brengi/CESE-PCB/2018/Moya/TP_FinalV2/doc/readme.txt

El circuito que se eligió es de un "Electrodo Activo para Electromiografía" para ser usado en mi Trabajo Final de la Especialidad de Sistemas Embebidos.
Está basado en el paper "Simple Circuit Design of Double Differential EMG Active Electrode" de Federico Nicolás Guerrero, Enrique Mario Spinelli y Marcelo Alejandro Haberman.
El circuito propuesto en el paper se muestra en la figura 3b y en el texto se hace la selección de componentes. La figura 5 muestra el PCB que implementaron.
La consigna para este trabajo fue mejorar ese PCB mediante las siguientes acciones:

- Incluir zonas de cobre
- Evitar puentes
- Brindar dos puntos de sujección a cada electrodo

El único requerimiento particular del circuito es que la distancia entre electrodos debe ser de 20mm.

Fue necesario iterar el diseño del esquemático y del PCB  reordenando componentes e intercambiando las unidades del circuito integrado para obtener un ruteo óptimo y las mayores áreas de cobre posible.
Si bien la distancia de los electrodos a los operacionales no es la misma,  no resulta crítico dadas las caracterísiticas de baja frecuencia de las señales (hasta 500 Hz).

Telmo Moya
CESE 2018
