brengi/CESE-PCB/doc/2016_curso1/Curso_PCBs_Intro.pdf

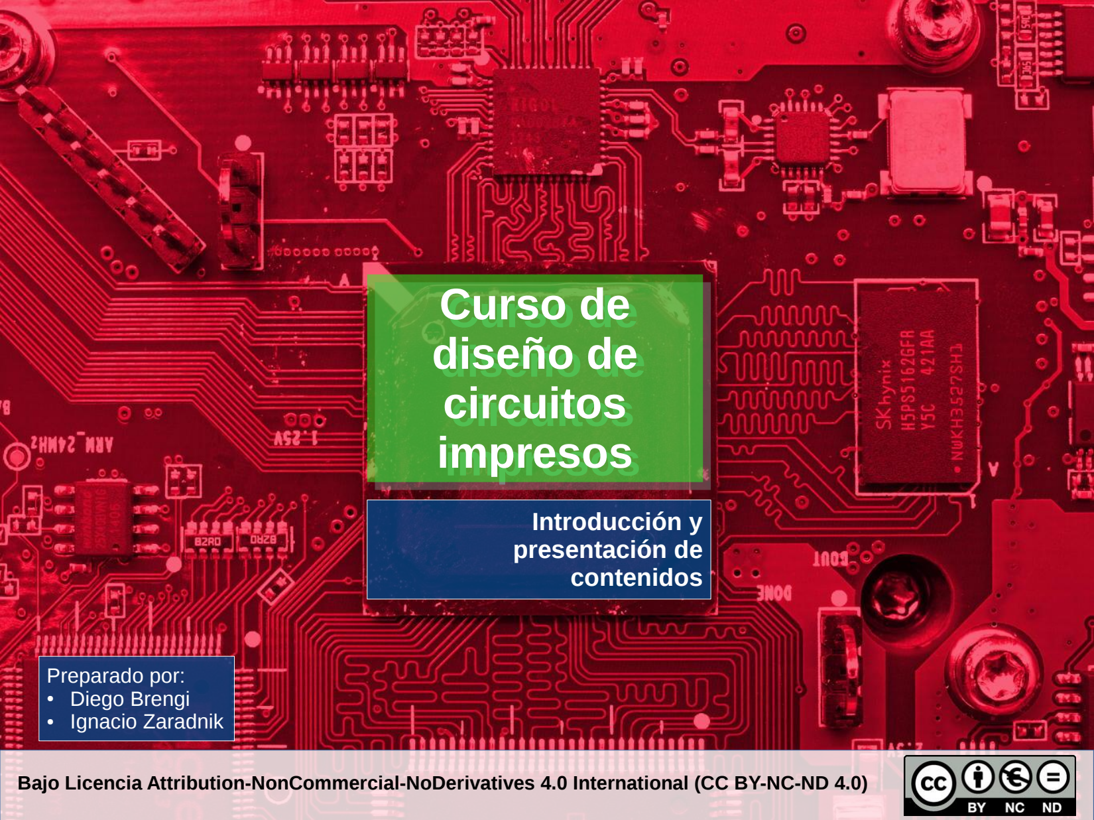
[picture p158: page 1]

# Curso de diseño de circuitos impresos

Introducción y
presentación de
contenidos

Bajo Licencia Attribution-NonCommercial-NoDerivatives 4.0 International (CC BY-NC-ND 4.0)

Preparado por:
- Diego Brengi
- Ignacio Zaradnik

## La problemática de los diseños de PCBs complejos

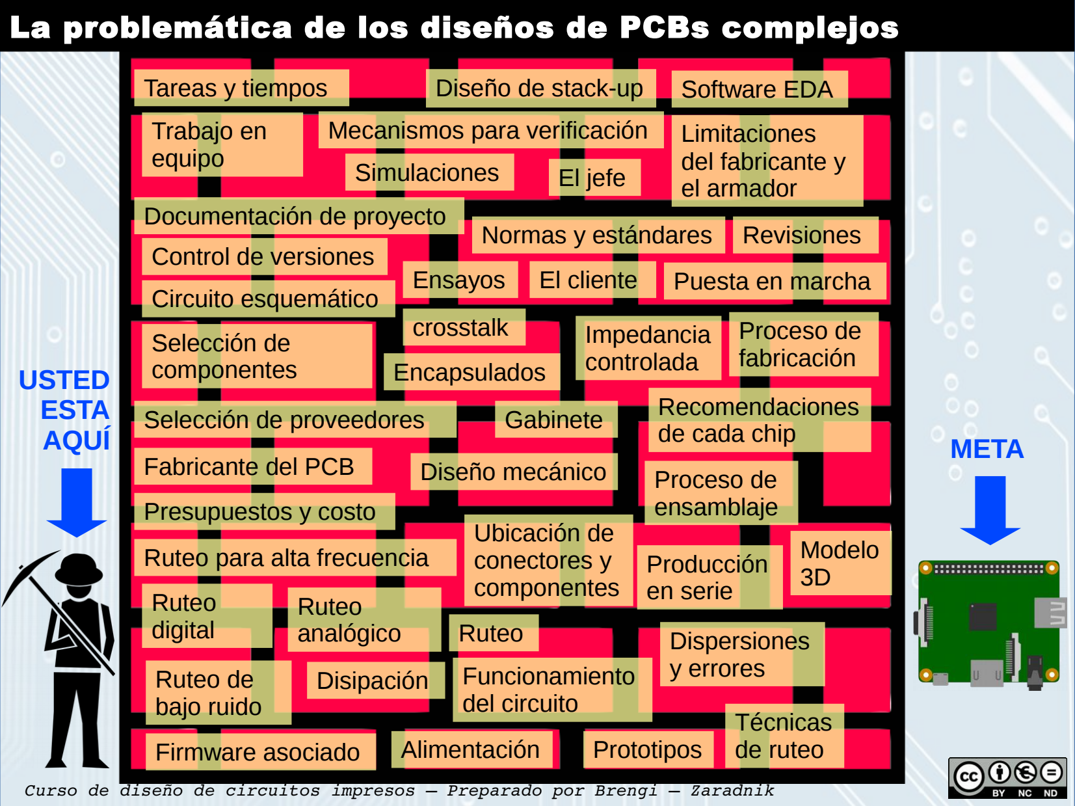
[picture p159: page 2]

Curso de diseño de circuitos impresos – Preparado por Brengi – Zaradnik

Proceso de
fabricación

Circuito esquemático

Documentación de proyecto

Selección de
componentes
Fabricante del PCB | Proceso de ensamblaje

Mecanismos para verificación

Puesta en marcha

Diseño de stack-up

Normas y estándares Revisiones

Trabajo en
equipo

Ruteo

Ubicación de
conectores y
componentes

Presupuestos y costo
Ruteo para alta frecuencia

Ruteo
analógico

Ruteo
digital

Software EDA

Diseño mecánico

Selección de proveedores

Simulaciones

Firmware asociado

Tareas y tiempos

Funcionamiento
del circuito

Gabinete

Ensayos

Alimentación

Ruteo de
bajo ruido

Limitaciones
del fabricante y
el armador

Recomendaciones
de cada chip

Modelo
3D

Encapsulados

Prototipos

Producción
en serie

Dispersiones
y errores

Técnicas
de ruteo

crosstalk Impedancia controlada

Disipación

Control de versiones
El cliente

El jefe

USTED
ESTA
AQUÍ | META

## La problemática de los diseños de PCBs complejos

## Los factores que intervienen son muy

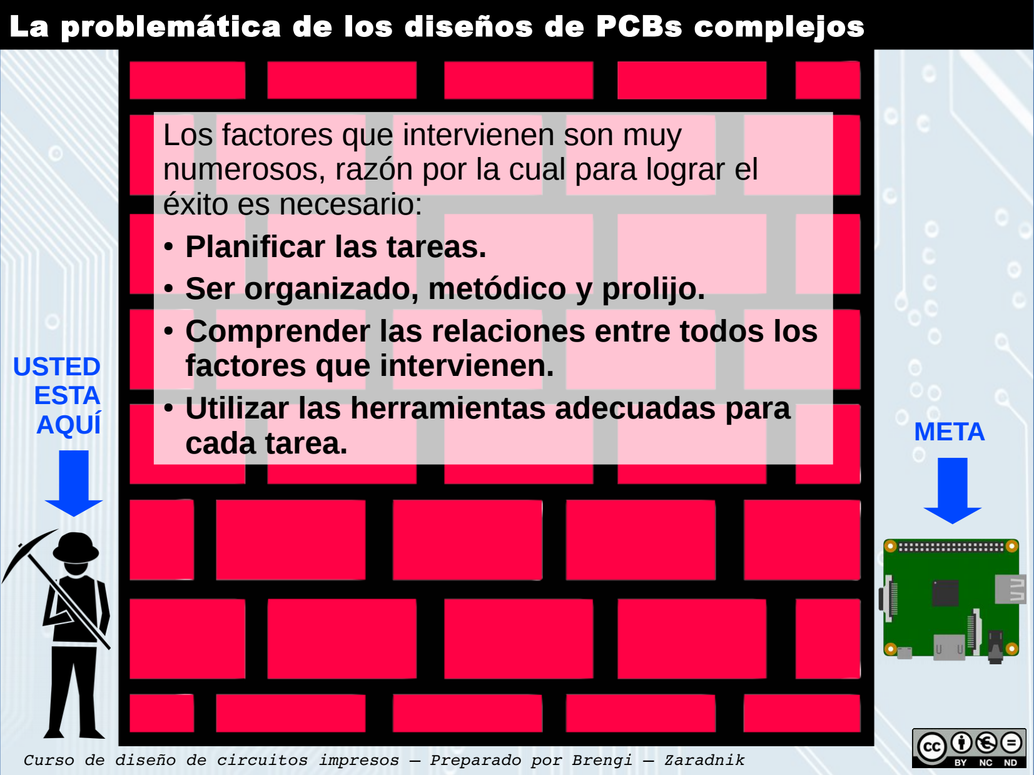
[picture p160: page 3]

USTED
ESTA
AQUÍ

## numerosos, razón por la cual para lograr el éxito es necesario:

- Planificar las tareas.
- Ser organizado, metódico y prolijo.

## - Comprender las relaciones entre todos los

factores que intervienen.

## - Utilizar las herramientas adecuadas para

cada tarea. | META

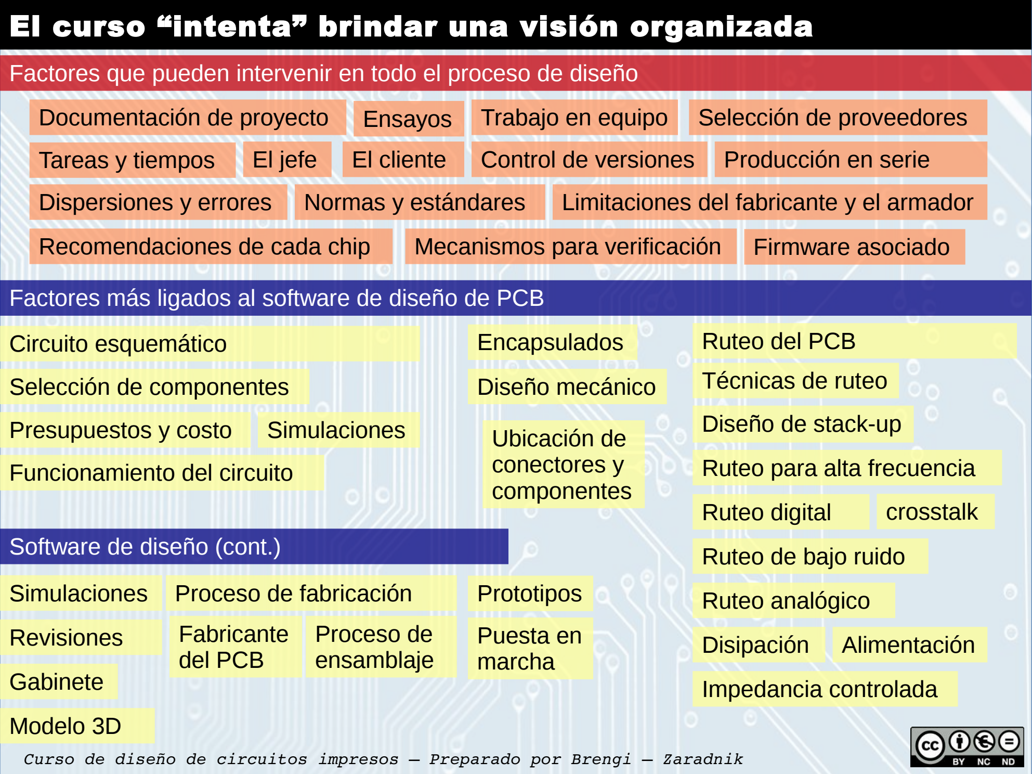
[picture p161: figure]
Proceso de fabricación; Circuito esquemático; Documentación de proyecto; Selección de componentes; Fabricante del PCB; Proceso de ensamblaje; Mecanismos para verificación; Puesta en marcha; Diseño de stack-up; Normas y estándares; Revisiones; Trabajo en equipo; Ruteo del PCB; Ubicación de conectores y componentes; Presupuestos y costo; Ruteo para alta frecuencia; Ruteo analógico; Ruteo digital; Diseño mecánico; Selección de proveedores; Simulaciones; Firmware asociado; Tareas y tiempos; Funcionamiento del circuito; Gabinete; Ensayos; Alimentación; Ruteo de bajo ruido; Recomendaciones de cada chip; Modelo 3D; Encapsulados; Prototipos; Producción en serie; Dispersiones y errores; Técnicas de ruteo; crosstalk; Impedancia controlada; Disipación; El jefe; El cliente; Control de versiones; Software de diseño (cont.)

## El curso “intenta” brindar una visión organizada

Factores más ligados al software de diseño de PCB

Limitaciones del fabricante y el armador

Factores que pueden intervenir en todo el proceso de diseño

## Alcance del curso

Aprender y dominar algunos de los conceptos y factores mencionados lleva años de experiencia, muchas horas de lectura en cada temática y otras tantas de práctica realizando diseños.

El curso debe ajustarse a una carga horaria total de 24 hs.

Por este motivo se dará prioridad a la práctica con el software de diseño de PCBs, a la metodología general y a los temas de base que incentiven a la investigación por cuenta propia.

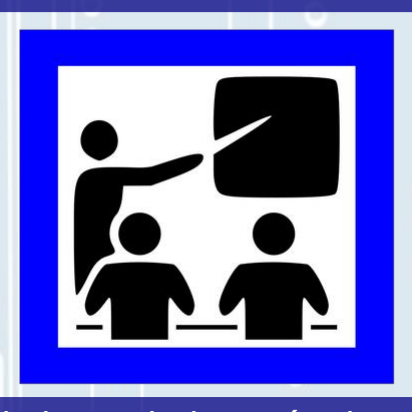
[picture p162: figure]

Al finalizar el curso se tendrá conocimiento de los métodos, pautas y procedimientos a considerar cuando se realiza un diseño de mediana y alta complejidad. Además se reforzarán los conceptos llevándolos a la práctica utilizando KiCad y realizando los ejercicio propuestos.

El contenido listado a continuación es orientativo, pudiéndose quitar o agregar temas dependiendo de la evolución del curso.

## Organización conceptual del curso

El curso esta organizado en cuatro módulos principales:

1)Glosario: Se da una base de conocimientos y términos, mencionando los elementos, componentes y partes que intervienen en el proceso de diseño. Se presentan de manera simple conceptos que después serán necesarios para entender los procedimientos. 2)Procedimientos: Se explican los pasos que debe seguir el diseñador en cada etapa. Aquí se agrupan técnicas, consejos, modalidades, y todos los pasos y consideraciones que deben realizarse para finalizar exitosamente un diseño.
3)Software EDA: Capacitación en el uso del software EDA que se utilizará en el curso (KiCad). 4)Ejercicios: Los ejercicios buscan consolidar los conocimientos aprendidos en los demás módulos.

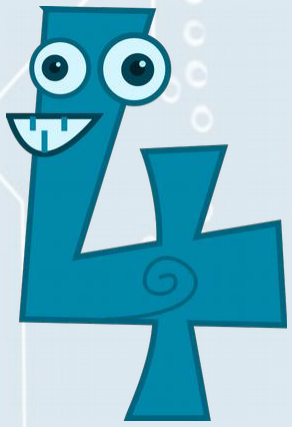
[picture p163: figure]

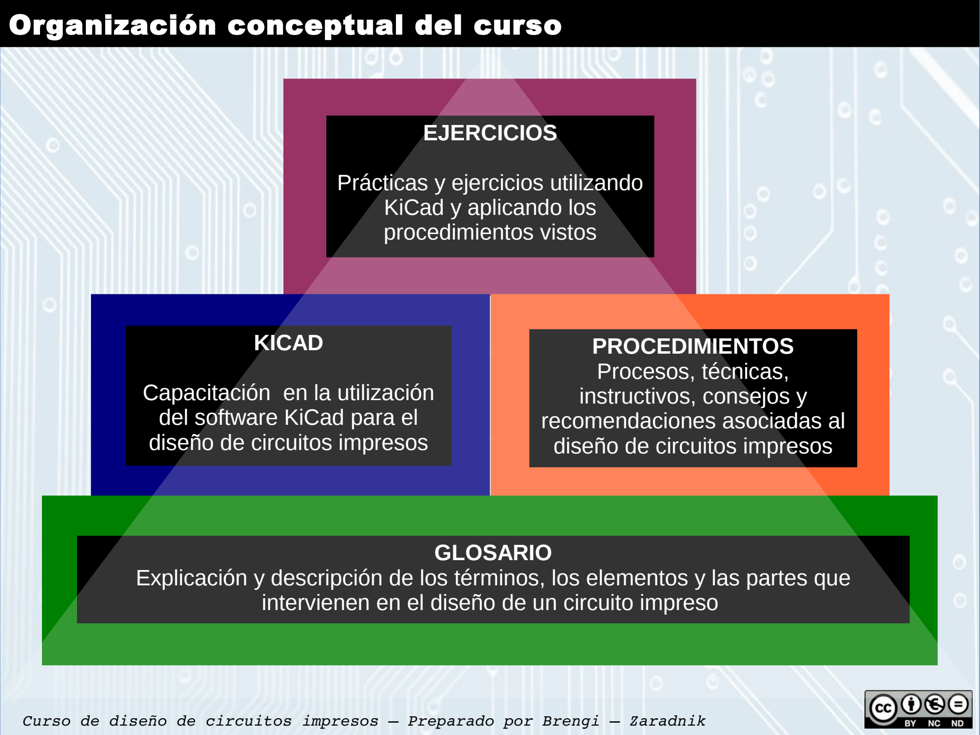
[picture p164: figure]
Organización conceptual del curso; GLOSARIO; PROCEDIMIENTOS Procesos, técnicas, instructivos, consejos y recomendaciones asociadas al diseño de circuitos impresos; KICAD; Capacitación en la utilización del software KiCad para el diseño de circuitos impresos; EJERCICIOS; Prácticas y ejercicios utilizando KiCad y aplicando los procedimientos vistos

Explicación y descripción de los términos, los elementos y las partes que intervienen en el diseño de un circuito impreso

## Glosario

GLOSARIO
Explicación y descripción de los términos, los elementos y las partes que intervienen en el diseño de un circuito impreso

Documentación – Sistema de revisión Documentación – Estructura de directorios Documentación – Administrativos
Documentación – Requerimientos
Documentación – Hojas de datos y notas de aplicación Documentación – Esquemático y PCB Documentación – Notas de ingeniería
Documentación – Proveedores, cotizaciones y presupuestos
Documentación – Especificaciones del fabricante Documentación – Revisiones del diseño Documentación – Brochure
Documentación – Autores y licencia
Software EDA
Software de diseño de PCB
Esquemático
Esquemático – Única hoja
Esquemático – Múltiples hojas Esquemático – Rótulo
Símbolo de esquemático
Símbolo – Multiparte regular Símbolo – Multiparte irregular Símbolo – Pin de conexión
Símbolo – Campos asociados Símbolo – Muchos pines.
Símbolo – Bibliotecas de símbolos Símbolo – Referencias de tensión

Esquemático – Líneas de interconexión Esquemático – Uniones
Esquemático – etiquetas globales
Esquemático – Etiquetas jerárquicas
Esquemático – Buses
Esquemático – Líneas, gráficos y notas adicionales Esquemático – ERC
Esquemático – Netlist
Esquemático – Listado de materiales
PCB
PCB – Rótulo y notas
PCB – Grilla y unidades
PCB – Bordes
PCB – Agujeros de sujeción PCB – Fiduciales
PCB – Vías
PCB – Vías – Pasante o PTH
PCB – Vías – otros tipos
PCB – Vías – terminaciones (tented via) PCB – pistas
PCB – pistas de alimentación
PCB – pistas diferenciales
PCB – pistas de impedancia controlada PCB – pistas de alta velocidad
PCB – Crosstalk
PCB – Capas
PCB – Capas – Mecánica
PCB – Capas – Cobre
PCB – Capas – Serigrafía
PCB – Capas – Máscara antisoldante PCB – Capas – Información de taladrado PCB – Capas – Pasta de estaño
PCB – Capas – Adicionales.
PCB – Stackup
PCB – Stackup – Láminas de cobre, sustratos y núcleos
PCB – Stackup – Preimpregnado
PCB – Stackup – Espesores
PCB – Stackup – Impedancias

PCB – Huellas
PCB – Huellas – Pads
PCB – Huellas – Tipos de encapsulados PCB – Huellas – Capas y propiedades PCB – Planos de alimentación
PCB – Rellenos de cobre
PCB – Rellenos de cobre – alivio térmico PCB – Áreas de exclusión
PCB – Ratsnest
PCB – Posicionamiento
PCB – Ruteo
PCB – Ruteo – Ic Fanout
PCB – Red de alimentación (PDN) PCB – Puntos de prueba
PCB – Verificador de capas
PCB – DRC
PCB – DRC – Clearance
PCB – Cupón
PCB – Archivos Gerber
Fabricación – Acabados superficiales HASL, ENIG y OSP.
Fabricación – Panelizado
Fabricación – corte vscoring y milling Armado – Montaje (Pick&place) Armado – Soldadura (Horno/Ola)

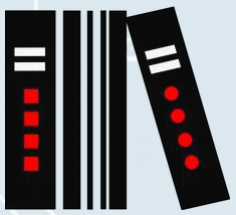
[picture p165: figure]

## Procedimientos

PROCEDIMIENTOS
Procesos, técnicas,
instructivos, consejos y
recomendaciones asociadas al diseño de circuitos impresos

PLANIFICACION DEL PCB
- Creación de huellas.
- Elección del stackup.
- Reglas de diseño del fabricante.
- Selección del método de ensamblaje y soldadura.
- Cálculos de pistas de alimentación.
- Cálculo de impedancia (impedancia controlada).
- Cálculo de par diferencial.
- Reglas de diseño y DRC.
- Planificación del panelizado.

RUTEO DEL PCB
- Asociación de símbolos y huellas.
- Sectorización del PCB, planificación y técnicas para la ubicación de componentes.
- Distribución de la alimentación y planos de alimentación.
- Técnicas de ruteo.
- Fanout de encapsulados de muchas conexiones.
- Ruteo de líneas diferenciales.
- Mitigación de crossltalk.
- Técnicas para circuitos de alta velocidad.
- Utilización de estructuras para la verificación.
- Revisiones de terceros.

FABRICACIÓN Y ARMADO
- Modelado 3D.
- Diseño del cupón de pruebas.
- Generación de archivos gerber e instrucciones para el fabricante.
- Generación de información para el armador.

METODOLOGÍA DE TRABAJO
- Ciclo general de diseño.
- Uso de git.
- Creación de la estructura de directorios.
- Proceso de documentación continua.
- Técnicas de trabajo en grupo.

DISEÑO DEL ESQUEMÁTICO
- Recomendaciones para un buen esquemático.
- Uso de los campos adicionales de los símbolos.
- Identificación de nodos y líneas especiales.
- Verificación ERC.
- Revisiones de terceros.

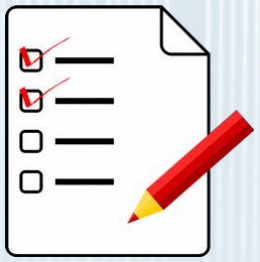
[picture p166: figure]

## Uso de KiCad

KICAD
Capacitación en la
utilización del software
KiCad para el diseño
de circuitos impresos

TOUR KICAD
- Presentación de KiCad.
- Características (ventajas y desventajas).
- Vista de las partes principales.
- Flujo de archivos.
- Flujo de trabajo en KiCad mientras se realiza un circuito mínimo.
- Administrador de proyectos.
- Editor de esquemáticos.
- Archivo netlist y asociación de huellas.
- Editor de PCB.
- La Graphic Abstarction Layer de KiCad (GAL).
- Modificaciones posteriores al esquemático.
- Generación de archivos Gerber.
- Visualización de archivos Gerber.
- Reportes de taladrado.
- Vista 3D.

ESCUELA KICAD
- Git y kicad.
- Estructura de directorios de un proyecto.
- Editor de esquemáticos, hojas jerárquicas y etiquetas de jerarquía.
- Editor de símbolos, pautas y creación de un símbolo.
- Creación de un símbolo multiparte no intercambiable.
- El chequeo de reglas eléctricas en el esquemático y power flags.
- Etiquetas locales y buses.
- Campos adicionales de información de los componentes.
- Documentación: Rótulo.
- Generación de listado de materiales.
- Opciones de footprints soportados.
- Asociación de footprints. Problemática.
- Operaciones con bloques en el esquemático.
- Editor de footprints.
- Pautas para la creación de footprints.
- Creación de un componente nuevo.
- Editor de PCB.
- Utilización de modos de visualización.
- Cambios posteriores de footprints.
- Operaciones con bloques en el editor de PCB.
- Ruteo en cuatro capas.
- Áreas de cobre y zonas de exclusión.
- Verificaciones del DRC.
- Modelos 3D. Como obtenerlos y como aplicarlos prolijamente.

KICAD EXPERTO
- Técnicas de trabajo grupal en un mismo diseño con KiCad.
- Técnicas para símbolos
complejos de muchas
conexiones.
- Cálculo de costo de materiales.
- Opciones avanzadas del editor de footprint.
- Uso de la calculadora de KiCad para impedancia controlada.
- Opciones de ruteo interactivo.
- Ruteo de par diferencial, ecualización de longitud y ecualización de fase.

Los módulos de KiCad están basados en el material publicado de Diego Brengi, Noelia Scotti y Diego Alamon en relación al proyecto CIAA.

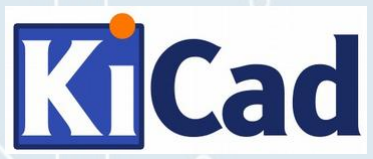
[picture p167: figure]

## Ejercicios y prácticas

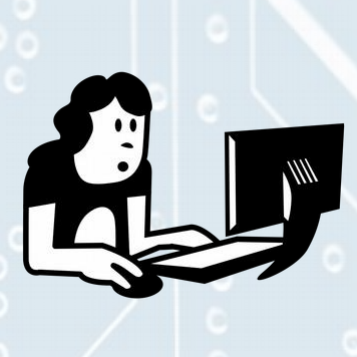
[picture p168: figure]

EJERCICIOS
Prácticas y ejercicios utilizando KiCad y aplicando los
procedimientos vistos

Práctica 1
Circuito básico en KiCad, recorriendo su flujo de trabajo.

Práctica 2
Circuito simple multicapa en KiCad, utilizando gran parte de sus herramientas y opciones.

Práctica 3
Práctica a definir, trabajando en técnicas de ruteo de multicapa y stackup.

Práctica 4
Participación parcial en un proyecto colaborativo de largo plazo, aplicando algunos de los conceptos avanzados del curso.

Las versiones para Windows y Linux se pueden bajar del siguiente enlace:

http://kicad-pcb.org/download/

VERSION RECOMENDADA
PARA LA ACTIVIDAD:

## 4.0.2 (28 Feb 2016)

PARA SACAR MÁXIMO PROVECHO AL CURSO, SE RECOMIENDA
TRAER NOTEBOOK Y KICAD
INSTALADO PARA EL PRIMER DÍA.

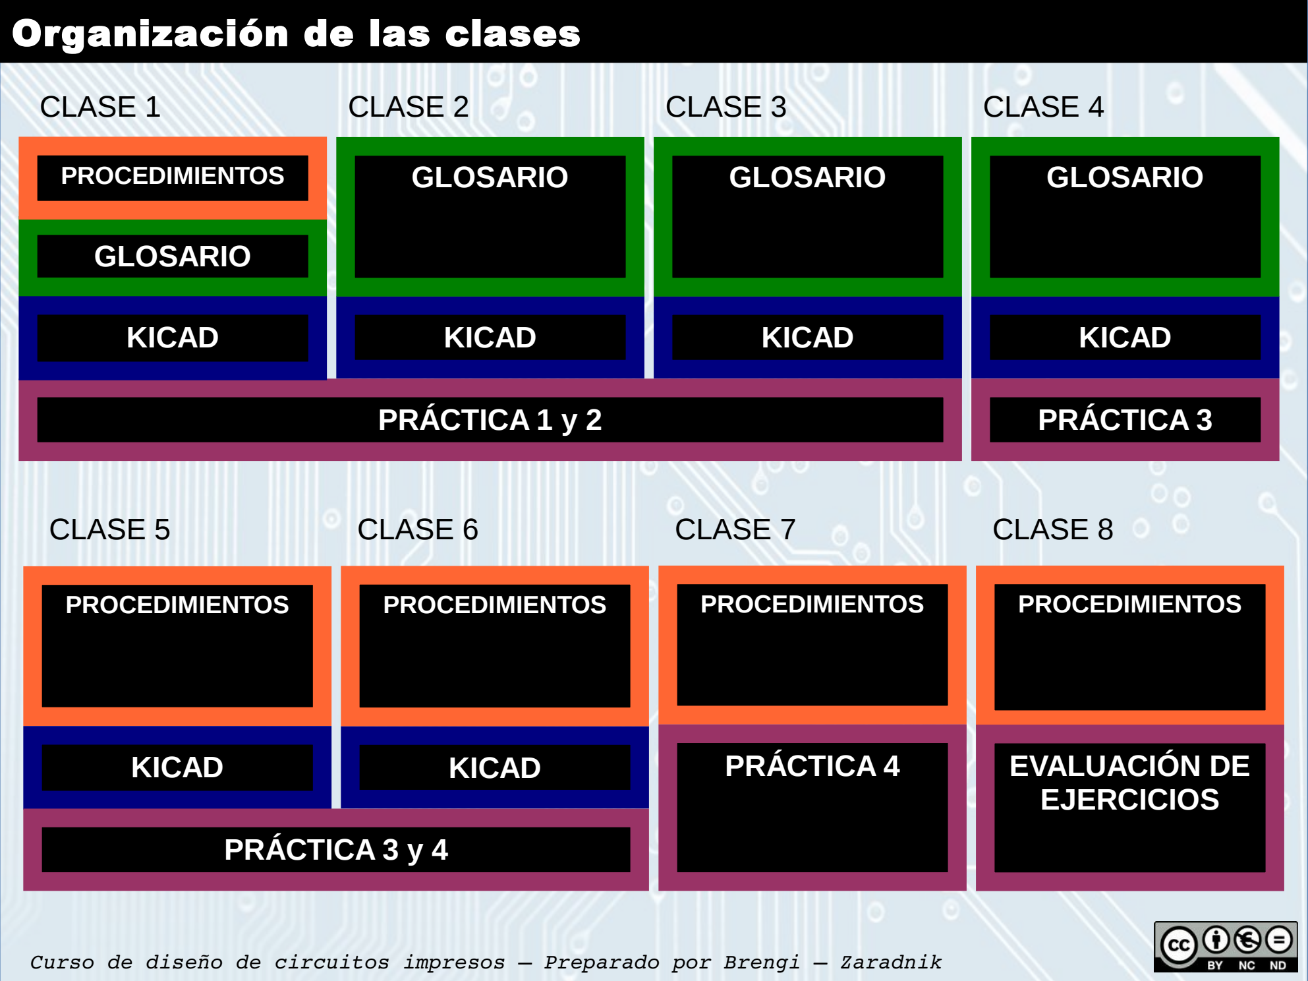
[picture p169: figure]
Organización de las clases; PRÁCTICA 1 y 2; KICAD; GLOSARIO; PROCEDIMIENTOS; PRÁCTICA 3 y 4; PRÁCTICA 4; EVALUACIÓN DE EJERCICIOS; CLASE 1; CLASE 2; CLASE 3; CLASE 4; CLASE 5; CLASE 6; CLASE 7; CLASE 8; PRÁCTICA 3

## Contacto e imágenes utilizadas

Las imágenes de clipart se tomaron de: https://openclipart.org/

Los demás logos corresponden a proyectos de Software Libre u Open Source.

Carátula principal:
Foto titulada “Rigol DS1054Z Oscilloscope Teardown PCB” de Dave Jones bajo licencia CC-BY 2.0 disponible en https://www.flickr.com/photos/eevblog/15354008908/in/dateposted/

Bajo Licencia Attribution-NonCommercial-NoDerivatives 4.0 International (CC BY-NC-ND 4.0)

Autor de esta presentación y contacto:
Diego Brengi - djavier@ieee.org

“Curso de diseño de circuitos impresos”
Preparado para la Carrera de Especialización en Sistemas Embebidos del LSE-FIUBA (CESE)

Versión
23/05/16

Fondo de la presentación:
Foto titulada “Electronic Circuit Board” de Creativity103 bajo licencia CC-BY 2.0 disponible en: https://www.flickr.com/photos/creative_stock/5227842611/
