brengi/CESE-PCB/doc/2016_curso1/KiCad_Avanzado_CESE.pdf

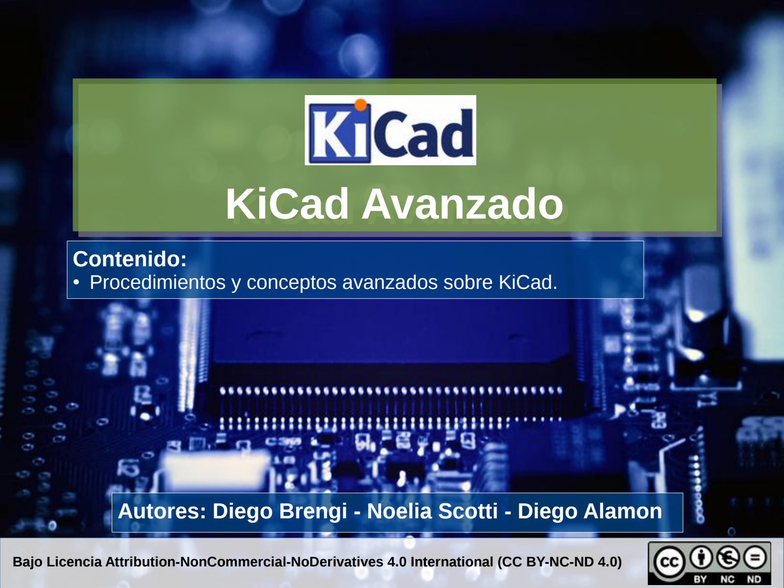
[picture p170: page 1]

# KiCad Avanzado

### Contenido:

- Procedimientos y conceptos avanzados sobre KiCad.

### Autores: Diego Brengi - Noelia Scotti - Diego Alamon

Bajo Licencia Attribution-NonCommercial-NoDerivatives 4.0 International (CC BY-NC-ND 4.0)

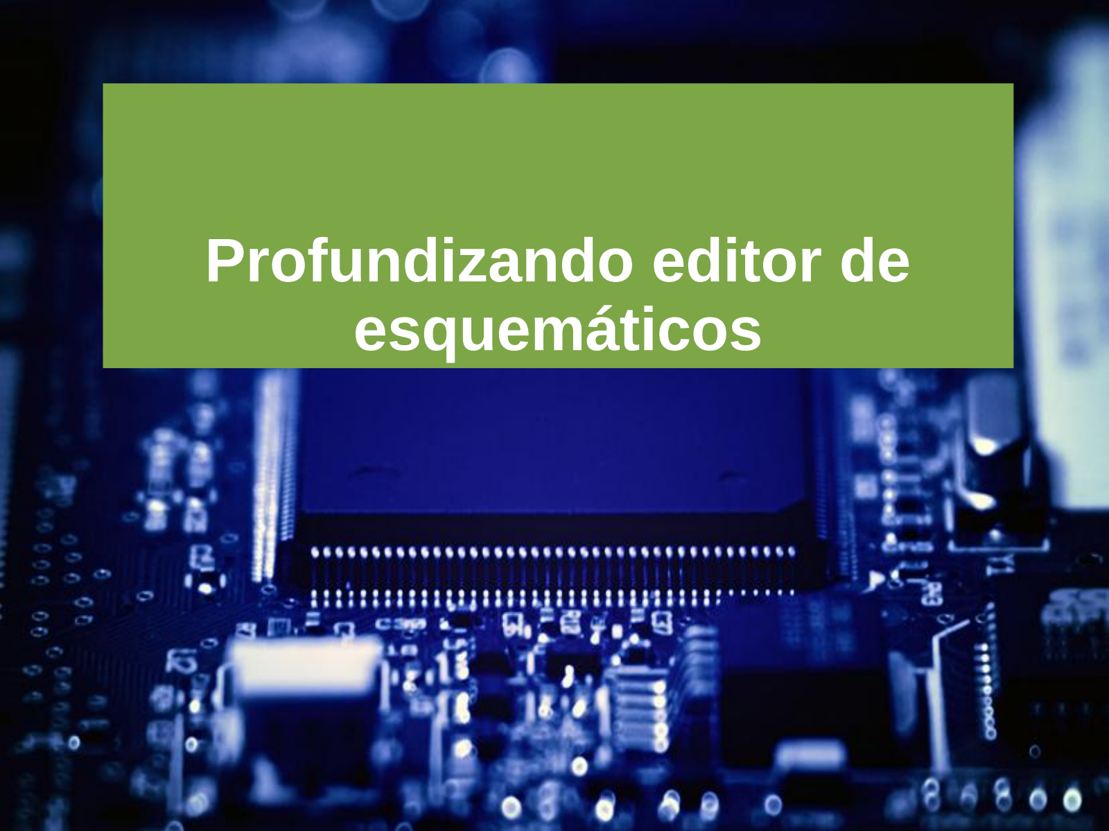
[picture p171: page 2]

# Profundizando editor de esquemáticos

## KiCad Trabajo grupal

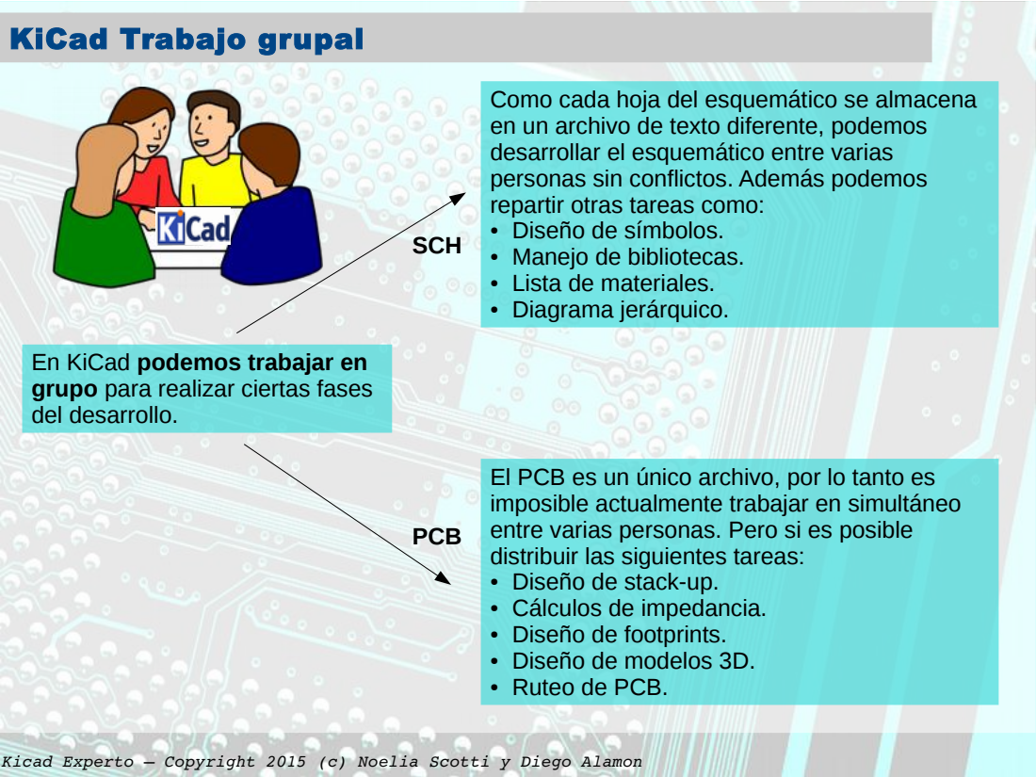
[picture p172: page 3]

Como cada hoja del esquemático se almacena
en un archivo de texto diferente, podemos
desarrollar el esquemático entre varias
personas sin conflictos. Además podemos
repartir otras tareas como:
● Diseño de símbolos.
SCH
● Manejo de bibliotecas.
● Lista de materiales.
● Diagrama jerárquico.

En KiCad podemos trabajar en
grupo para realizar ciertas fases
del desarrollo.

El PCB es un único archivo, por lo tanto es
imposible actualmente trabajar en simultáneo
entre varias personas. Pero si es posible
PCB
distribuir las siguientes tareas:
● Diseño de stack-up.
● Cálculos de impedancia.
● Diseño de footprints.
● Diseño de modelos 3D.
● Ruteo de PCB.

Kicad Experto – Copyright 2015 (c) Noelia Scotti y Diego Alamon

## KiCad Trabajo grupal

Cuidados que hay que tener
- No agregar hojas a mitad de proyecto, si fuera necesario, lo debe hacer el coordinador teniendo cuidado de que no se modifique la numeración de las hojas actuales.
- Guardar, editar y subir al repositorio solamente nuestros archivos. Si editamos involuntariamente archivos del compañero, deben ser reemplazados por la versión que esté en el repositorio remoto.
- Numerar los componentes con el esquema number*100.
- No renumerar nunca el proyecto completo.

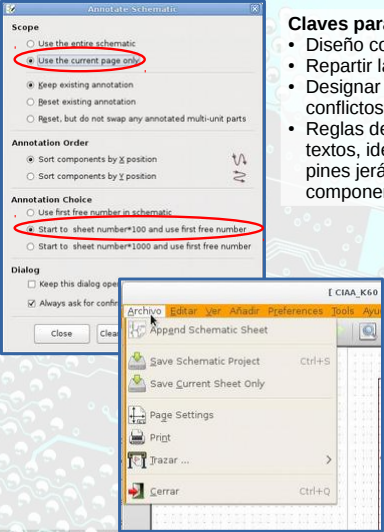
[picture p173: figure]

Claves para el trabajo grupal
- Diseño con múltiples hojas (jerárquico o plano).
- Repartir las tareas desde el principio del proyecto.
- Designar un coordinador que gestione librerías, conflictos y hojas complicadas como las de una CPU.
- Reglas de diseño claras desde el principio (tamaños de textos, identificación de pares diferenciales, ubicación de pines jerárquicos, campos de información de los componentes, etc.)

Kicad Experto – Copyright 2016 (c) Diego Brengi

## KiCost – Cálculo de costos

KiCost es un script Python para calcular costos de los componentes de diseño hecho en KiCad.

Funcionamiento básico:

1)Ingresar en el esquemático los campos especiales de información. 2)Generar el netlist básico (xml). 3)Correr el script con el xml como entrada.
4)KiCost consultará las bases de datos de los proveedores y generará una planilla de cálculo.
Licencia: | MIT

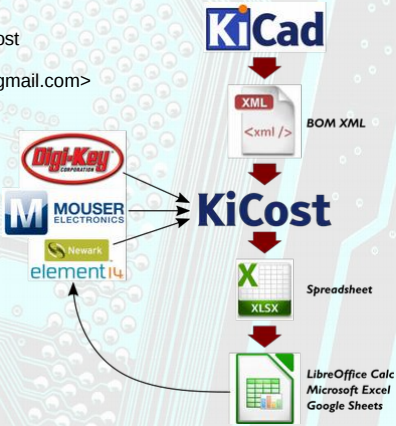
[picture p174: figure]

Código: | https://github.com/xesscorp/KiCost
Docum.: | https://kicost.readthedocs.io
Autor: | Dave Vandenbout <devbisme@gmail.com>

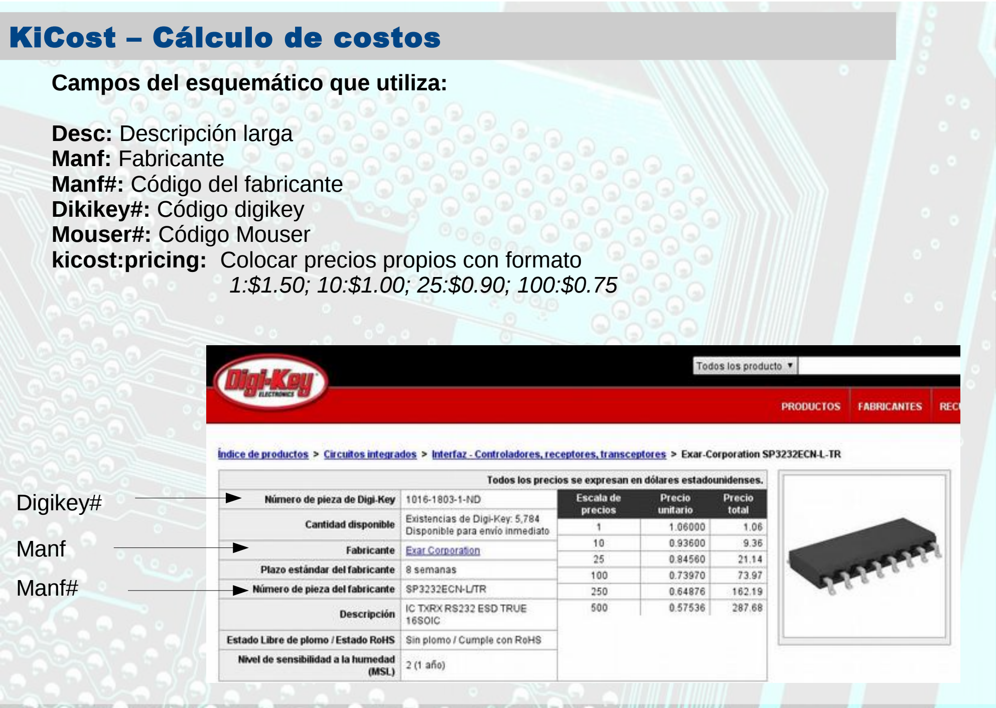
[picture p175: figure]
KiCost – Cálculo de costos; Campos del esquemático que utiliza:; Desc: Descripción larga Manf: Fabricante Manf#: Código del fabricante Dikikey#: Código digikey Mouser#: Código Mouser; Digikey#; Manf; Manf#

kicost:pricing: Colocar precios propios con formato

## KiCost – Cálculo de costos

Ejercicio2cese$ kicost -i ej2.xml
No 'newark#' or 'manf#' field: cannot lookup part ['F1', 'F2'] at newark No 'digikey#' or 'manf#' field: cannot lookup part ['F1', 'F2'] at digikey No 'mouser#' or 'manf#' field: cannot lookup part ['F1', 'F2'] at mouser
Part ['R1', 'R2'] not found at newark
Progress: 100%|
Exception TypeError: TypeError("'NoneType' object is not callable",) in ignored Ejercicio2cese$

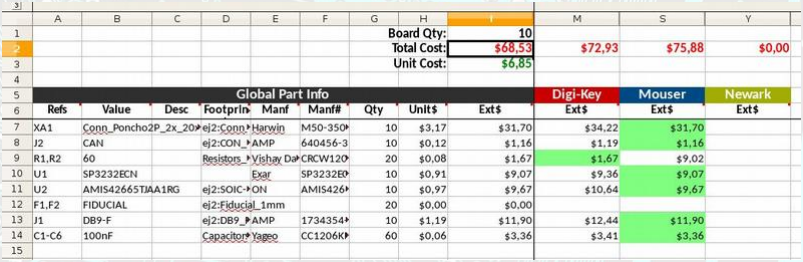
[picture p176: figure]

Ver el instructivo: https://www.youtube.com/watch?v=AeccxROpDfY

## KiCost – Cálculo de costos

Ver el instructivo: https://www.youtube.com/watch?v=AeccxROpDfY

Ventajas:
- Considera precios según las cantidades.
- Marca el proveedor de menor precio.
- Informa stock existente.
- Permite armar la lista para hacer directamente el pedido.
- Permite incluir otros campos arbitrarios a la planilla de reporte.

Desventajas:
- No siempre es eficiente en encontrar los proveedores.
- Necesita exacta concordancia con los campos de descripción, valor y footprint para agrupar componentes.
- No permite seleccionar los nombre de los campos a considerar.
- Parece trabajar mejor con Digikey.

## KiPart para componentes de muchos pines

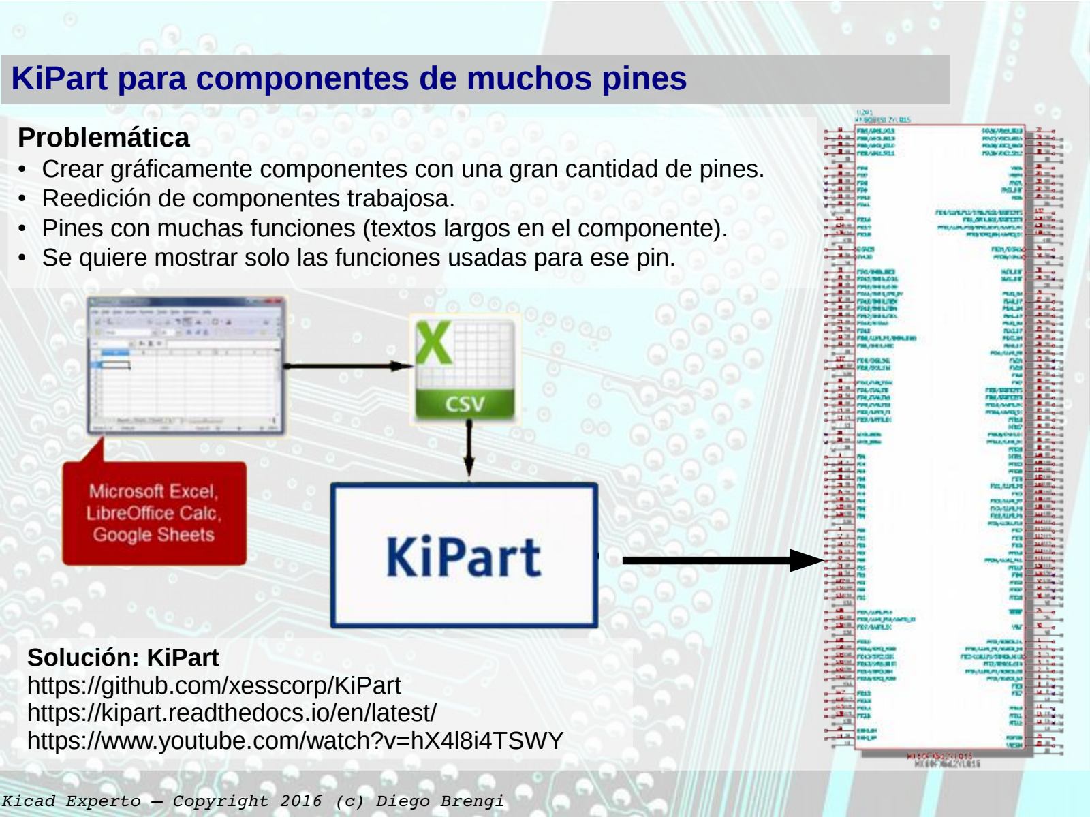
[picture p177: page 9]

Solución: KiPart
https://github.com/xesscorp/KiParthttps://kipart.readthedocs.io/en/latest/https://www.youtube.com/watch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

Problemática
- Crear gráficamente componentes con una gran cantidad de pines.
- Reedición de componentes trabajosa.
- Pines con muchas funciones (textos largos en el componente).
- Se quiere mostrar solo las funciones usadas para ese pin.

## KiField para editar, reorganizar o corregir campos del esquemático

Solución: KiField
https://github.com/xesscorp/kifieldhttps://kifield.readthedocs.io/en/latest/

Problemática
- En diseños de muchos componentes, resulta complejo llevar en forma ordenada y consistente los campos adicionales de información como por ejemplo la descripción larga de los componentes o los código de producto.
- En KiCad es muy laborioso reorganizar o borrar los campos de información de los componentes, y requiere recorrer uno por uno los componentes del esquemático.

KiField extrae los
campos a una planilla

KiField inserta los campos desde una planilla

Se editan los
campos
cómodamente en
una planilla de
cálculo.

Tip: KiField No esta
internacionalizado,
tiene problemas al
manejar acentos y
comillas dobles.

ESQUEMATICO

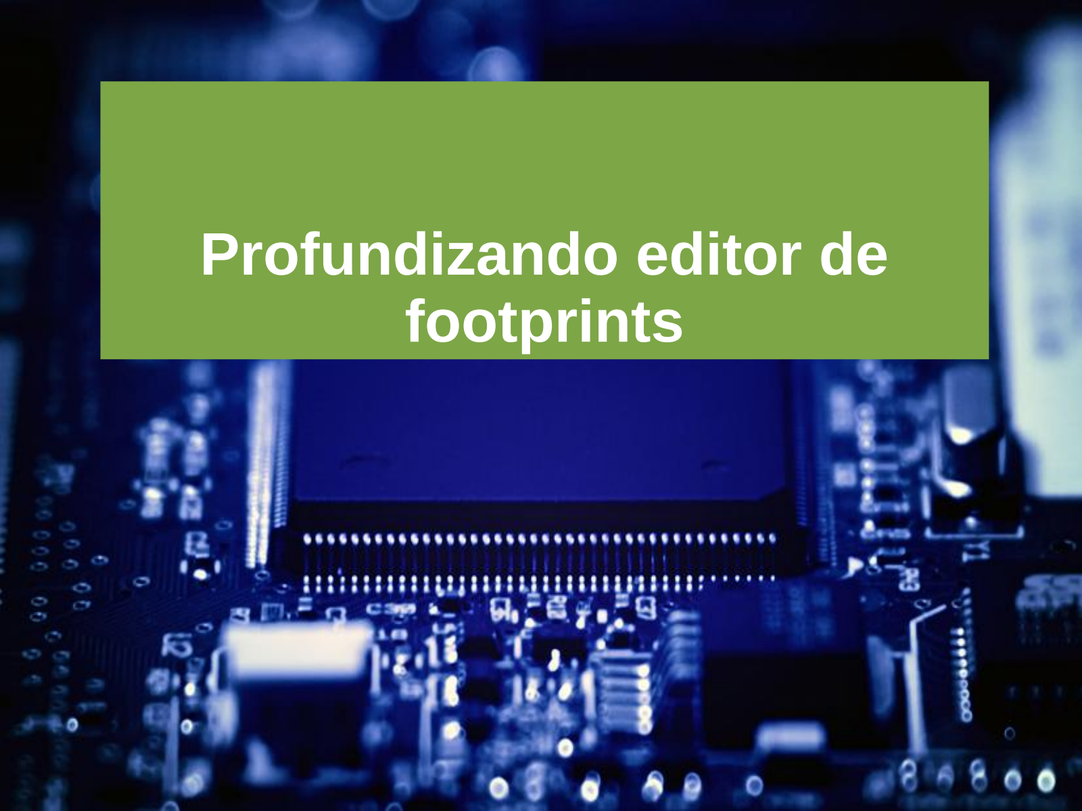
[picture p178: page 11]

# Profundizando editor de footprints

## Opciones avanzadas del editor de módulos

En el siguiente video se ejemplifica como
fácilmente se puede:
- Realizar dibujos y editarlos.
- Importar un archivo DXF.
- Copiar, alinear y distribuir pads.
- Enumerar pads fácilmente.

KiCad module editor demo
https://vimeo.com/99235812

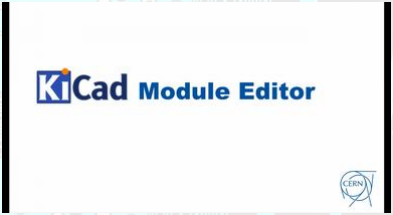
[picture p179: figure]
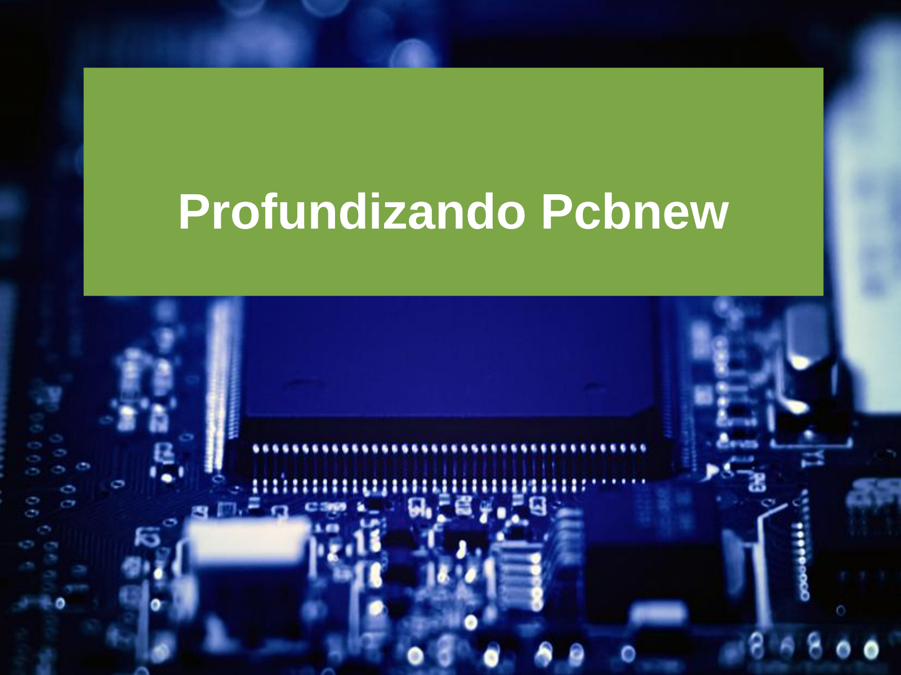
[picture p180: page 13]

# Profundizando Pcbnew

## Ruteo interactivo

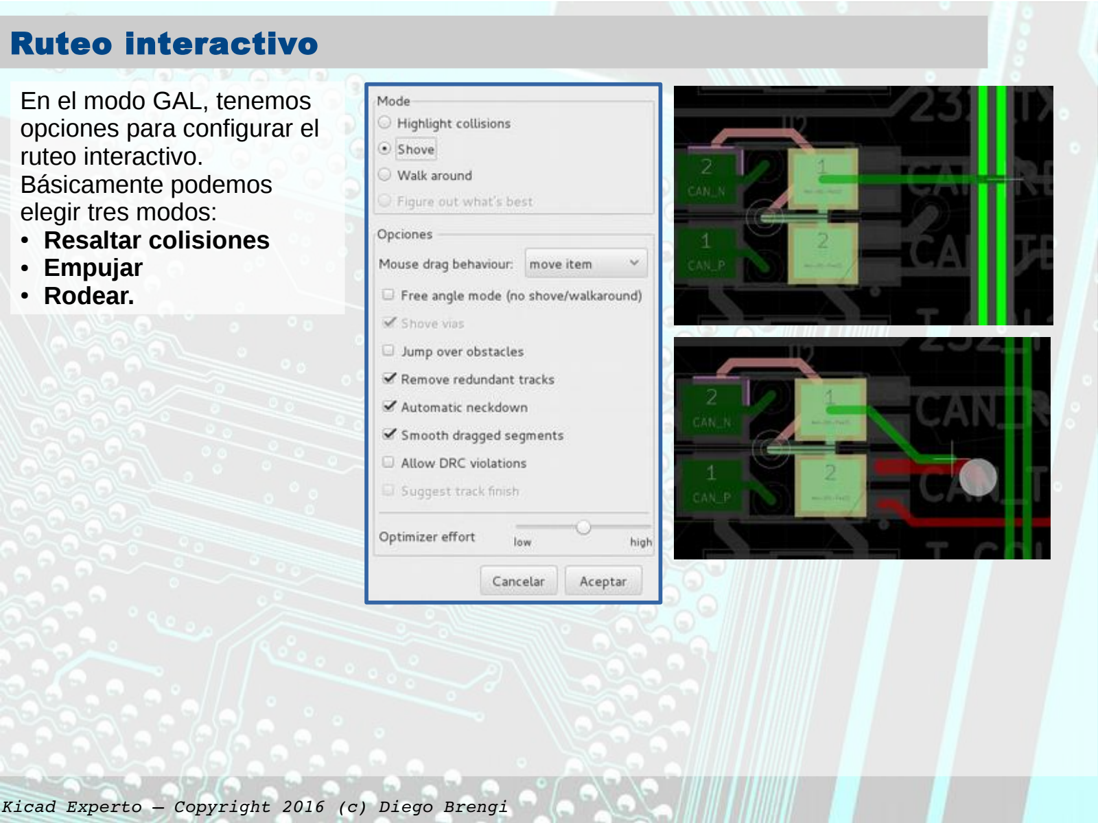
[picture p181: page 14]

En el modo GAL, tenemos
opciones para configurar el ruteo interactivo.
Básicamente podemos
elegir tres modos:
- Resaltar colisiones
- Empujar
- Rodear.

Actualmente KiCad no posee campos para ingresar la información detallada (espesores y materiales) del stack-up. Por eso es conveniente colocar esta información en alguna parte del diseño. Utilizaremos la capa de dibujos para anotar el stackup.

## Pcbnew – Stackup

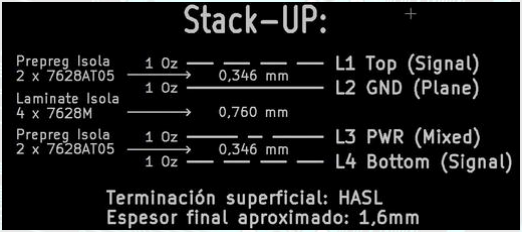
[picture p182: figure]

Stack-up de la CIAA-FSL fabricada por Mayer S.A. (4 Layers)

## Impedancia Controlada

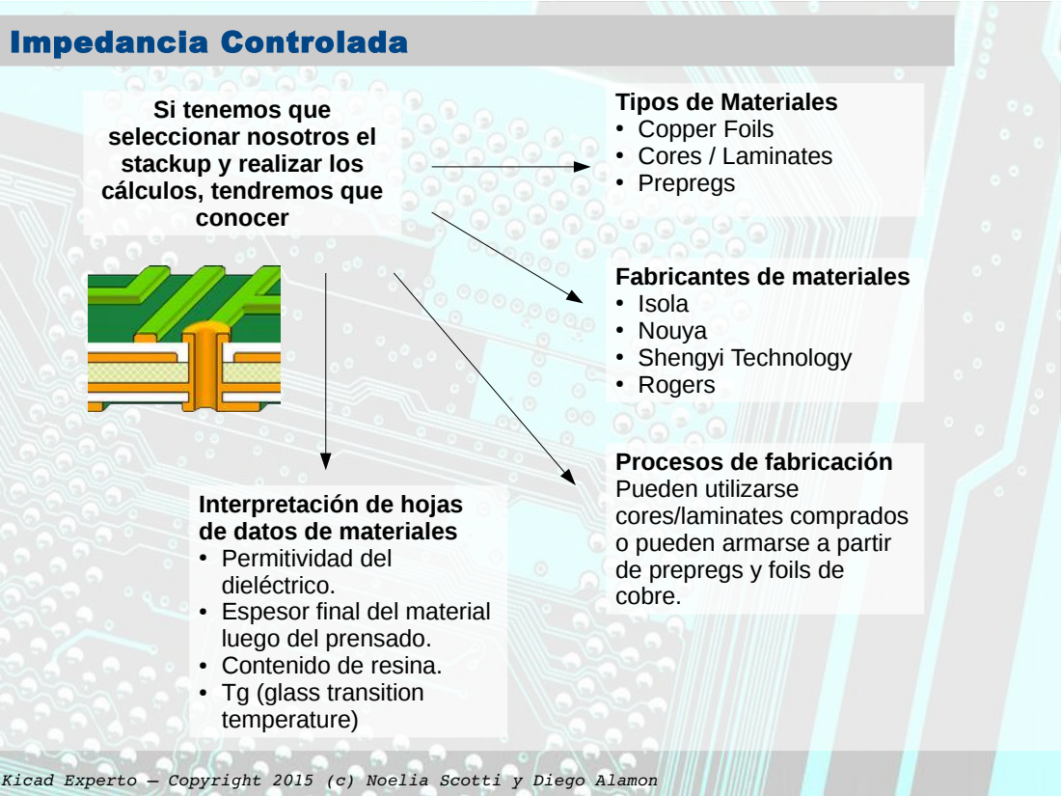
[picture p183: page 16]
conocer

Tipos de Materiales
● Copper Foils
● Cores / Laminates
● Prepregs

Si tenemos que
seleccionar nosotros el
stackup y realizar los
cálculos, tendremos que

Fabricantes de materiales
● Isola
● Nouya
● Shengyi Technology
● Rogers

Procesos de fabricación
Pueden utilizarse
cores/laminates comprados
o pueden armarse a partir
de prepregs y foils de
cobre.

Interpretación de hojas
de datos de materiales
● Permitividad del
dieléctrico.
● Espesor final del material
luego del prensado.
● Contenido de resina.
● Tg (glass transition
temperature)

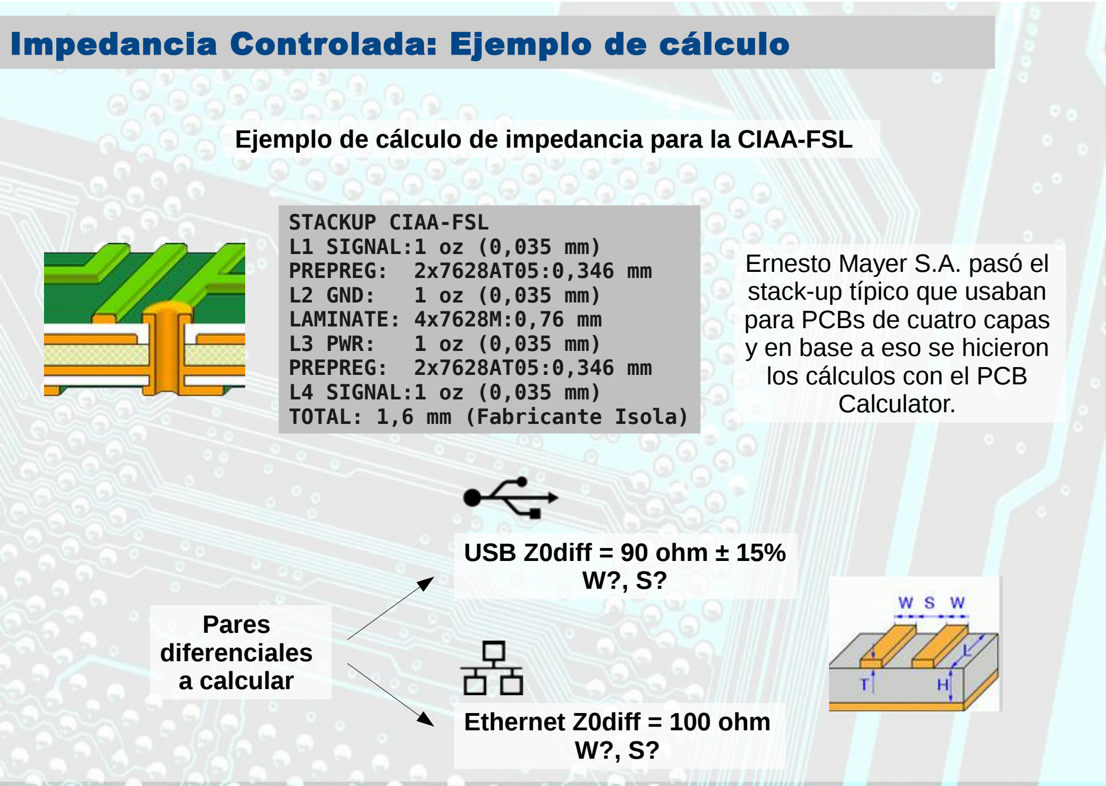
[picture p184: figure]
Pares diferenciales a calcular; STACKUP CIAA-FSL L1 SIGNAL:1 oz (0,035 mm) PREPREG: 2x7628AT05:0,346 mm; L2 GND:; LAMINATE: 4x7628M:0,76 mm; L3 PWR:; PREPREG: 2x7628AT05:0,346 mm L4 SIGNAL:1 oz (0,035 mm) TOTAL: 1,6 mm (Fabricante Isola); Ernesto Mayer S.A. pasó el stack-up típico que usaban para PCBs de cuatro capas y en base a eso se hicieron los cálculos con el PCB Calculator.; USB Z0diff = 90 ohm ± 15% W?, S?; Ethernet Z0diff = 100 ohm W?, S?

## Impedancia Controlada: Ejemplo de cálculo

Ejemplo de cálculo de impedancia para la CIAA-FSL

## Impedancia Controlada: PCB Calculator

Herramientas

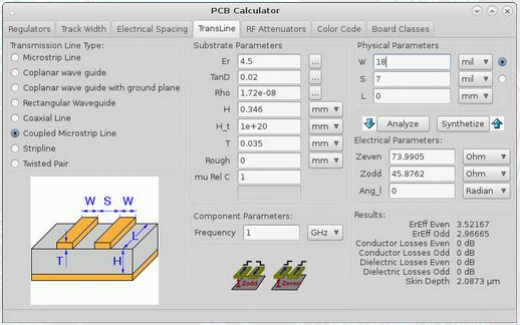
[picture p185: figure]

- Regulators: Calculadora de resistencias para reguladores.
- Track Width: Calculadora para el ancho de pistas en fc. de la corriente máxima.
- Electrical Spacing: Separaciones mínimas para lograr determinada aislación entre pistas.
- TransLine: Calculadora de impedancia característica (Z0) para líneas de Tx.
- RF-Attenuators: Cálculo de atenuadores de RF.
- Color Code: Código de colores de resistencias.
- Board Classes: Clasificación de PCBs según sus dimensiones mínimas.

## Impedancia Controlada: Microstrip Diferencial

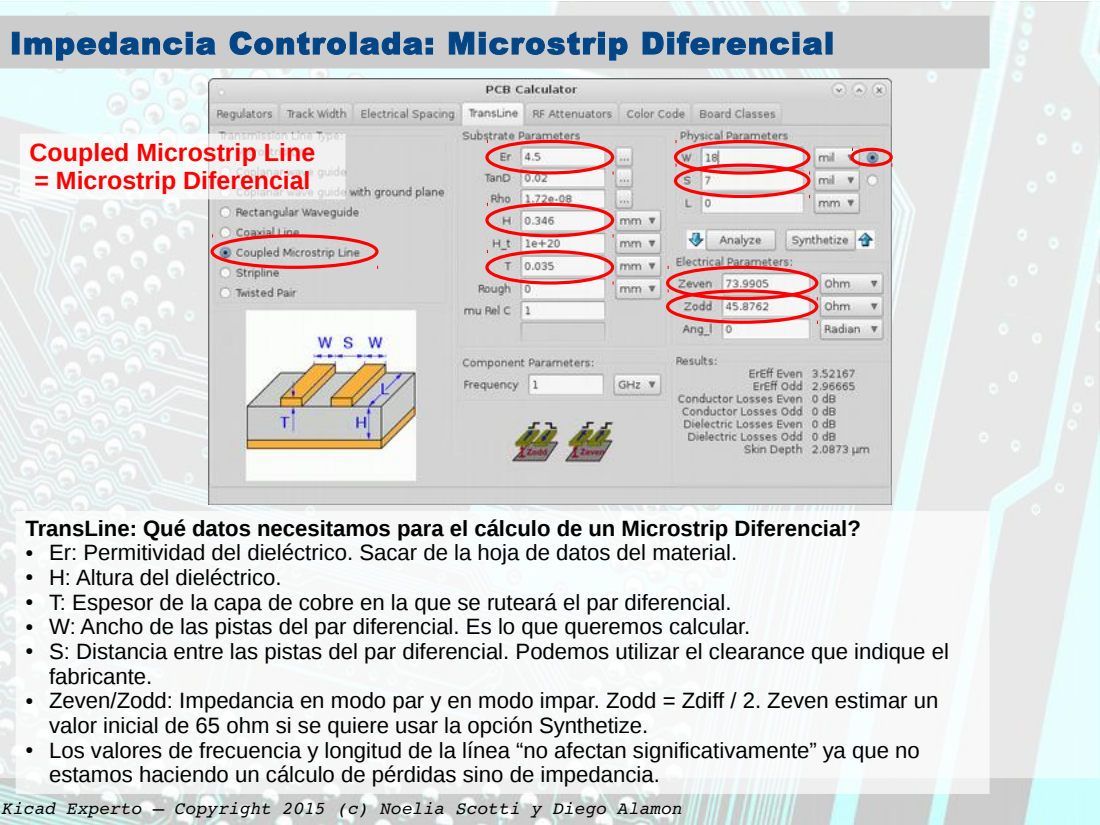
[picture p186: page 19]

Coupled Microstrip Line
= Microstrip Diferencial

TransLine: Qué datos necesitamos para el cálculo de un Microstrip Diferencial?
● Er: Permitividad del dieléctrico. Sacar de la hoja de datos del material.
● H: Altura del dieléctrico.
● T: Espesor de la capa de cobre en la que se ruteará el par diferencial.
● W: Ancho de las pistas del par diferencial. Es lo que queremos calcular.
● S: Distancia entre las pistas del par diferencial. Podemos utilizar el clearance que indique el
fabricante.
● Zeven/Zodd: Impedancia en modo par y en modo impar. Zodd = Zdiff / 2. Zeven estimar un
valor inicial de 65 ohm si se quiere usar la opción Synthetize.
● Los valores de frecuencia y longitud de la línea “no afectan significativamente” ya que no
estamos haciendo un cálculo de pérdidas sino de impedancia.

## Impedancia Controlada: Ejemplo de cálculo

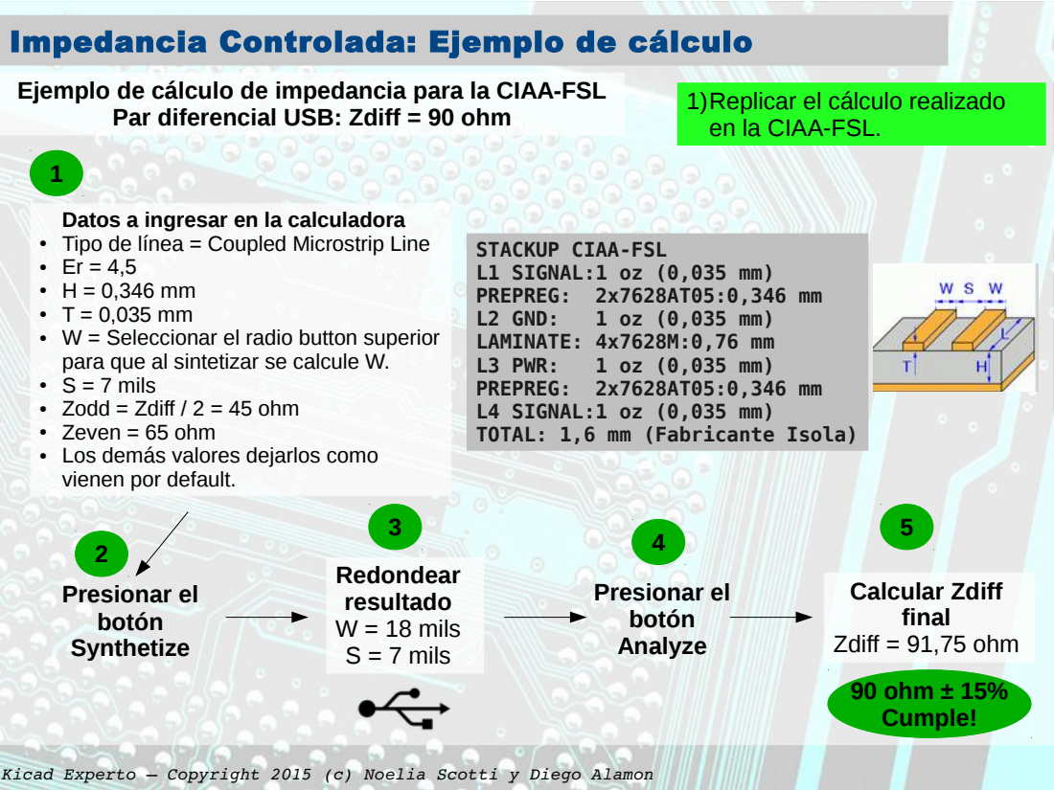
[picture p187: page 20]
L2 GND:; L3 PWR:; Redondear resultado W = 18 mils S = 7 mils; Presionar el botón Synthetize; Calcular Zdiff final Zdiff = 91,75 ohm; 90 ohm ± 15% Cumple!; Presionar el botón Analyze

Ejemplo de cálculo de impedancia para la CIAA-FSL

1)Replicar el cálculo realizado
en la CIAA-FSL.

Par diferencial USB: Zdiff = 90 ohm

Datos a ingresar en la calculadora
● Tipo de línea = Coupled Microstrip Line
● W = Seleccionar el radio button superior
para que al sintetizar se calcule W.
● S = 7 mils
● Zodd = Zdiff / 2 = 45 ohm
● Zeven = 65 ohm
● Los demás valores dejarlos como
vienen por default.

STACKUP CIAA-FSL
L1 SIGNAL:1 oz (0,035 mm)
PREPREG: 2x7628AT05:0,346 mm
LAMINATE: 4x7628M:0,76 mm
L4 SIGNAL:1 oz (0,035 mm)
TOTAL: 1,6 mm (Fabricante Isola)

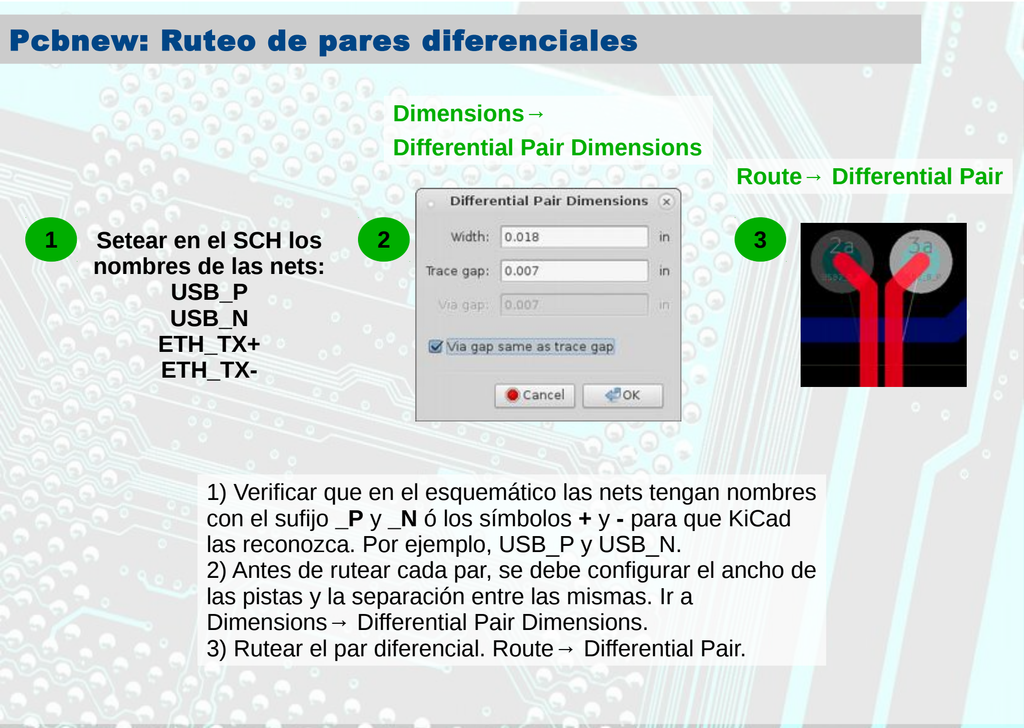
[picture p188: figure]
Pcbnew: Ruteo de pares diferenciales; Dimensions→ Differential Pair Dimensions.; Dimensions→ Differential Pair Dimensions; Setear en el SCH los; nombres de las nets: USB_P USB_N ETH_TX+ ETH_TX-; Route→ Differential Pair

1) Verificar que en el esquemático las nets tengan nombres con el sufijo _P y _N ó los símbolos + y - para que KiCad las reconozca. Por ejemplo, USB_P y USB_N.
2) Antes de rutear cada par, se debe configurar el ancho de las pistas y la separación entre las mismas. Ir a
3) Rutear el par diferencial. Route→ Differential Pair.

## Pcbnew: Ruteo de pares diferenciales

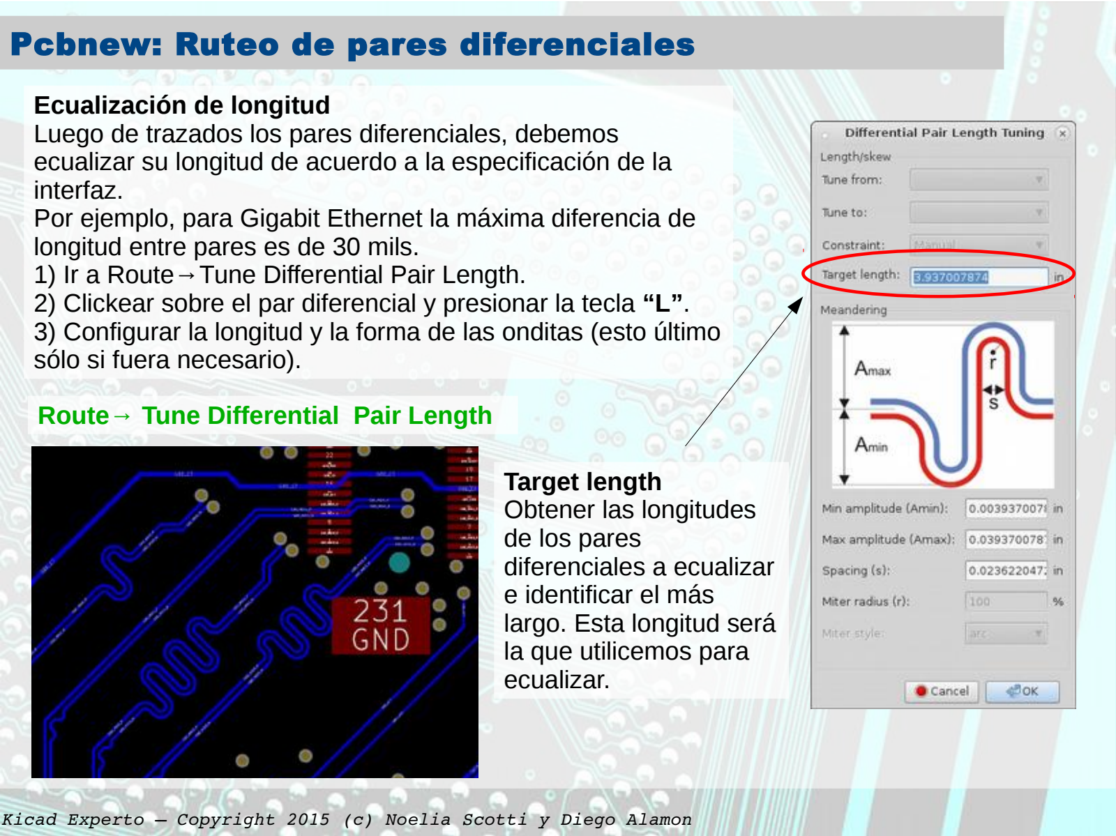
[picture p189: page 22]

Ecualización de longitud
Luego de trazados los pares diferenciales, debemos ecualizar su longitud de acuerdo a la especificación de la interfaz.
Por ejemplo, para Gigabit Ethernet la máxima diferencia de longitud entre pares es de 30 mils.
1) Ir a Route→Tune Differential Pair Length.
2) Clickear sobre el par diferencial y presionar la tecla “L”.
3) Configurar la longitud y la forma de las onditas (esto último sólo si fuera necesario).

Route→ Tune Differential Pair Length

Target length
Obtener las longitudes
de los pares
diferenciales a ecualizar
e identificar el más
largo. Esta longitud será
la que utilicemos para
ecualizar.

## Pcbnew: Ruteo de pares diferenciales

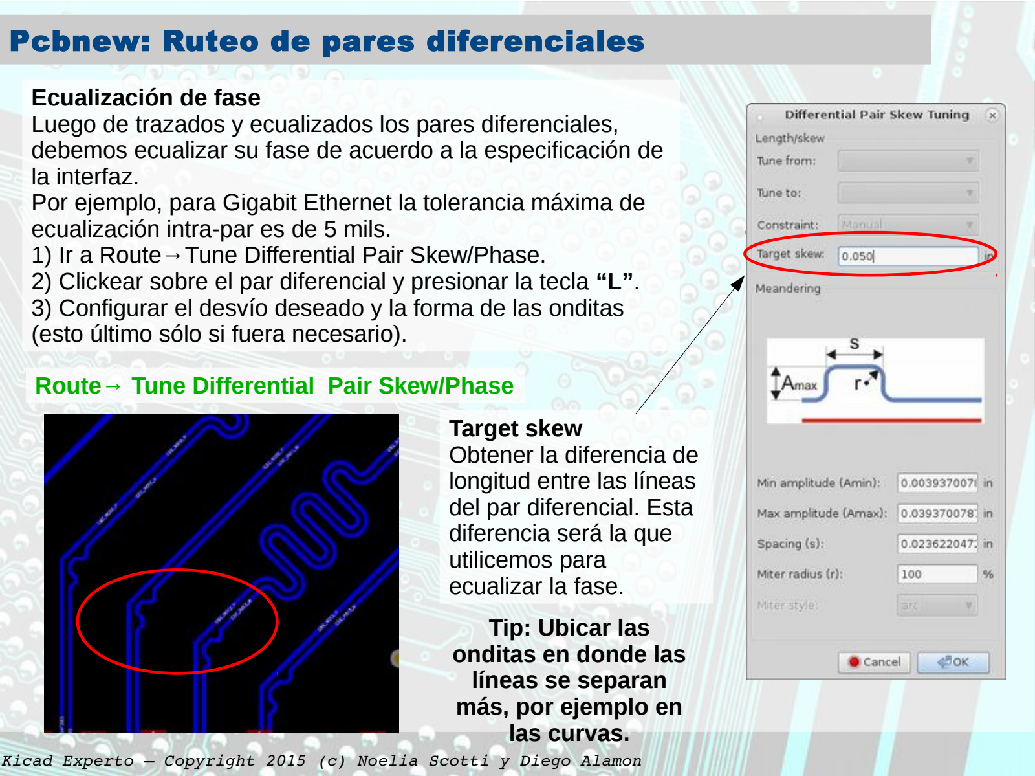
[picture p190: page 23]

Ecualización de fase
Luego de trazados y ecualizados los pares diferenciales, debemos ecualizar su fase de acuerdo a la especificación de la interfaz.
Por ejemplo, para Gigabit Ethernet la tolerancia máxima de ecualización intra-par es de 5 mils.
1) Ir a Route→Tune Differential Pair Skew/Phase.
2) Clickear sobre el par diferencial y presionar la tecla “L”.
3) Configurar el desvío deseado y la forma de las onditas (esto último sólo si fuera necesario).

Route→ Tune Differential Pair Skew/Phase
Target skew
Obtener la diferencia de
longitud entre las líneas
del par diferencial. Esta
diferencia será la que
utilicemos para
ecualizar la fase.
Tip: Ubicar las
onditas en donde las
líneas se separan
más, por ejemplo en
las curvas.

## Pcbnew: Ruteo de pares diferenciales IV

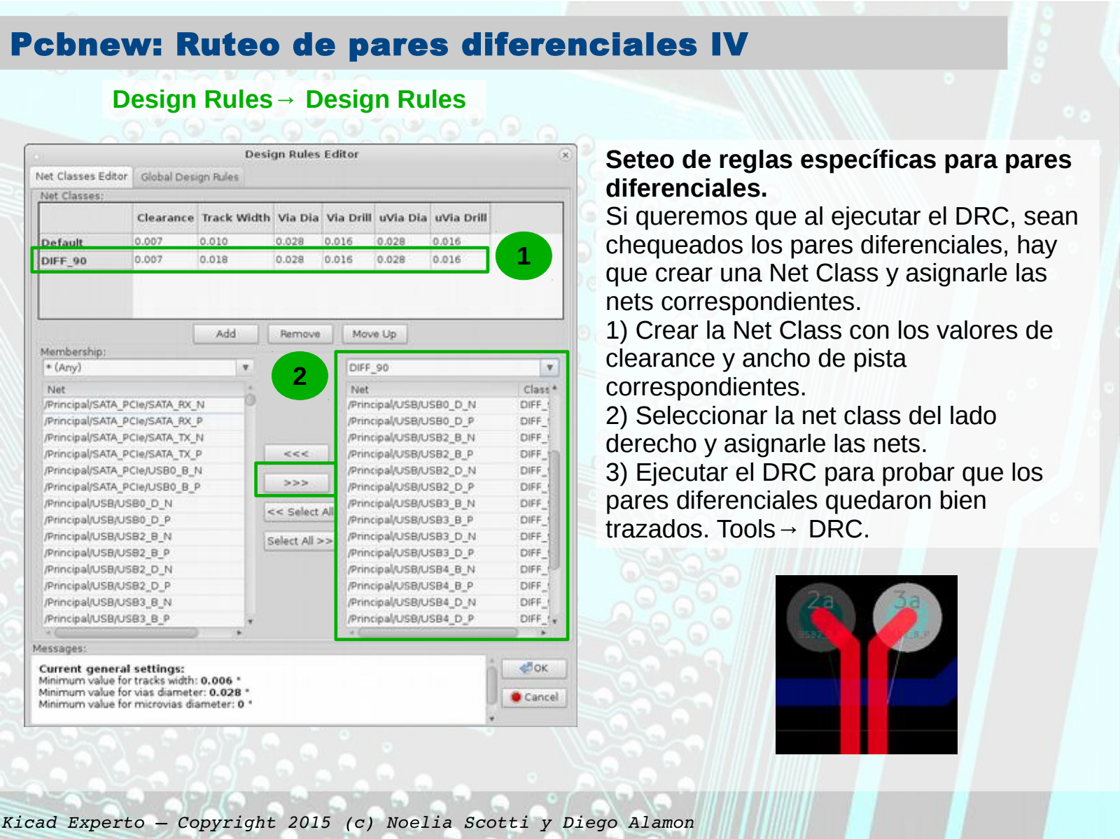
[picture p191: page 24]

Seteo de reglas específicas para pares diferenciales.
Si queremos que al ejecutar el DRC, sean chequeados los pares diferenciales, hay que crear una Net Class y asignarle las nets correspondientes.
1) Crear la Net Class con los valores de clearance y ancho de pista correspondientes.
2) Seleccionar la net class del lado derecho y asignarle las nets.
3) Ejecutar el DRC para probar que los pares diferenciales quedaron bien trazados. Tools→ DRC.

Design Rules→ Design Rules

1

2

## Auto Router en Kicad

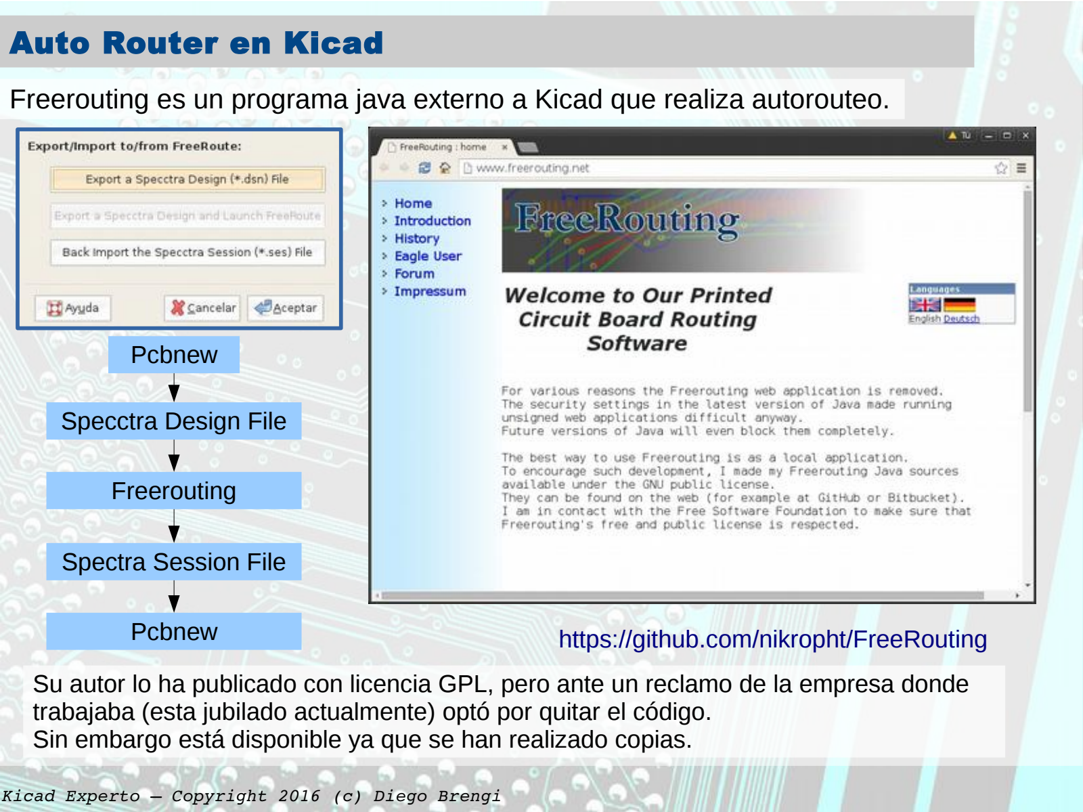
[picture p192: page 25]

Freerouting es un programa java externo a Kicad que realiza autorouteo.

Su autor lo ha publicado con licencia GPL, pero ante un reclamo de la empresa donde trabajaba (esta jubilado actualmente) optó por quitar el código.
Sin embargo está disponible ya que se han realizado copias.

https://github.com/nikropht/FreeRouting

Pcbnew

Specctra Design File

Freerouting

Spectra Session File

Pcbnew

## Auto router en KiCad

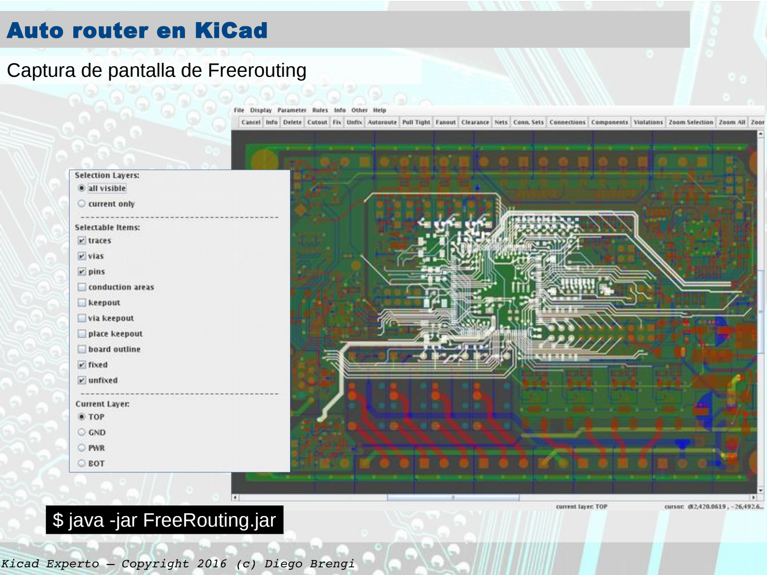
[picture p193: page 26]

Captura de pantalla de Freerouting

$ java -jar FreeRouting.jar

## Imágenes de esta presentación

Las imágenes de clipart se tomaron de: https://openclipart.org/

Los demás logos corresponden a proyectos de Software Libre u Open Source. Consultar cada licencia en particular.

Todas las capturas de pantalla fueron realizadas por los autores y están bajo la misma licencia que esta presentación.

Carátula principal:
Foto titulada “Circuit” de Yuri Samoilov bajo licencia CC-BY disponible en https://www.flickr.com/photos/yusamoilov/14011462899/

Fondo de la presentación:
Foto titulada “computer motherboard tracks” de Creativity103 bajo licencia CC-BY disponible en: https://www.flickr.com/photos/creative_stock/5228433146/

El resto de las imágenes se cita la fuente debajo de cada una.

Versión
26/07/16
Adaptación: Diego Brengi - djavier@ieee.org

Bajo Licencia Attribution-NonCommercial-NoDerivatives 4.0 International (CC BY-NC-ND 4.0)
