brengi/CESE-PCB/doc/2016_curso1/KiCad_Tour_CESE.pdf

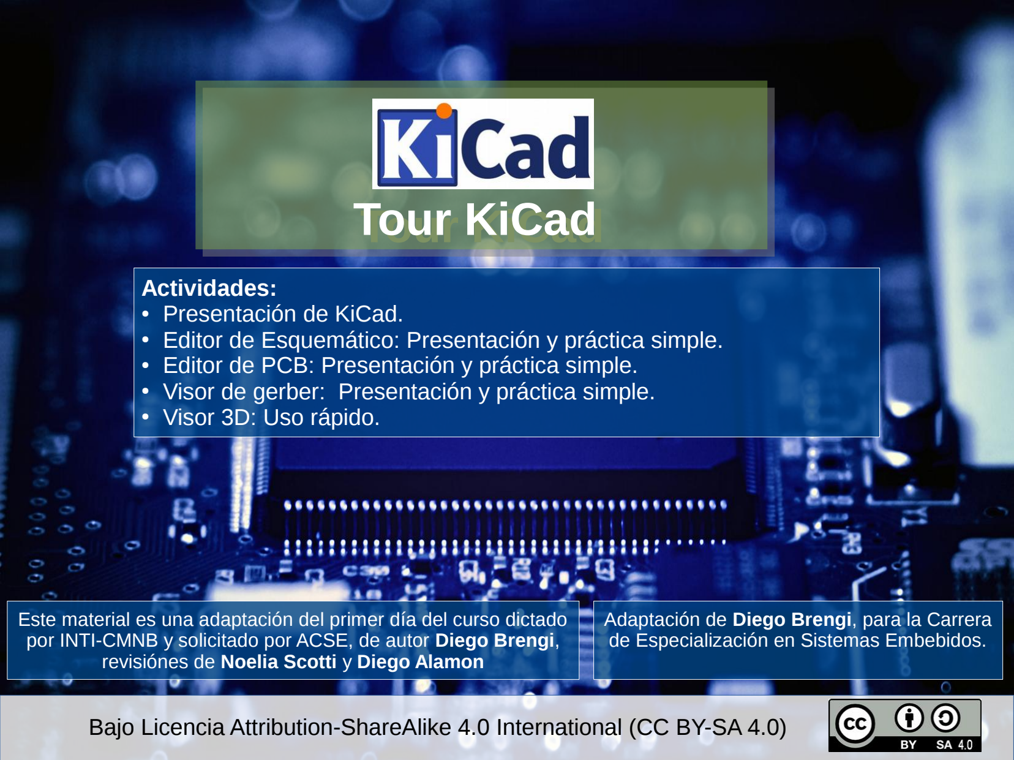
[picture p194: page 1]

# Tour KiCad

Actividades:
- Presentación de KiCad.
- Editor de Esquemático: Presentación y práctica simple.
- Editor de PCB: Presentación y práctica simple.
- Visor de gerber: Presentación y práctica simple.
- Visor 3D: Uso rápido.

Bajo Licencia Attribution-ShareAlike 4.0 International (CC BY-SA 4.0)

Este material es una adaptación del primer día del curso dictado por INTI-CMNB y solicitado por ACSE, de autor Diego Brengi, revisiónes de Noelia Scotti y Diego Alamon

Adaptación de Diego Brengi, para la Carrera de Especialización en Sistemas Embebidos.

## Introducción a KiCad

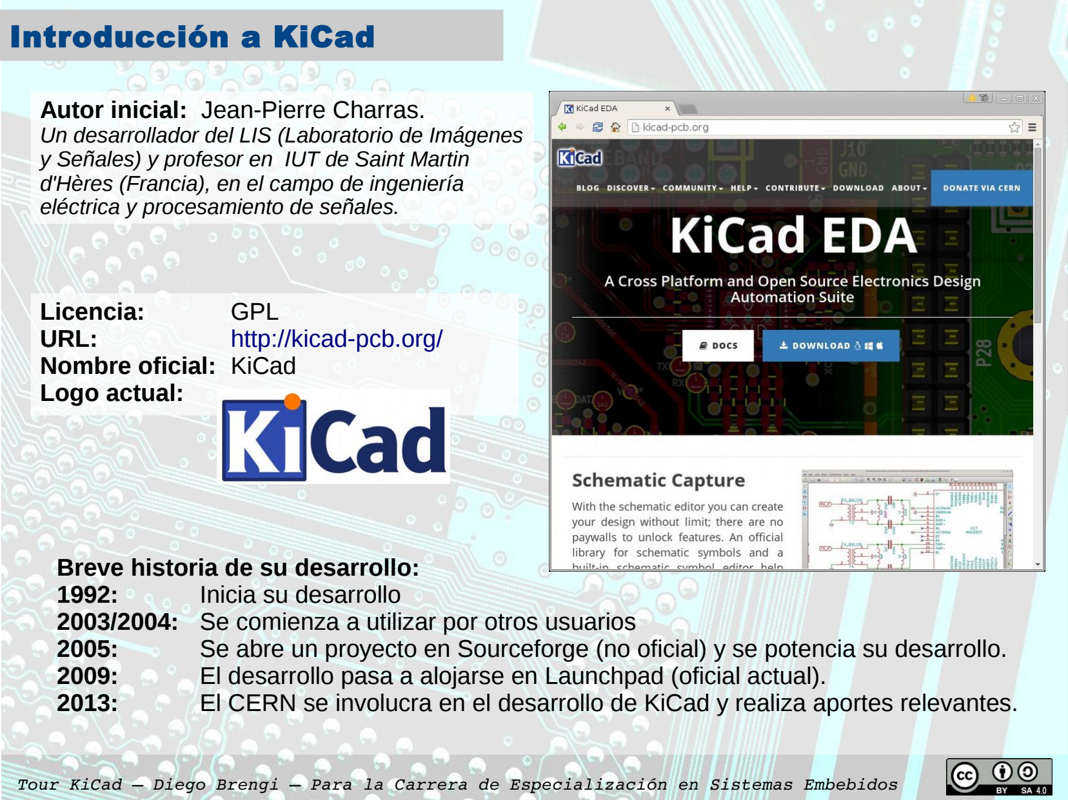
[picture p195: page 2]

Tour KiCad – Diego Brengi – Para la Carrera de Especialización en Sistemas Embebidos

Autor inicial: Jean-Pierre Charras.
Un desarrollador del LIS (Laboratorio de Imágenes y Señales) y profesor en IUT de Saint Martin d'Hères (Francia), en el campo de ingeniería eléctrica y procesamiento de señales.
Licencia: | GPL
URL: | http://kicad-pcb.org/
Nombre oficial: KiCad
Logo actual:

Breve historia de su desarrollo:
1992: | Inicia su desarrollo
2003/2004: Se comienza a utilizar por otros usuarios
2005: | Se abre un proyecto en Sourceforge (no oficial) y se potencia su desarrollo.
2009: | El desarrollo pasa a alojarse en Launchpad (oficial actual).
2013: | El CERN se involucra en el desarrollo de KiCad y realiza aportes relevantes.

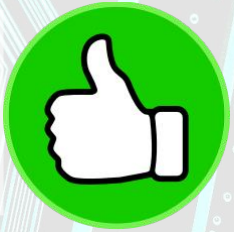
[picture p196: figure]

Ventajas principales
- Disponibilidad del código fuente.
- Gratuito.
- Formatos abiertos y documentados.
- Formatos en modo texto (ascii).
- Multiplataforma: Linux, Windows y Mac.
- Utilizado en la mayoría de los proyectos actuales Open Source y/o Hardware Libre actuales.

## Introducción a KiCad

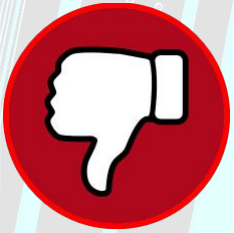
[picture p197: figure]

Desventajas
- Documentación cambiante.
- Cambios constantes en formatos (mejoras).
- Diferencias entre distintas versiones.
- Necesita seguir mejorando su interfaz.
- Necesita incorporar funcionalidades para optimizar tiempos y para circuitos más complejos.

## Partes Principales de KiCad Administrador de proyecto:

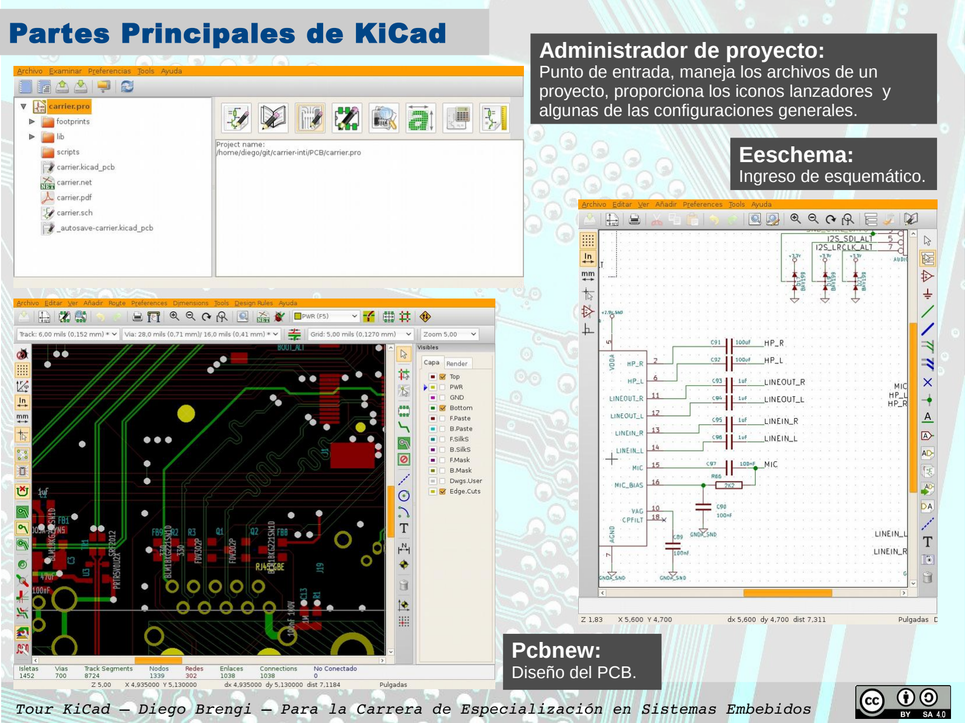
[picture p198: page 4]

Punto de entrada, maneja los archivos de un proyecto, proporciona los iconos lanzadores y algunas de las configuraciones generales.
Eeschema:
Ingreso de esquemático.

Pcbnew:
Diseño del PCB.

## Partes Principales de KiCad

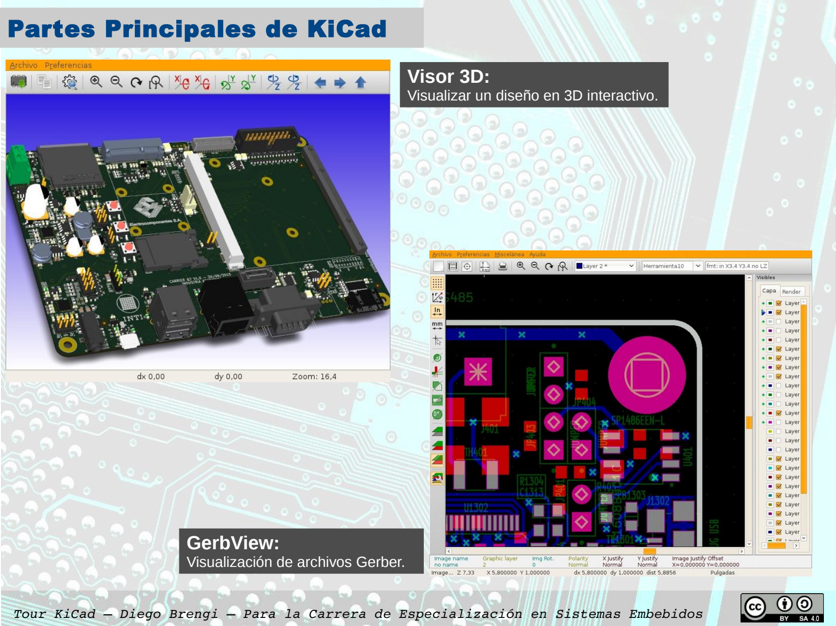
[picture p199: page 5]

GerbView:
Visualización de archivos Gerber.

Visor 3D:
Visualizar un diseño en 3D interactivo.

## Partes Principales de KiCad

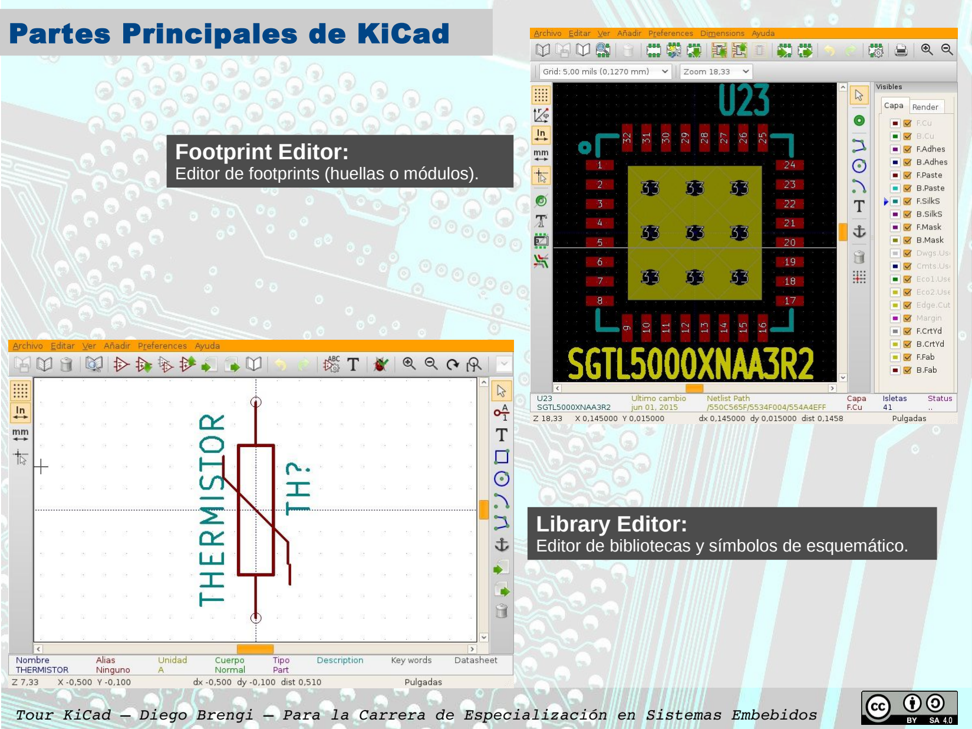
[picture p200: page 6]

Library Editor:
Editor de bibliotecas y símbolos de esquemático.

Footprint Editor:
Editor de footprints (huellas o módulos).

## Partes Principales de KiCad

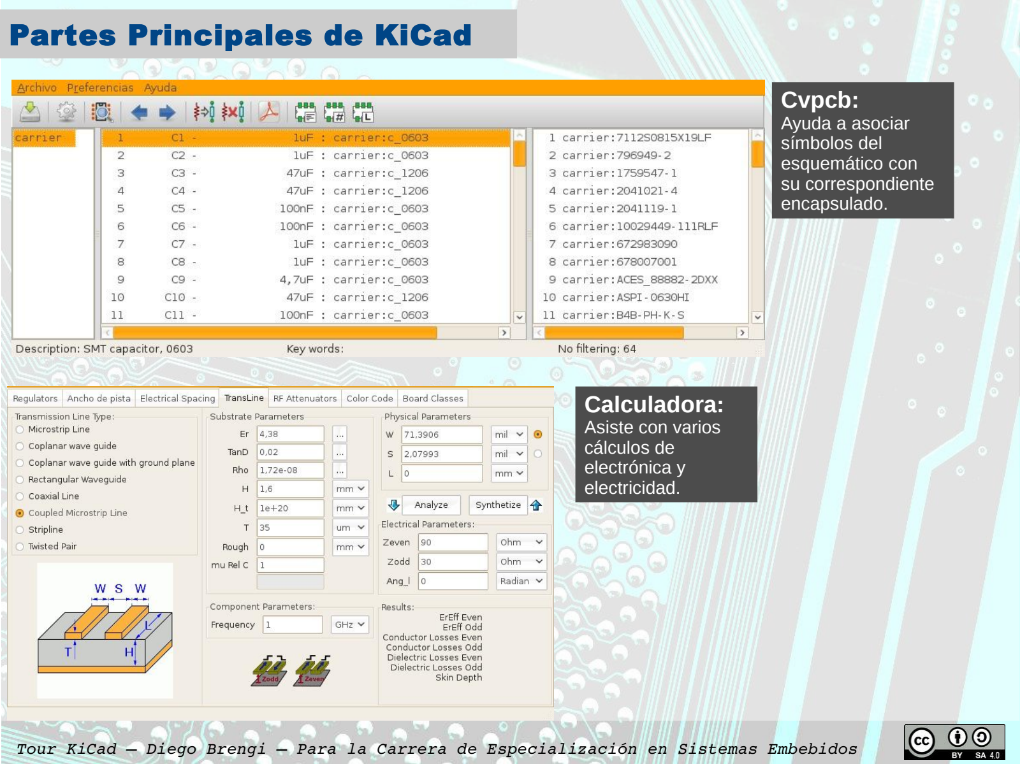
[picture p201: page 7]

Cvpcb:
Ayuda a asociar
símbolos del
esquemático con
su correspondiente
encapsulado.

Calculadora:
Asiste con varios
cálculos de
electrónica y
electricidad.

## Partes Principales de KiCad

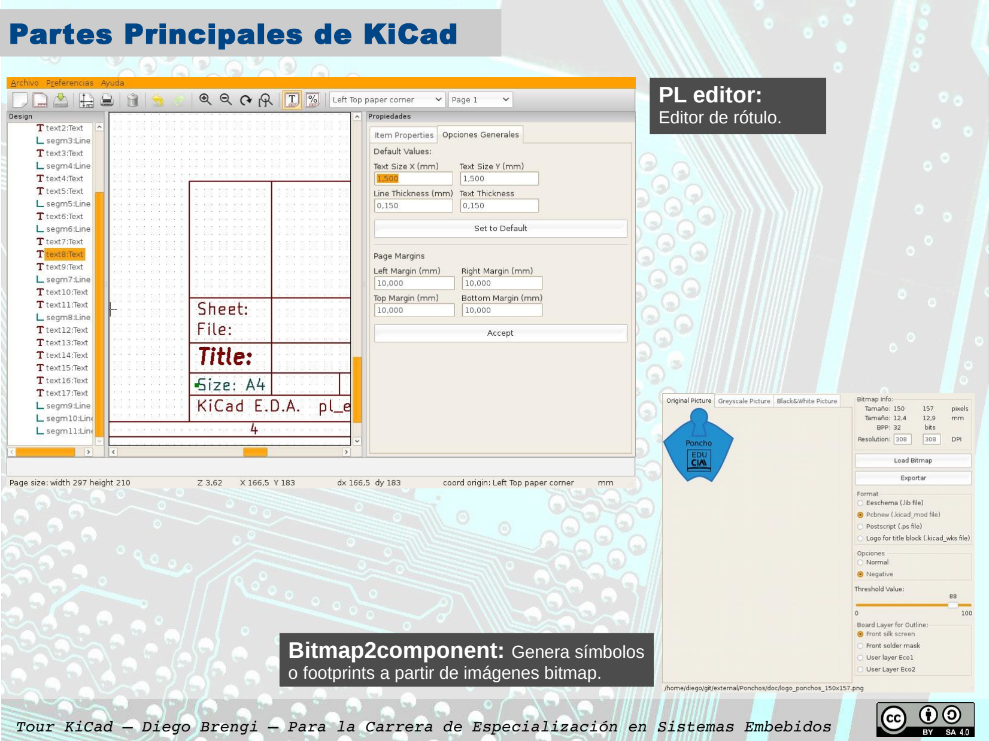
[picture p202: page 8]

PL editor:
Editor de rótulo.

Bitmap2component: Genera símbolos
o footprints a partir de imágenes bitmap.

El desarrollo de KiCad se lleva en https://launchpad.net/ y el código se maneja mediante Bazaar (similar a GIT).

Las versiones para Windows y Linux se pueden bajar del siguiente enlace:

http://kicad-pcb.org/download/

## Versiones estables

Product: En desarrollo constante. Pre-release (Freeze): Rama donde solo se limpan errores para convertirse en estable. Estable: Versión probada y depurada.

VERSION RECOMENDADA
PARA LA ACTIVIDAD:

## 4.0.2 (28 Feb 2016)

Dic 2012
Cambio del formato de archivo de PCB y de Footprint:
Formato del PCB .brd →
.kicad_pcb
Formato .mod → .kicad_mod
Sep 2013
Push&Shove.
2014
Cambios en formato de librerías de footprints (.pretty y .kicad_mod) Jun 2014
Router interactivo.
Jul 2014
Mejoras en el editor de módulos. Mar 2015
Líneas diferenciales.
Mar 2015
Cambio en bibliotecas por defecto del esquemático. Resistores y capacitores más compactos
(quedan desconectados en viejos diseños). Diodos y LEDs cambian la numeración de ánodo y cátodo.

## Cambios relevantes en KiCad

## CUIDADO!

Al abrir diseños hechos con versiones viejas de KiCad, pueden aparecer algunos problemas:
- Componentes desconectados en el esquemático.
- Diodos y LEDs conectados al revés.
- Textos en otra posición.
- Errores de corrección de .brd a .kicad_pcb

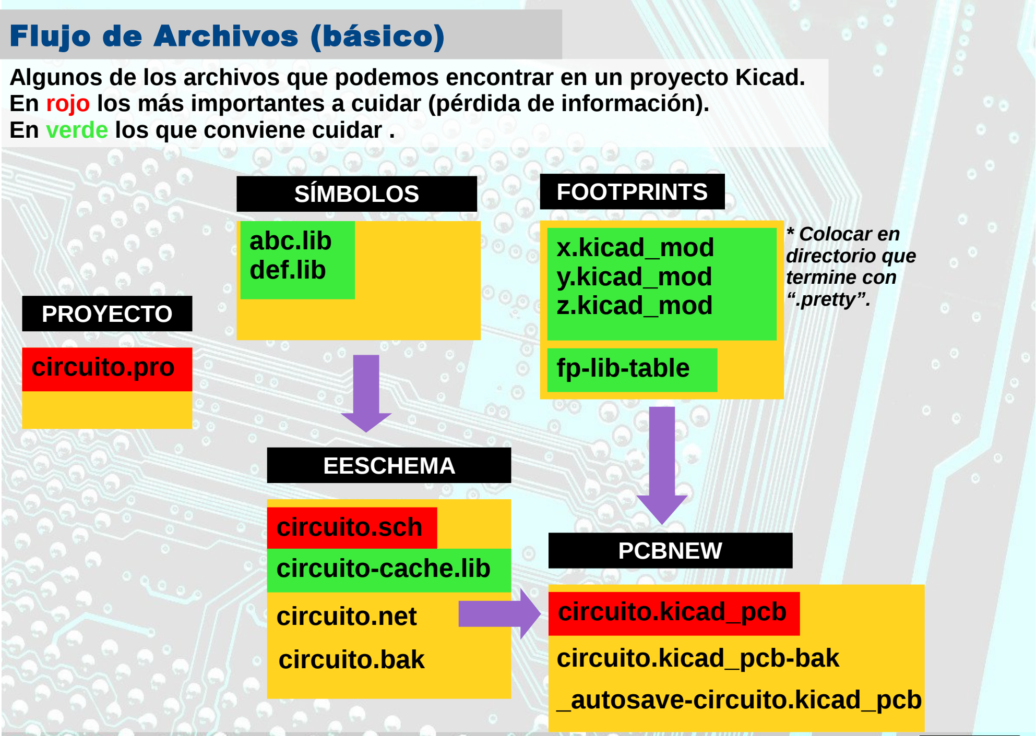
[picture p203: figure]
En verde los que conviene cuidar .; Flujo de Archivos (básico); circuito.pro; circuito.sch; circuito.kicad_pcb; circuito-cache.lib; fp-lib-table; circuito.net; PROYECTO; SÍMBOLOS; PCBNEW; FOOTPRINTS; EESCHEMA; circuito.kicad_pcb-bak; abc.lib def.lib; x.kicad_mod y.kicad_mod z.kicad_mod; * Colocar en directorio que termine con “.pretty”.; circuito.bak; _autosave-circuito.kicad_pcb

Algunos de los archivos que podemos encontrar en un proyecto Kicad. En rojo los más importantes a cuidar (pérdida de información).

# KiCad

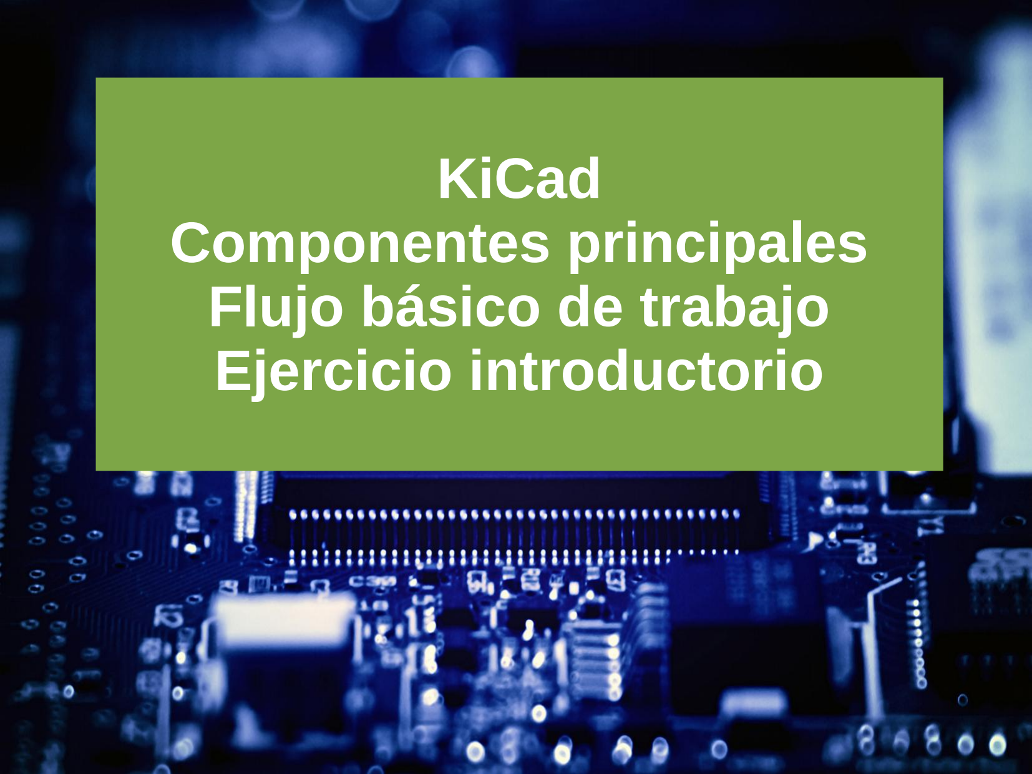
[picture p204: page 12]

# Componentes principales Flujo básico de trabajo Ejercicio introductorio

## Ejercicio 1 – Ejercicio Introductorio

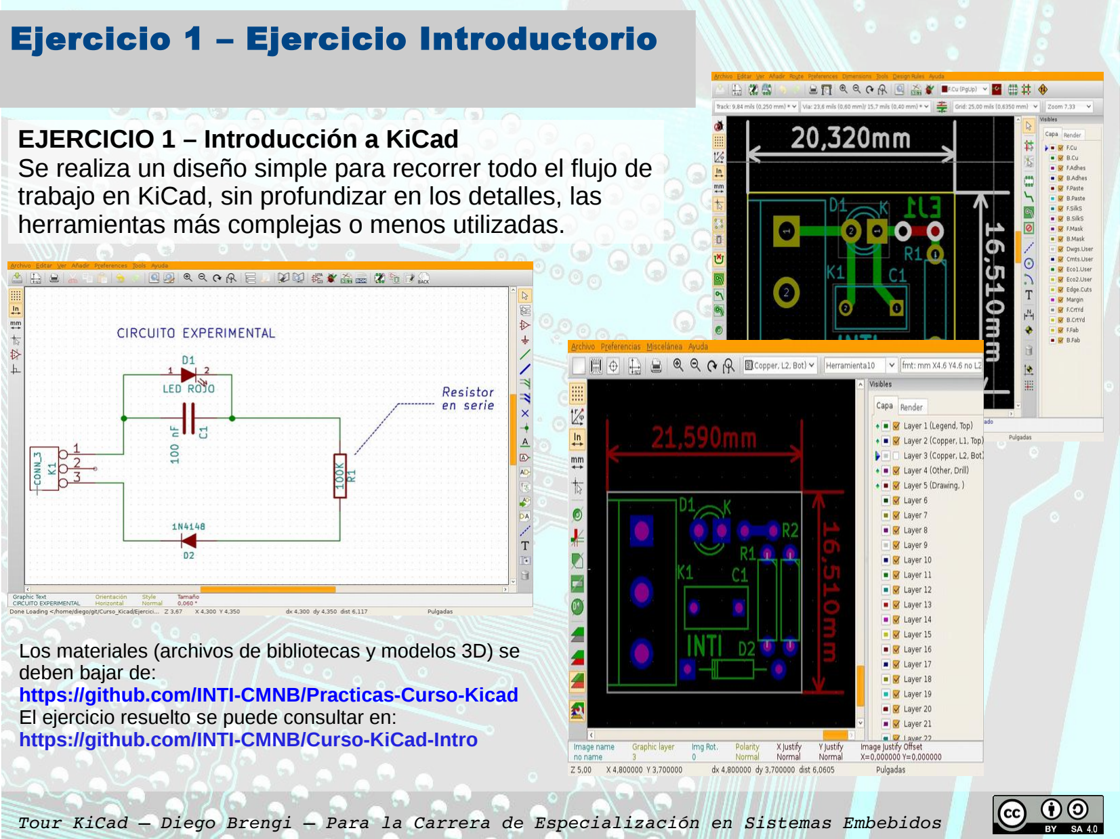
[picture p205: page 13]

EJERCICIO 1 – Introducción a KiCad
Se realiza un diseño simple para recorrer todo el flujo de trabajo en KiCad, sin profundizar en los detalles, las herramientas más complejas o menos utilizadas.

Los materiales (archivos de bibliotecas y modelos 3D) se deben bajar de:
https://github.com/INTI-CMNB/Practicas-Curso-Kicad El ejercicio resuelto se puede consultar en: https://github.com/INTI-CMNB/Curso-KiCad-Intro

# Administrador

de

# Proyectos

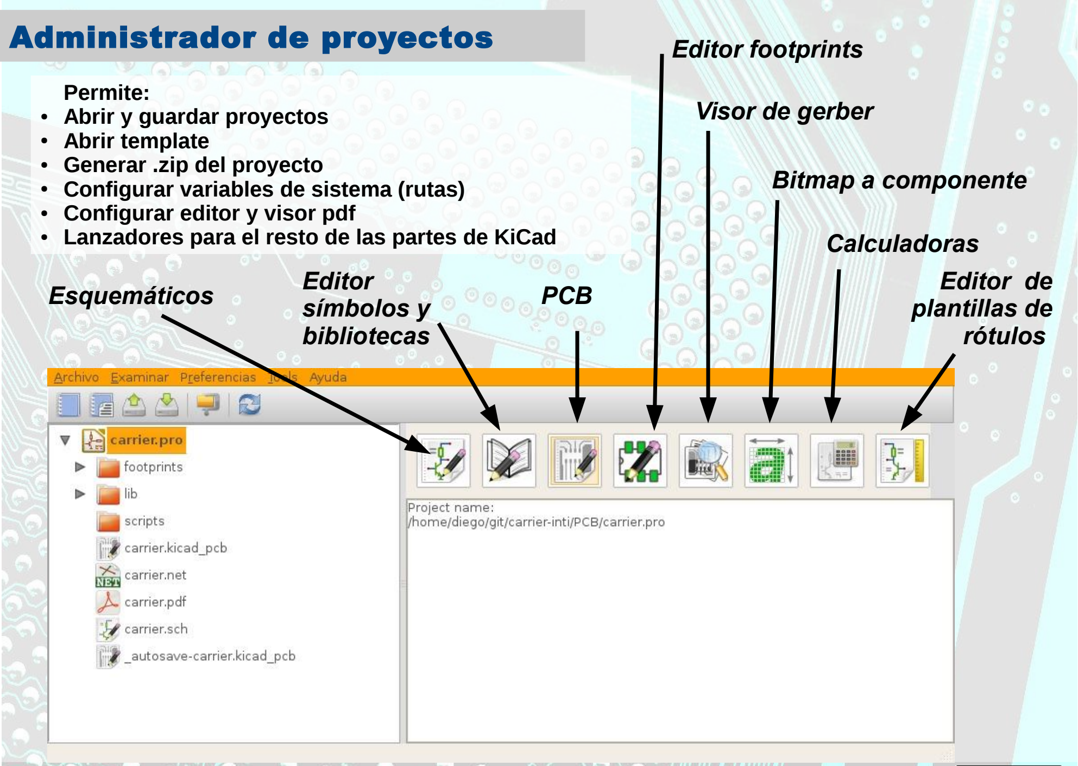
[picture p206: figure]
Permite: ● Abrir y guardar proyectos ● Abrir template ● Generar .zip del proyecto; ● Configurar editor y visor pdf; Administrador de proyectos; Esquemáticos; Editor; símbolos y bibliotecas; PCB; Editor footprints; Visor de gerber; Bitmap a componente; Calculadoras Editor de plantillas de rótulos

- Configurar variables de sistema (rutas)
- Lanzadores para el resto de las partes de KiCad

Ejercicio:

1)Abrir proyecto nuevo. Usar como nombre: Apellido_Nombre, evitando los espacios y acentos. Aceptar la recomendación de utilizar un directorio vacío.
2) Observar los archivos creados.
3)En el administrador de proyectos configurar un editor de texto (estilo block de notas o Notepad++).
4)Abrir el esquemático y el pcb recién creados con el editor de textos.

## Administrador de proyectos

Estos cuadros verdes
contienen las instrucciones a
seguir para realizar el ejercicio.

# Editor de Esquemáticos (Eeschema)

## Eeschema – Editor de Esquemáticos

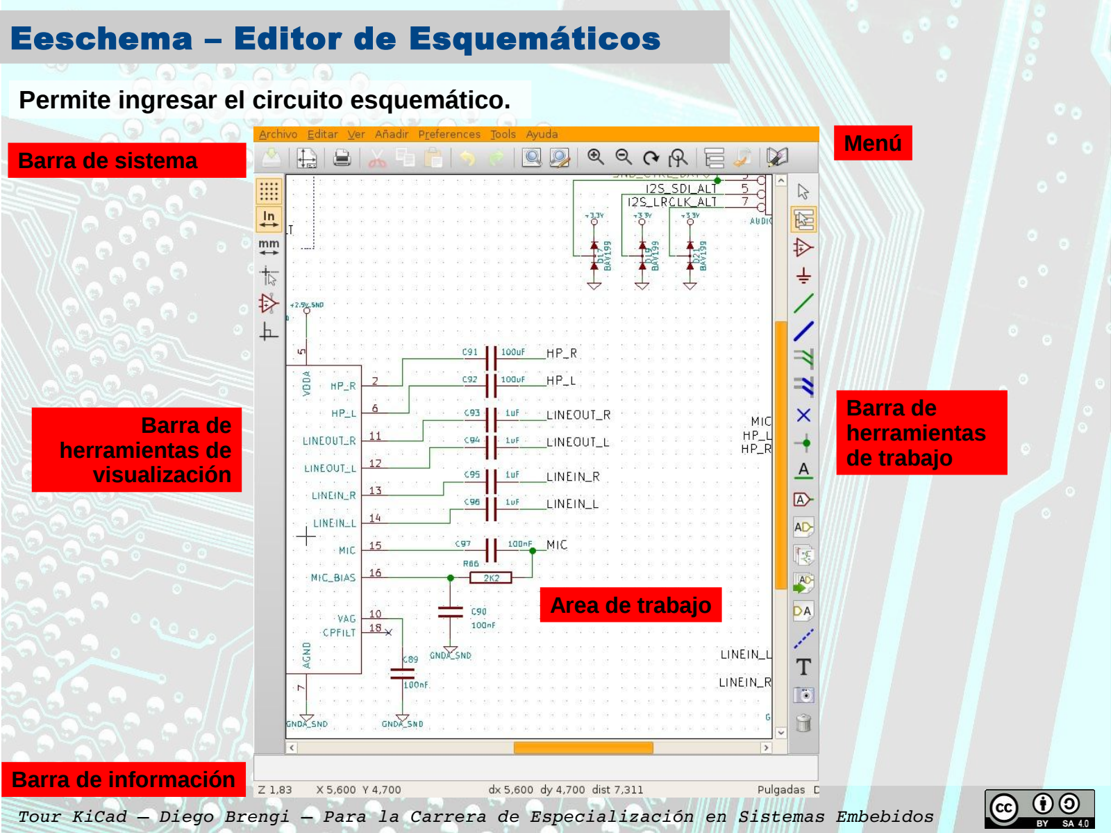
[picture p207: page 18]

Permite ingresar el circuito esquemático.

Area de trabajo

Barra de
herramientas de
visualización

Barra de
herramientas
de trabajo

Barra de sistema

Menú

Barra de información

- Visualización de grilla
- Pulgadas
- Milímetros
- Tipo de cursor
- Mostrar pines ocultos
- Solo líneas verticales u horizontales

## Eeschema – Barra de herramientas de visualización

En verde las opciones
para investigar y
probar en el primer
ejercicio.

Cursor general
Subir/bajar jerarquía
Colocar símbolo nuevo
Colocar símbolo de alimentación Cables
Buses
Entrada de cable
Entrada de bus
Sin conexión
Unión
Colocar Etiqueta para nodo (local) Colocar Etiqueta global
Crear etiqueta jerárquica en esquemático Crear nueva hoja jerárquica Importar pin dentro de hoja jerárquica Crear pin jerárquico en hoja jerárquica Línea de dibujo
Colocar texto
Colocar imagen bitmap
Borrar elemento

## Eeschema – Barra de herramientas de trabajo

En verde las
opciones para
realizar y
probar en el
primer
ejercicio.

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
rimir

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
m in

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
alla

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
e je

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
biblio

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
biblio

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
al R

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
tlis

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
Bill o

f

M

a

t

e

rials

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
r .c

m

p

En verde las opciones
para realizar y probar
en el primer ejercicio.

## Eeschema – Barra de sistema

Las opciones en azul
solamente cuando se lanza
eeschema por separado.

ARCHIVO
- Trazar

PREFERENCIAS
- Bibliotecas
- Colores
- Opciones de edición
- Idioma
- Edición de shortcut keys

AYUDA
- Versión de KiCad

## Eeschema – menú

Este menú repite la mayoría de las opciones disponibles en los íconos. Aunque posee algunas opciones solamente accesibles desde aquí:

Barra de información inferior. Coordenadas relativas y
absolutas e información
contextual, por ejemplo del componente seleccionado.

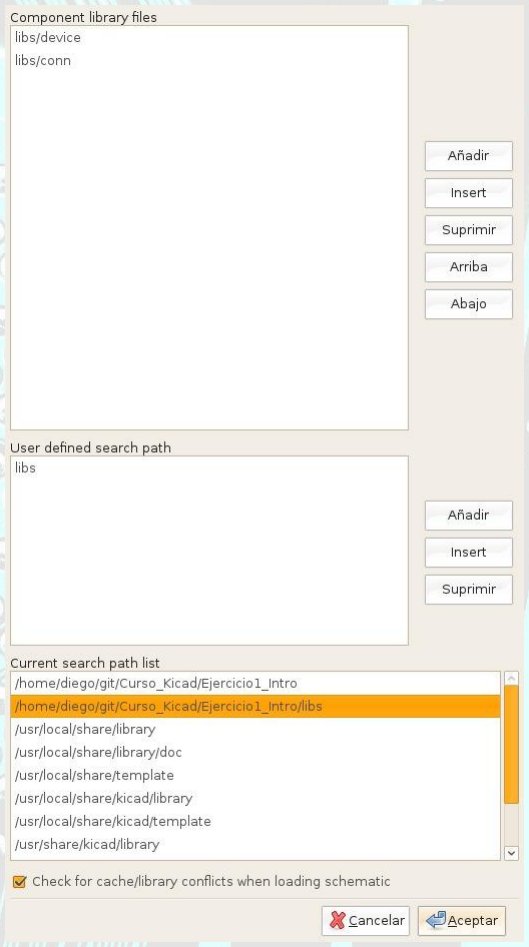
[picture p208: figure]

1)Abrir Eeschema y entrar a la configuración de bibliotecas. 2)Eliminar todas las bibliotecas. 3)Agregar una ruta de búsqueda de usuario (relativa al
directorio de proyecto).
4)Agregar las dos bibliotecas de símbolos que se utilizarán en el ejercicio.

## Ejercicio 1 – Configurar las bibliotecas de símbolos

Para el ejercicio utilizaremos las bibliotecas de
símbolos provistas en el subdirectorio “libs”.
En este ejercicio solo necesitamos las siguientes
bibliotecas:
- device: Dispositivos discretos más comunes.
- conn: Conectores genéricos.

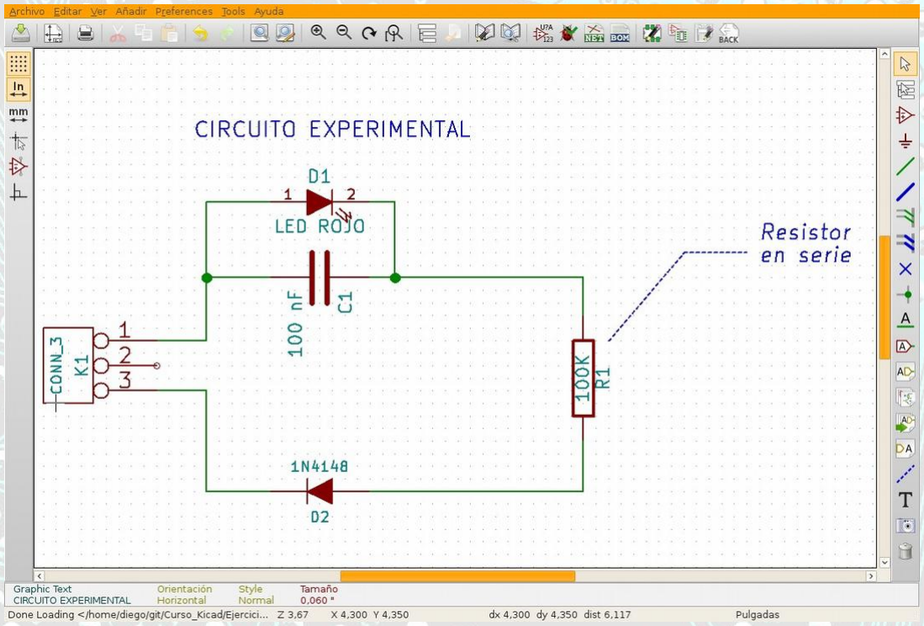
[picture p209: figure]

1)Completar rótulo.
2)Colocar Símbolos.
3)Colocar conexiones.
4)Numeración de
componentes.
5)Completar el campo
valor.
6)Textos y líneas.
7)Chequeo ERC.
8)Flag NC.(faltaba!)
9)Generación de netlist.

## Ejercicio 1 - Esquemático

El ejercicio consiste en ingresar el siguiente circuito para ir descubriendo y probando las distintas herramientas, siguiendo las instrucciones y el orden de operaciones a continuación. Cada operación o paso se muestra en pantalla y luego se dan unos minutos para que cada participante la realice e investigue un poco el software.

## Eeschema - Hotkeys

Tecla | Operación
A | Añadir componente
G | Arrastrar elemento
V | Editar valor del componente
W | Comenzar cableado
K | Finalizar cableado
Q | Añadir flag de no conectado
T | Añadir texto
[CTRL]+S | Guardar esquemático

Más teclas en Preferencias->Hotkeys

Tecla | Operación
M | Mover elemento
R | Rotar elemento
E | editar elemento
CTRL-Z | Deshacer
[DEL] | Borrar
Teclas MUY IMPORTANTES | Otras teclas

## Ejercicio 1 – Conexiones prolijas en KiCad

El conexionado debe ser prolijo y consistente, independientemente de que el software interprete bien un circuito desprolijo.
Puntos de
unión
innecesarios.

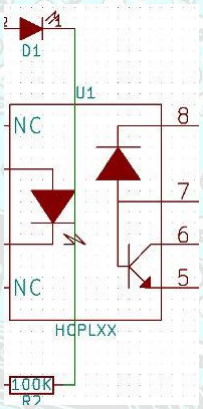
[picture p210: figure]
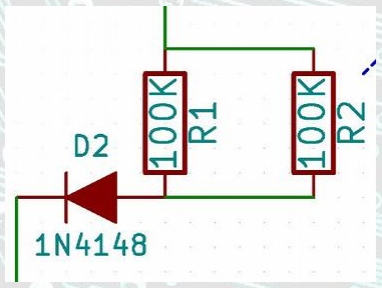
[picture p211: figure]

Sin punto de
unión.

Unión en
terminal y sin
punto.

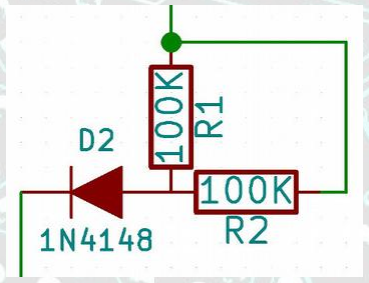
[picture p212: figure]

Unión en
terminal, sin
cable.

Unión en
terminal y con
punto.

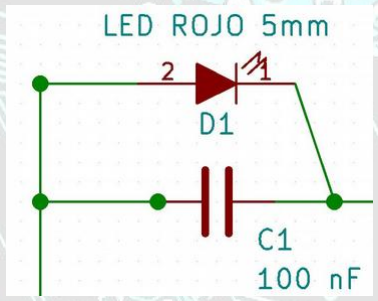
[picture p213: figure]

conexionado
cruza un
símbolo.

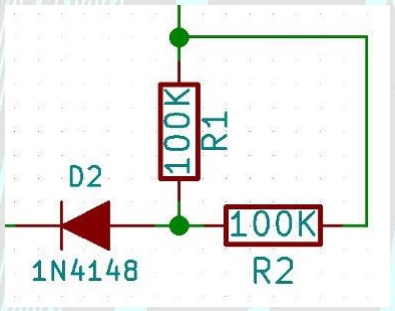
[picture p214: figure]

Consejo: Luego de un
terminal de símbolo siempre un tramo “limpio” de cable de conexión.

Línea no está
a 90 grados.

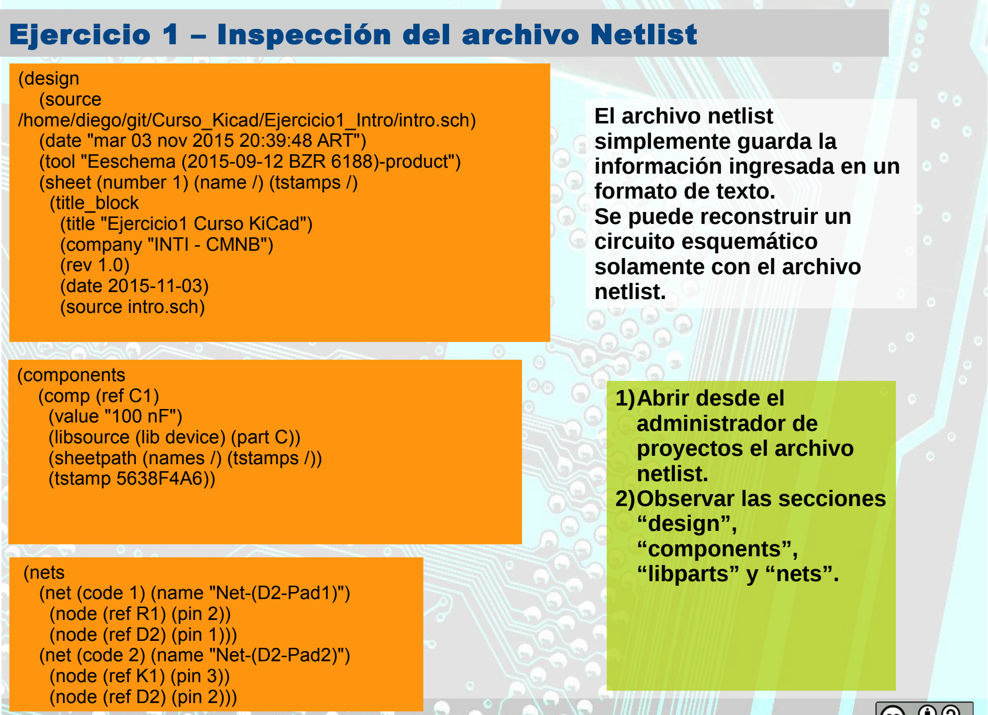
[picture p215: figure]
1)Abrir desde el administrador de proyectos el archivo netlist. 2)Observar las secciones “design”, “components”, “libparts” y “nets”.; (design (source; (date "mar 03 nov 2015 20:39:48 ART"); (sheet (number 1) (name /) (tstamps /) (title_block (title "Ejercicio1 Curso KiCad") (company "INTI - CMNB") (rev 1.0) (date 2015-11-03) (source intro.sch); (components (comp (ref C1) (value "100 nF") (libsource (lib device) (part C)) (sheetpath (names /) (tstamps /)) (tstamp 5638F4A6)); (nets (net (code 1) (name "Net-(D2-Pad1)") (node (ref R1) (pin 2)) (node (ref D2) (pin 1))) (net (code 2) (name "Net-(D2-Pad2)") (node (ref K1) (pin 3)) (node (ref D2) (pin 2))); El archivo netlist simplemente guarda la información ingresada en un formato de texto. Se puede reconstruir un circuito esquemático solamente con el archivo netlist.

## Ejercicio 1 – Inspección del archivo Netlist

/home/diego/git/Curso_Kicad/Ejercicio1_Intro/intro.sch)

(tool "Eeschema (2015-09-12 BZR 6188)-product")

## Ejercicio 1 – Asociación de footprint con Cvpcb

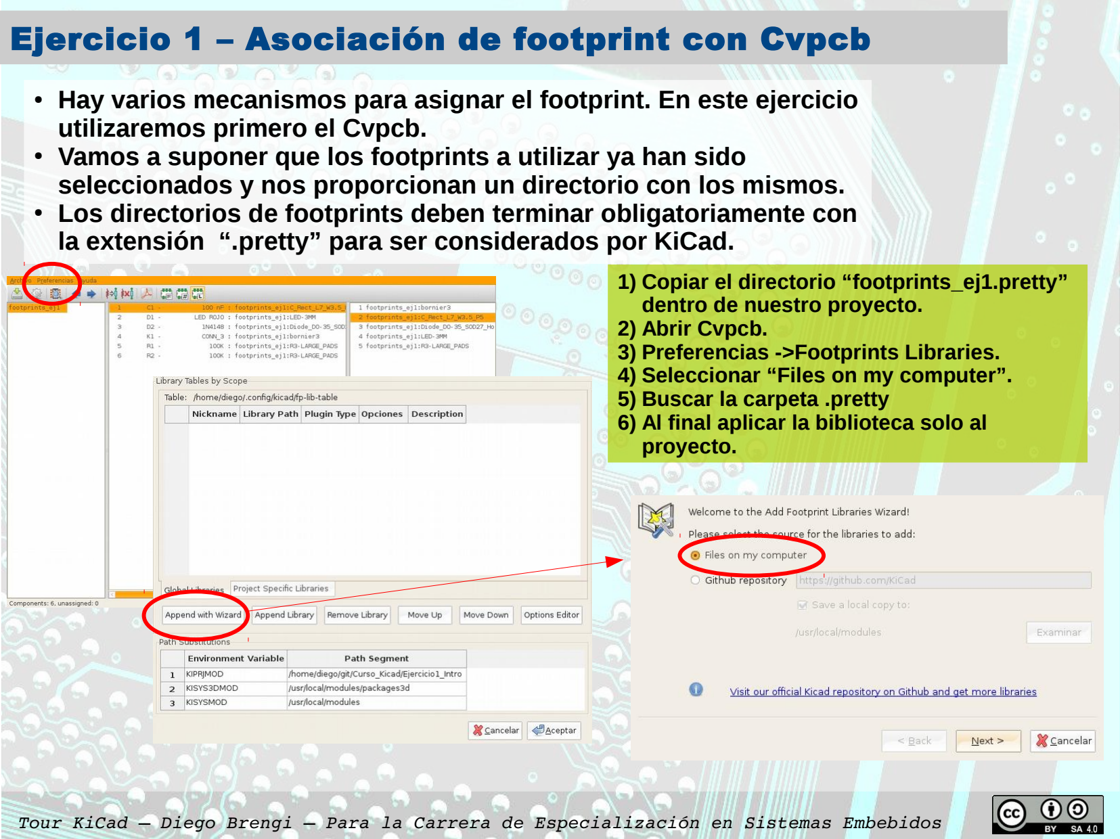
[picture p216: page 28]

1) Copiar el directorio “footprints_ej1.pretty” dentro de nuestro proyecto.
2) Abrir Cvpcb.
3) Preferencias ->Footprints Libraries.
4) Seleccionar “Files on my computer”.
5) Buscar la carpeta .pretty
6) Al final aplicar la biblioteca solo al proyecto.
- Hay varios mecanismos para asignar el footprint. En este ejercicio utilizaremos primero el Cvpcb.
- Vamos a suponer que los footprints a utilizar ya han sido seleccionados y nos proporcionan un directorio con los mismos.
- Los directorios de footprints deben terminar obligatoriamente con la extensión “.pretty” para ser considerados por KiCad.

## Ejercicio 1 – Asociación de footprint con Cvpcb

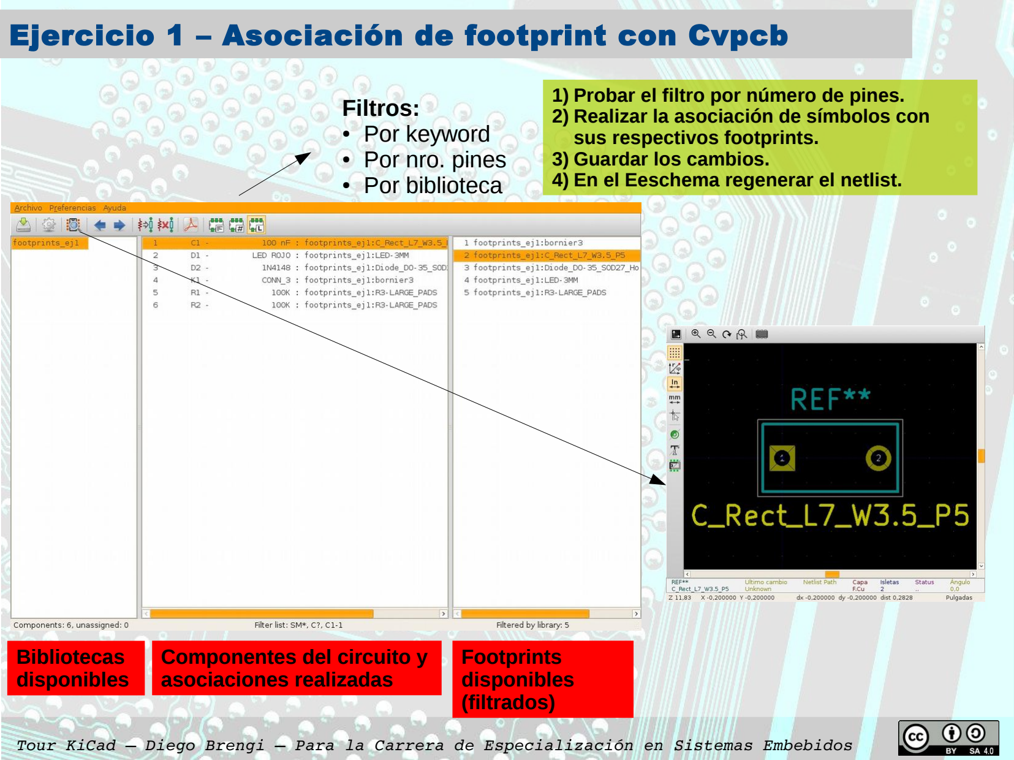
[picture p217: page 29]

Bibliotecas
disponibles

Componentes del circuito y asociaciones realizadas

Footprints
disponibles
(filtrados)

Filtros:
- Por keyword
- Por nro. pines
- Por biblioteca
1) Probar el filtro por número de pines.
2) Realizar la asociación de símbolos con sus respectivos footprints.
3) Guardar los cambios.
4) En el Eeschema regenerar el netlist.

Volvemos a revisar el netlist.

(fp_lib_table
(lib (name footprints_ej1)
(type KiCad)
(uri "$(KIPRJMOD)/footprints_ej1.pretty") (options "")
(descr ""))
)

(components
(comp (ref C1)
(value "100 nF")
(footprint footprints_ej1:C_Rect_L7_W3.5_P5) (libsource (lib device) (part C))
(sheetpath (names /) (tstamps /))
(tstamp 5638F4A6))

## Ejercicio 1 – Asociación de footprint

Se creó el archivo fp-lib-table que guarda localmente las bibliotecas de footprints utilizadas.

# Editor de PCB (Pcbnew)

## Pcbnew – Editor de PCB

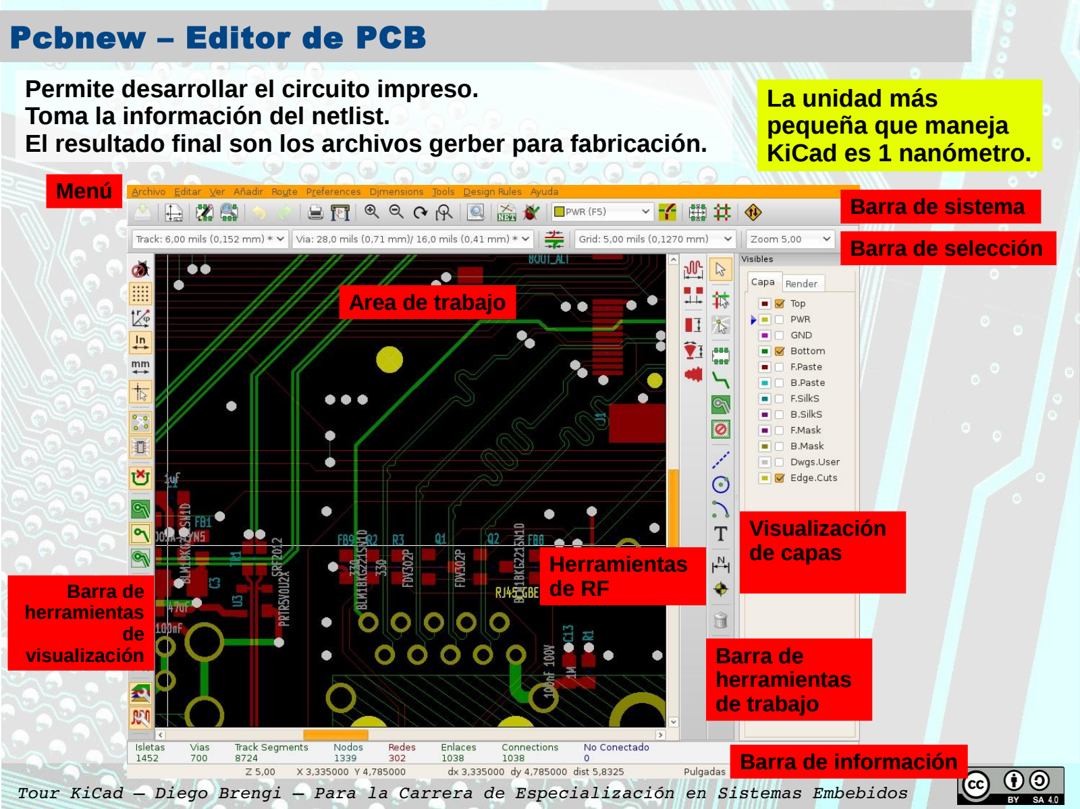
[picture p218: page 32]

Permite desarrollar el circuito impreso.
Toma la información del netlist.
El resultado final son los archivos gerber para fabricación.

Area de trabajo

Barra de
herramientas
de
visualización | Barra de
herramientas
de trabajo

Barra de sistema Menú

Barra de información

Visualización
de capas Herramientas
de RF

Barra de selección

La unidad más
pequeña que maneja
KiCad es 1 nanómetro.

Deshabilitar DRC interactivo Visualización de grilla
Coordenadas polares (relativas) Pulgadas
Milímetros
Tipo de cursor
Ocultar/mostrar ratnest
Ratnest al mover footpints
Deshabilitar auto delete tracks redundantes Mostrar zonas de cobre
No mostrar zonas de cobre
Mostrar solo contorno de zonas de cobre Mostrar solo contorno de los pads Mostrar solo contorno de las vías Mostrar solo contorno de las pistas
Modo de alto contraste
Mostrar/ocultar el panel de capas Mostrar/ocultar el panel de herramientas RF

## Pcbnew – Barra de herramientas de visualización

En verde las opciones
para probar en el
primer ejercicio.

Cursor general
Resaltador
Visualizar local ratnest
Colocar módulo
Colocar pista
Agregar zona de cobre
Area de exclusión
Dibujo de línea
Dibujo de círculo
Dibujo de arco
Colocar texto
Colocar cota
Colocar mira de centrado
Borrar elemento
Definir coord. origen para agujereado Definir coordenadas de origen de la grilla

En verde las
opciones para
realizar y probar
en el primer
ejercicio.

## Pcbnew – Barra de herramientas de trabajo

Panel de herramientas para RF Permite realizar dibujos con dimensiones ingresadas por el usuario

## Pcbnew – Paneles a la derecha

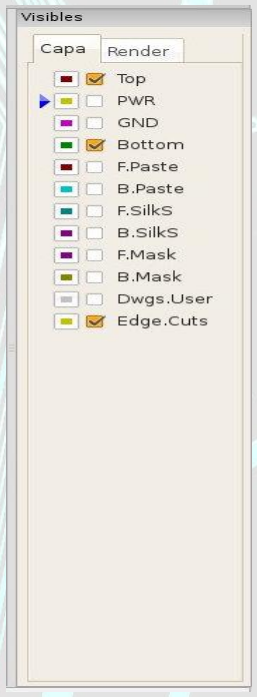
[picture p219: figure]

Control de visualización de capas y otros elementos

Posee dos solapas:

Solapa de visualización de capas (de fabricación)
- Capas de cobre.
- Capas de serigrafía.
- Capas de máscaras.

Solapa de renderizado
- Footprints.
- Pads, vías.
- Textos.
- Valores y referencias.

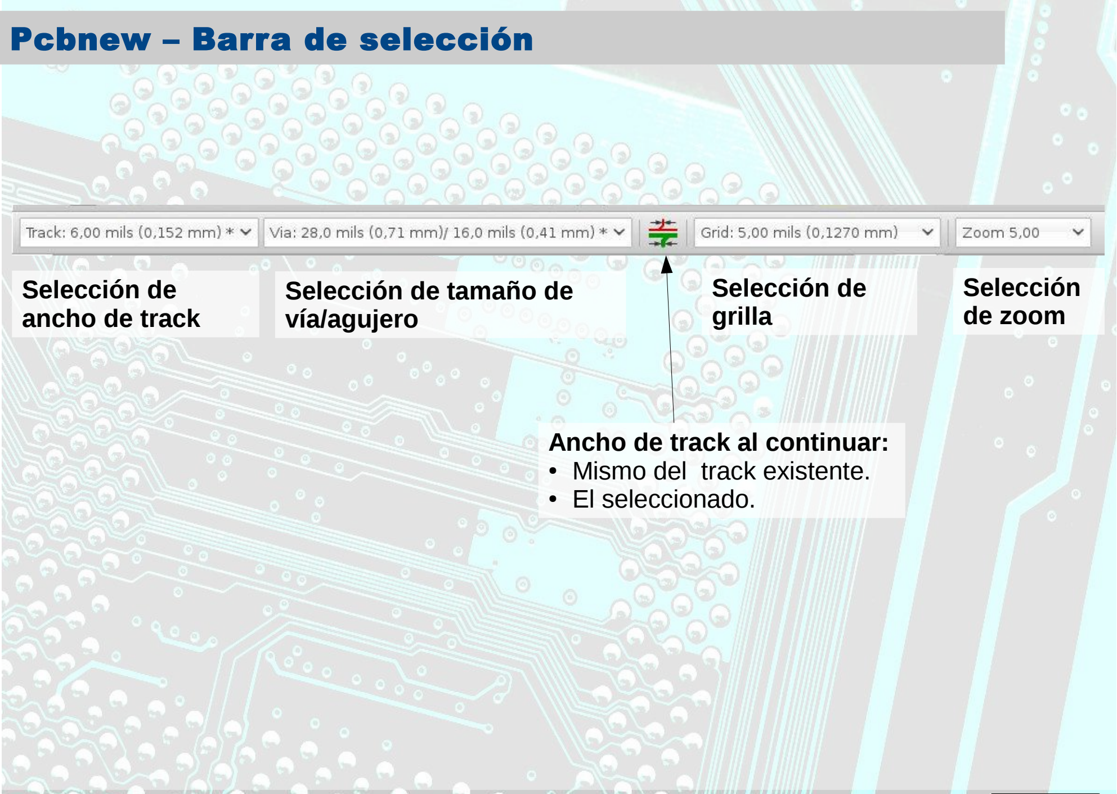
[picture p220: figure]
Selección de tamaño de vía/agujero; Pcbnew – Barra de selección; Selección de zoom; Selección de ancho de track; Selección de grilla; Ancho de track al continuar: ● Mismo del track existente. ● El seleccionado.

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
dició

n

d

el r

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
rimir

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
m in

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
alla

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
tlis

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
## Pcbnew – Barra de sistema

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
k: A

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
ARCHIVO
Fabrication outputs

EDITAR
Cleanup tracks and vias
Swap layers
Tamaños de textos de referencias y valores

VER
Visor 3D
Cambiar a OpenGL

ROUTE
Par diferencial
Tune (track, diff track, etc.)

PREFERENCIAS
Asistente de bibliotecas de footprints Bibliotecas de footprints
Generales, visualización, Hotkeys. Macros

DIMENSIONES
Textos, pads, pads clearance

DESIGN RULES
Reglas de diseño
Configuración de capas

AYUDA
Versión de KiCad

## Pcbnew – Barra de Menú

Muchas de las opciones del menú poseen un ícono que realiza la misma funcionalidad. Se mencionan a continuación algunas opciones solo accesibles mediente el menú:

Barra información de
elementos y de coordenadas.

1)Rótulo.
2)Lectura de Netlist.
3)Manejo de grilla y recomendaciones. 4)Mediciones relativas.
5)Separación de componentes y ubicación.
6)Capas importantes.
7)Ubicación de componentes. 8)Configuración de vías y pistas. 9)Margen global.
10)Dibujar el borde de PCB. 11)Ruteo.
12)Dibujar cotas en mm.
13)Ejecutar el DRC.
14)Acomodar la serigrafía.
15)Mover el diseño dentro de la hoja. 16)Textos en cobre y serigrafía. 17)BOM simple.

## Ejercicio 1: Editor de PCB

El ejercicio consiste en ingresar el siguiente circuito para ir descubriendo y probando las distintas herramientas, siguiendo las instrucciones y el orden de operaciones a continuación.

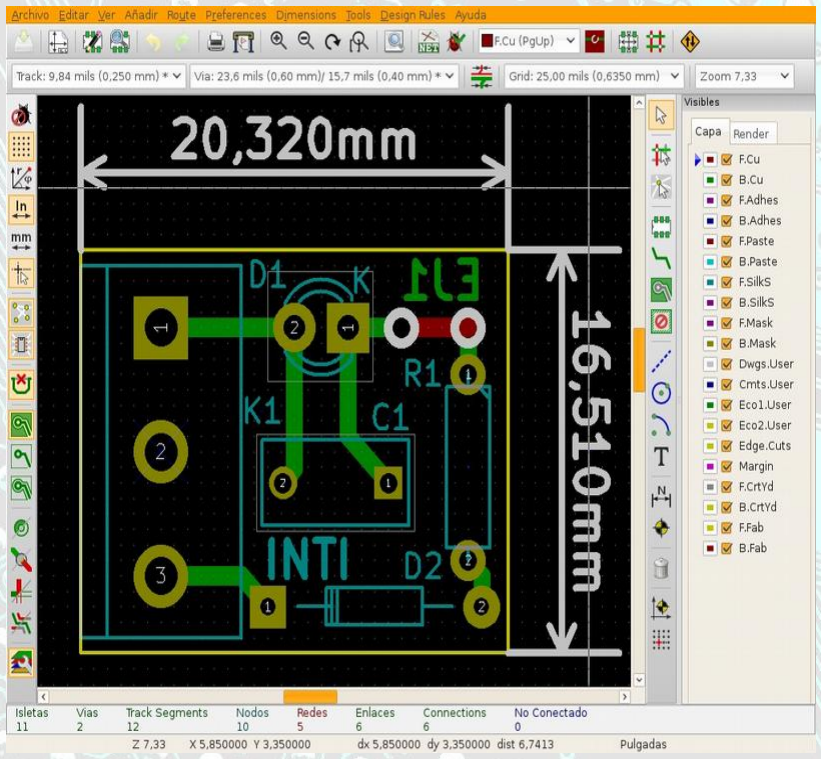
[picture p221: figure]

Algunas pautas:
Grilla de posicionado en 25 mils, pistas de 32 mils, Margen de 32 mils, Vía de 65/32 mils (puente obligatorio).

## Pcbnew - Hotkeys

Tecla | Operación
M | Mover elemento
R | Rotar elemento
E | editar elemento
G | Arrastrar elemento
[End] | Mouse Left Doble Click
[Enter] | Mouse Left Click
[CTRL]-U | Cambiar de unidades (mm y “)
[PgUP] | Seleccionar capa top
[PgDwn] | Seleccionar capa bottom
[bkspc] | Borrar segmento
[CTRL]-Z | Deshacer
[DEL] | Borrar pista o footprint
[CTRL]+S | Guardar esquemático
/ | Cambiar postura de pista

Más teclas en Preferencias->Hotkeys

## Ejercicio 1: Modificaciones

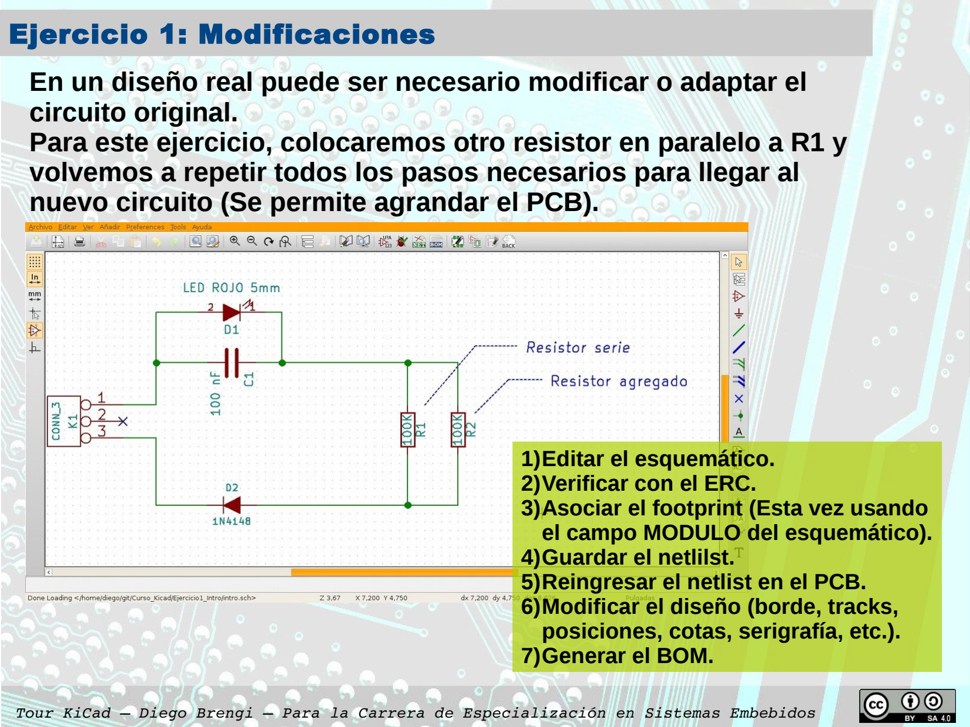
[picture p222: page 41]

### En un diseño real puede ser necesario modificar o adaptar el

circuito original.

### Para este ejercicio, colocaremos otro resistor en paralelo a R1 y volvemos a repetir todos los pasos necesarios para llegar al

nuevo circuito (Se permite agrandar el PCB).

1)Editar el esquemático.
2)Verificar con el ERC.
3)Asociar el footprint (Esta vez usando el campo MODULO del esquemático). 4)Guardar el netlilst.
5)Reingresar el netlist en el PCB. 6)Modificar el diseño (borde, tracks, posiciones, cotas, serigrafía, etc.). 7)Generar el BOM.

## Ejercicio 1: Modificaciones

Circuito final

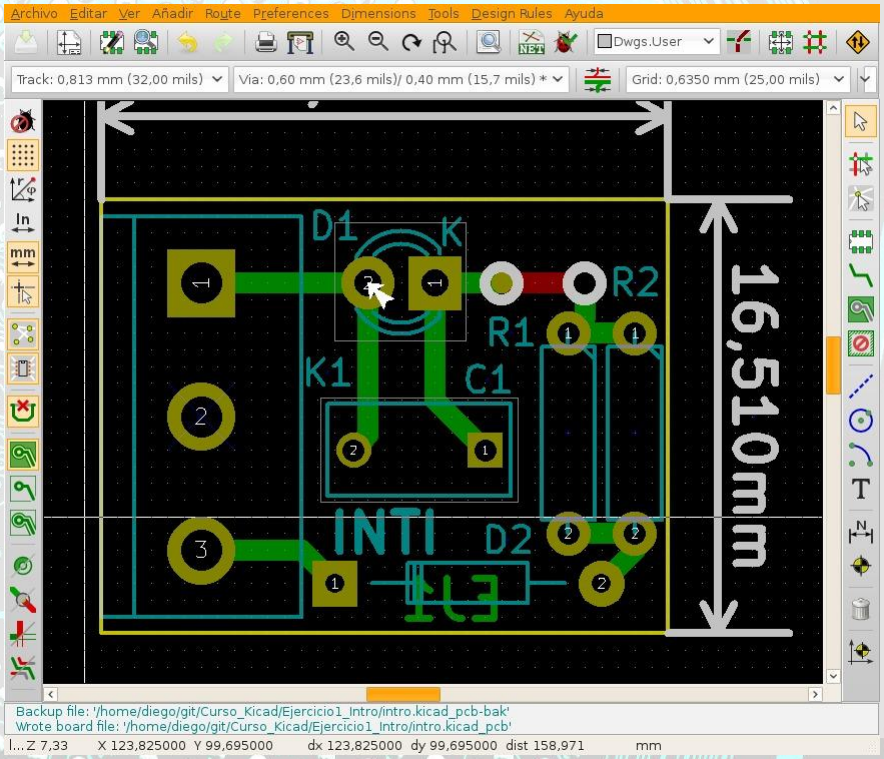
[picture p223: figure]

# Visor de archivos Gerber (GerbView)

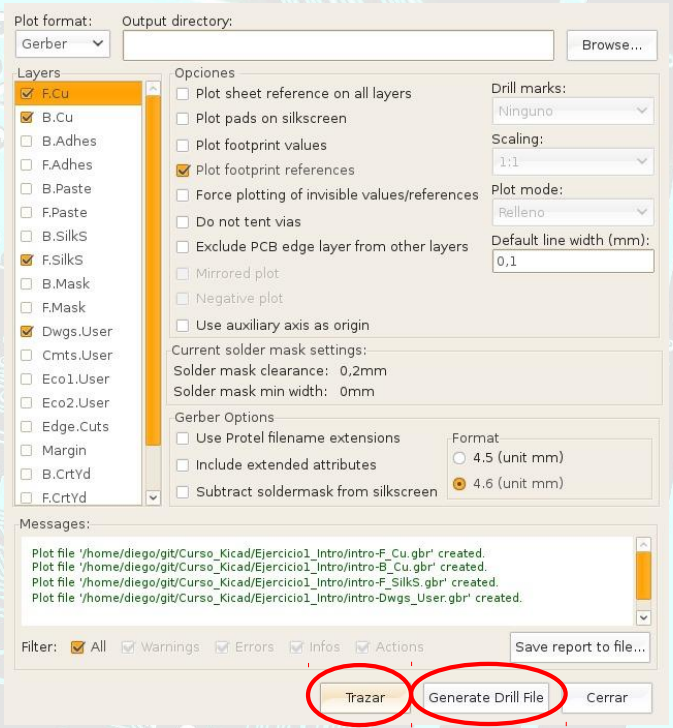
[picture p224: figure]

Para enviar a fabricar un circuito es necesario enviarle al
fabricante los archivos Gerber y el archivo de taladrado.
La generación se hace desde el Pcbnew.

## Ejercicio 1: Generación de archivos Gerber

Para este ejercicio se generaron los siguientes archivos:

## - PROY-B_Cu.gbr - PROY-Dwgs_User.gbr - PROY-F_Cu.gbr - PROY-F_SilkS.gbr - PROY.drl

## Ejercicio 1: Generación de archivos Gerber

En el siguiente paso veremos como se utiliza el GerbView para visualizar estos archivos gerber.

Para el proceso de fabricación y ensamblaje se generan
normalmente más archivos
gerber, como por ejemplo
Paste, Adhes, Mask, etc.

## GerbView – Visor de archivos Gerber

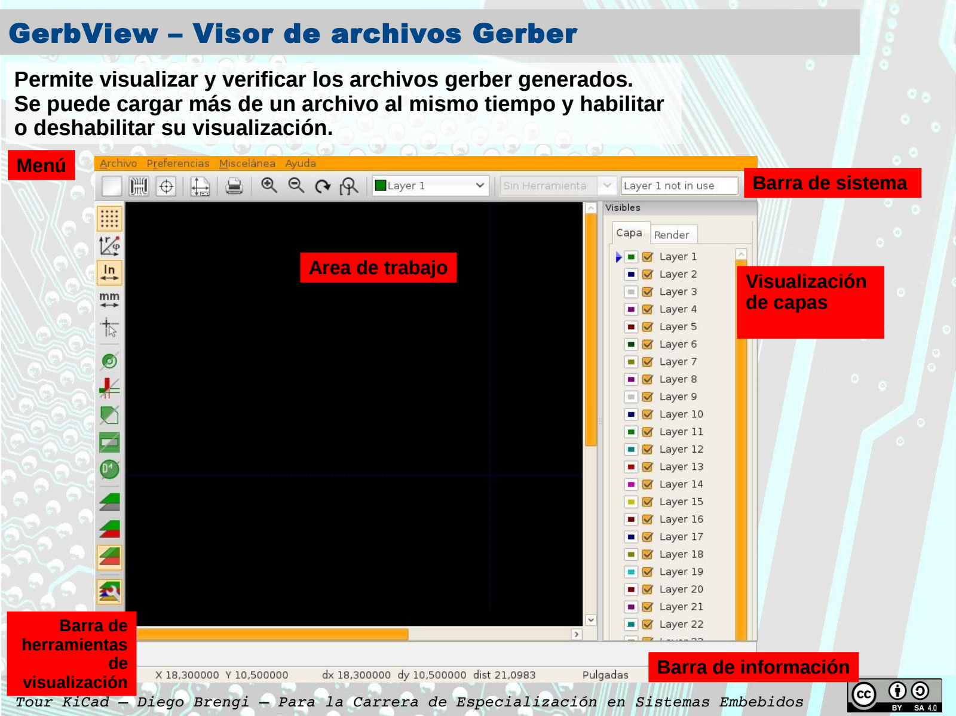
[picture p225: page 46]

Permite visualizar y verificar los archivos gerber generados. Se puede cargar más de un archivo al mismo tiempo y habilitar o deshabilitar su visualización.

Area de trabajo

Barra de
herramientas
de
visualización

Barra de sistema

Menú

Barra de información

Visualización
de capas

Abrir todos los archivos
gerber.

Usar SHIFT o CTRL en
el diálogo de abrir
archivo y seleccionar
todos los gerber.

También se puede
cargar el archivo de
taladrado.

## Ejercicio 1: Visualización de archivos Gerber

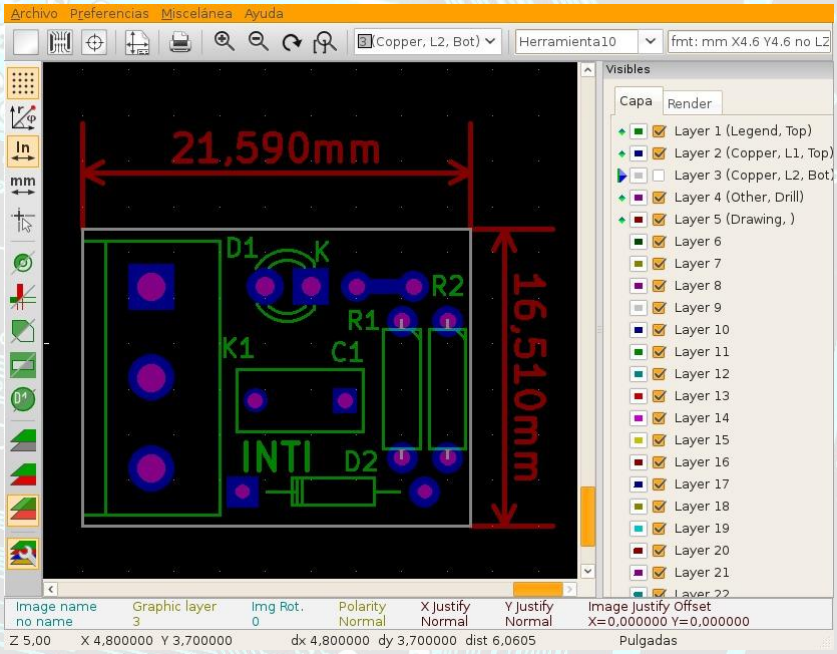
[picture p226: figure]

1)Observar en que consiste cada capa. 2)Investigar las opciones del visor de archivos gerber.

## Ejercicio 1: Vista 3D

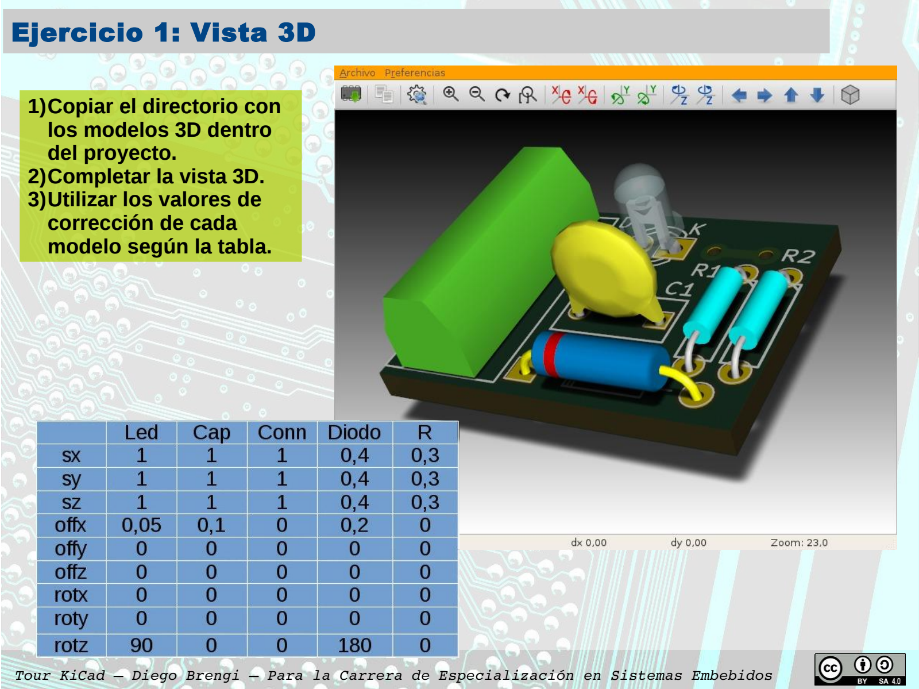
[picture p227: page 48]

1)Copiar el directorio con los modelos 3D dentro
del proyecto.
2)Completar la vista 3D.
3)Utilizar los valores de
corrección de cada
modelo según la tabla.

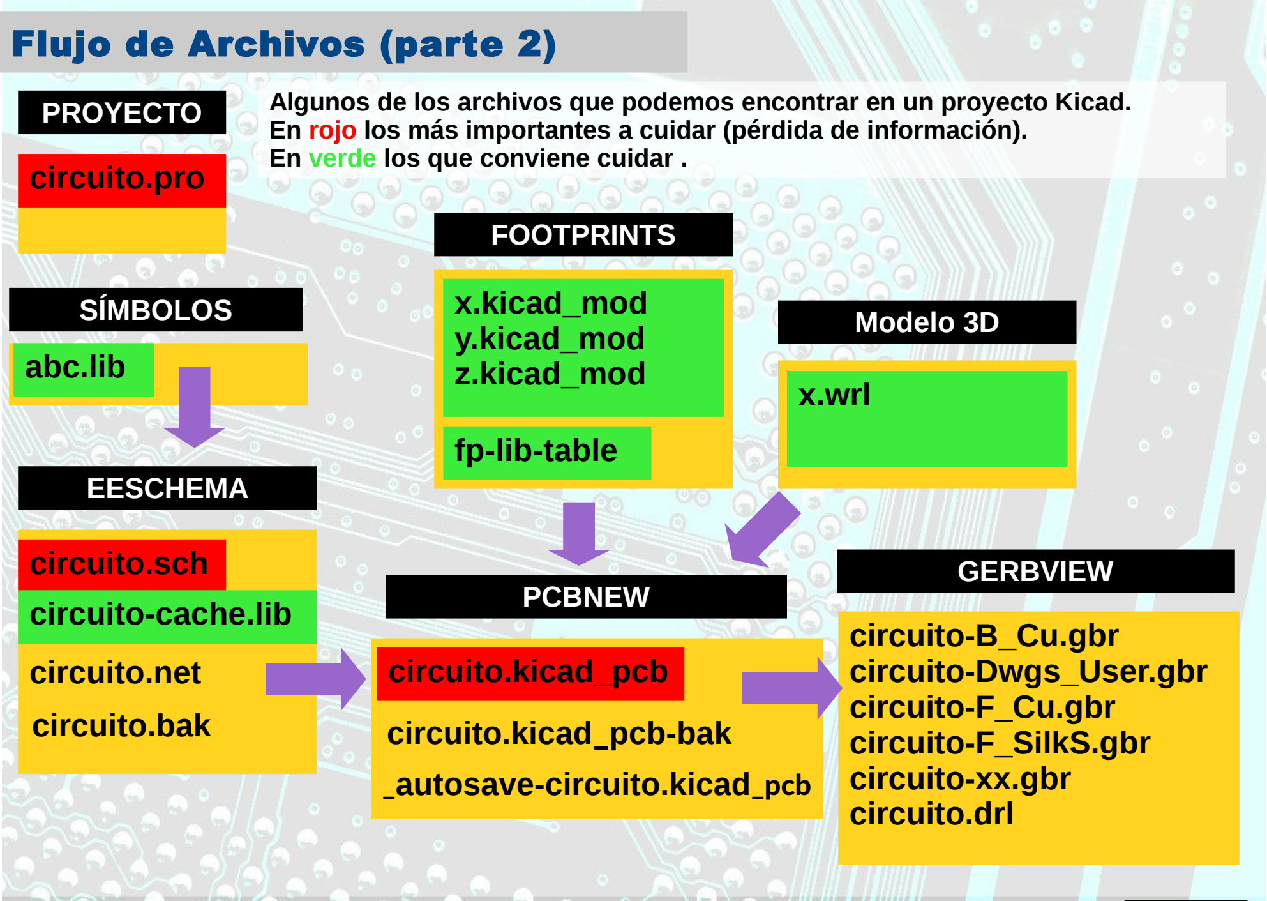
[picture p228: figure]
En verde los que conviene cuidar .; Flujo de Archivos (parte 2); circuito.pro; circuito.sch; circuito.kicad_pcb; circuito-cache.lib; fp-lib-table; circuito.net; PROYECTO; SÍMBOLOS; PCBNEW; FOOTPRINTS; EESCHEMA; circuito.kicad_pcb-bak; abc.lib; x.kicad_mod y.kicad_mod z.kicad_mod; circuito.bak; _autosave-circuito.kicad_pcb; circuito-B_Cu.gbr circuito-Dwgs_User.gbr circuito-F_Cu.gbr circuito-F_SilkS.gbr circuito-xx.gbr circuito.drl; GERBVIEW; x.kicad_mod y.kicad_mod; z.kicad_mod; x.wrl; Modelo 3D

Algunos de los archivos que podemos encontrar en un proyecto Kicad. En rojo los más importantes a cuidar (pérdida de información).

## Contacto e Imágenes de esta presentación

Las imágenes de clipart se tomaron de: https://openclipart.org/

Los demás logos corresponden a proyectos de Software Libre u Open Source.

Carátula principal:
Foto titulada “Circuit” de Yuri Samoilov bajo licencia CC-BY disponible en
https://www.flickr.com/photos/yusamoilov/14011462899/

Fondo de la presentación:
Foto titulada “computer motherboard tracks” de Creativity103 bajo licencia CC-BY disponible en: https://www.flickr.com/photos/creative_stock/5228433146/

El resto de las imágenes se cita la fuente debajo de cada una.

Todas las capturas de pantalla fueron realizadas por los autores y están bajo la misma licencia que esta presentación.

Versión
23/05/16

Autor de esta presentación y contacto:
Diego Brengi - djavier@ieee.org

TOUR KICAD del “Curso de diseño de circuitos impresos”
Preparado para la Carrera de Especialización en Sistemas Embebidos del LSE-FIUBA (CESE)
