brengi/CESE-PCB/2018/Mena/Doc/REQUERIMIENTOS MINIMOS FE 2017.pdf

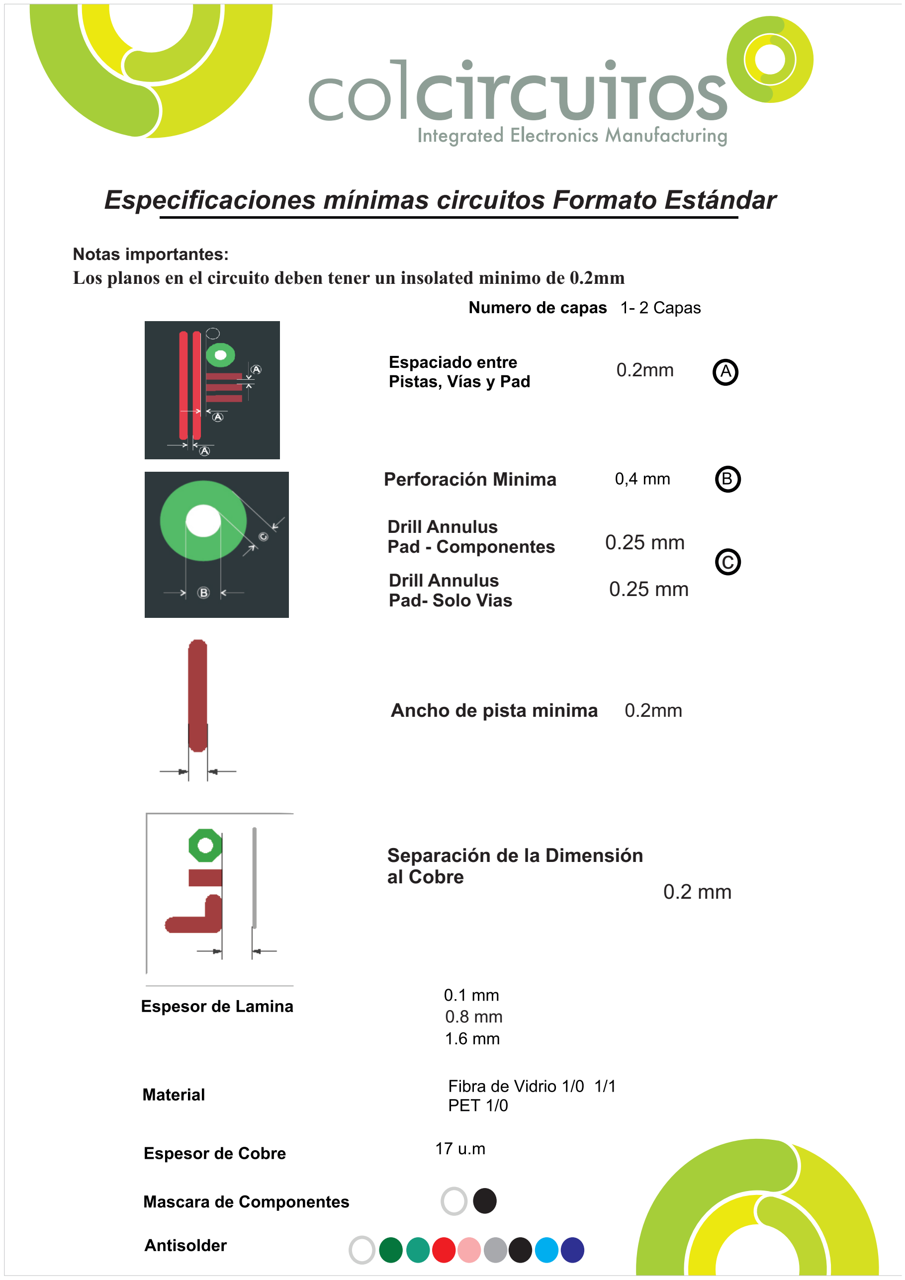
[picture p230: figure]
Drill Annulus Pad - Componentes; Drill Annulus; Pad- Solo Vias; Perforación Minima; Separación de la Dimensión al Cobre; Notas importantes:; Ancho de pista minima

Los planos en el circuito deben tener un insolated minimo de 0.2mm

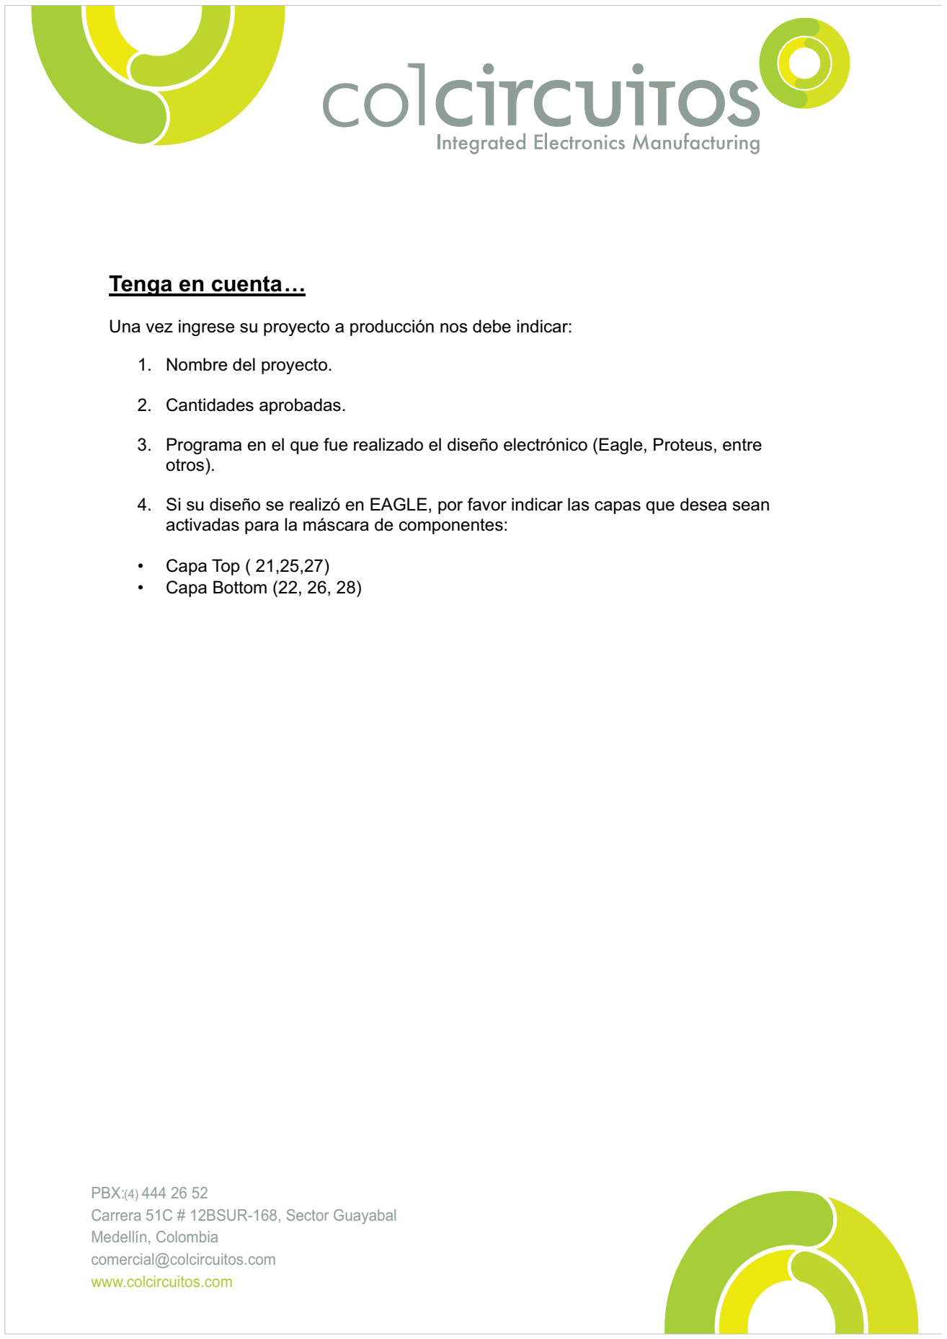
[picture p231: figure]
PBX: (4) 444 26 52; Medellín, Colombia comercial@colcircuitos.com www.colcircuitos.com; Tenga en cuenta…; 1. Nombre del proyecto.; 2. Cantidades aprobadas.; otros).; • Capa Top ( 21,25,27) • Capa Bottom (22, 26, 28)

Carrera 51C # 12BSUR-168, Sector Guayabal

Una vez ingrese su proyecto a producción nos debe indicar:

3. Programa en el que fue realizado el diseño electrónico (Eagle, Proteus, entre
4. Si su diseño se realizó en EAGLE, por favor indicar las capas que desea sean activadas para la máscara de componentes:

## Especificaciones mínimas circuitos Formato Estándar
