brengi/CESE-PCB/2018/Pistarelli/doc/TS12I-072C-R-G15 Drawing.pdf

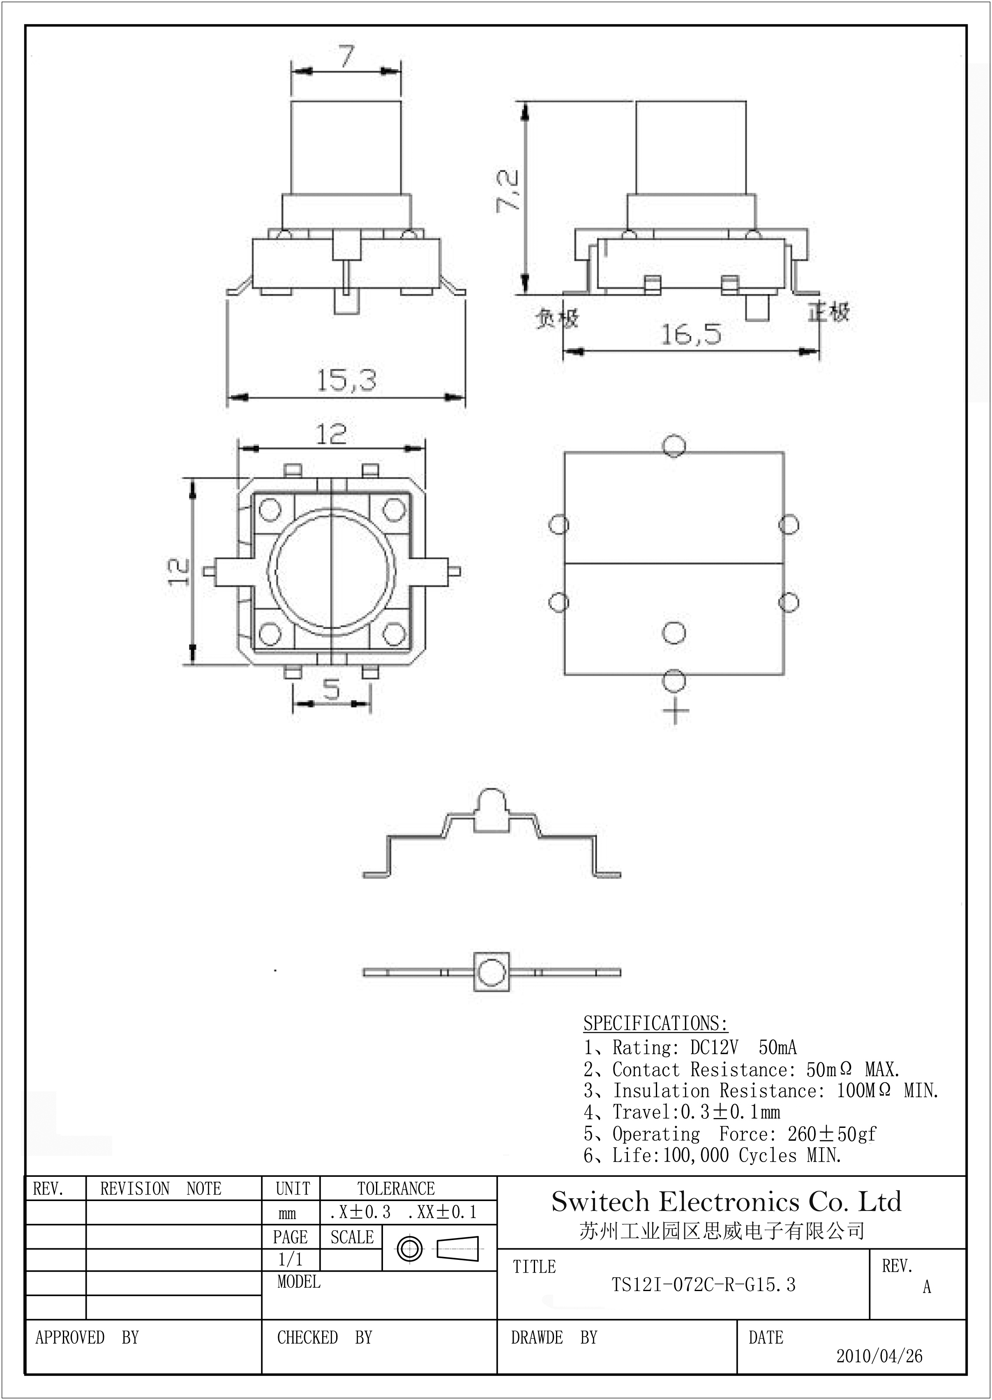
[picture p249: page 1]
