brengi/CESE-PCB/2018/Alvarez/Documentacion/Esquemático-placa-4-reles1.png

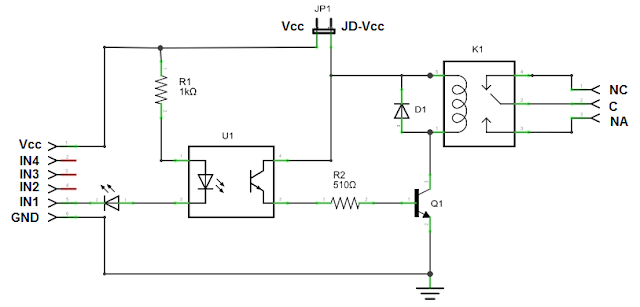
2018/Alvarez/Documentacion/Esquemático-placa-4-reles1.png
