brengi/CESE-PCB/2018/Alvarez/Documentacion/Modulo-4reles-propio-fondo.jpg

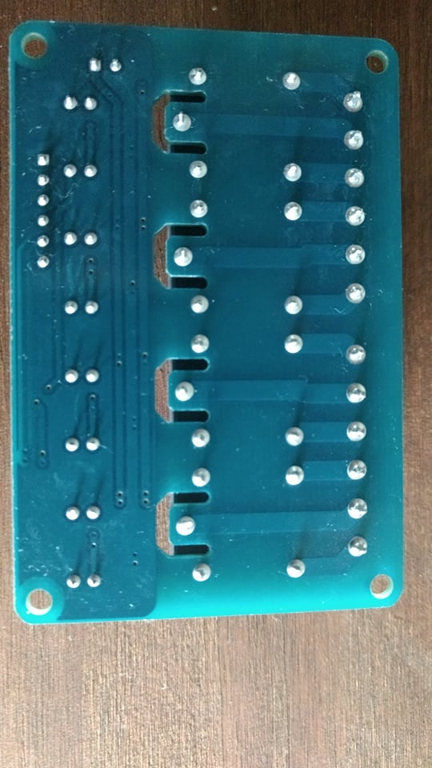
2018/Alvarez/Documentacion/Modulo-4reles-propio-fondo.jpg
