brengi/CESE-PCB/2018/Alvarez/Documentacion/Modulo-4reles-propio-frente.jpg

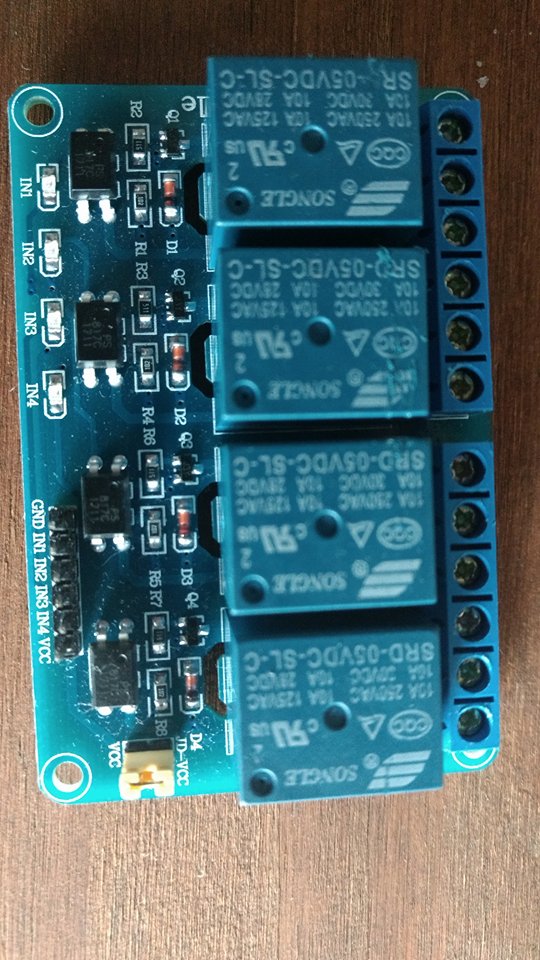
2018/Alvarez/Documentacion/Modulo-4reles-propio-frente.jpg
