brengi/CESE-PCB/2018/Alvarez/Documentacion/modulo-8-reles-back.jpg

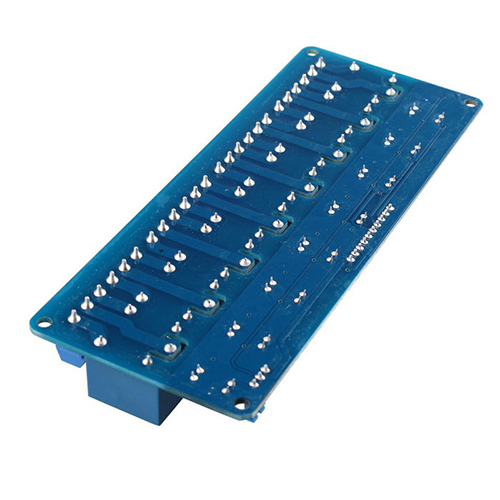
2018/Alvarez/Documentacion/modulo-8-reles-back.jpg
