brengi/CESE-PCB/2018/Alvarez/Documentacion/modulo-8-reles-esquematico.jpg

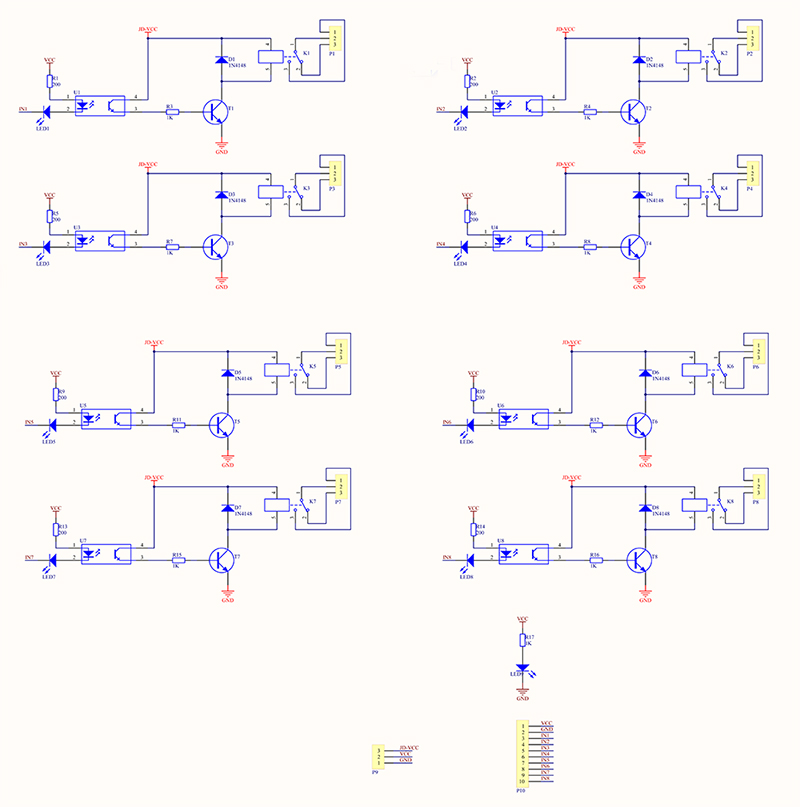
2018/Alvarez/Documentacion/modulo-8-reles-esquematico.jpg
