brengi/CESE-PCB/2018/Alvarez/Documentacion/modulo-8-reles-frente.jpg

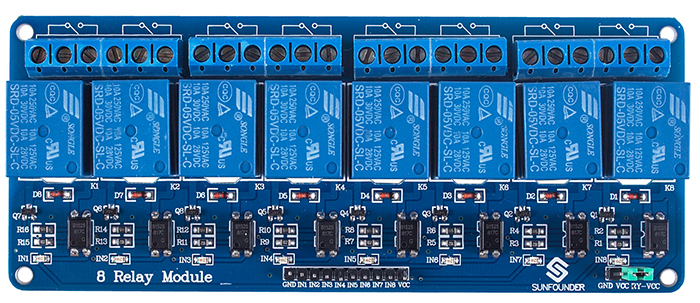
2018/Alvarez/Documentacion/modulo-8-reles-frente.jpg
