brengi/CESE-PCB/2018/Alvarez/Documentacion/modulo-reles-optoacoplados-5v-bornera-arduino-10a-nubbeo.jpg

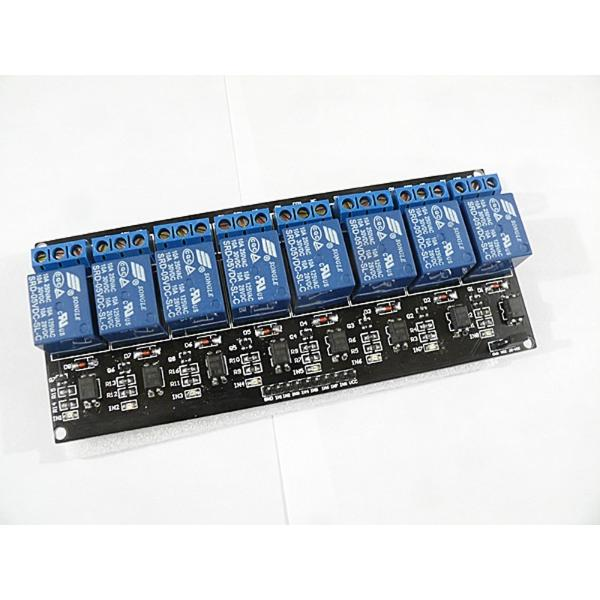
2018/Alvarez/Documentacion/modulo-reles-optoacoplados-5v-bornera-arduino-10a-nubbeo.jpg
