brengi/CESE-PCB/2018/Chavez/mma7361.jpg

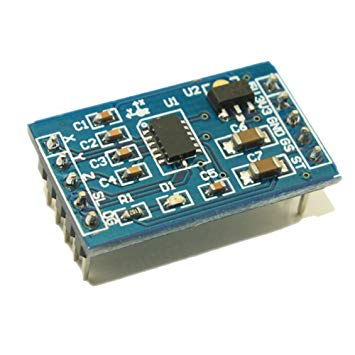
2018/Chavez/mma7361.jpg
