brengi/CESE-PCB/2018/Chavez/MMA7361/Documentacion/F9MHNKGHUQIFY4S.LARGE_.jpg

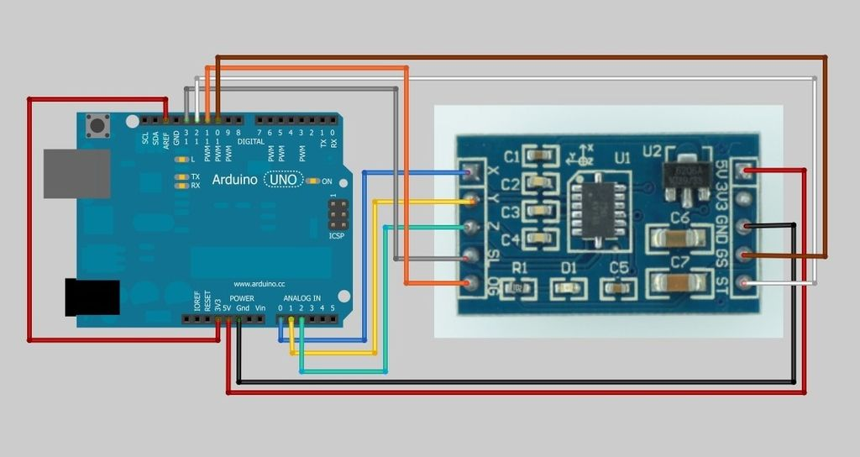
2018/Chavez/MMA7361/Documentacion/F9MHNKGHUQIFY4S.LARGE_.jpg
