brengi/CESE-PCB/2018/Chavez/MMA7361/Vistas3D/Module.jpg

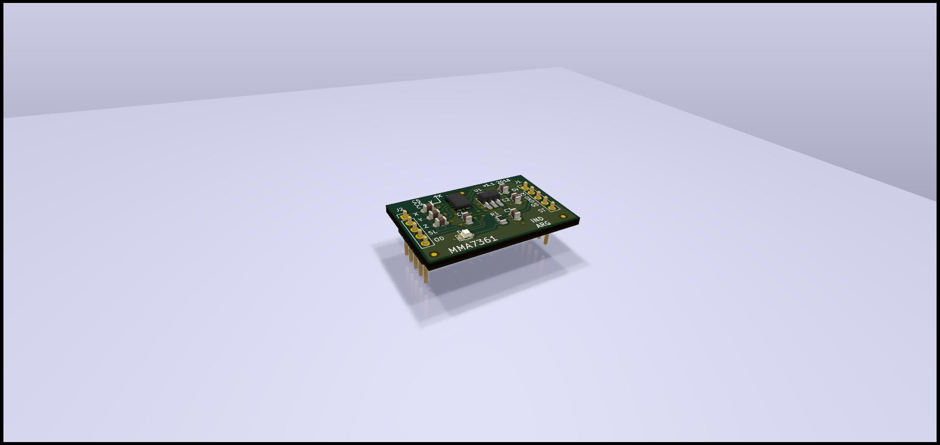
2018/Chavez/MMA7361/Vistas3D/Module.jpg
