brengi/CESE-PCB/2018/Chavez/MMA7361/Vistas3D/Side.jpg

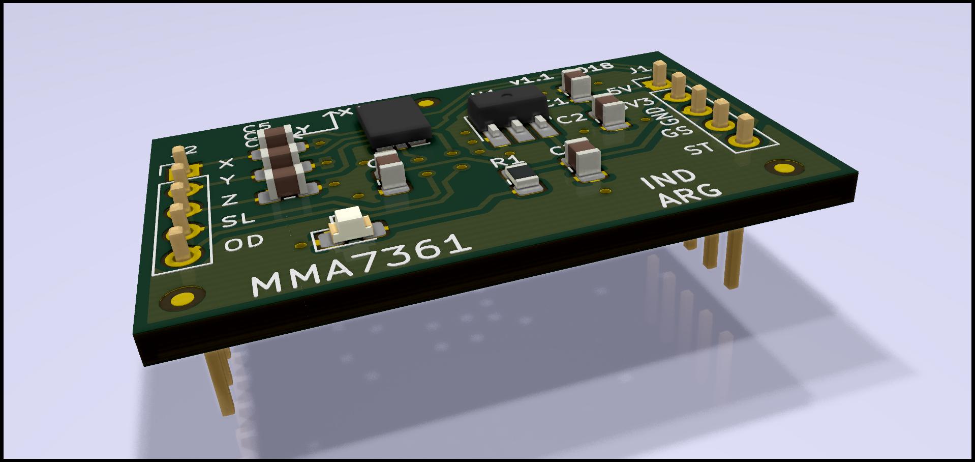
2018/Chavez/MMA7361/Vistas3D/Side.jpg
