brengi/CESE-PCB/2018/Company/Diagrama en bloque del sistema (con leyenda).png

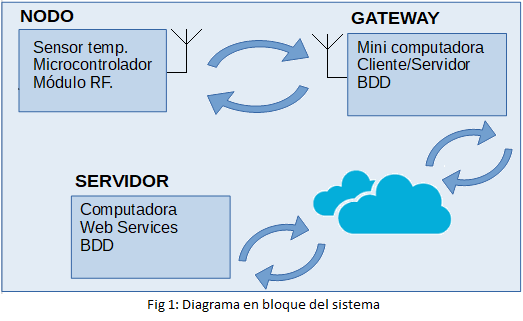
2018/Company/Diagrama en bloque del sistema (con leyenda).png
