brengi/CESE-PCB/2018/Company/Prototipo1.jpg

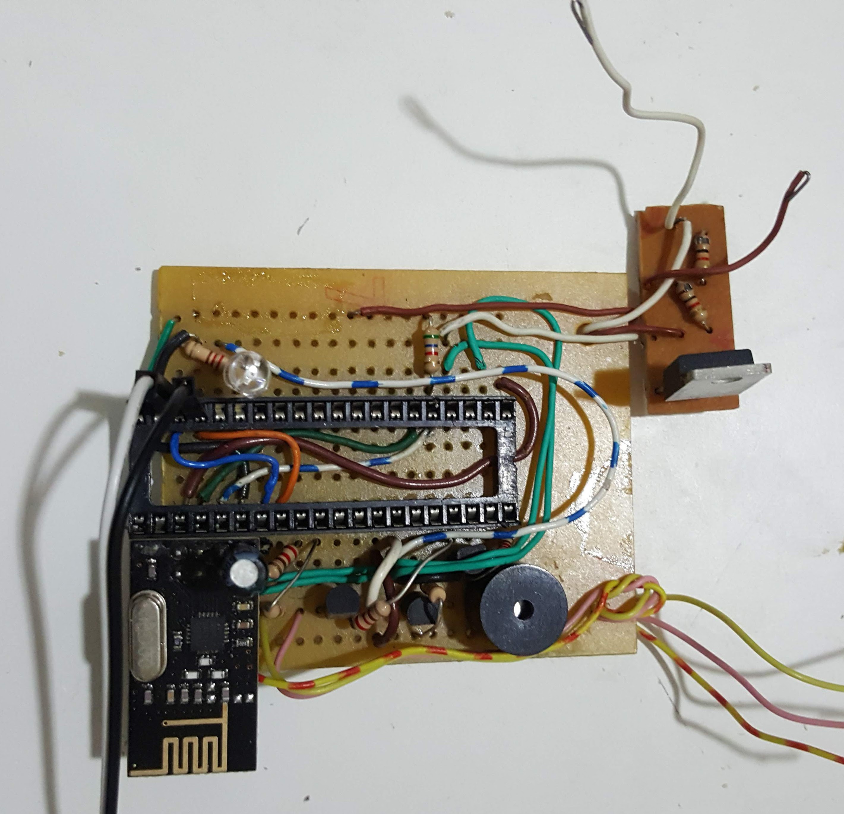
2018/Company/Prototipo1.jpg
