brengi/CESE-PCB/2018/Company/Prototipo2.jpg

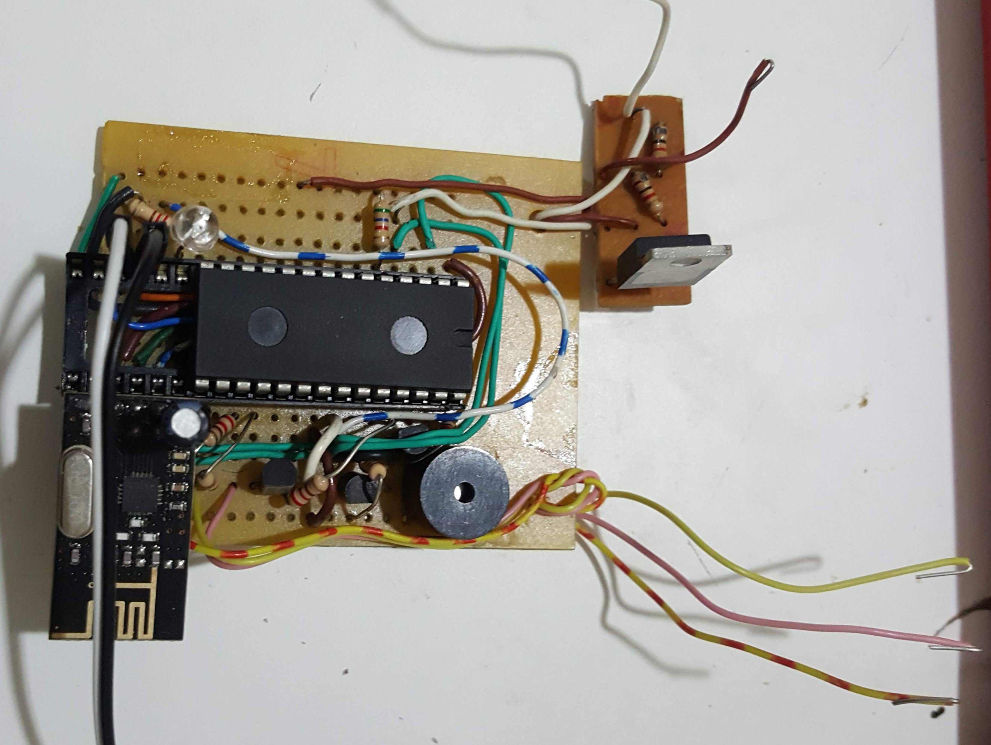
2018/Company/Prototipo2.jpg
