brengi/CESE-PCB/2018/Company/Prototipo3.jpg

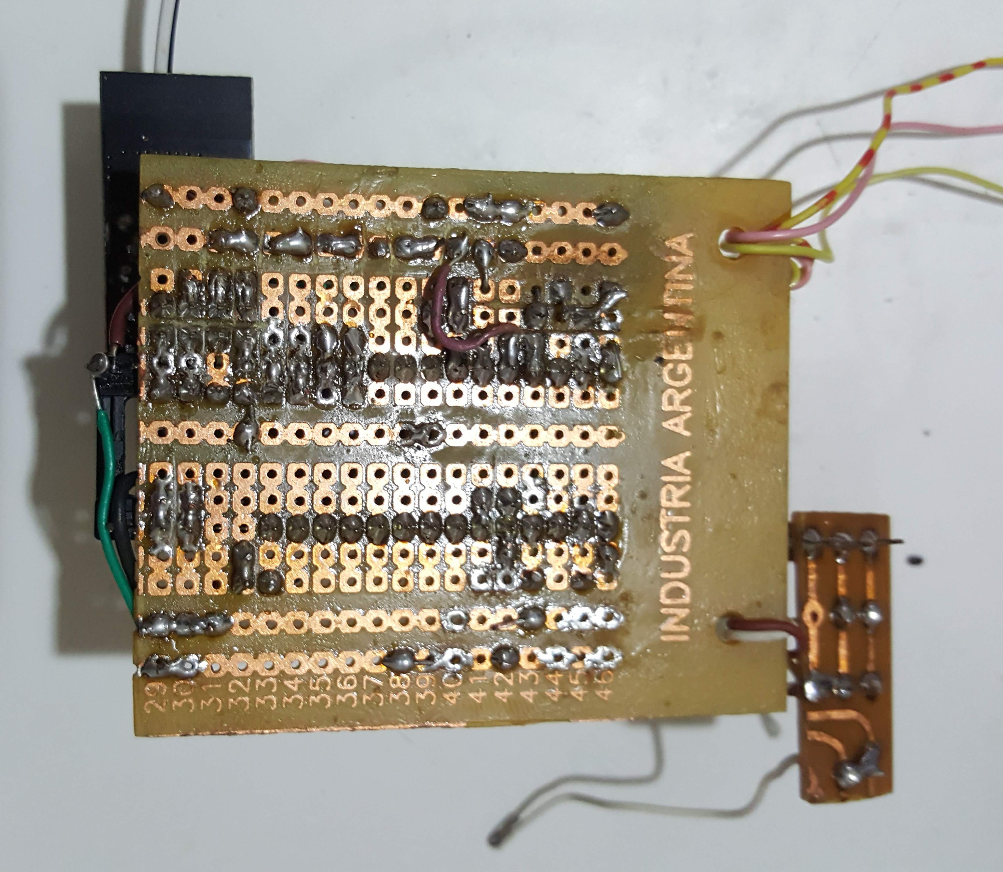
2018/Company/Prototipo3.jpg
