brengi/CESE-PCB/2018/Ericson/img2_r1.0.jpg

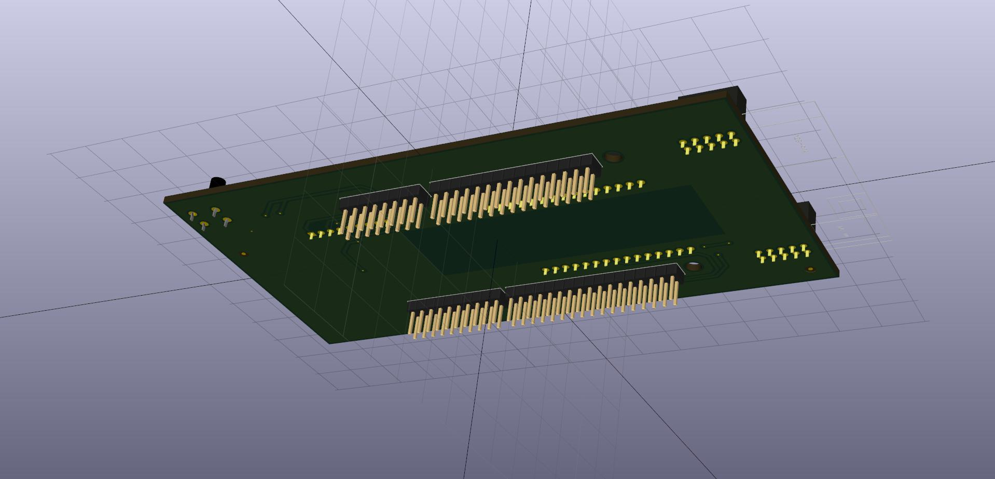
2018/Ericson/img2_r1.0.jpg
