brengi/CESE-PCB/2018/img/Oldani.jpg

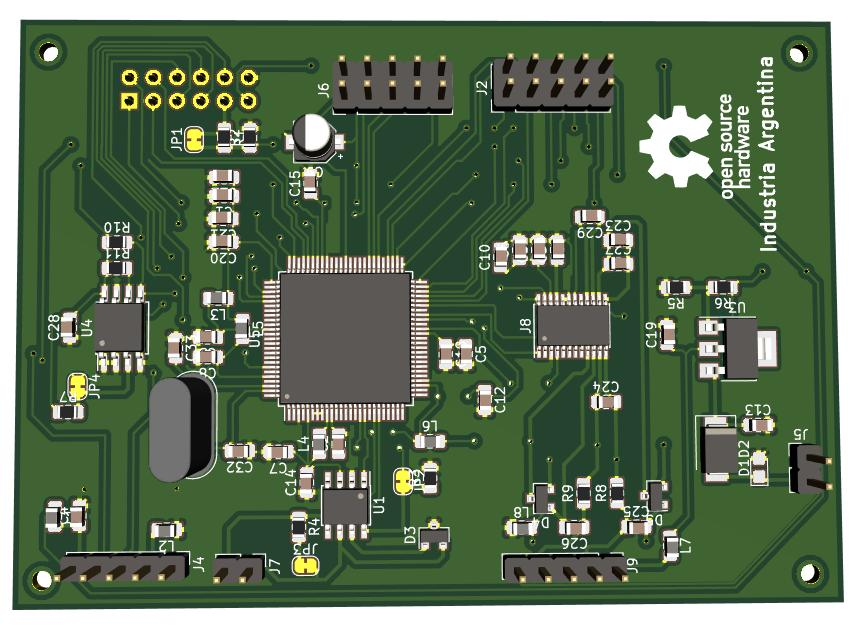
2018/img/Oldani.jpg
