brengi/CESE-PCB/2018/Lavigna/PRACTICA_FINAL/PROJECTO_KICAD/FINAL/PICS/VISTA 3D TOP.png

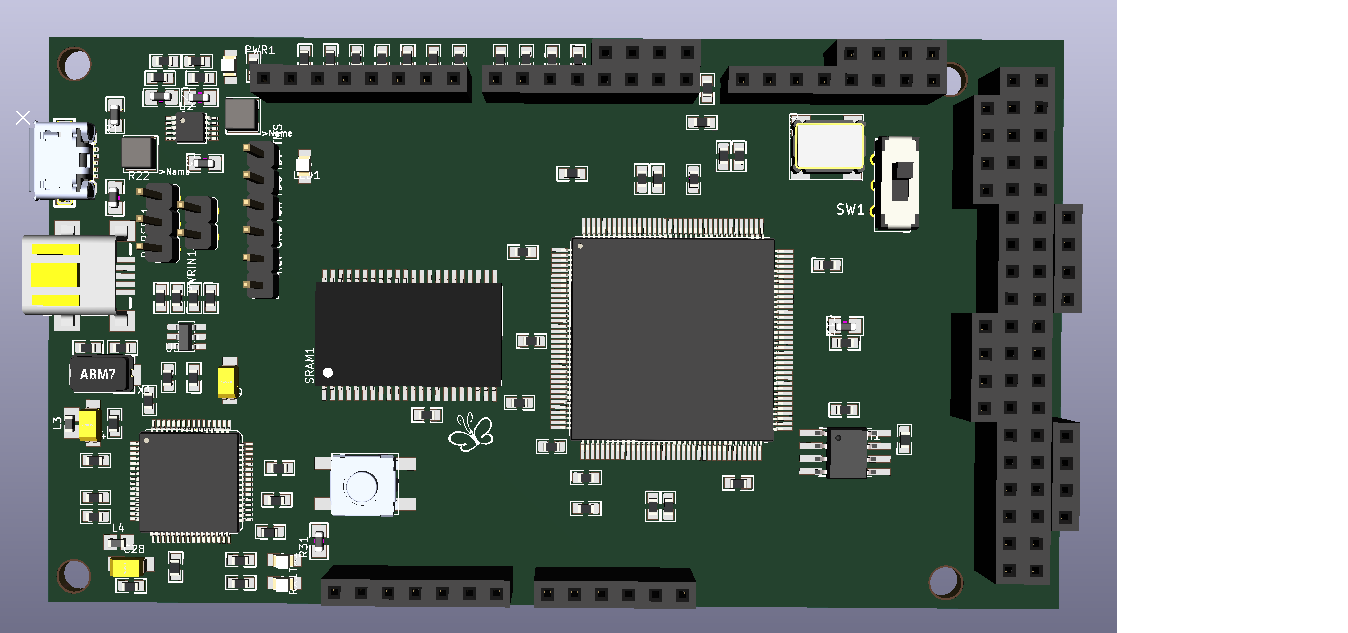
2018/Lavigna/PRACTICA_FINAL/PROJECTO_KICAD/FINAL/PICS/VISTA 3D TOP.png
