brengi/CESE-PCB/2018/Moreyra/TrackerAVL/doc/Display 12864 SPI connection.jpg

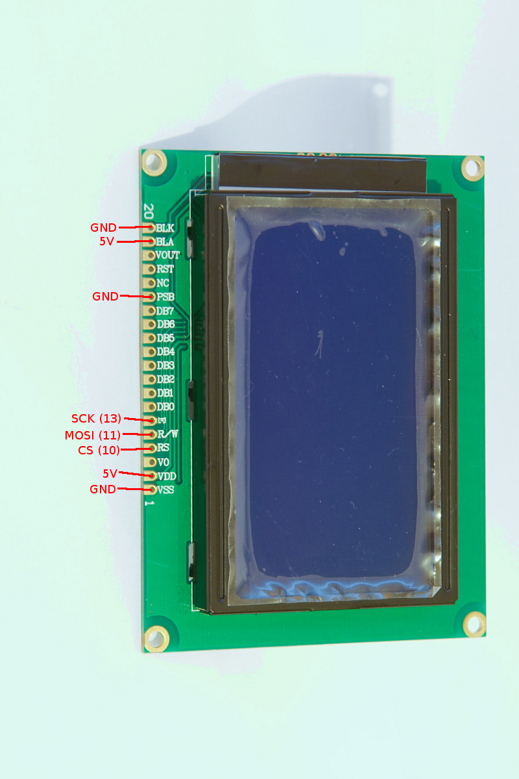
2018/Moreyra/TrackerAVL/doc/Display 12864 SPI connection.jpg
