brengi/CESE-PCB/2018/Moreyra/TrackerAVL/doc/Freewheeling diodes configurations (relay output).png

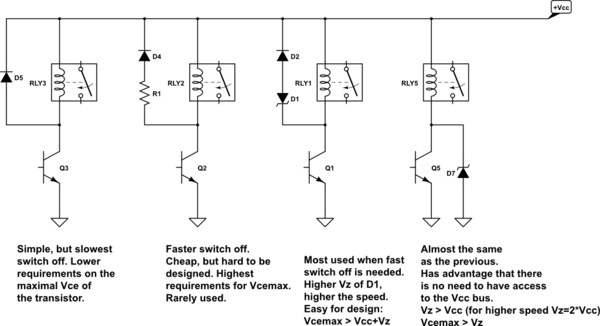
2018/Moreyra/TrackerAVL/doc/Freewheeling diodes configurations (relay output).png
