brengi/CESE-PCB/2018/Oliva/R_OlivaEj2/Ej2_3DView_2bottom.png

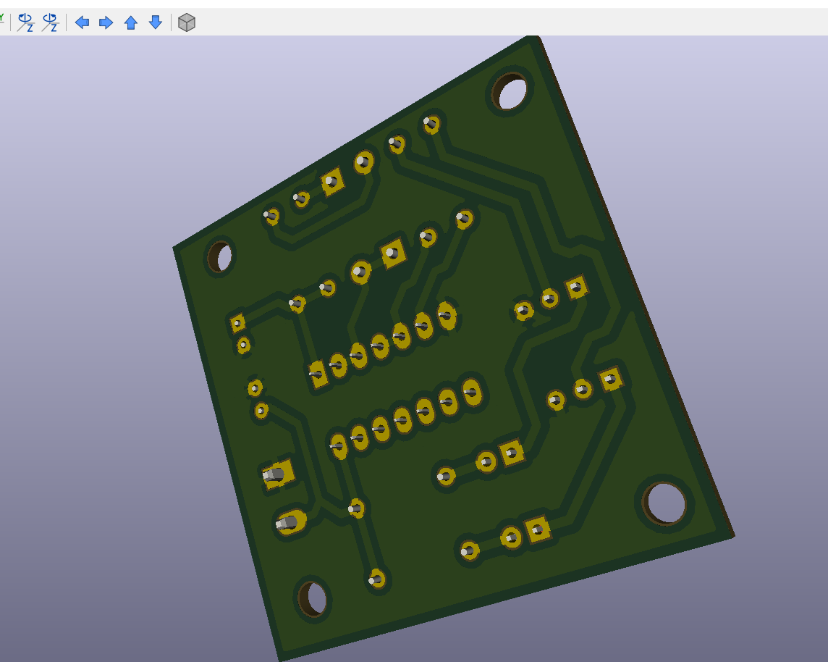
2018/Oliva/R_OlivaEj2/Ej2_3DView_2bottom.png
