brengi/CESE-PCB/2018/Oliva/R_OlivaEj3/eJ3_3D_Vista2_inf 7-10-18.png

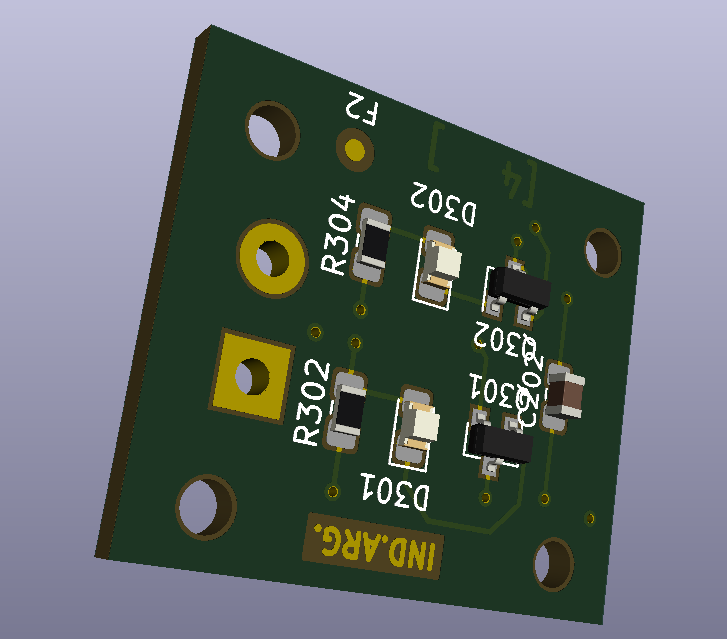
2018/Oliva/R_OlivaEj3/eJ3_3D_Vista2_inf 7-10-18.png
