brengi/CESE-PCB/2018/Oliva/R_OlivaTPFinal/WEMB02_j/3dVersion(1)_02J_08-12-18.jpg

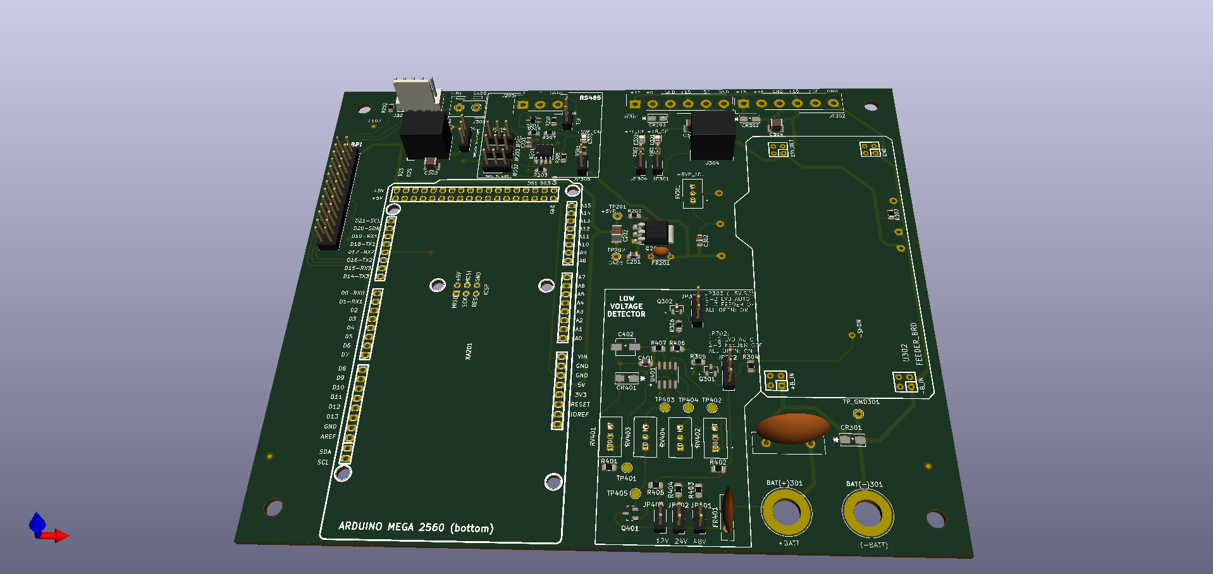
2018/Oliva/R_OlivaTPFinal/WEMB02_j/3dVersion(1)_02J_08-12-18.jpg
