brengi/CESE-PCB/2018/Oliva/R_OlivaTPFinal/WEMB02_j/3dVersion(Reduced)_02e_05-11-18.jpg

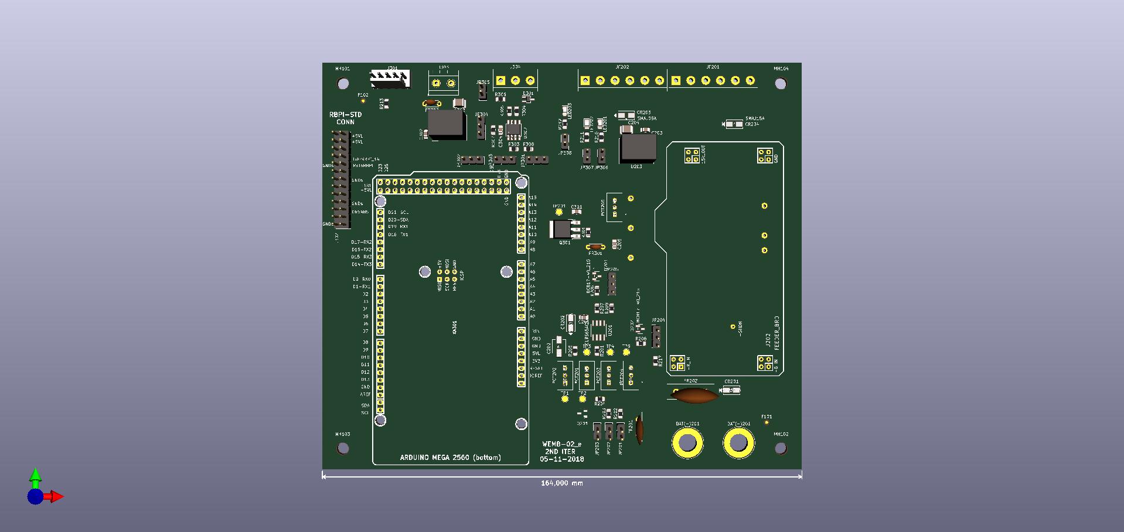
2018/Oliva/R_OlivaTPFinal/WEMB02_j/3dVersion(Reduced)_02e_05-11-18.jpg
