brengi/CESE-PCB/2018/Oliva/R_OlivaTPFinal/WEMB02_j/3dVersion(Routed)_02g_11-11-18.jpg

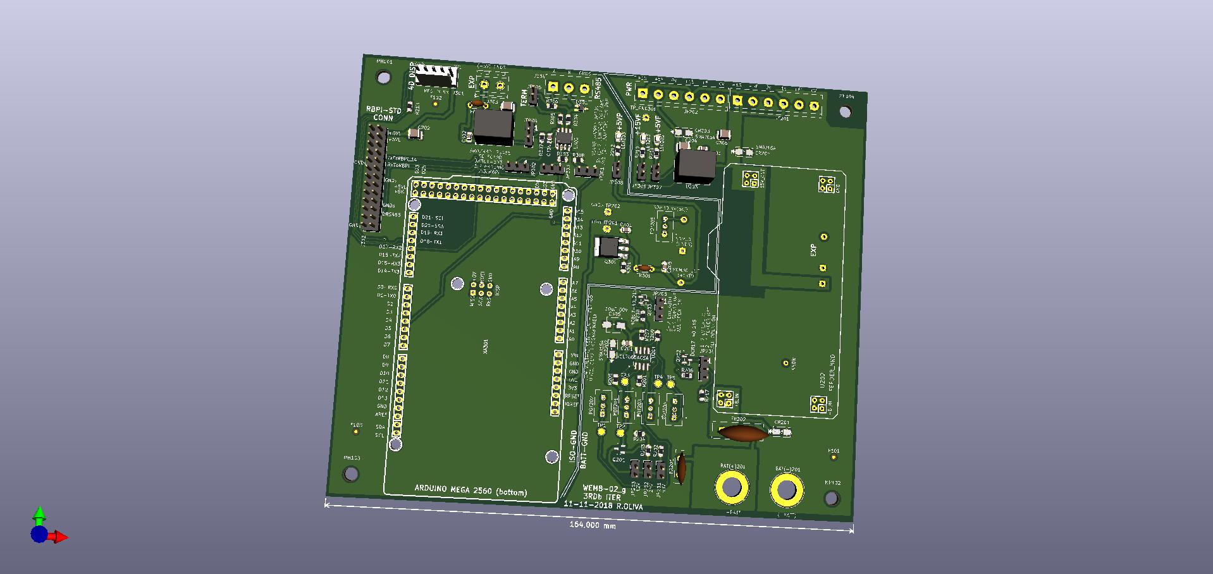
2018/Oliva/R_OlivaTPFinal/WEMB02_j/3dVersion(Routed)_02g_11-11-18.jpg
