brengi/CESE-PCB/2018/Oliva/R_OlivaTPFinal/WEMB02_j/PCB_Layout_versionC.png

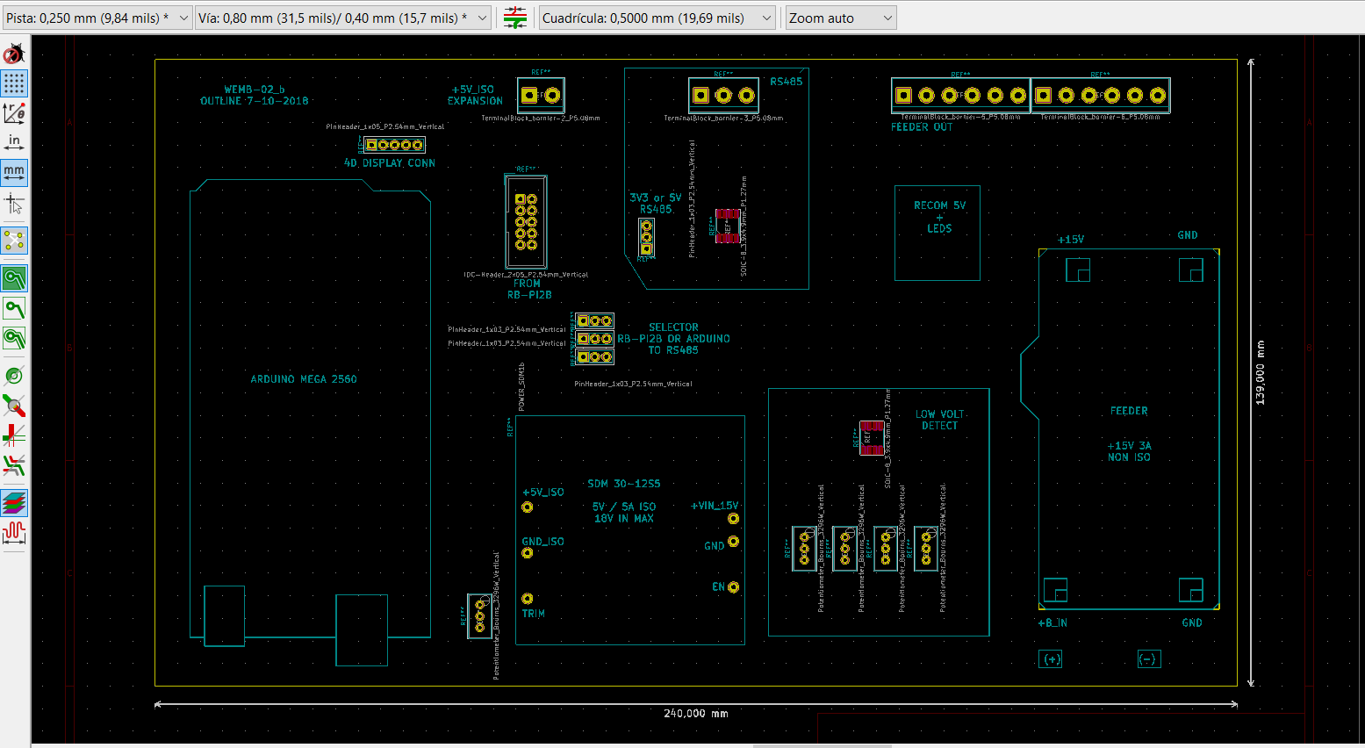
2018/Oliva/R_OlivaTPFinal/WEMB02_j/PCB_Layout_versionC.png
