brengi/CESE-PCB/2018/Oliva/R_OlivaTPFinal/WEMB02_j/ultimas3D_vistas/3dVersion_b02J_14-12-18.jpg

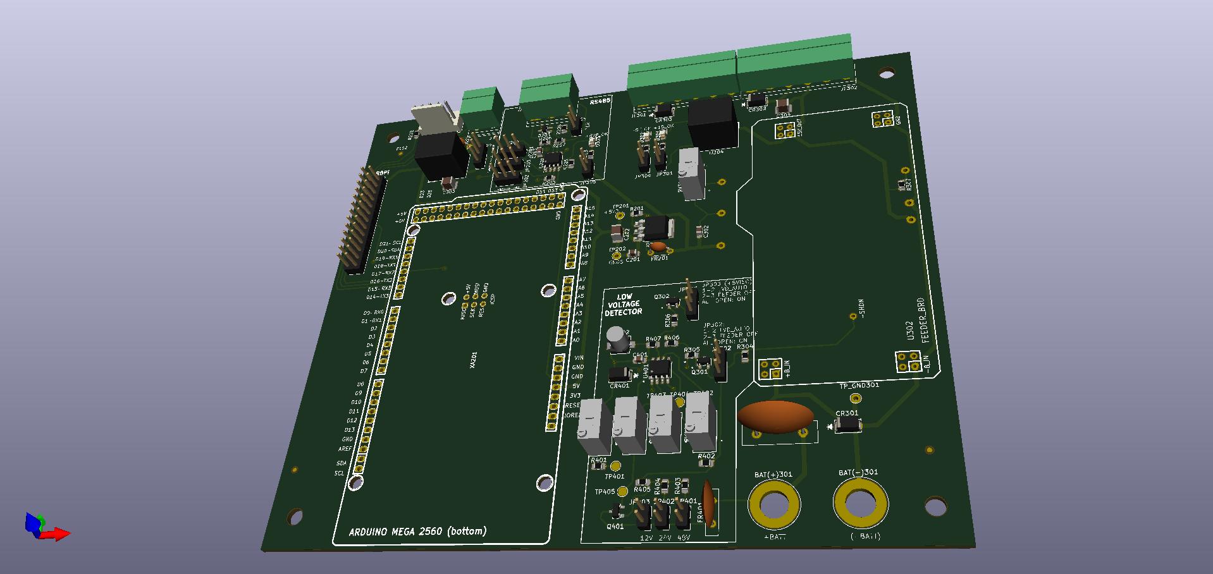
2018/Oliva/R_OlivaTPFinal/WEMB02_j/ultimas3D_vistas/3dVersion_b02J_14-12-18.jpg
