brengi/CESE-PCB/2018/Pojomovsky/datasheets/Simple-H-v1.4-top.jpg

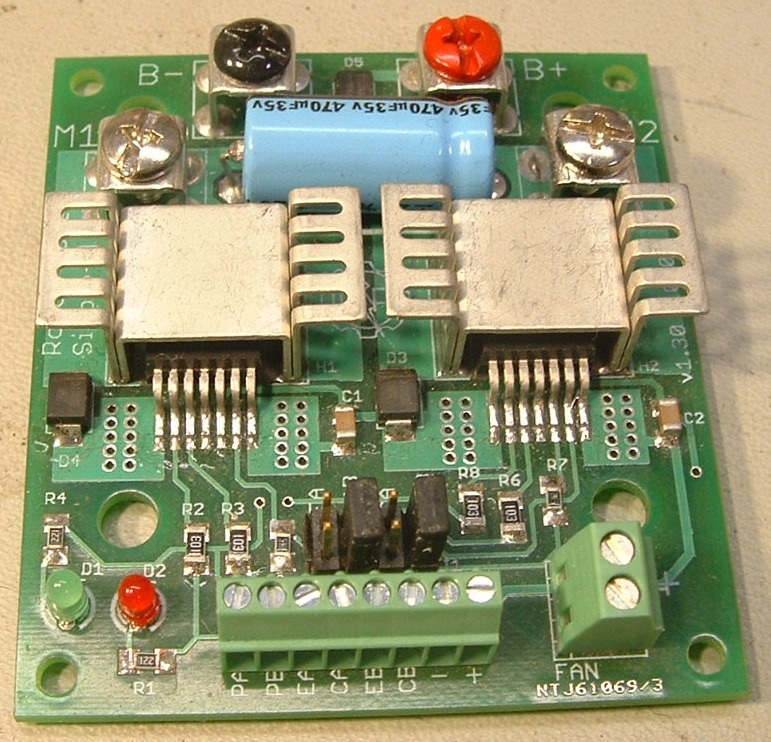
2018/Pojomovsky/datasheets/Simple-H-v1.4-top.jpg
