brengi/CESE-PCB/2018/Salamandri/docs/Imagenes3D/Perspectiva1.png

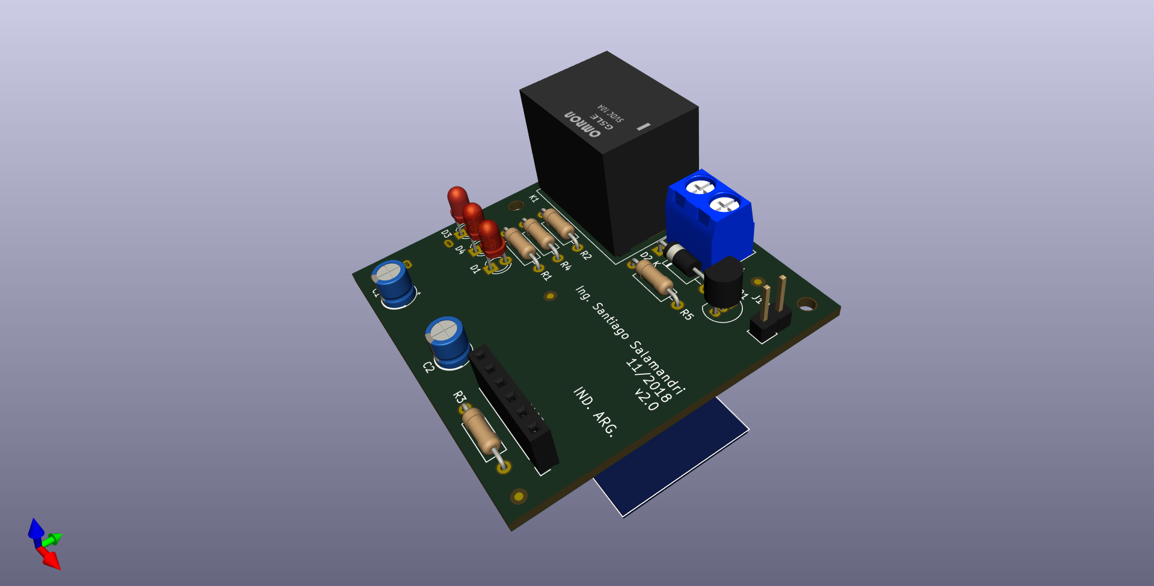
2018/Salamandri/docs/Imagenes3D/Perspectiva1.png
