brengi/CESE-PCB/2018/Salamandri/docs/Imagenes3D/VistaInferior.png

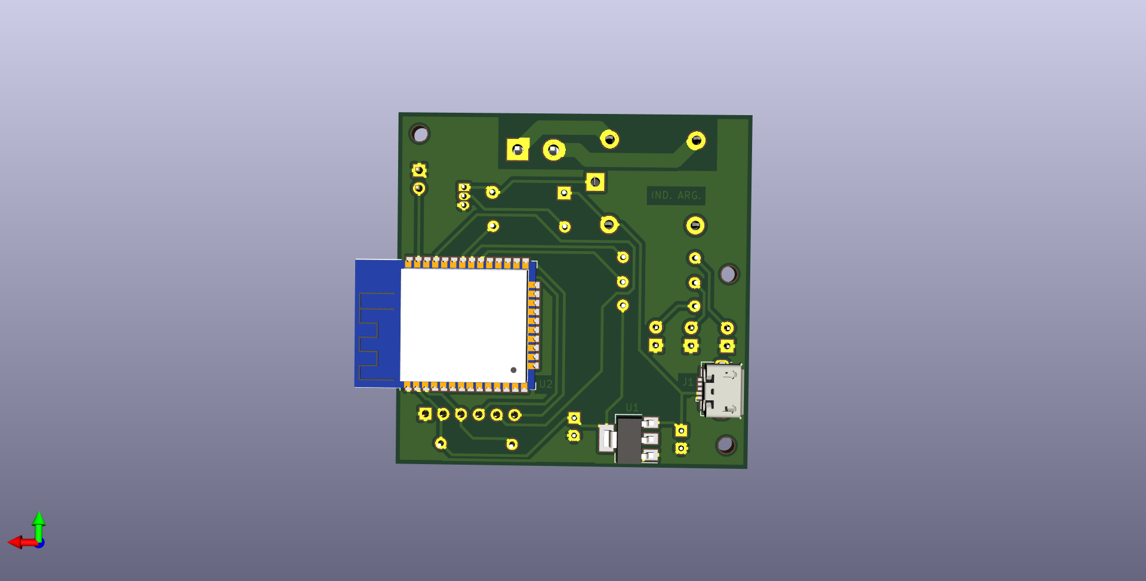
2018/Salamandri/docs/Imagenes3D/VistaInferior.png
