brengi/CESE-PCB/2018/Salamandri/docs/Imagenes3D/VistaSuperior.png

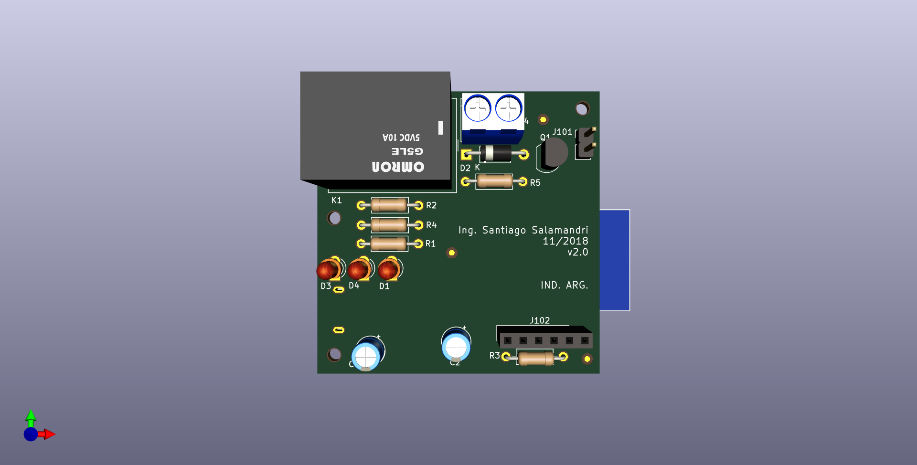
2018/Salamandri/docs/Imagenes3D/VistaSuperior.png
