brengi/CESE-PCB/2018/Slavkin/pics/bottom.png

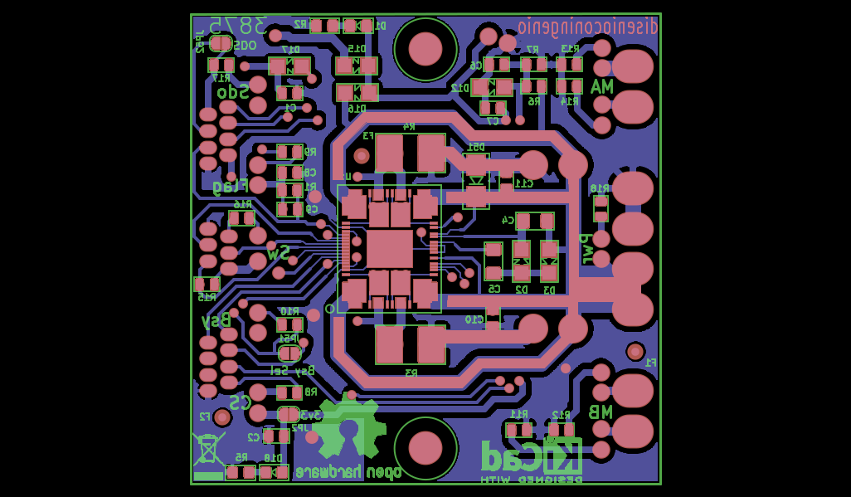
2018/Slavkin/pics/bottom.png
