brengi/CESE-PCB/2018/Slavkin/pics/top.png

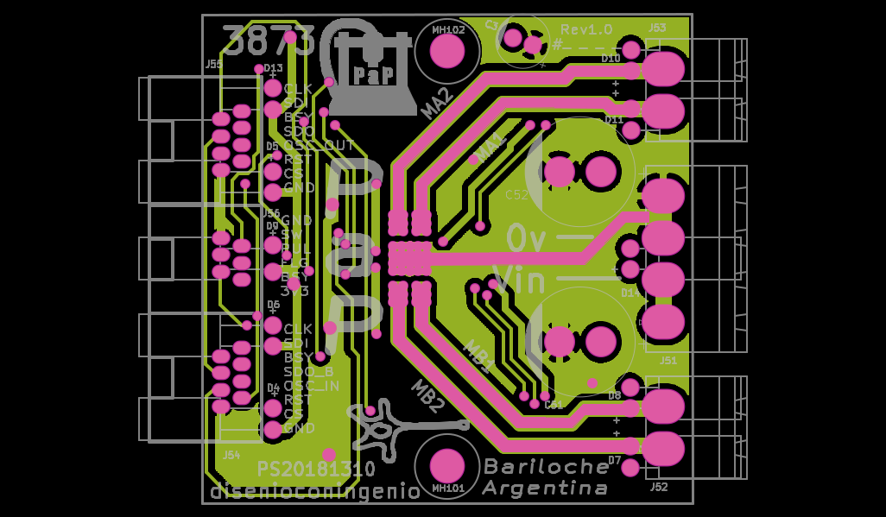
2018/Slavkin/pics/top.png
