brengi/CESE-PCB/2018/Slavkin/pics/v.jpg

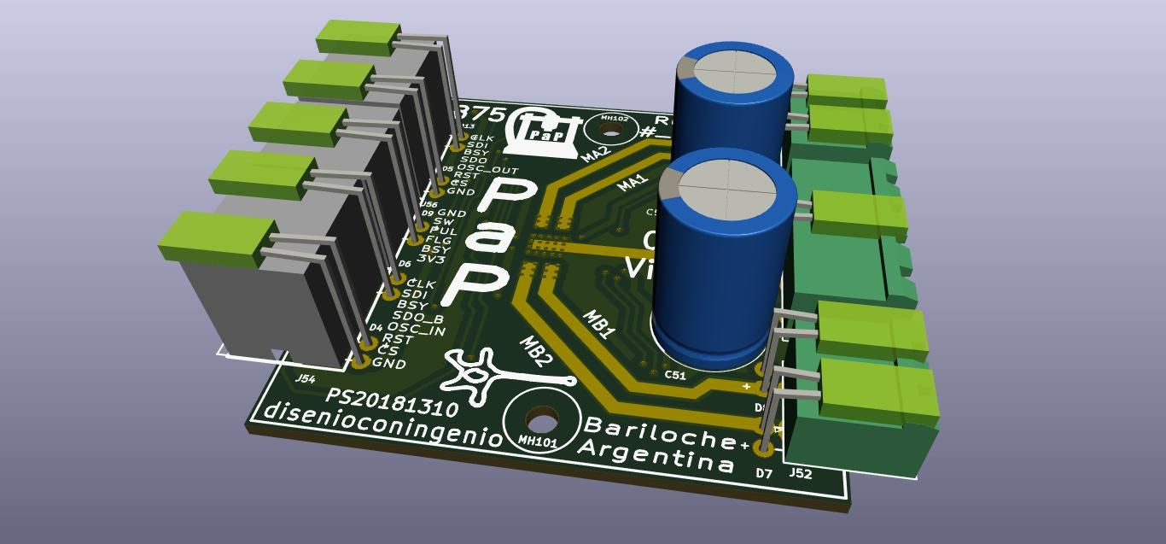
2018/Slavkin/pics/v.jpg
