brengi/CESE-PCB/2018/Yanez/diagramas_referenciales/diagrama_optoacople.jpg

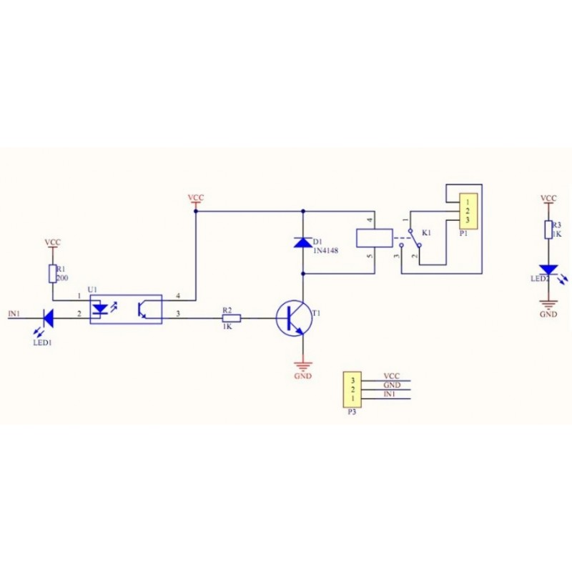
2018/Yanez/diagramas_referenciales/diagrama_optoacople.jpg
