brengi/CESE-PCB/2018/Yanez/diagramas_referenciales/ESP8266_relay_switch.png

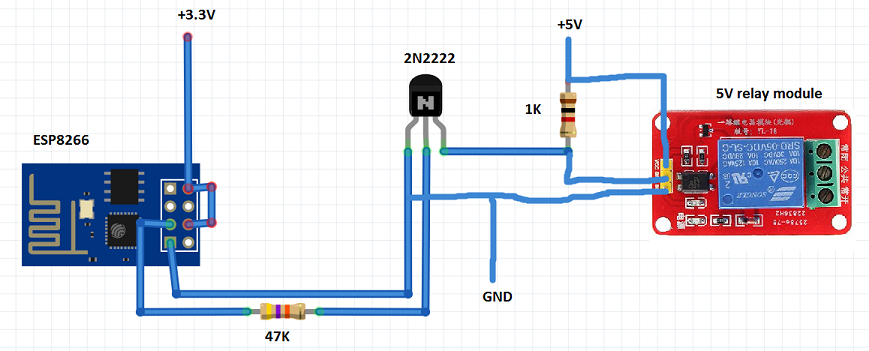
2018/Yanez/diagramas_referenciales/ESP8266_relay_switch.png
