brengi/CESE-PCB/2018/Yanez/diagramas_referenciales/wifi_salida_rele_x1.jpg

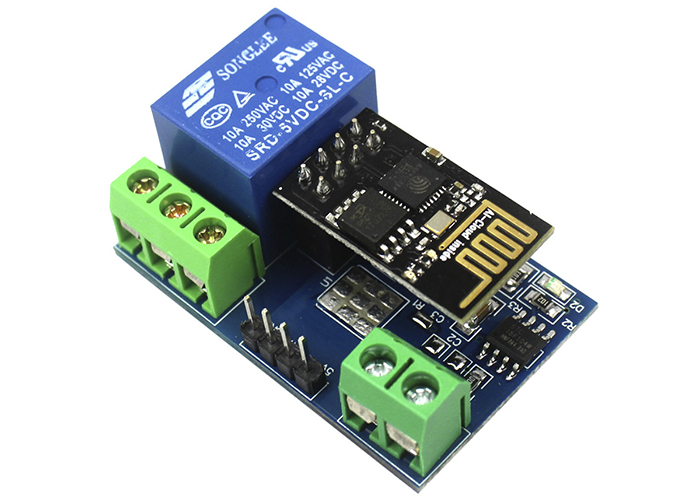
2018/Yanez/diagramas_referenciales/wifi_salida_rele_x1.jpg
