brengi/CESE-PCB/2020/B/MonzonL.png

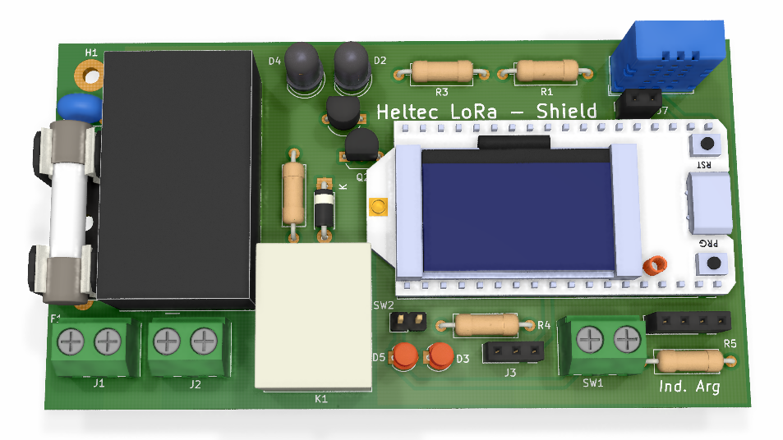
2020/B/MonzonL.png
