brengi/CESE-PCB/AislacionUSB/doc/USB types.png

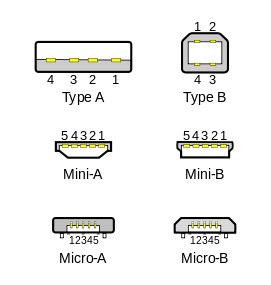
AislacionUSB/doc/USB types.png
