brengi/CESE-PCB/2018/Lavigna/PRACTICA_FINAL/PROJECTO_KICAD/FINAL/3D-MODELS/AVR-USB/10118193-0001LF--3DModel-STEP-56544.STEP

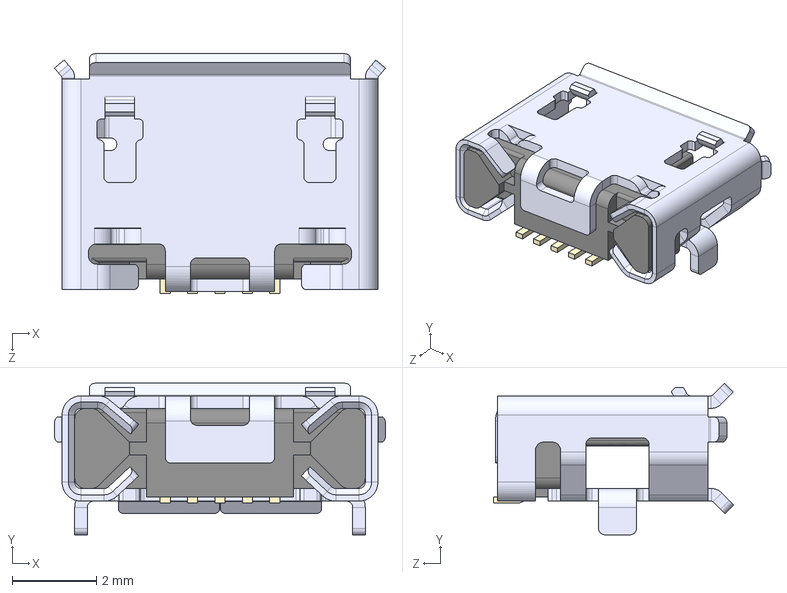
[picture p320: CAD file, 2019-05-17]
2018/Lavigna/PRACTICA_FINAL/PROJECTO_KICAD/FINAL/3D-MODELS/AVR-USB/10118193-0001LF--3DModel-STEP-56544.STEP
7.86 x 3.60 x 5.71 mm
