brengi/CESE-PCB/AislacionUSB/USBCableIsolatorCircuit.pdf

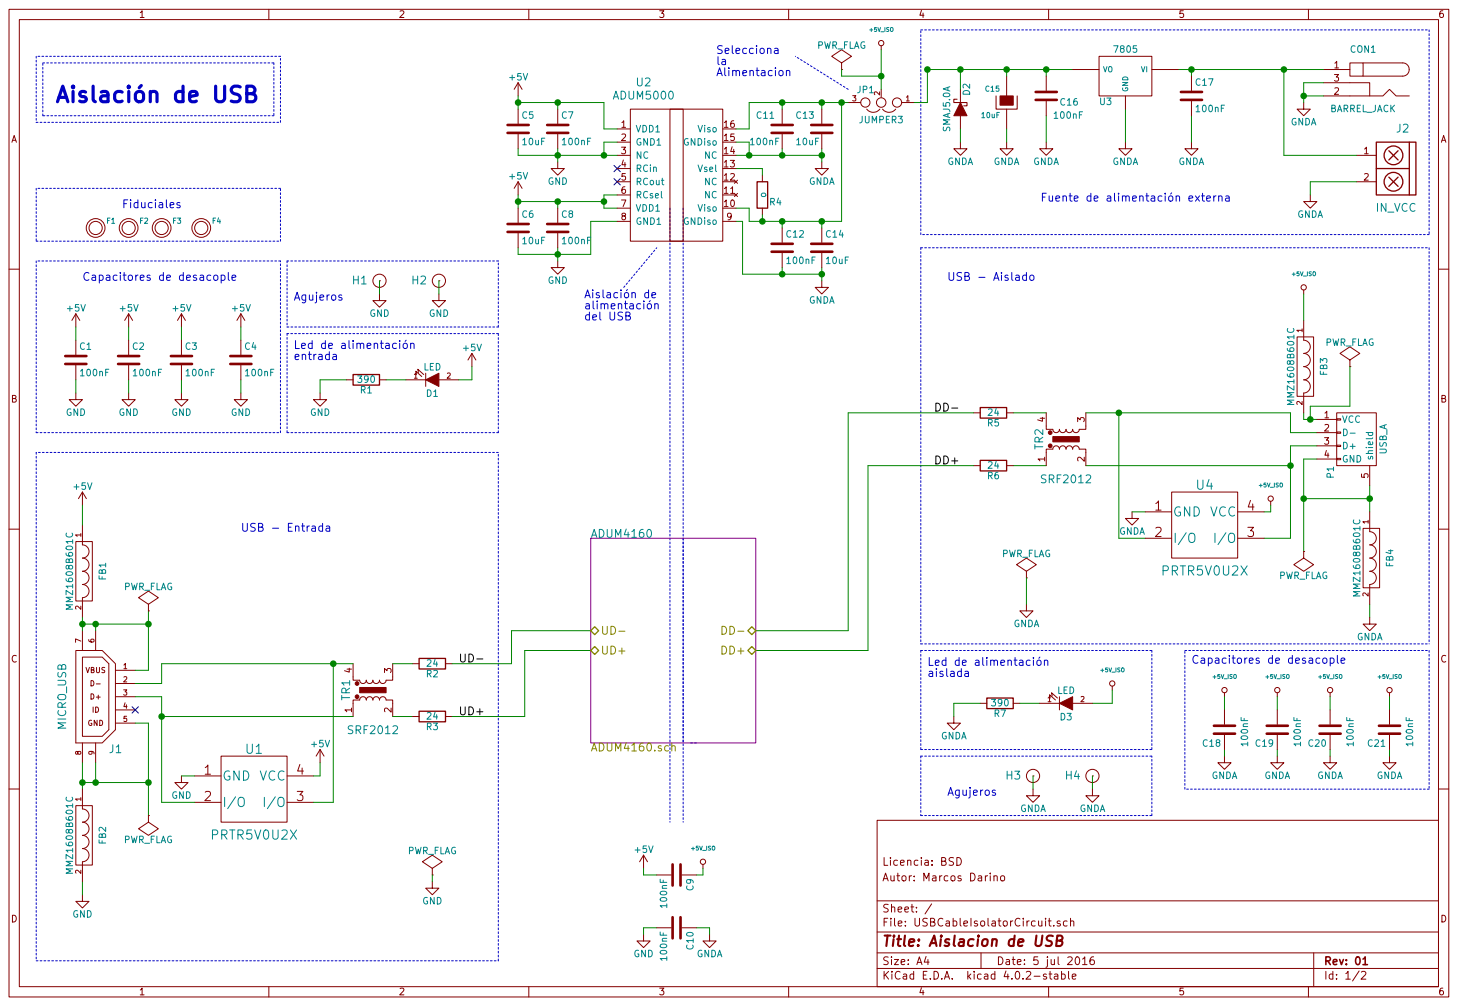
[picture p324: page 1]

o VDD1 1 GND1 2 NC 3 RCin 4 RCout 5 RCsel 6 VDD1 7 GND1 8 GNDiso 9 Viso 10 NC 11 NC 12 Vsel 13 NC 14 GNDiso 15 Viso 16 U2 ADUM5000 C5

Fuente de alimentación externa

entrada Capacitores de desacople
+5V GND

Licencia: BSD
File: USBCableIsolatorCircuit.sch Sheet: / Autor: Marcos Darino

Id: 1/2 Title: Aislacion de USB

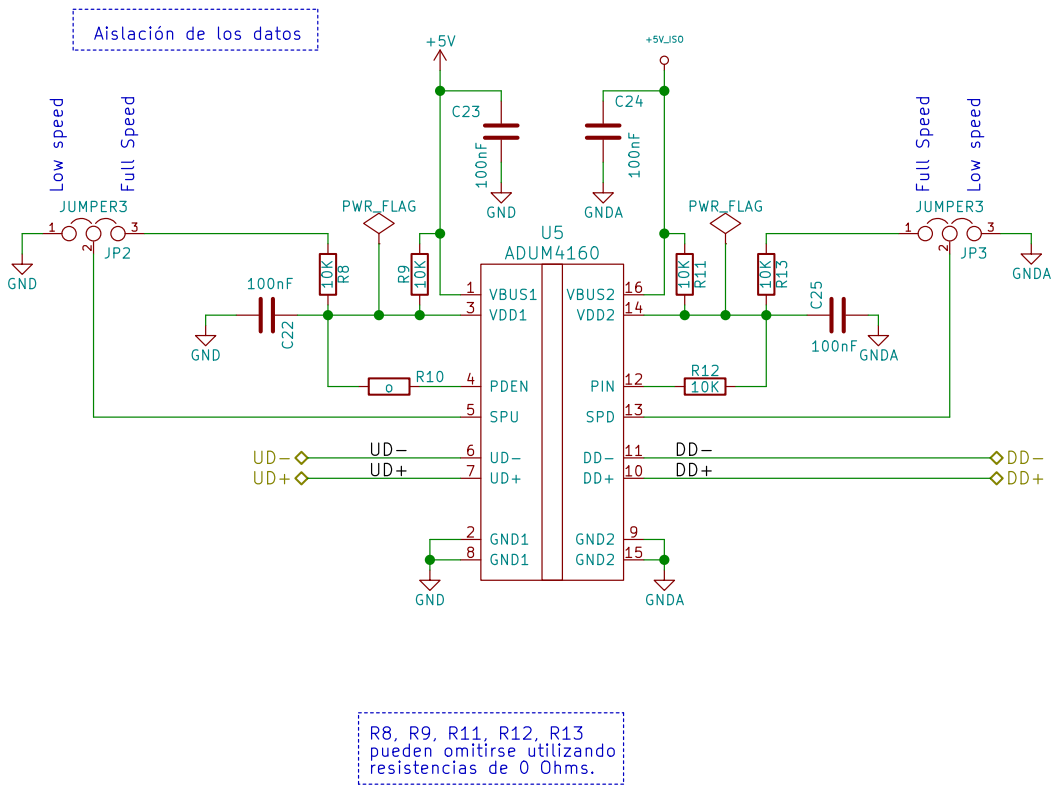
[picture p325: page 2]

Licencia: BSD
File: ADUM4160.sch Sheet: /ADUM4160/ Autor: Marcos Darino

Id: 2/2 Title: Aislacion de USB - ADUM4160
