brengi/CESE-PCB/2018/Slavkin/pap.pdf

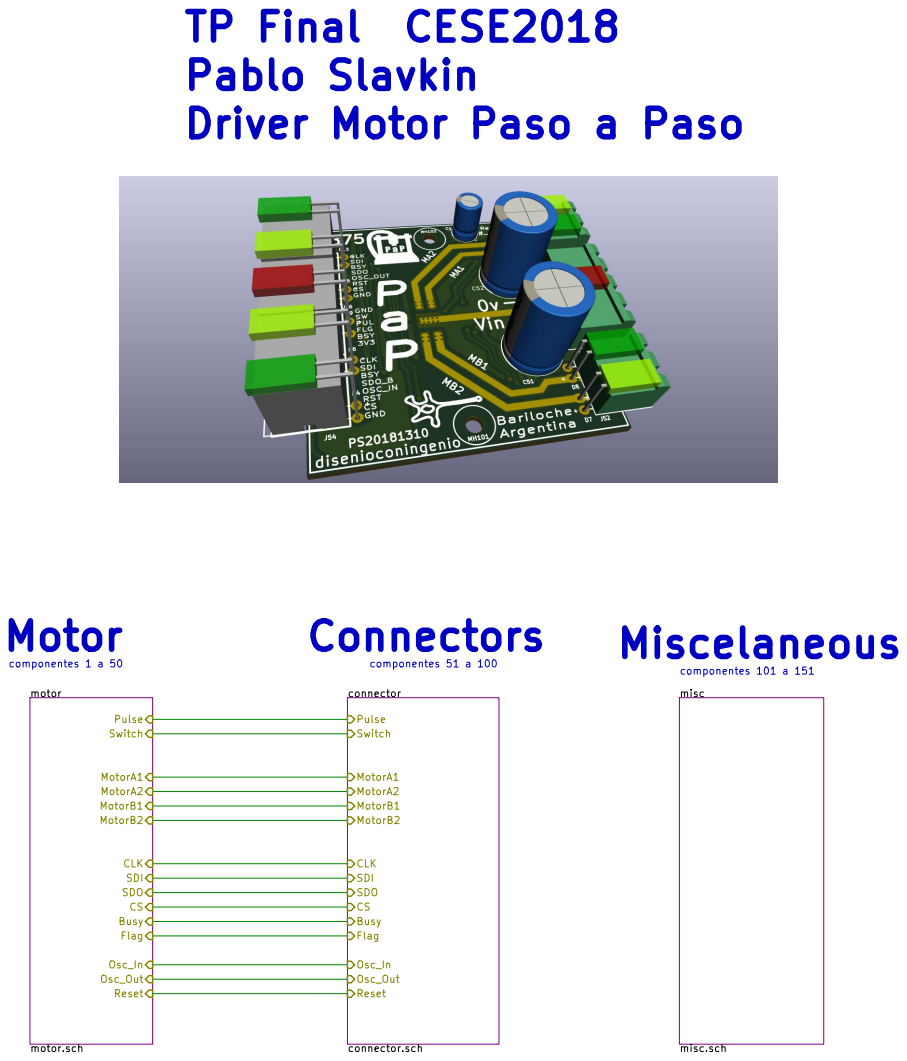
[picture p326: page 1]

componentes 101 a 151 TP Final CESE2018
Pablo Slavkin
Driver Motor Paso a Paso

Busy Pulse Switch CLK Osc_In Osc_Out Reset Flag

connector connector.sch CSCLK
SDI Pulse Switch MotorB2 MotorA2 MotorA1 MotorB1 SDO

File: pap.sch Sheet: / disenioconingenio Pablo Slavkin

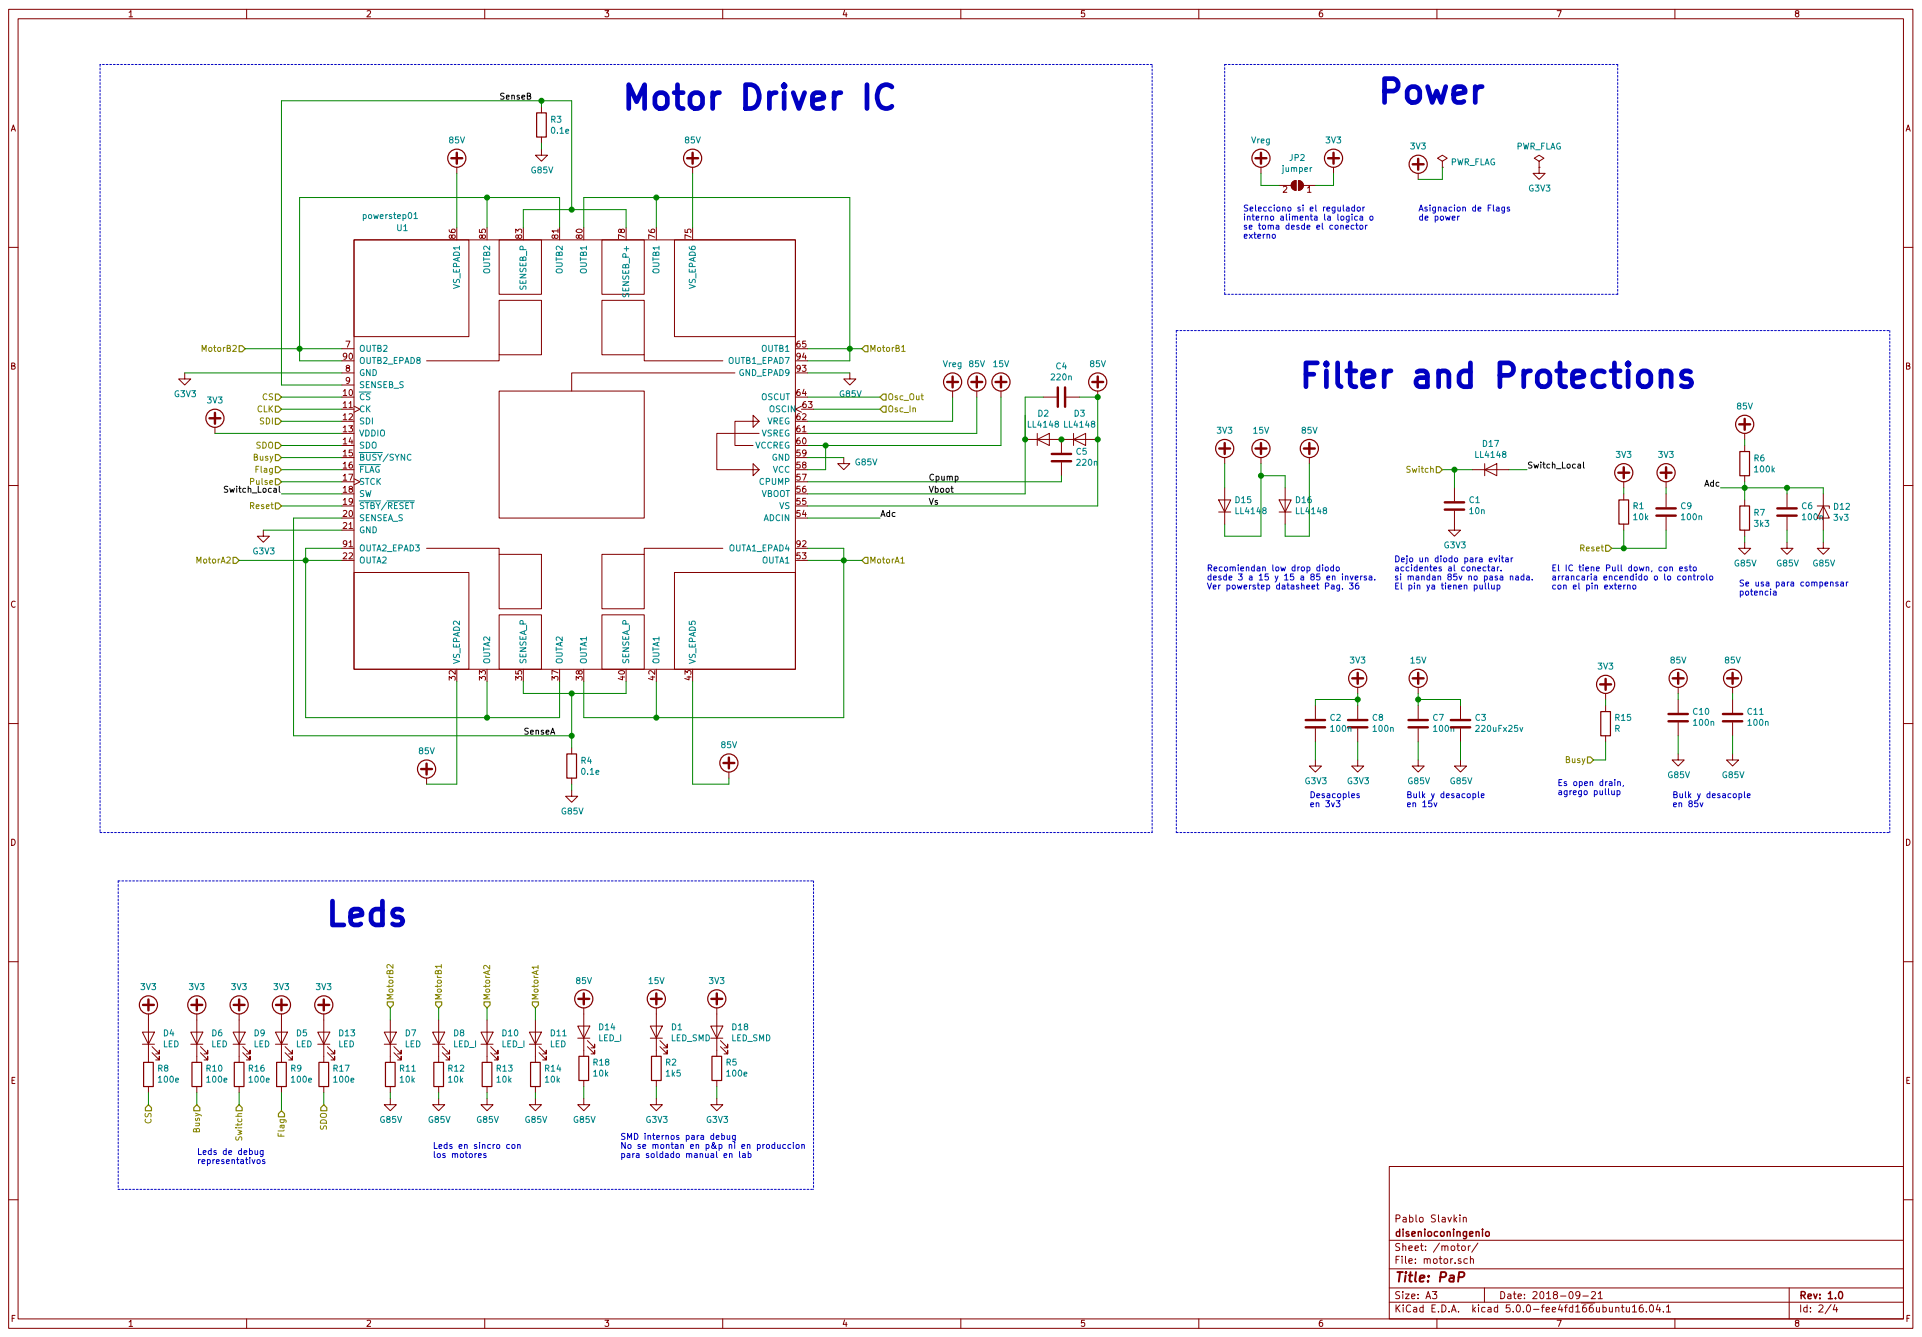
[picture p327: page 2]

Selecciono si el regulador

El IC tiene Pull down, con esto arrancaria encendido o lo controlo

en 85v Es open drain, agrego pullup

SMD internos para debug No se montan en p&p ni en produccion

Leds de debug representativos

Leds en sincro con
los motores

File: motor.sch Sheet: /motor/ disenioconingenio Pablo Slavkin

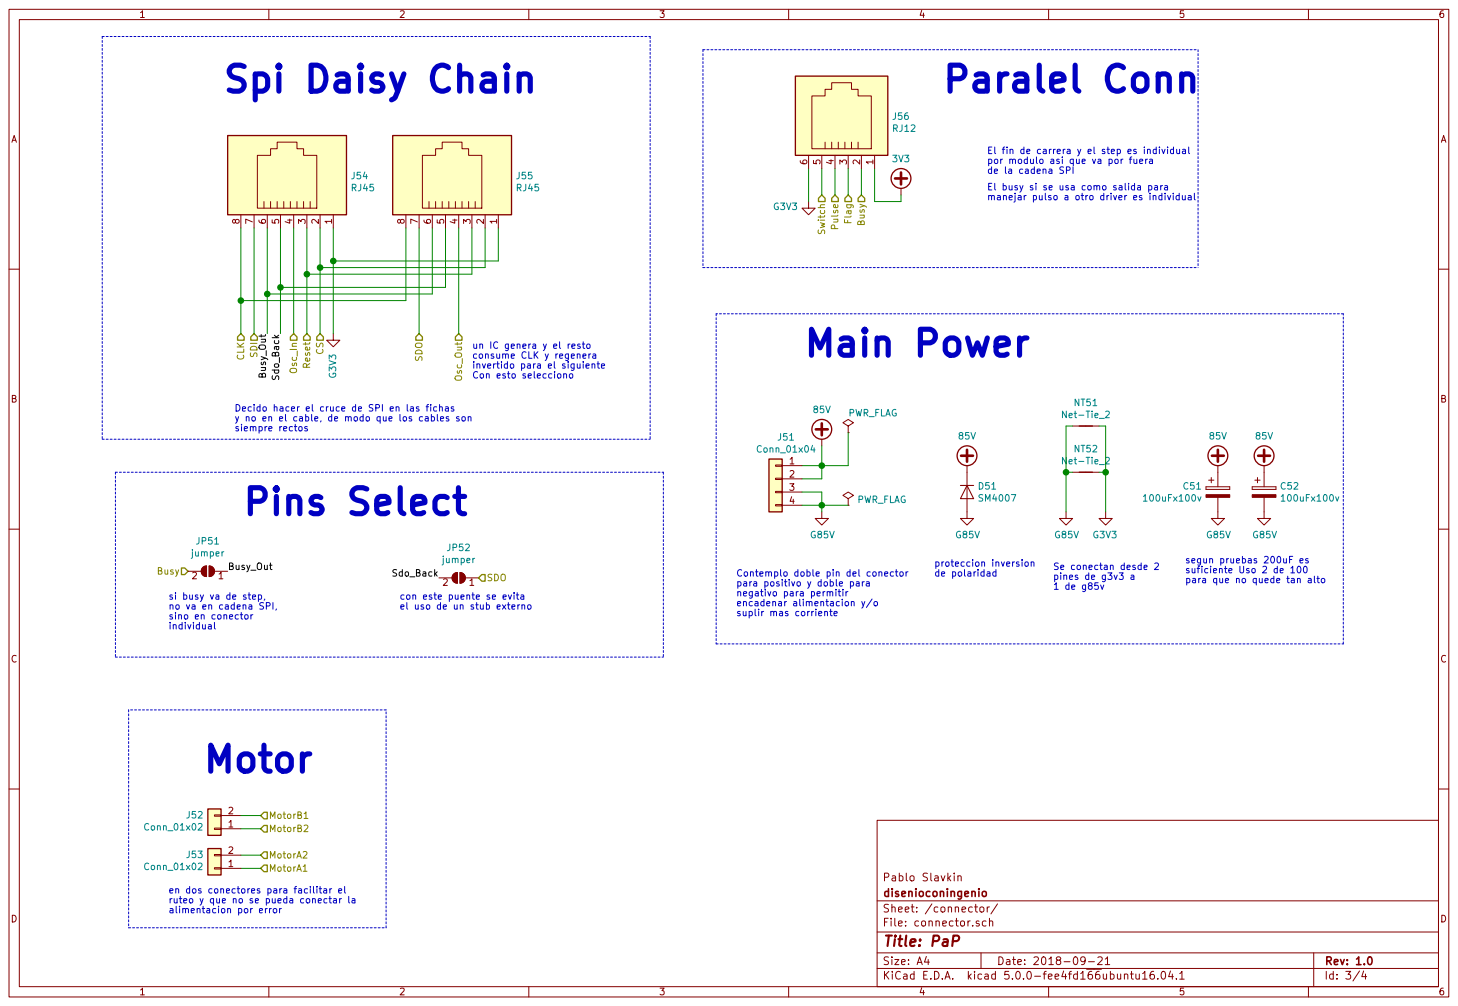
[picture p328: page 3]

El fin de carrera y el step es individual

El busy si se usa como salida para
manejar pulso a otro driver es individual

un IC genera y el resto
consume CLK y regenera

para positivo y doble para
negativo para permitir
encadenar alimentacion y/o

si busy va de step, no va en cadena SPI, sino en conector

File: connector.sch Sheet: /connector/ disenioconingenio Pablo Slavkin

en dos conectores para facilitar el
ruteo y que no se pueda conectar la
alimentacion por error

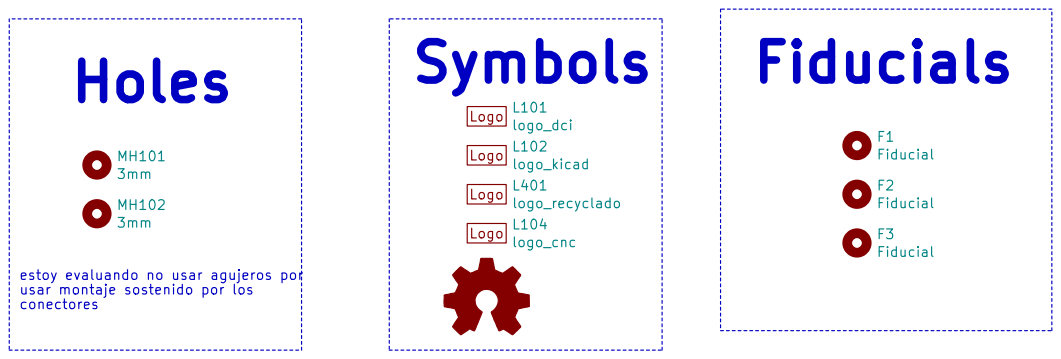
[picture p329: page 4]

estoy evaluando no usar agujeros por

File: misc.sch Sheet: /misc/ disenioconingenio Pablo Slavkin
