brengi/CESE-PCB/2018/Germino/esquematicos/retro-ciaa.pdf

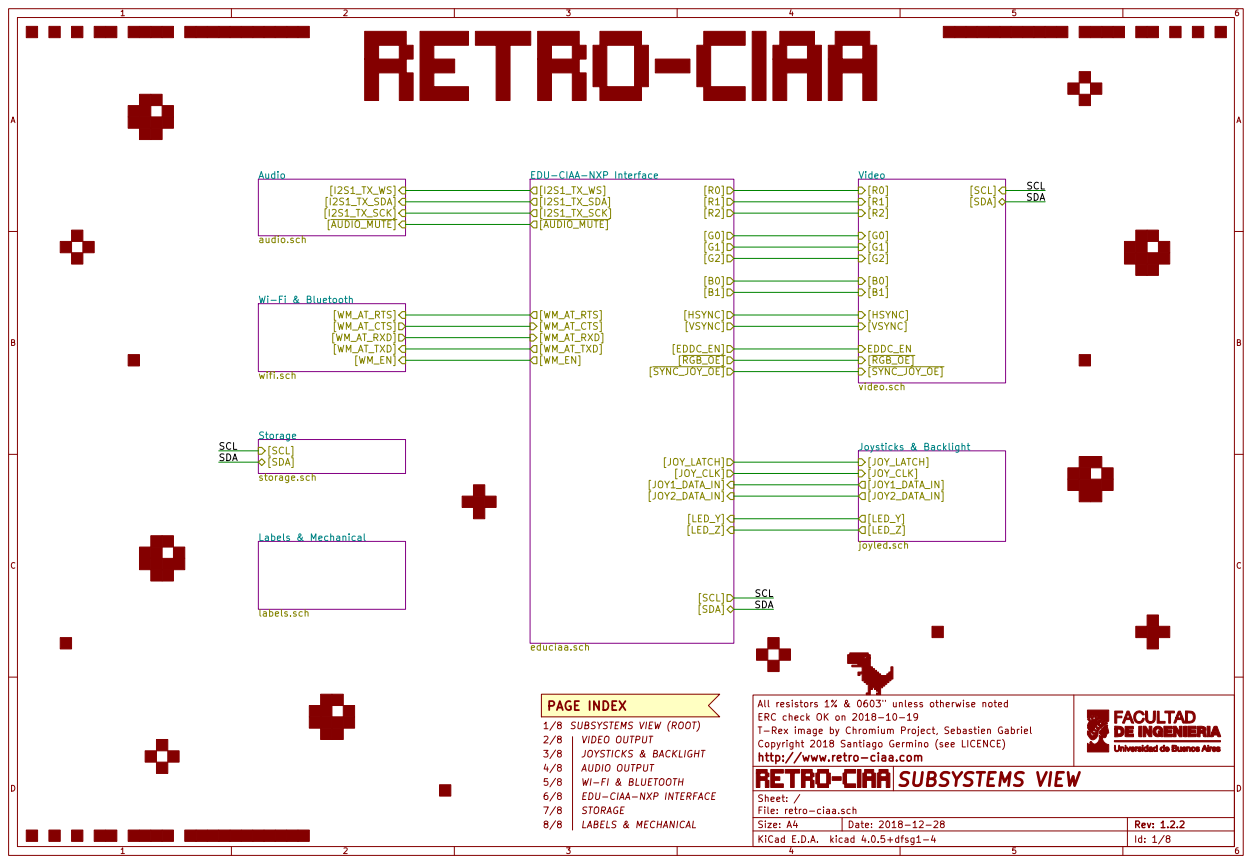
[picture p330: page 1]

[AUDIO_MUTE] Wi-Fi & Bluetooth wifi.sch
audio.sch

LABELS & MECHANICAL PAGE INDEX

All resistors 1% & 0603" unless otherwise noted ERC check OK on 2018-10-19 T-Rex image by Chromium Project, Sebastien Gabriel

Copyright 2018 Santiago Germino (see LICENCE)
File: retro-ciaa.sch Sheet: / http://www.retro-ciaa.com

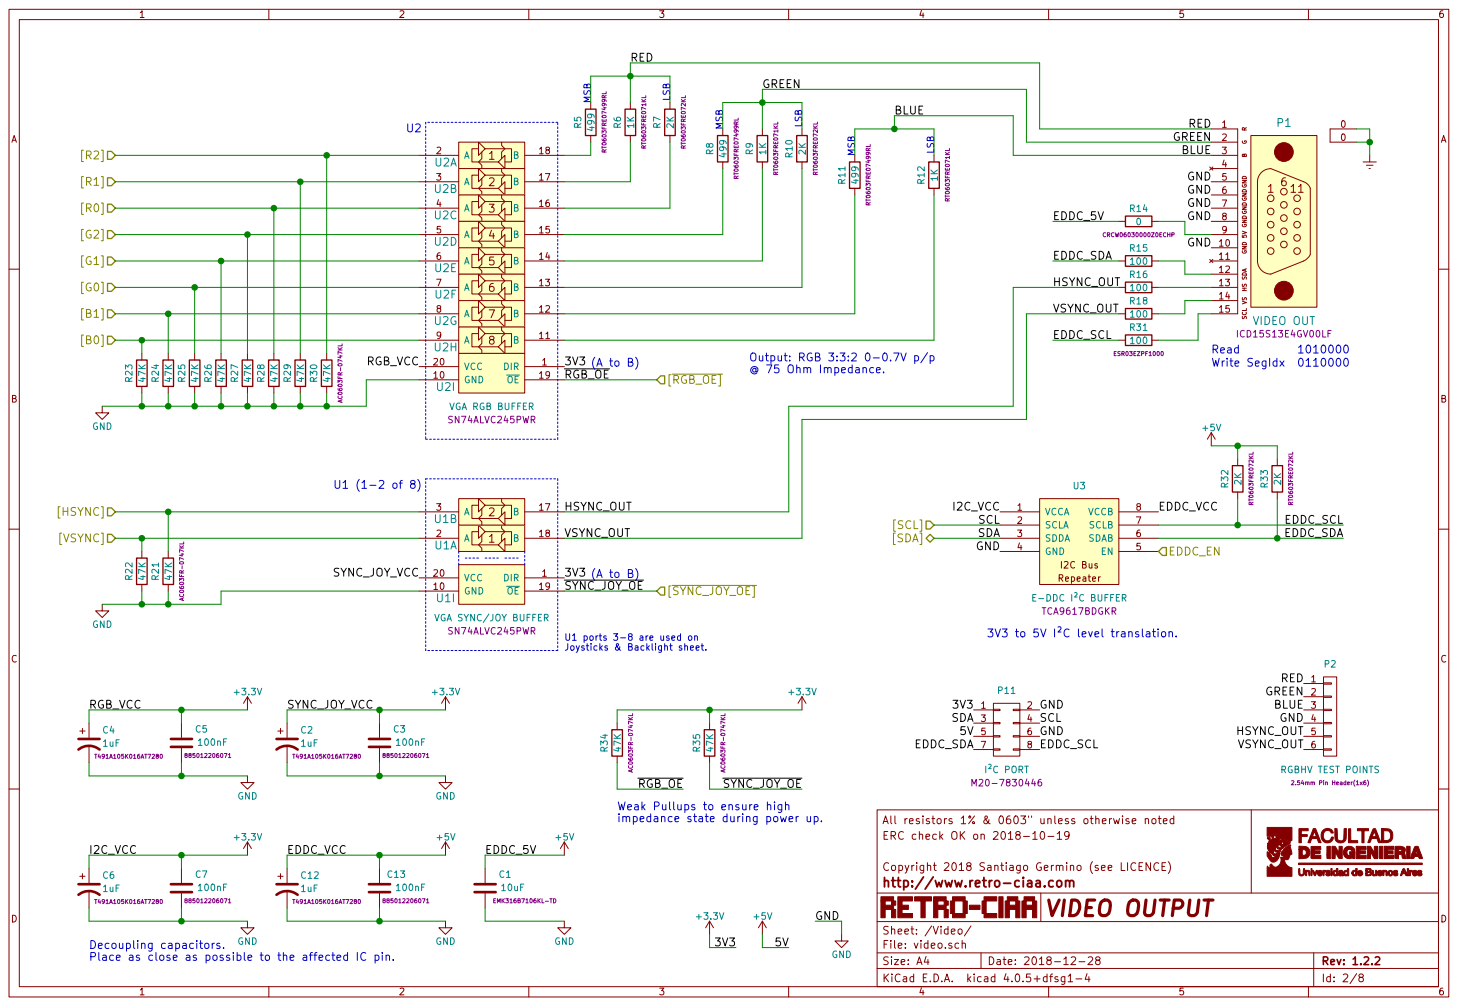
[picture p331: page 2]

B G GND GNDGNDGNDGND HS R SCL SDA VS 0

U1 ports 3-8 are used on
Joysticks & Backlight sheet.

Weak Pullups to ensure high
impedance state during power up.

All resistors 1% & 0603" unless otherwise noted ERC check OK on 2018-10-19 Copyright 2018 Santiago Germino (see LICENCE)

File: video.sch Sheet: /Video/ http://www.retro-ciaa.com

Decoupling capacitors.
Place as close as possible to the affected IC pin.

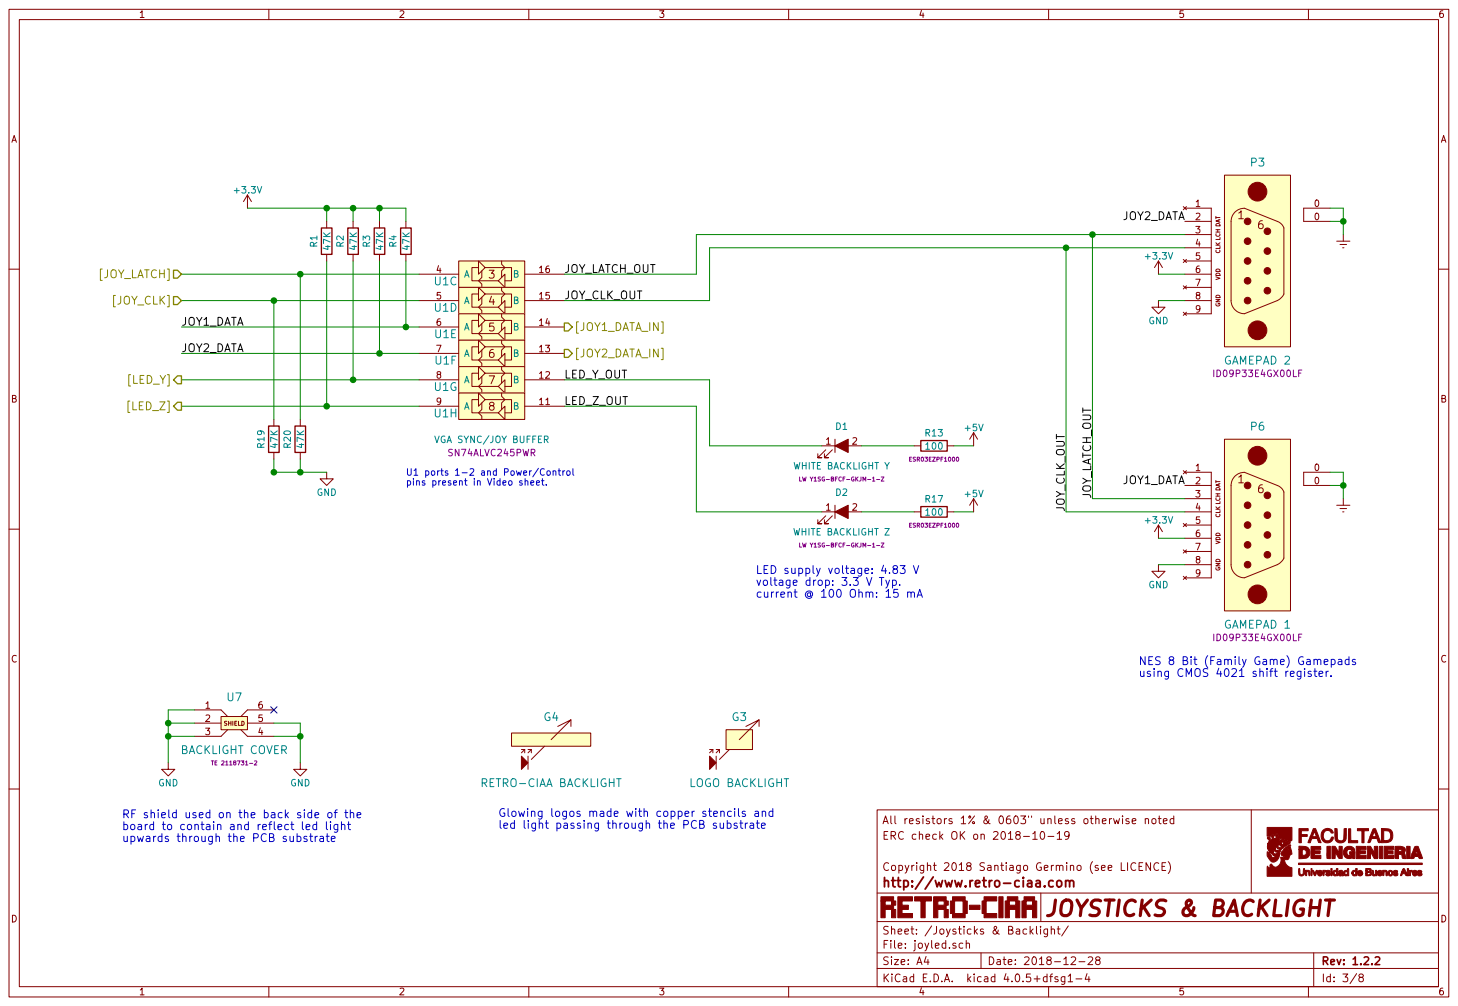
[picture p332: page 3]

+3.3V JOY1_DATA JOY_LATCH_OUT JOY_CLK_OUT | 5

[JOY2_DATA_IN] RF shield used on the back side of the

VGA SYNC/JOY BUFFER
SN74ALVC245PWR

LW Y1SG-BFCF-GKJM-1-Z GND

U1 ports 1-2 and Power/Control

NES 8 Bit (Family Game) Gamepads
using CMOS 4021 shift register.

Glowing logos made with copper stencils and

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

board to contain and reflect led light
upwards through the PCB substrate

http://www.retro-ciaa.com

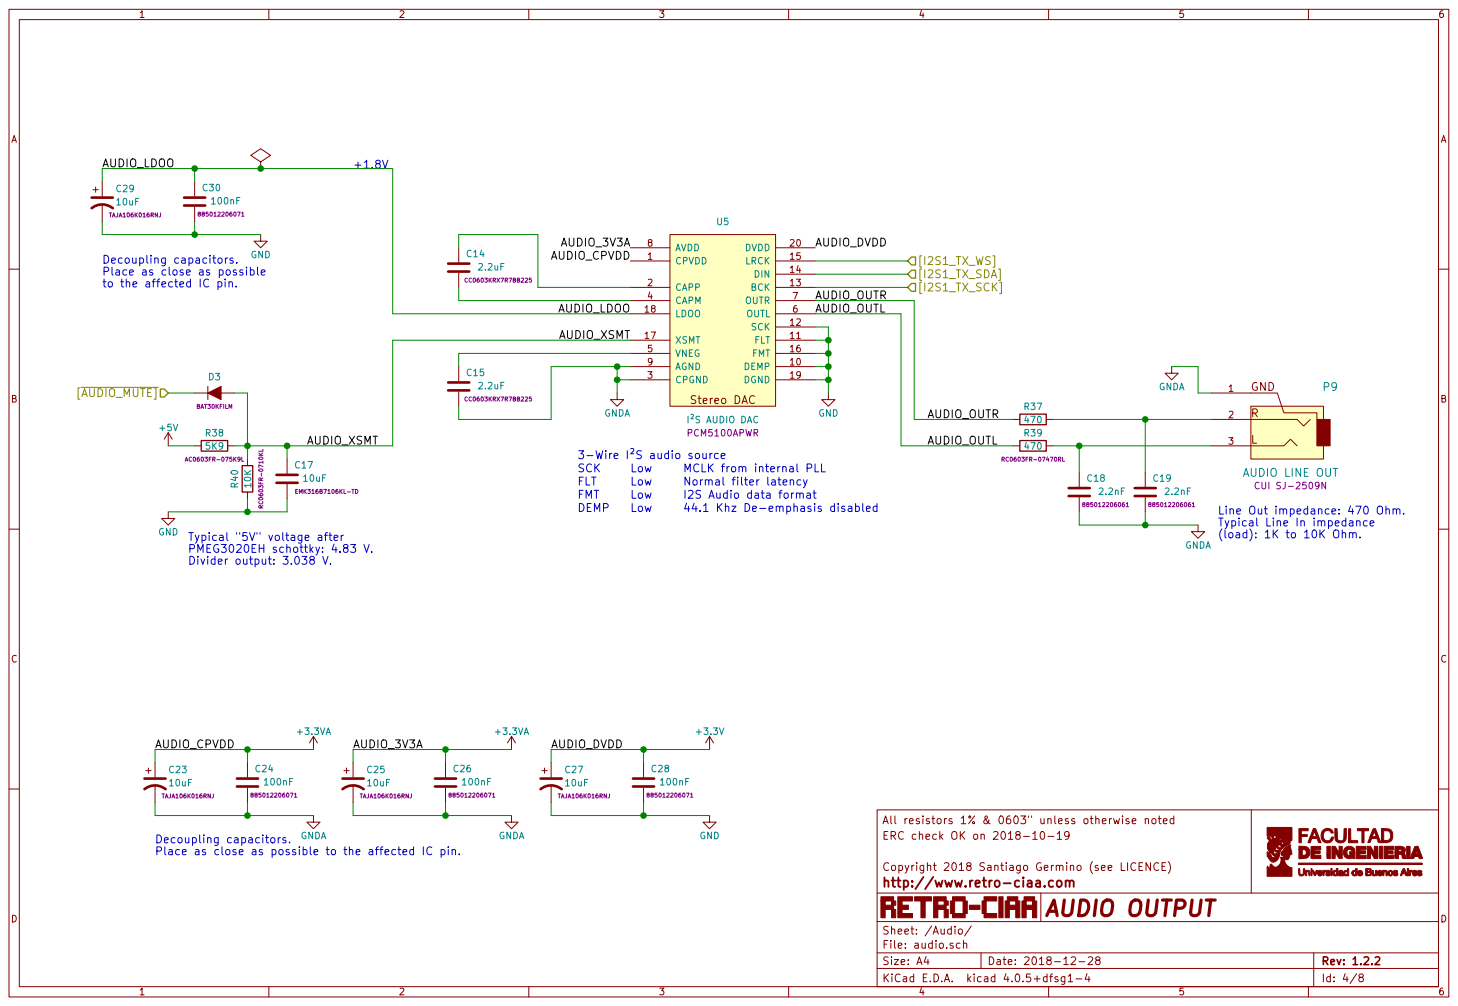
[picture p333: page 4]

Decoupling capacitors.
Place as close as possible
to the affected IC pin.

3-Wire I²S audio source

EMK316B7106KL-TD GND Typical "5V" voltage after

Typical Line In impedance

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

Place as close as possible to the affected IC pin.

File: audio.sch Sheet: /Audio/ http://www.retro-ciaa.com

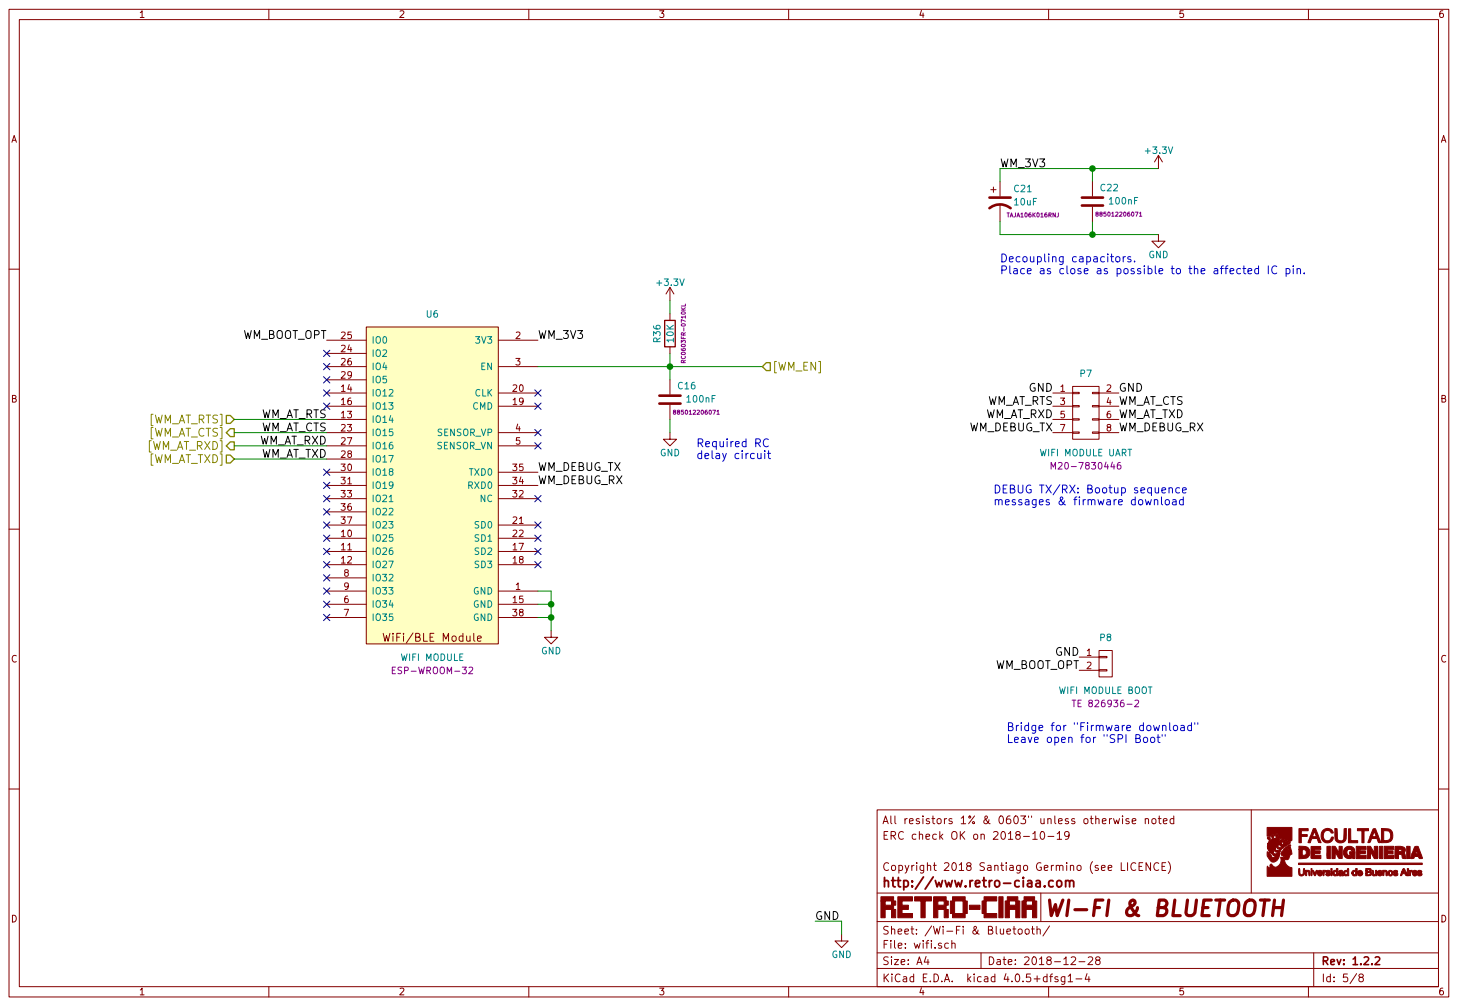
[picture p334: page 5]

Decoupling capacitors.
Place as close as possible to the affected IC pin.
[WM_EN] GND GND

DEBUG TX/RX: Bootup sequence

Leave open for "SPI Boot"

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

File: wifi.sch Sheet: /Wi-Fi & Bluetooth/ http://www.retro-ciaa.com

Id: 5/8 WI-FI & BLUETOOTH

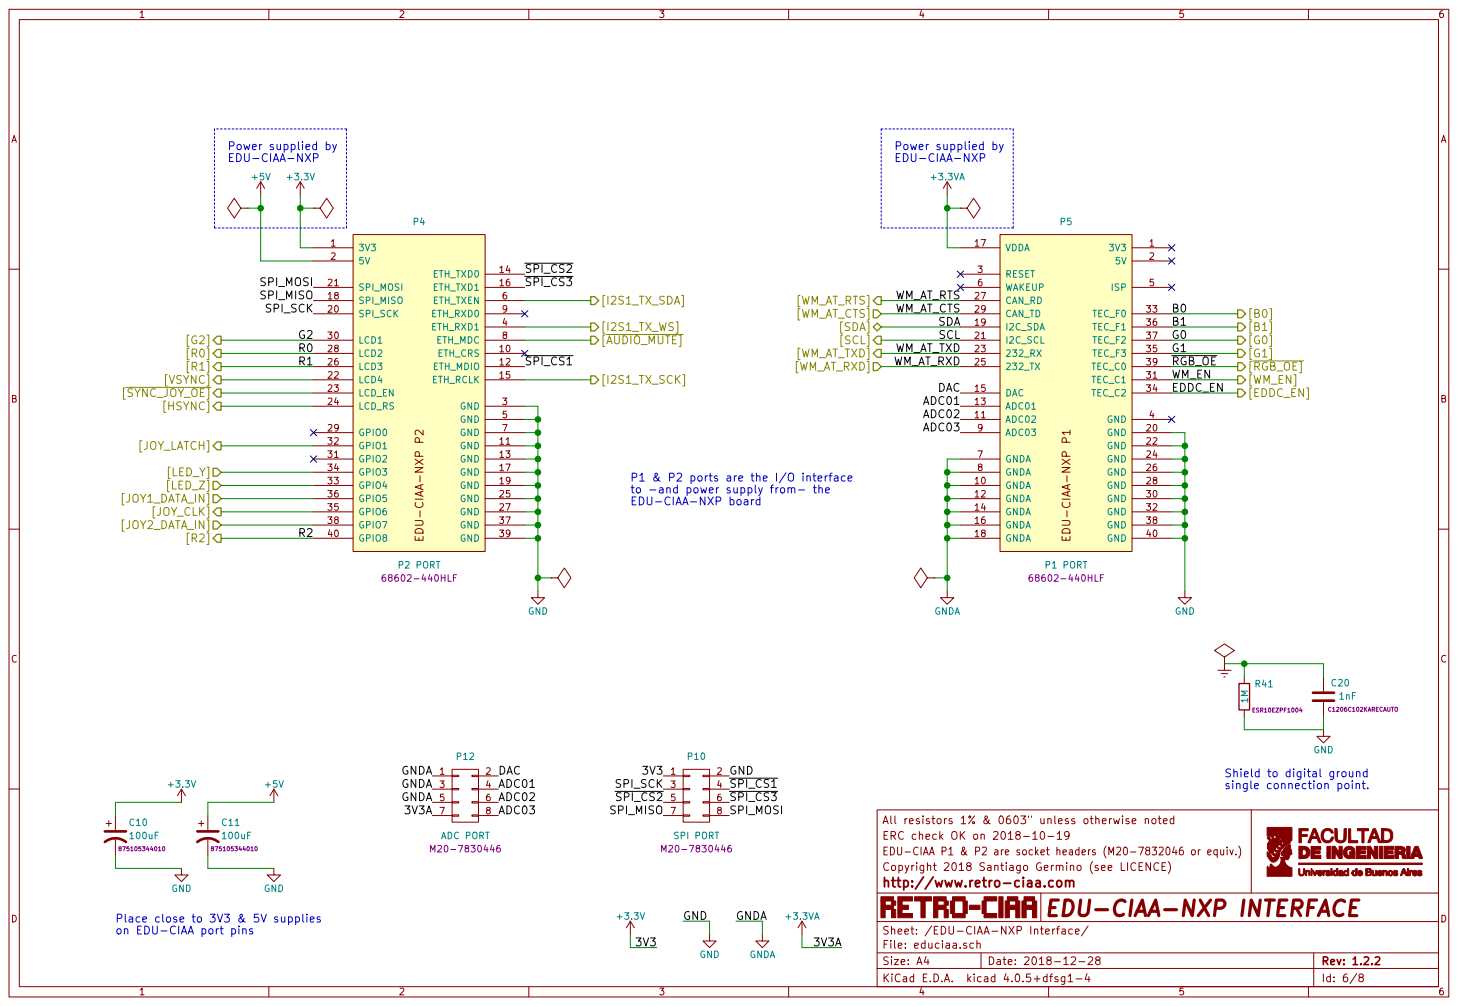
[picture p335: page 6]

Copyright 2018 Santiago Germino (see LICENCE) EDU-CIAA-NXP P1

P1 & P2 ports are the I/O interface
to -and power supply from- the
EDU-CIAA-NXP board

+5V Place close to 3V3 & 5V supplies

All resistors 1% & 0603" unless otherwise noted ERC check OK on 2018-10-19 EDU-CIAA P1 & P2 are socket headers (M20-7832046 or equiv.)

File: educiaa.sch Sheet: /EDU-CIAA-NXP Interface/ http://www.retro-ciaa.com

Id: 6/8 EDU-CIAA-NXP INTERFACE

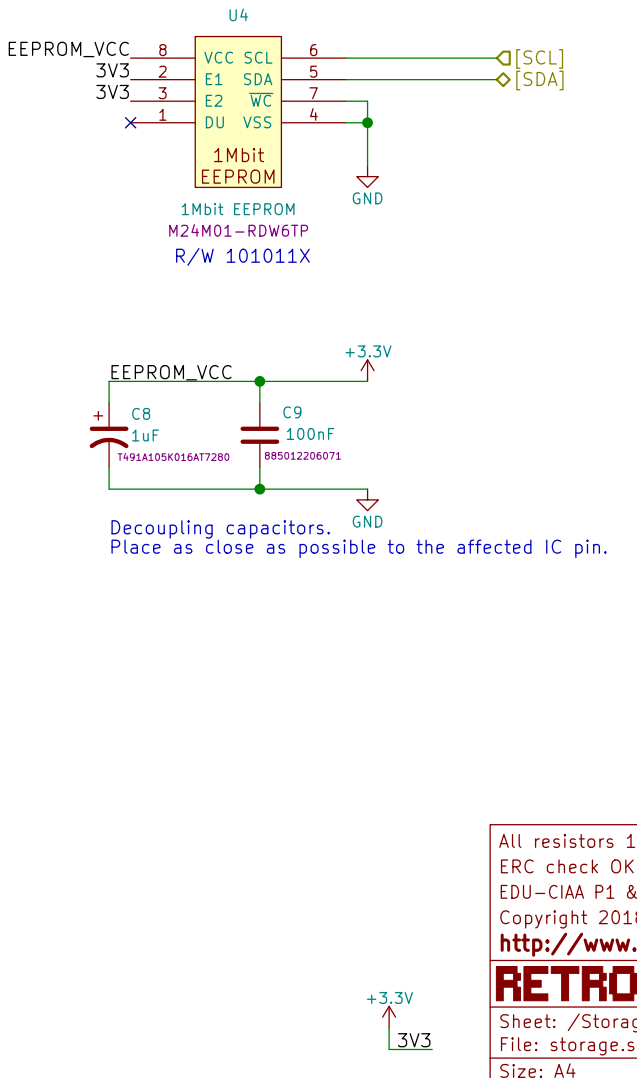
[picture p336: page 7]

Place as close as possible to the affected IC pin. GND

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

Copyright 2018 Santiago Germino (see LICENCE)
http://www.retro-ciaa.com

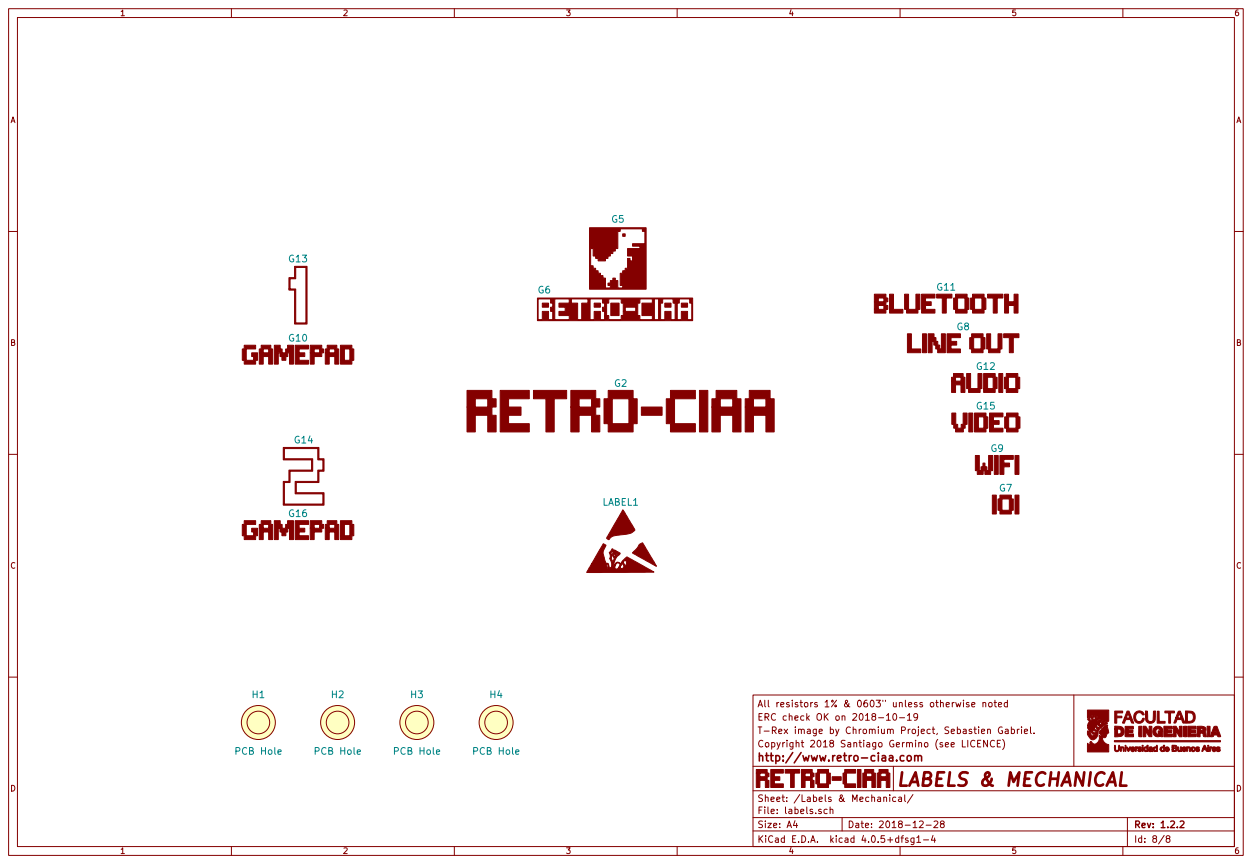
[picture p337: page 8]
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

File: labels.sch Sheet: /Labels & Mechanical/ http://www.retro-ciaa.com
