brengi/CESE-PCB/2018/Lavigna/PRACTICA_FINAL/DOC/Papilio_DUO.pdf

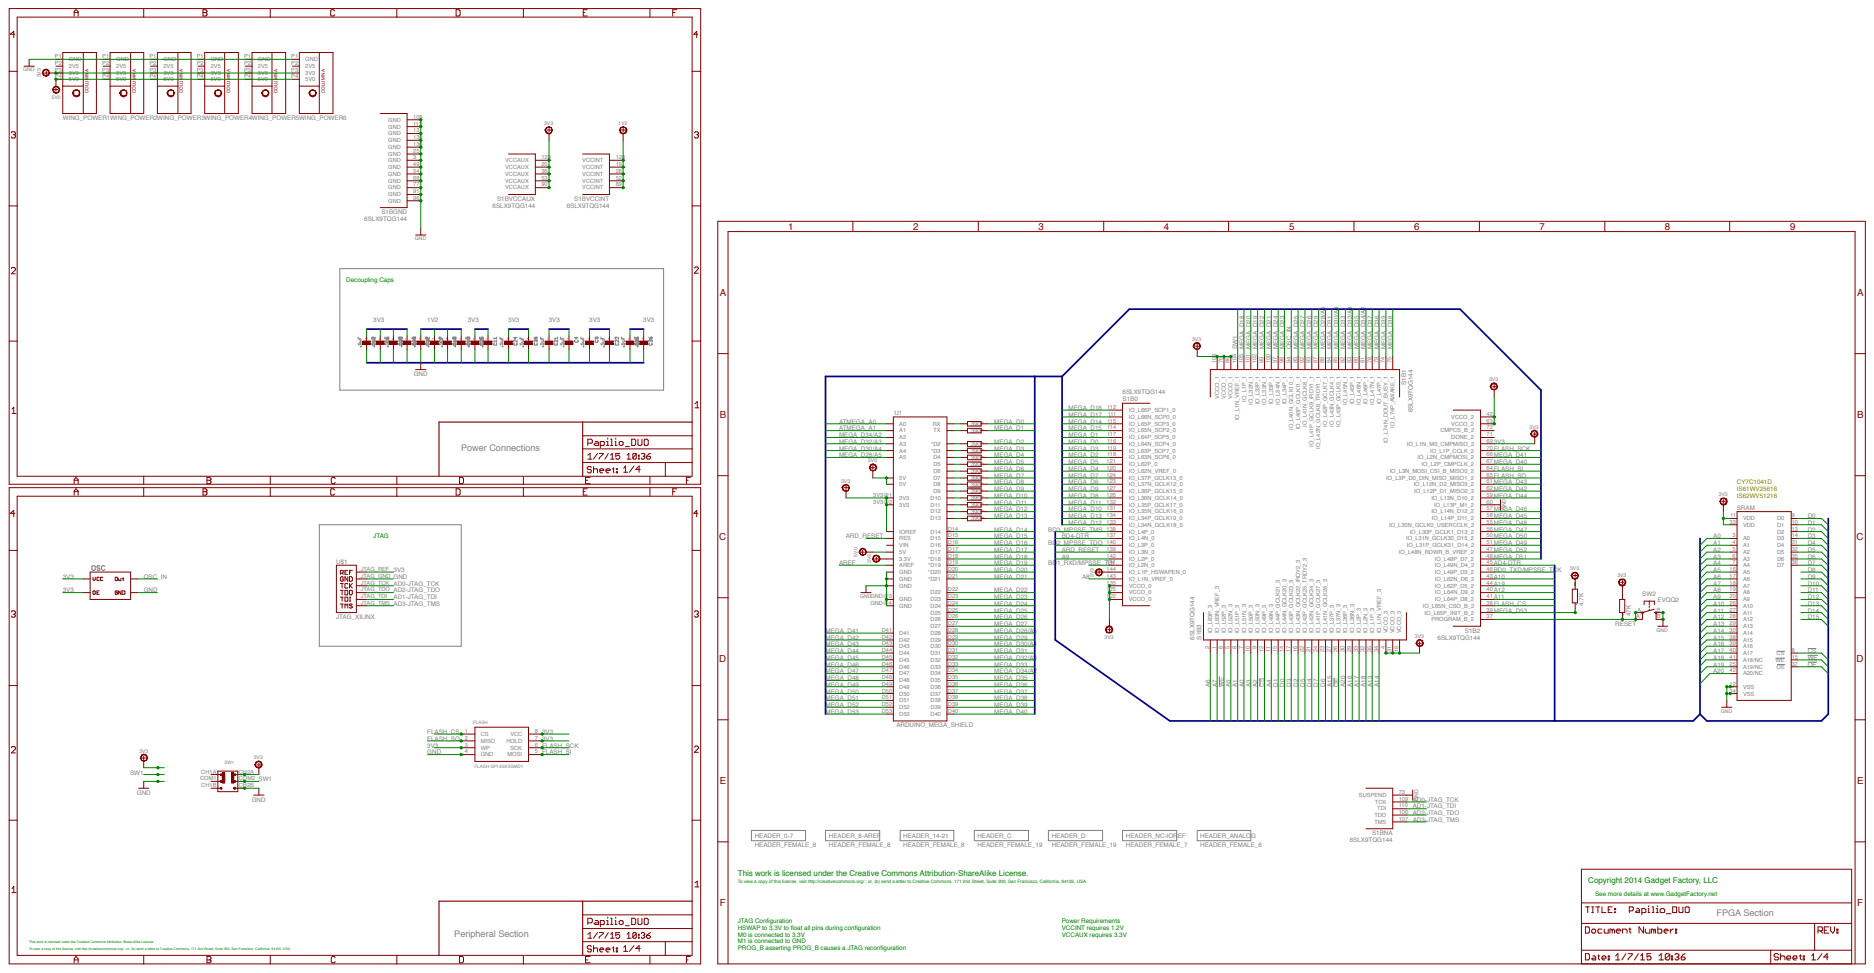
[picture p338: page 1]

Copyright 2014 Gadget Factory, LLC This work is licensed under the Creative Commons Attribution-ShareAlike License.

To view a copy of this license, visit http://creativecommons.org/ ; or, (b) send a letter to Creative Commons, 171 2nd Street, Suite 300, San Francisco, California, 94105, USA.

See more details at www.GadgetFactory.net

JTAG Configuration
HSWAP to 3.3V to float all pins during configuration
M0 is connected to 3.3V
M1 is connected to GND
PROG_B asserting PROG_B causes a JTAG reconfiguration

This work is licensed under the Creative Commons Attribution Share-Alike License.

# delays 1V2 start

3.3uH

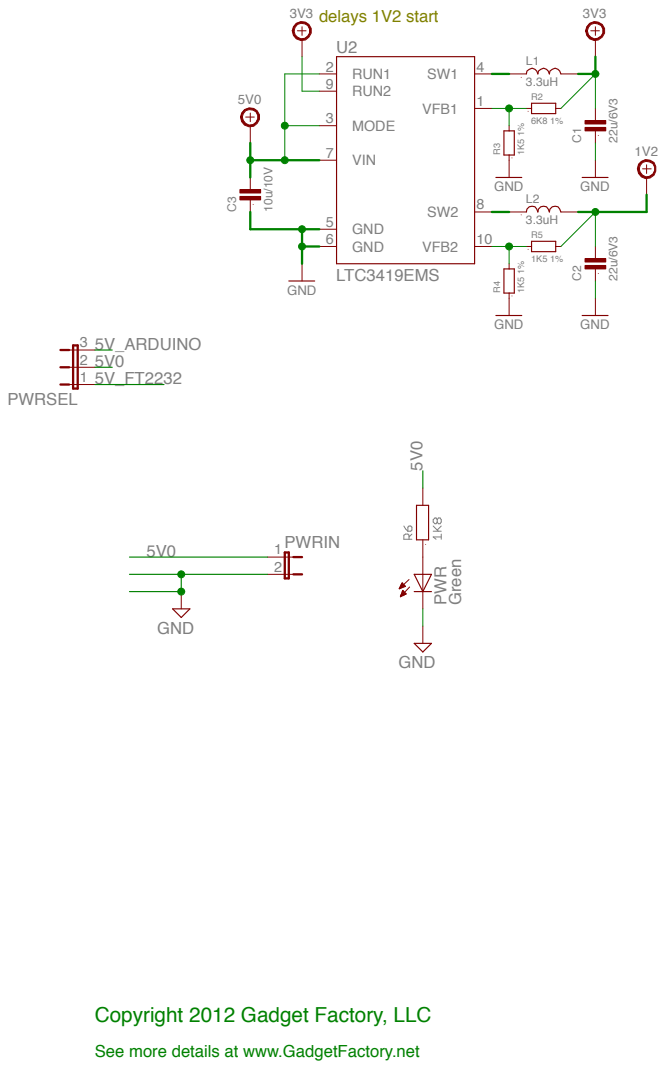
[picture p339: page 2]

Copyright 2012 Gadget Factory, LLC

See more details at www.GadgetFactory.net

3.3V

1.8V

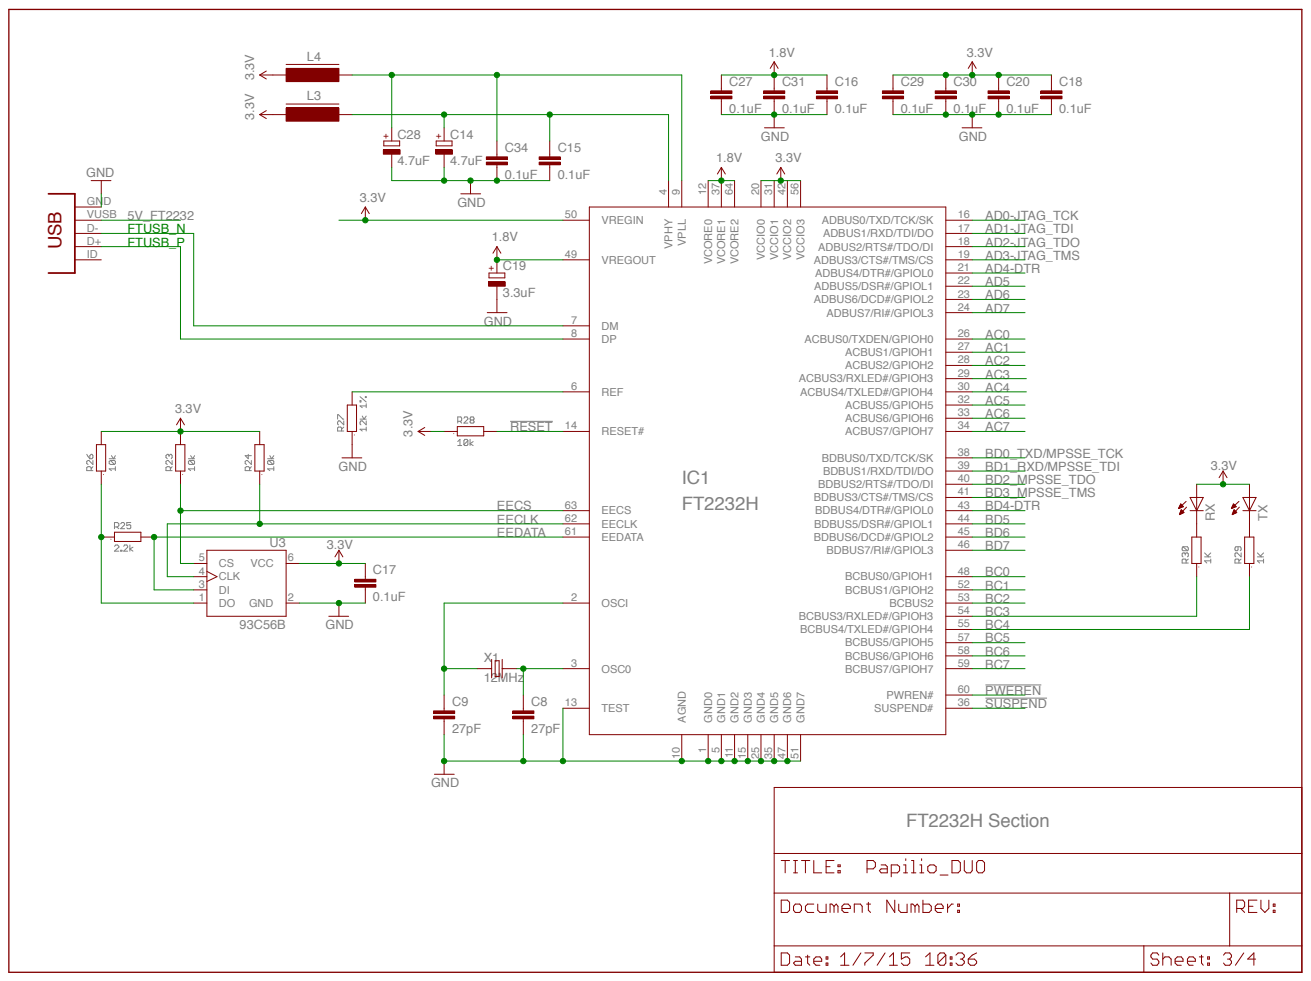
[picture p340: page 3]

EECLK | EEDATA 61 EECLK 62 EECS 63

EEDATA

U3 3.3V | OSCI 2

1M

# MH2029-300Y

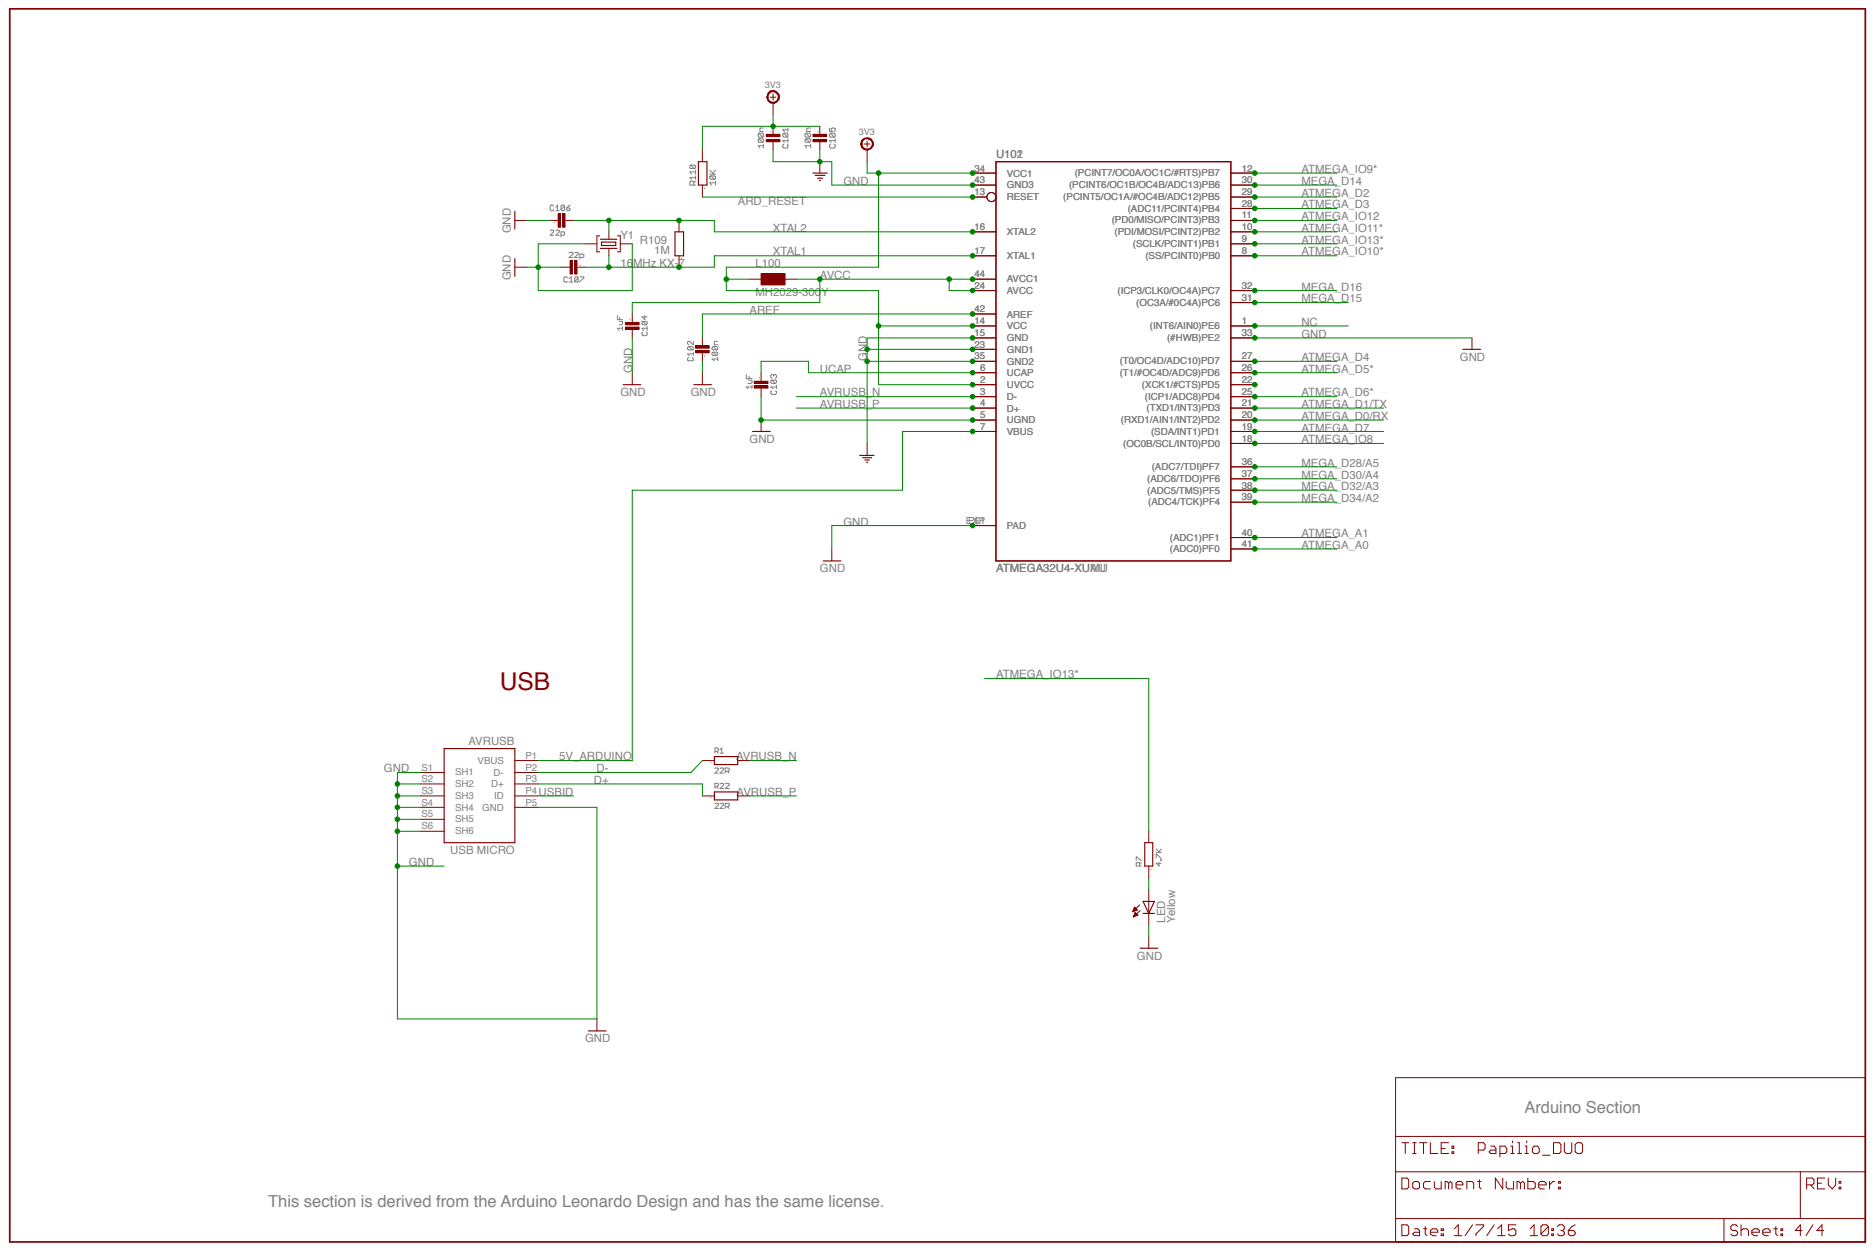
[picture p341: page 4]

VCC 14

GND1 23

UCAP 6

This section is derived from the Arduino Leonardo Design and has the same license.
