brengi/CESE-PCB/2018/Oliva/R_OlivaTPFinal/WEMB02_j/WEMB02_j/docs/SchPrintout_v02h_121118.pdf

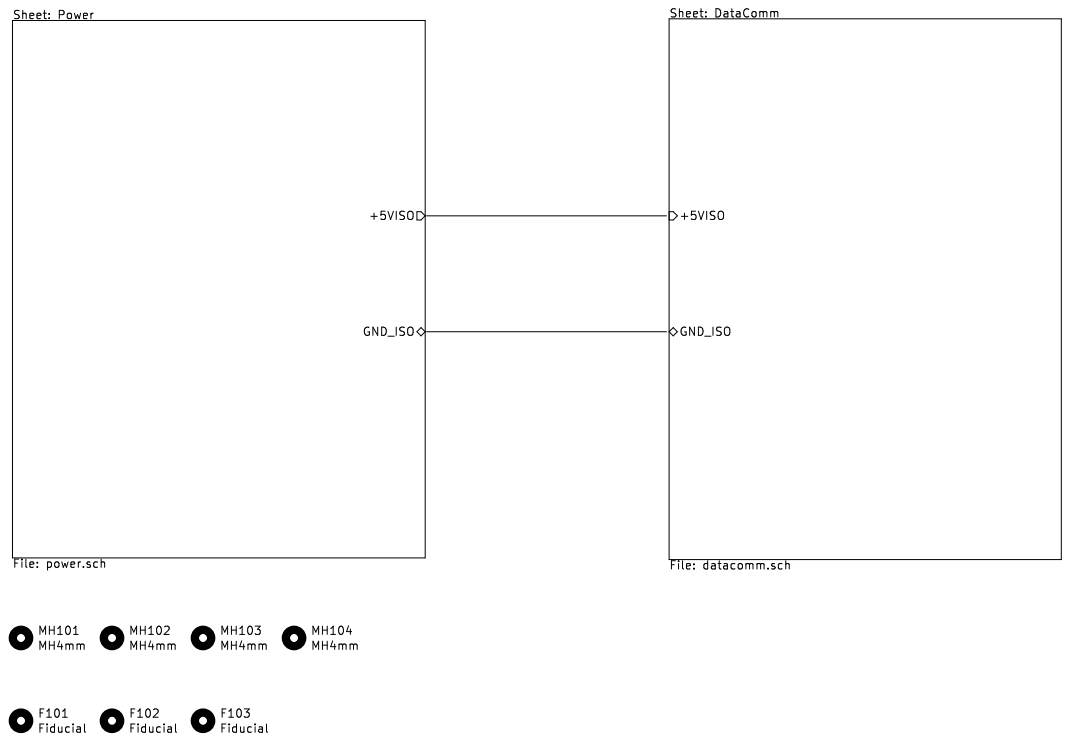
[picture p351: page 1]

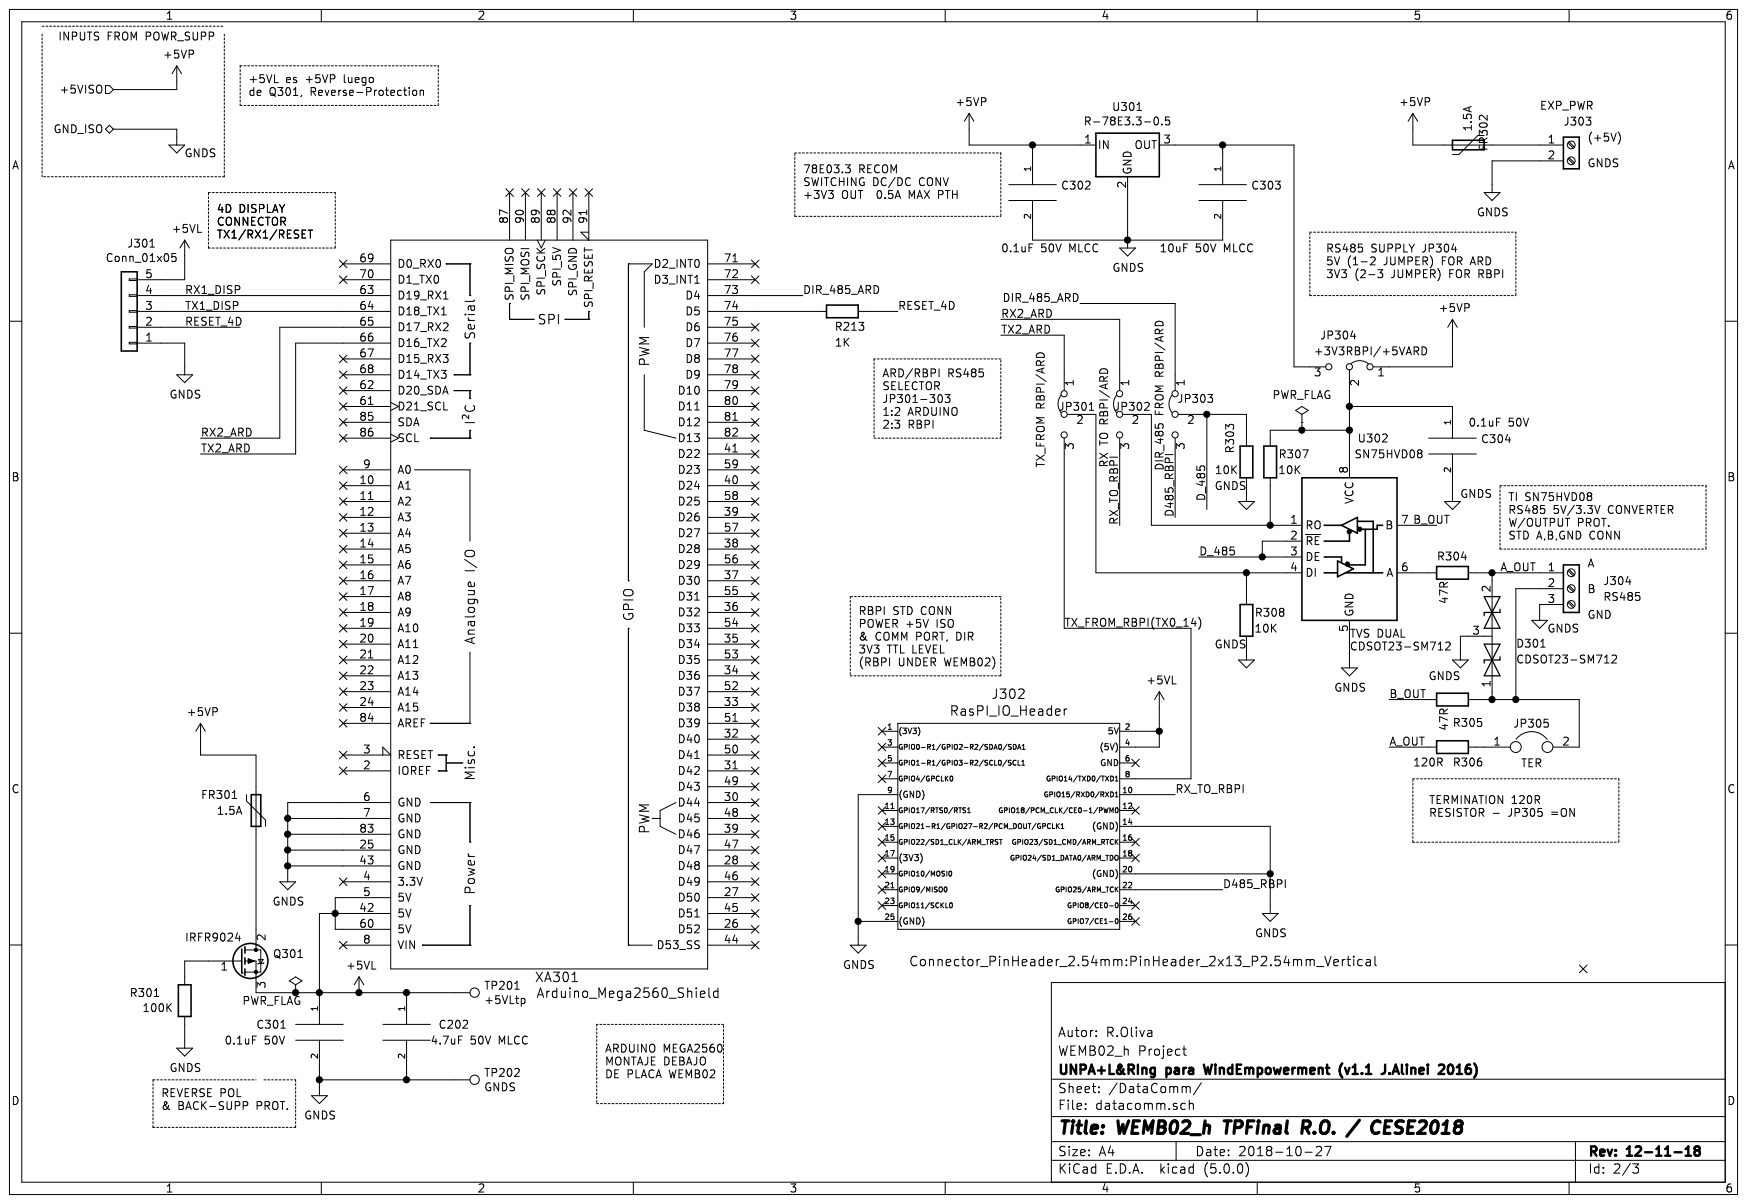
[picture p352: page 2]

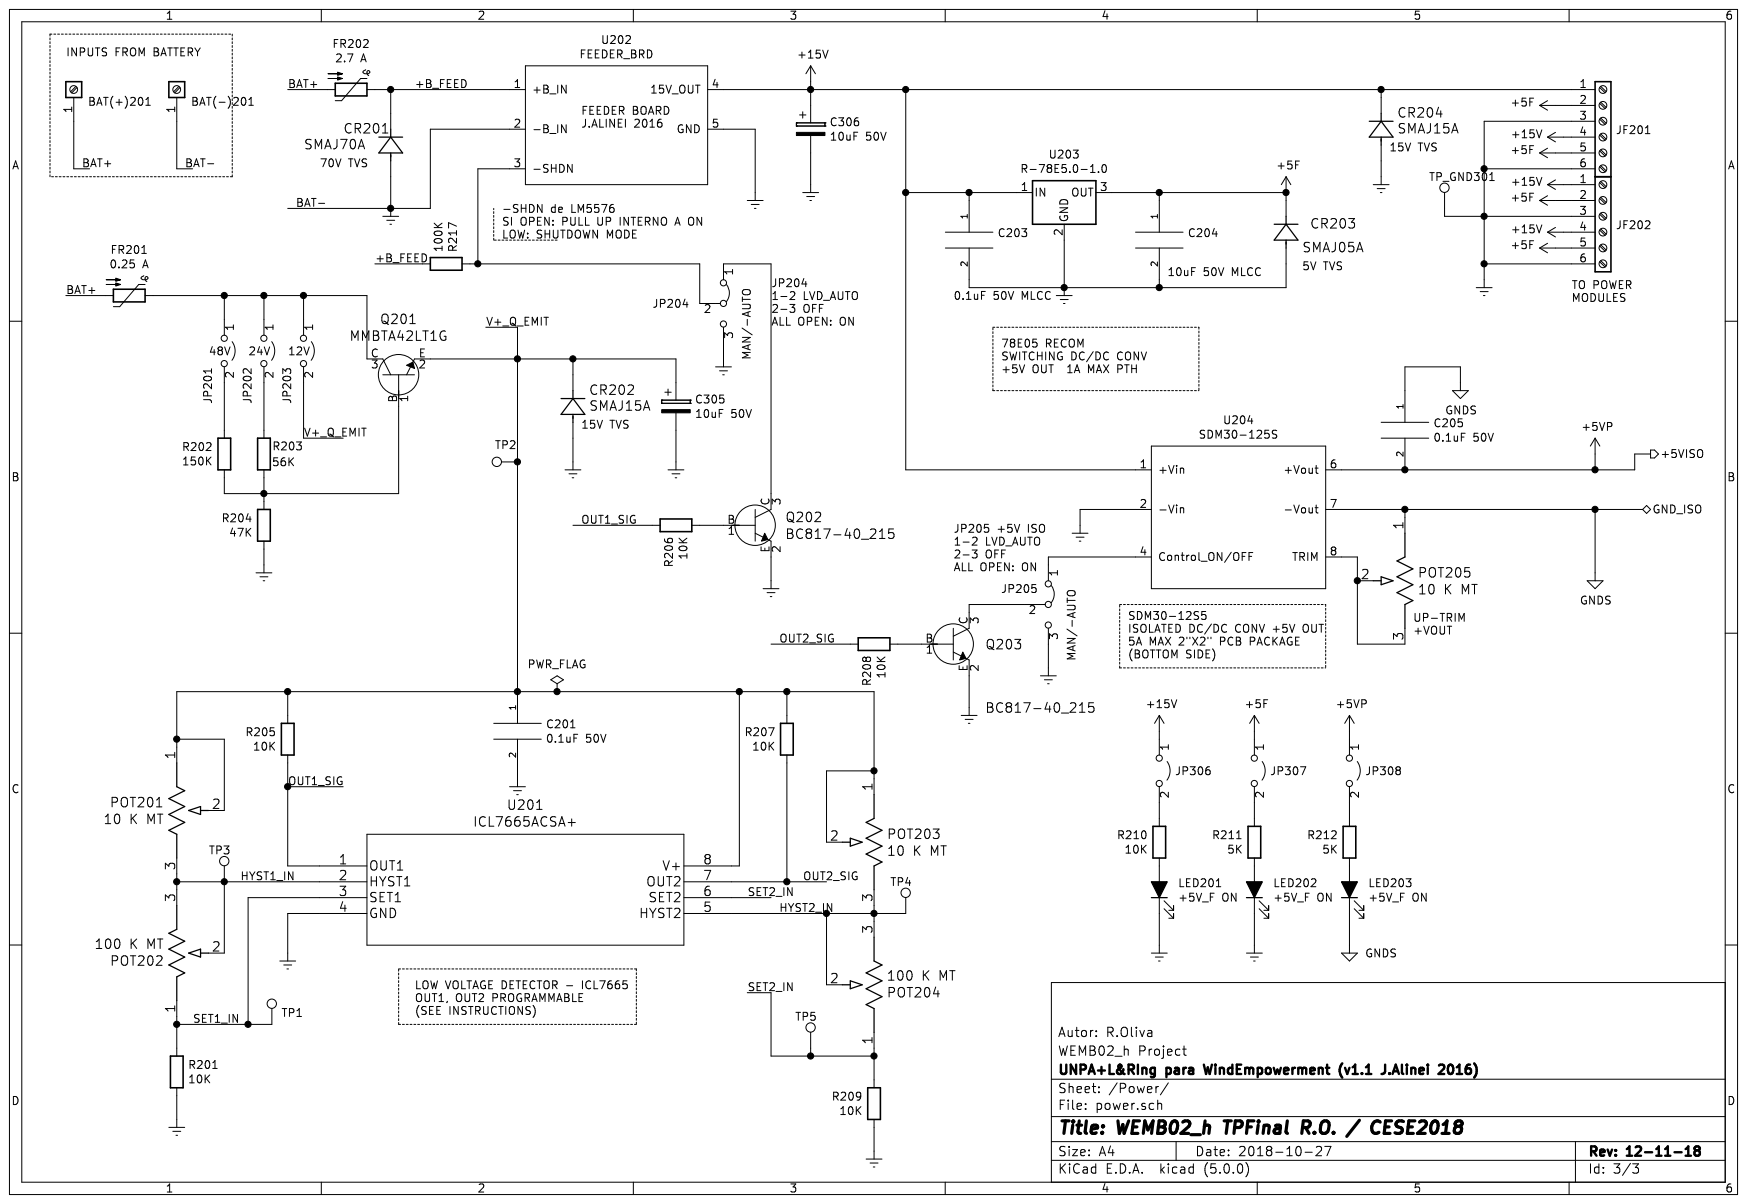
[picture p353: page 3]
