brengi/CESE-PCB/AislacionUSB/doc/Circuitos modelos/Circuito Modelo 2 -Circuitsathome.pdf

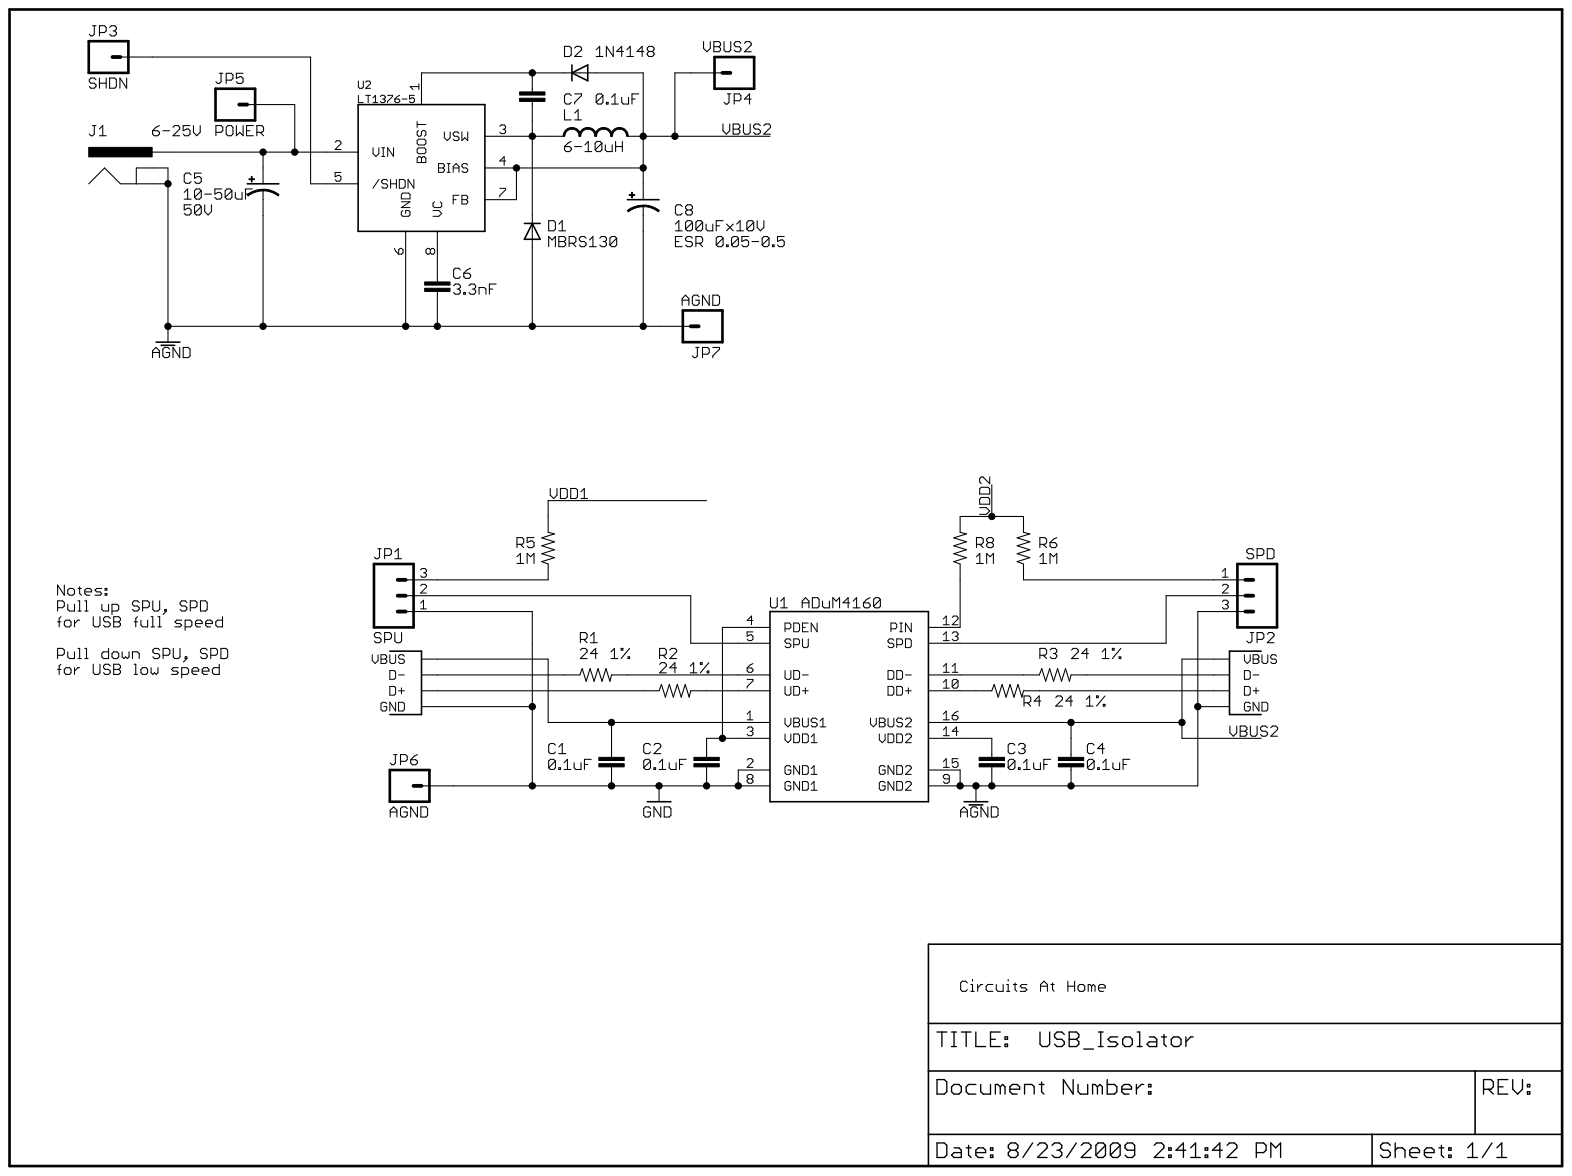
[picture p354: page 1]
