brengi/CESE-PCB/2018/Dordolo/CIAA-UNO/CIAA-UNO.kicad_pcb

## KiCad design 2018/Dordolo/CIAA-UNO/CIAA-UNO.kicad_pcb (2019-05-17)

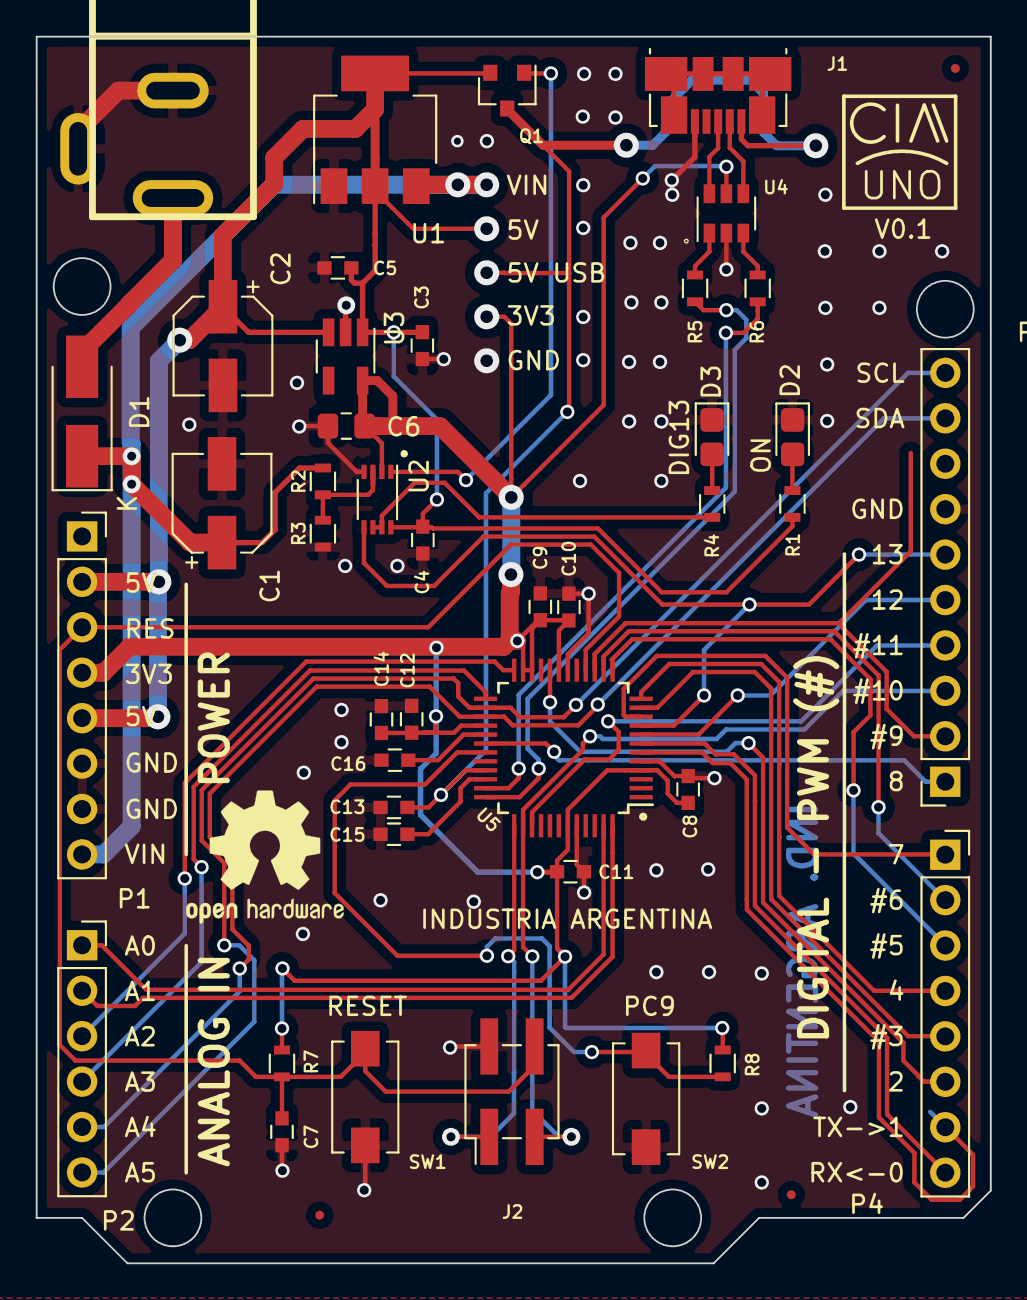
[picture p388: board CIAA-UNO.kicad_pcb from above]

Board: 2 copper layers, 53.3 x 68.6 mm, 45 parts (0 on the bottom side), 42 nets.

Parts:
C1, C2: 47uF; CP_Elec_5x5.3
C3, C4: 0.1 uF; C_0603
C5: 1uF; C_0603
C6: 2.2uF; C_0805_2012Metric_Pad1.15x1.40mm_HandSolder
C7, C15, C16: 1u; C_0603
C8, C9, C10, C11, C12: 100n; C_0603
C13: 4.7u; C_0603
C14: 10u; C_0603
CON1: BARREL_JACK; dc_socket
D1: DIODE; D_SMA_Handsoldering
D2, D3: LED; LED_0805_2012Metric_Castellated
F1, F2, F3: Fiducial; Fiducial_0.5mm_Dia_1mm_Outer
J1: USB_OTG; USB_Micro-B_Molex_47346-0001
J2: SWD; Pin_Header_Straight_2x02_Pitch2.54mm_SMD
P1: Power Header; PinSocket_1x08_P2.54mm_Vertical
P2: Analog Header; PinSocket_1x06_P2.54mm_Vertical
P3: Digital Header 02; PinSocket_1x10_P2.54mm_Vertical
P4: Digital Header 01; PinSocket_1x08_P2.54mm_Vertical
Q1: FDN340P; SOT-23
R1, R4: 510; R_0603
R2, R3: 10K; R_0603
R5, R6: 15R; R_0603
R7, R8: 1K; R_0603
SW1, SW2: reset; SW_SPST_EVQPE1
U1: LD1117S50TR; SOT-223-3_TabPin2
U2: LMV358IDGKR; VSSOP-8_2.3x2mm_P0.5mm
U3: LP2985-33DBVR; SOT-23-5_HandSoldering
U4: USBLC6-2; SOT-23-6
U5: EFM32HG-48LQFP; LQFP-48_7x7mm_Pitch0.5mm

Connections:
3V3_LDO: C6.1, C8.1, C9.1, C10.2, C11.2, C12.1, C14.1, P1.4, R7.1, R8.1, U2.2, U3.5, U4.5, U5.4, U5.19, U5.22, U5.23, U5.28, U5.43
5V_LDO: C2.1, C3.1, C4.2, C5.1, P1.2, P1.5, Q1.2, R1.2, U1.2, U2.8, U3.1, U3.3
/EFM32HG-48LQFP/328P_RESET: C7.2, J2.4, P1.3, R7.2, SW1.2, U5.16
/EFM32HG-48LQFP/ARD_AN0: P2.1, U5.47
/EFM32HG-48LQFP/ARD_AN1: P2.2, U5.48
/EFM32HG-48LQFP/ARD_AN2: P2.3, U5.24
/EFM32HG-48LQFP/ARD_AN3: P2.4, U5.25
/EFM32HG-48LQFP/ARD_AN4/SDA: P2.5, P3.9, U5.27
/EFM32HG-48LQFP/ARD_AN5/SCL: P2.6, P3.10, U5.26
/EFM32HG-48LQFP/ARD_DIG0: P4.8, U5.7
/EFM32HG-48LQFP/ARD_DIG1: P4.7, U5.6
/EFM32HG-48LQFP/ARD_DIG2: P4.6, U5.20
/EFM32HG-48LQFP/ARD_DIG3: P4.5, U5.11
/EFM32HG-48LQFP/ARD_DIG4: P4.4, U5.12
/EFM32HG-48LQFP/ARD_DIG5: P4.3, U5.13
/EFM32HG-48LQFP/ARD_DIG6: P4.2, U5.14
/EFM32HG-48LQFP/ARD_DIG7: P4.1, U5.10
/EFM32HG-48LQFP/ARD_DIG8: P3.1, U5.30
/EFM32HG-48LQFP/ARD_DIG9: P3.2, U5.15
/EFM32HG-48LQFP/ARD_DIG10/SPI_SS: J2.3, P3.3, U5.38
/EFM32HG-48LQFP/ARD_DIG11/SPI_MOSI: P3.4, U5.39
/EFM32HG-48LQFP/ARD_DIG12/SPI_MISO: P3.5, U5.8
/EFM32HG-48LQFP/ARD_DIG13/SPI_SCK: P3.6, U2.5, U5.9
/EFM32HG-48LQFP/PC9: R8.2, SW2.2, U5.31
/EFM32HG-48LQFP/PF0/SWCLK: J2.1, U5.37
/EFM32HG-48LQFP/USB_D+: R5.2, U5.36
/EFM32HG-48LQFP/USB_D-: R6.2, U5.35
/USB Interface/B_USB+: J1.3, U4.6
/USB Interface/B_USB-: J1.2, U4.4
GND: C1.2, C2.2, C3.2, C4.1, C5.2, C6.2, C7.1, C8.2, C9.2, C10.1, C11.1, C12.2, C13.2, C14.2, C15.2, C16.2, CON1.2, CON1.MP, D2.1, D3.1, J1.5, J2.2, P1.6, P1.7, P3.7, R3.1, SW1.1, SW2.1, U1.1, U2.4, U3.2, U4.2, U5.5, U5.18, U5.44
unnamed: C15.1, U5.34
unnamed: C16.1, U5.29
unnamed: CON1.1, D1.2
unnamed: D2.2, R1.1
unnamed: D3.2, R4.2
unnamed: Q1.1, U2.1
unnamed: R2.1, R3.2, U2.3
unnamed: R4.1, U2.6, U2.7
unnamed: R5.1, U4.1
unnamed: R6.1, U4.3
USBVCC: C13.1, J1.1, Q1.3, U5.33
Vin: C1.1, D1.1, P1.8, R2.2, U1.3
