brengi/CESE-PCB/2018/Yanez/wifi_ESP-01_opto_rele/wifi_ESP-01_opto_rele.kicad_pcb

## KiCad design 2018/Yanez/wifi_ESP-01_opto_rele/wifi_ESP-01_opto_rele.kicad_pcb (2019-05-17)

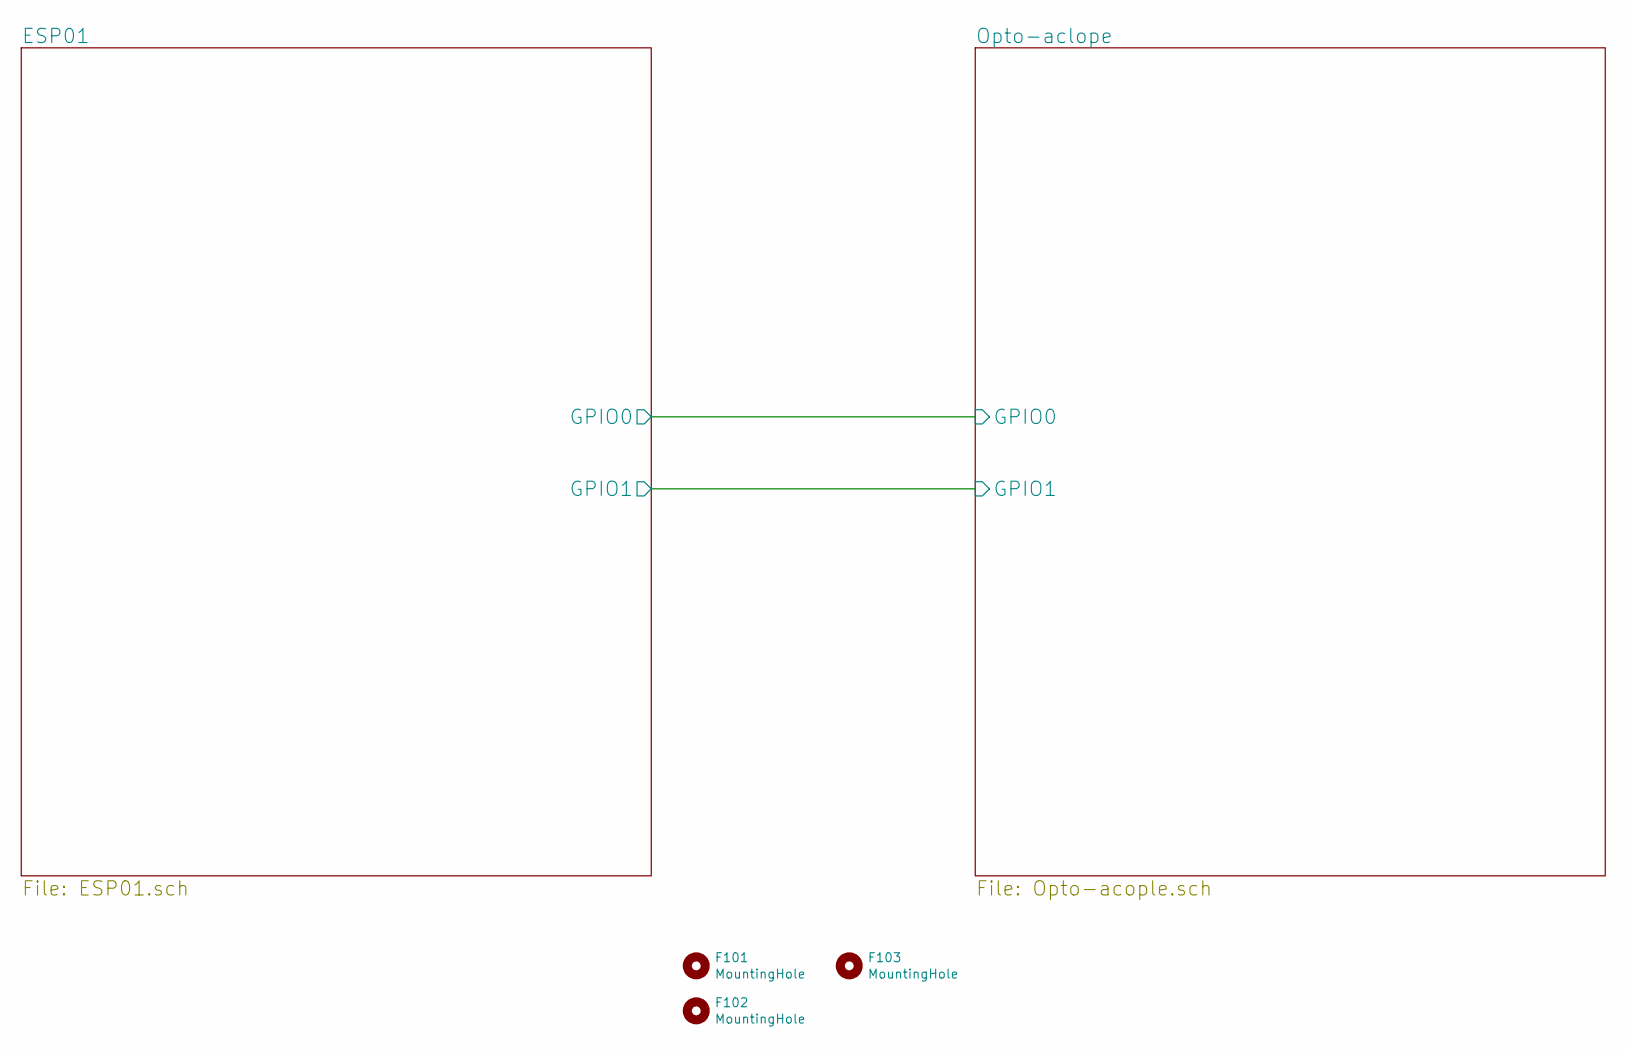
[picture p389: schematic wifi_ESP-01_opto_rele.sch, Módulo Wifi-ESP01 con relés optoacoplados]

Parts:
F101, F102, F103: MountingHole; Fiducial_1mm_Dia_2mm_Outer

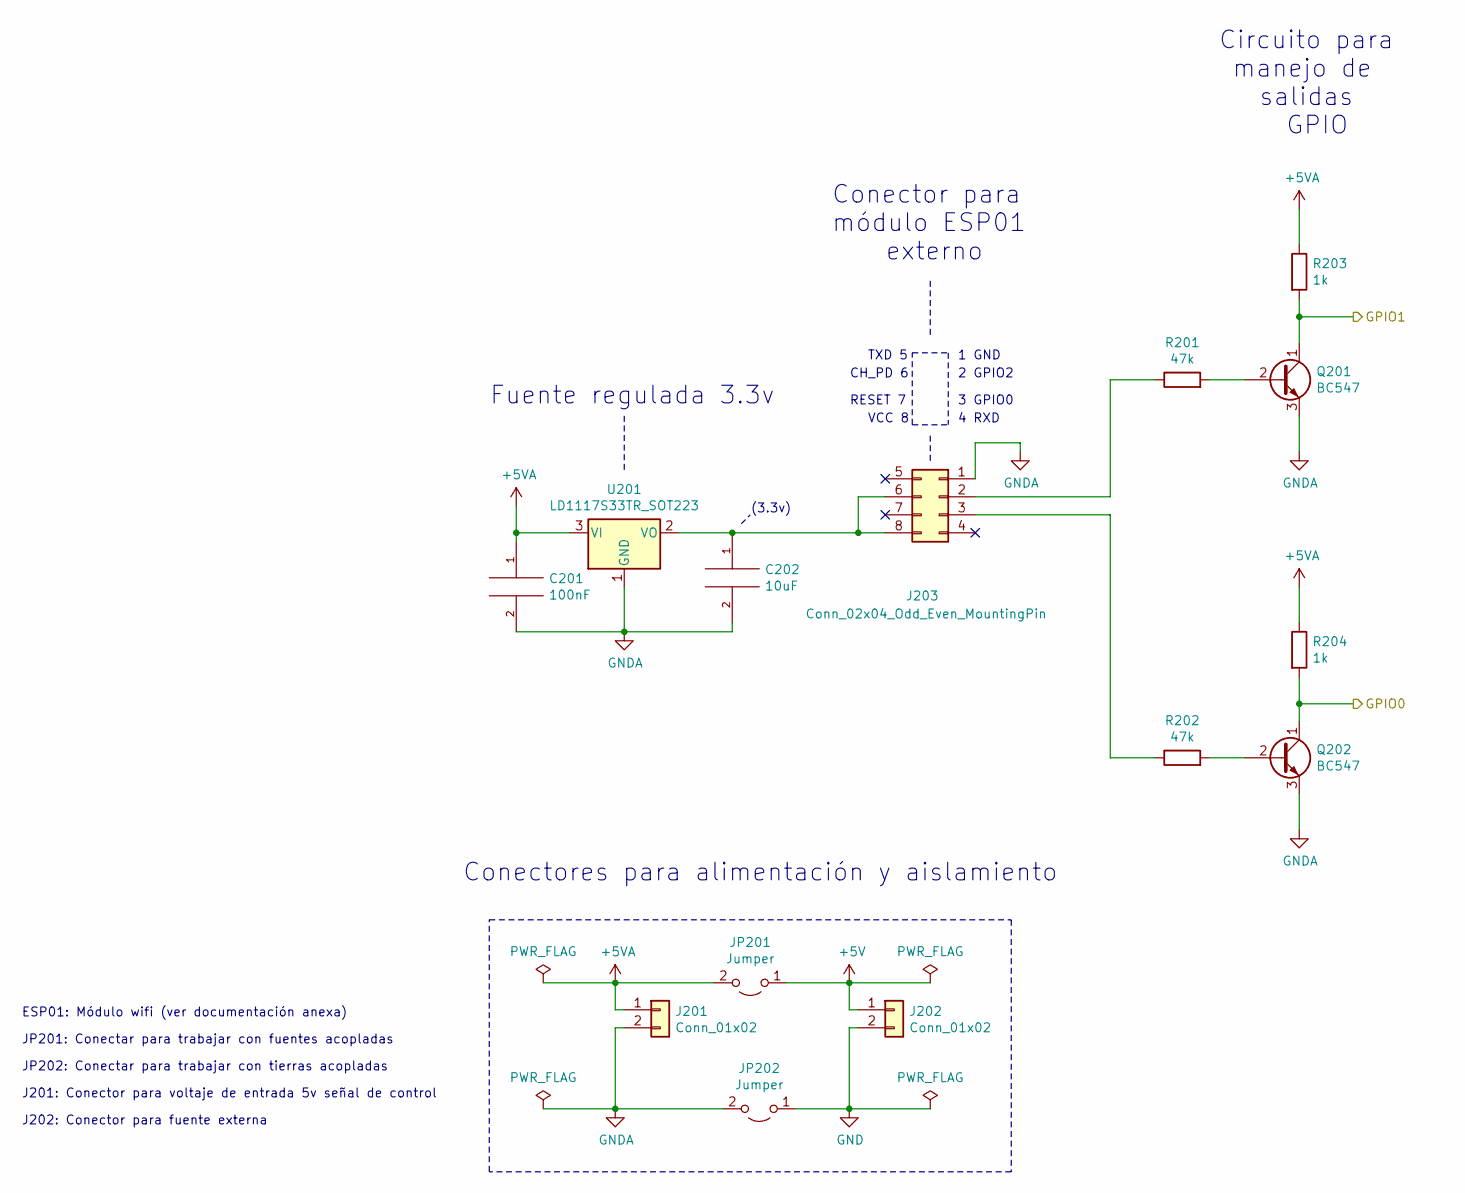
[picture p390: schematic ESP01.sch, Módulo Wifi-ESP01]

Parts:
C201: 100nF; C_0805_2012Metric_Pad1.15x1.40mm_HandSolder
C202: 10uF; C_0805_2012Metric_Pad1.15x1.40mm_HandSolder
J201, J202: Conn_01x02; TerminalBlock_bornier-2_P5.08mm
J203: Conn_02x04_Odd_Even_MountingPin; PinSocket_2x04_P2.54mm_Vertical
JP201, JP202: Jumper; PinHeader_1x02_P2.54mm_Vertical
Q201, Q202: BC547; SOT-23
R201, R202: 47k; R_0805_2012Metric_Pad1.15x1.40mm_HandSolder
R203, R204: 1k; R_0805_2012Metric_Pad1.15x1.40mm_HandSolder
U201: LD1117S33TR_SOT223; SOT-223-3_TabPin2

Connections:
+5V: J202.1, JP201.1 (A); also elsewhere on the board
+5VA: C201.1, J201.1, JP201.2 (B), R203.1, R204.1, U201.3 (VI); also elsewhere on the board
/ESP01/GPIO0: Q202.1 (C), R204.2; also elsewhere on the board
/ESP01/GPIO1: Q201.1 (C), R203.2; also elsewhere on the board
GND: J202.2, JP202.1 (A); also elsewhere on the board
GNDA: C201.2, C202.2, J201.2, J203.1, JP202.2 (B), Q201.3 (E), Q202.3 (E), U201.1 (GND)
unnamed: C202.1, J203.6, J203.8, U201.2 (VO)
unnamed: J203.2, R201.1
unnamed: J203.3, R202.1
unnamed: Q201.2 (B), R201.2
unnamed: Q202.2 (B), R202.2

Notes on the sheet:
Conectores para alimentación y aislamiento
Fuente regulada 3.3v
Conector para módulo ESP01 externo
Circuito para manejo de salidas GPIO
(3.3v)
ESP01: Módulo wifi (ver documentación anexa)
JP201: Conectar para trabajar con fuentes acopladas
JP202: Conectar para trabajar con tierras acopladas
J201: Conector para voltaje de entrada 5v señal de control
J202: Conector para fuente externa
1 GND
2 GPIO2
3 GPIO0
4 RXD
TXD 5
CH_PD 6
RESET 7
VCC 8

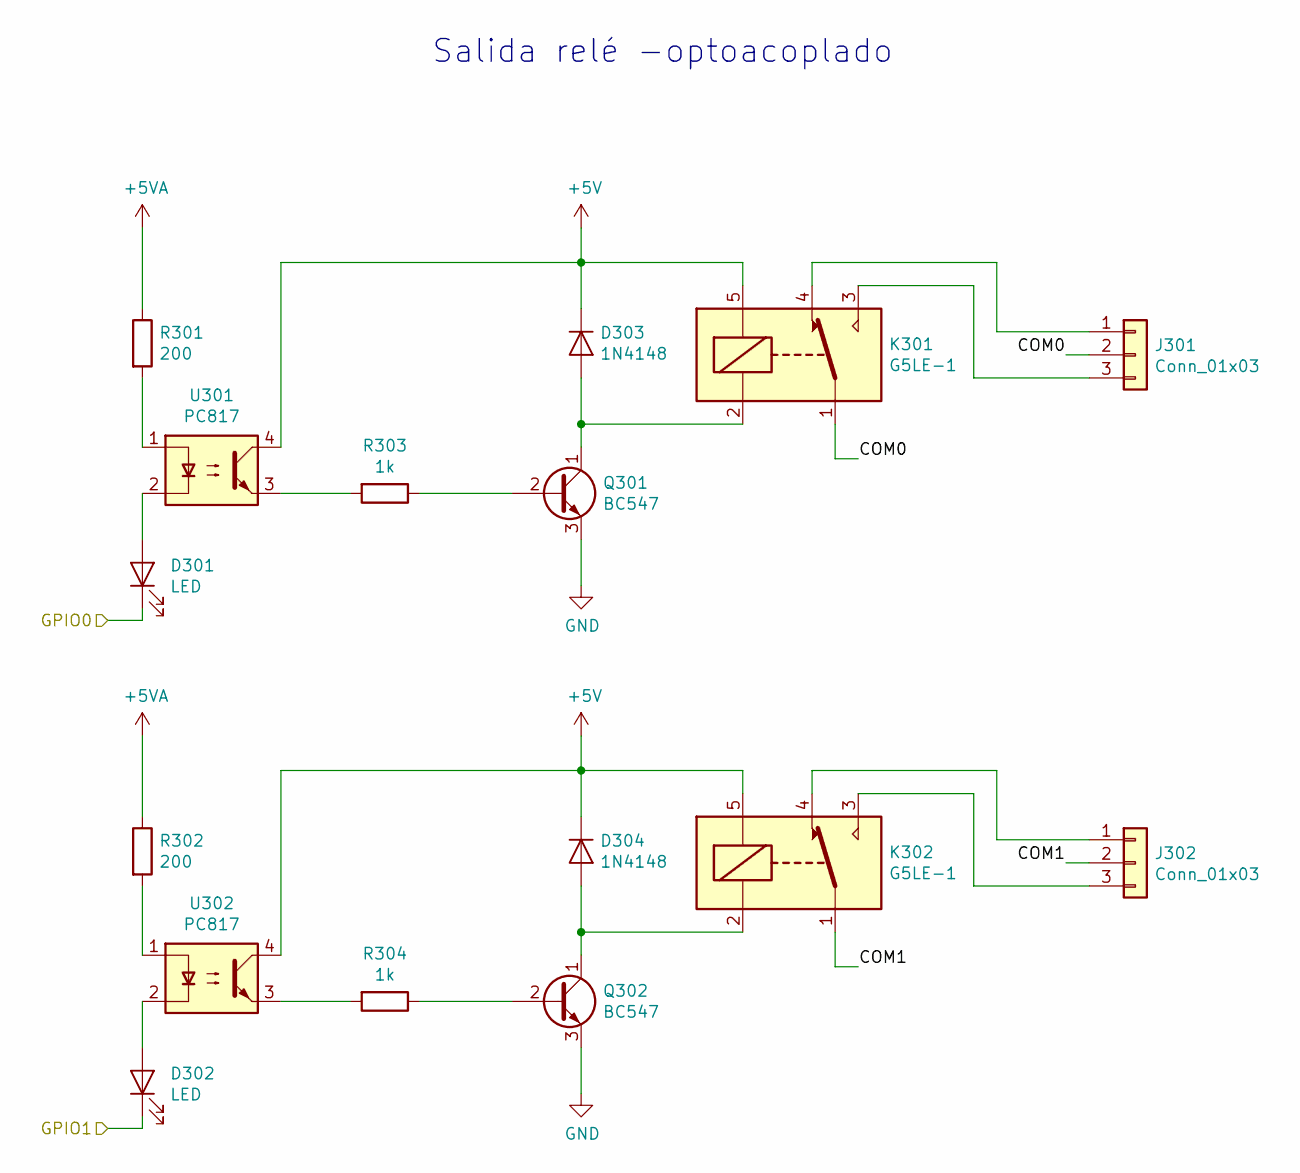
[picture p391: schematic Opto-acople.sch, Módulo relés optoacoplados]

Parts:
D301, D302: LED; LED_0805_2012Metric_Pad1.15x1.40mm_HandSolder
D303, D304: 1N4148; D_0805_2012Metric_Pad1.15x1.40mm_HandSolder
J301, J302: Conn_01x03; TerminalBlock_bornier-3_P5.08mm
K301, K302: G5LE-1; Relay_SPDT_Omron-G5LE-1
Q301, Q302: BC547; SOT-23
R301, R302: 200; R_0805_2012Metric_Pad1.15x1.40mm_HandSolder
R303, R304: 1k; R_0805_2012Metric_Pad1.15x1.40mm_HandSolder
U301, U302: PC817; DIP-4_W7.62mm

Connections:
+5V: D303.1 (K), D304.1 (K), K301.5, K302.5, U301.4, U302.4; also elsewhere on the board
+5VA: R301.1, R302.1; also elsewhere on the board
/ESP01/GPIO0: D301.1 (K); also elsewhere on the board
/ESP01/GPIO1: D302.1 (K); also elsewhere on the board
/Opto-aclope/COM0: J301.2, K301.1
/Opto-aclope/COM1: J302.2, K302.1
GND: Q301.3 (E), Q302.3 (E); also elsewhere on the board
unnamed: D301.2 (A), U301.2
unnamed: D302.2 (A), U302.2
unnamed: D303.2 (A), K301.2, Q301.1 (C)
unnamed: D304.2 (A), K302.2, Q302.1 (C)
unnamed: J301.1, K301.4
unnamed: J301.3, K301.3
unnamed: J302.1, K302.4
unnamed: J302.3, K302.3
unnamed: Q301.2 (B), R303.1
unnamed: Q302.2 (B), R304.1
unnamed: R301.2, U301.1
unnamed: R302.2, U302.1
unnamed: R303.2, U301.3
unnamed: R304.2, U302.3

Notes on the sheet:
Salida relé -optoacoplado

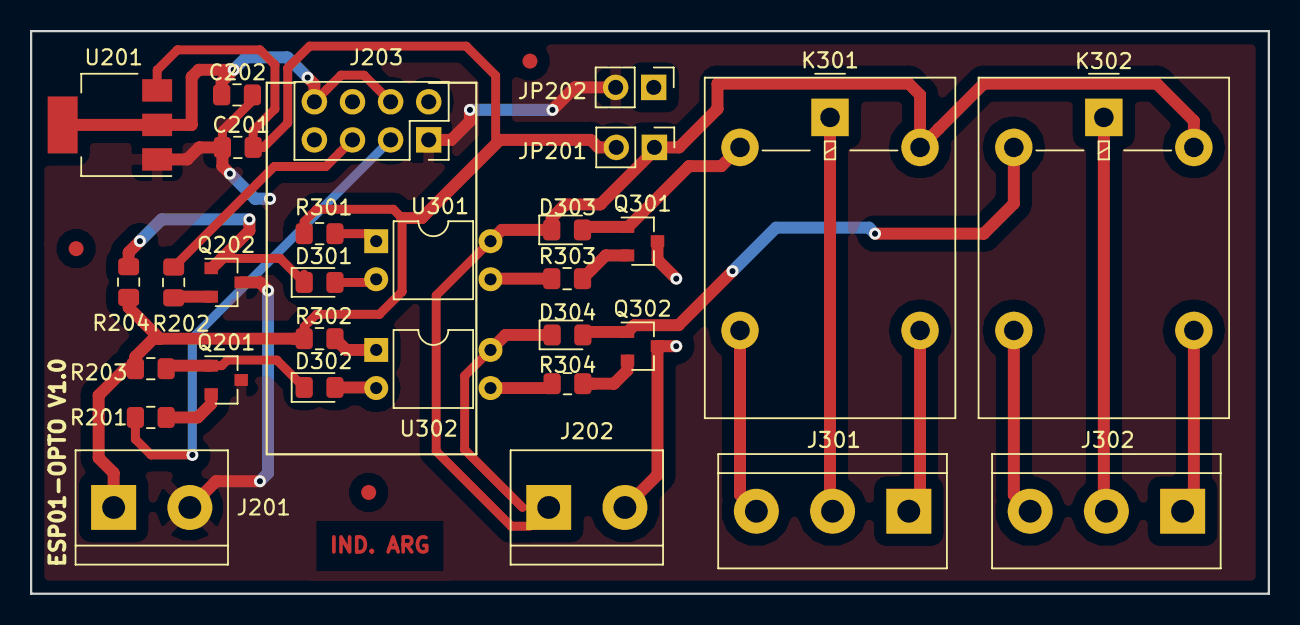
[picture p392: board wifi_ESP-01_opto_rele.kicad_pcb from above]

Board: 2 copper layers, 82.5 x 37.5 mm, 33 parts (0 on the bottom side), 27 nets.
