brengi/CESE-PCB/2018/Ericson/PCB_TP_Final/PCB_TP_Final.kicad_pcb

## KiCad design 2018/Ericson/PCB_TP_Final/PCB_TP_Final.kicad_pcb (2019-05-17)

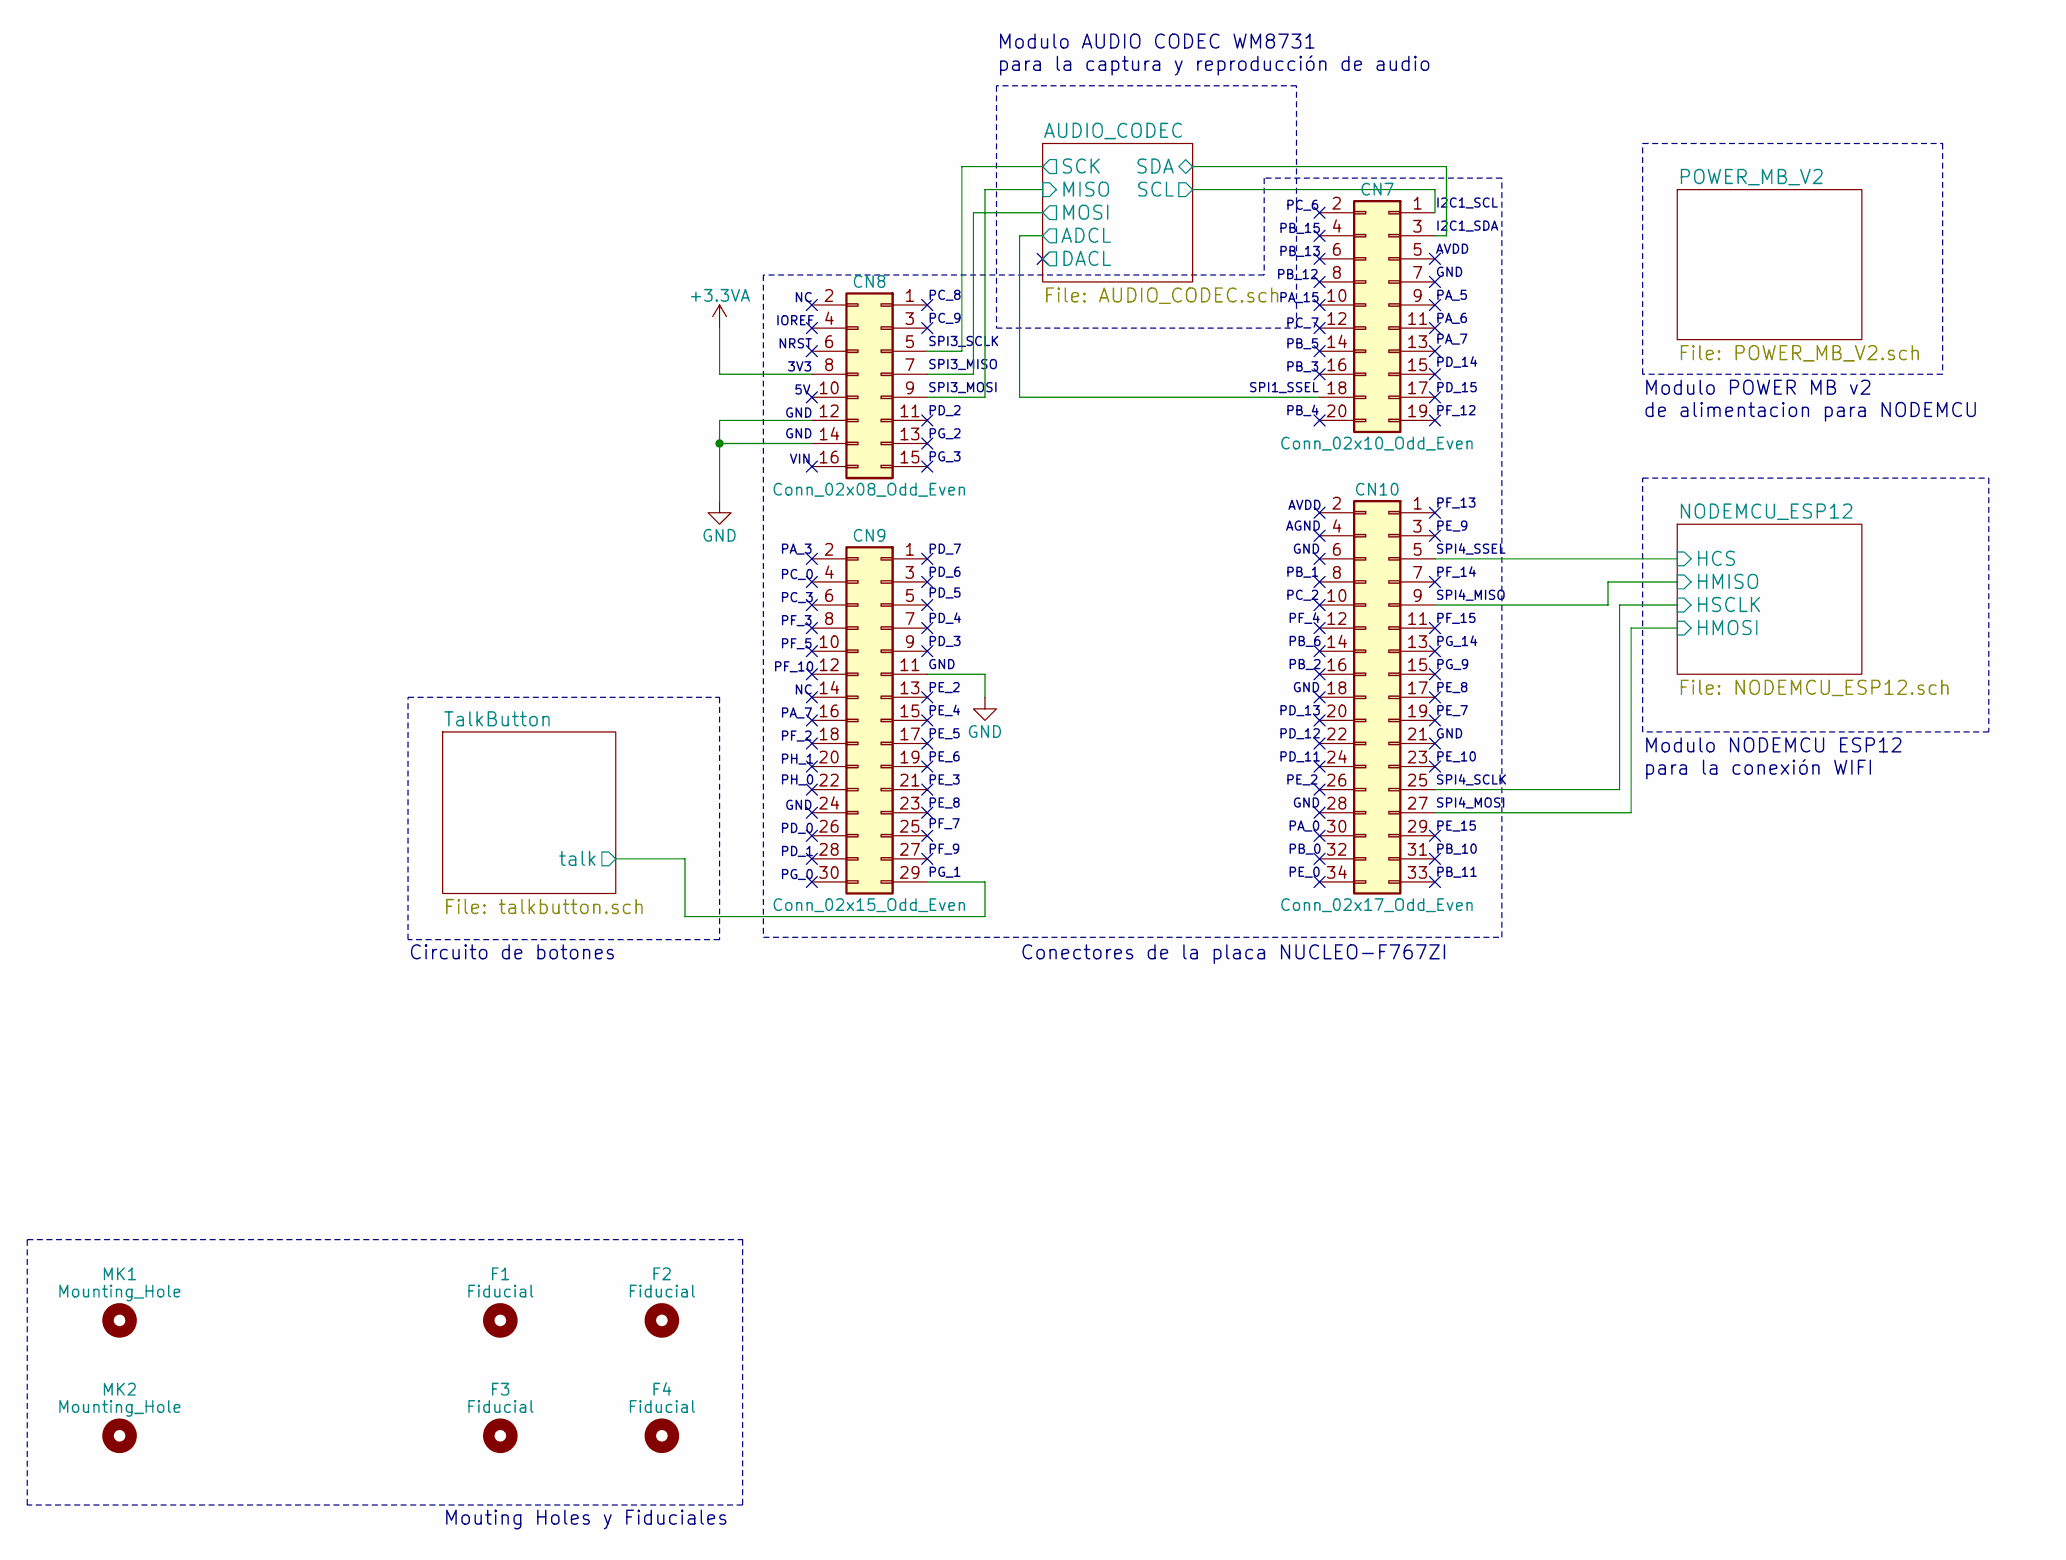
[picture p393: schematic PCB_TP_Final.sch, SHIELD VoIP para NUCLEO F767]

Parts:
CN7: Conn_02x10_Odd_Even; Pin_Header_Straight_2x10_Pitch2.54mm
CN8: Conn_02x08_Odd_Even; Pin_Header_Straight_2x08_Pitch2.54mm
CN9: Conn_02x15_Odd_Even; Pin_Header_Straight_2x15_Pitch2.54mm
CN10: Conn_02x17_Odd_Even; Pin_Header_Straight_2x17_Pitch2.54mm
F1, F2: Fiducial; Fiducial_1mm_Dia_2.54mm_Outer_CopperBottom
F3, F4: Fiducial; Fiducial_1mm_Dia_2.54mm_Outer_CopperTop
MK1, MK2: Mounting_Hole; MountingHole_3.7mm

Connections:
+3.3VA: CN8.8; also elsewhere on the board
/AUDIO_CODEC/ADCL: CN7.18; also elsewhere on the board
/AUDIO_CODEC/MISO: CN8.9; also elsewhere on the board
/AUDIO_CODEC/MOSI: CN8.7; also elsewhere on the board
/AUDIO_CODEC/SCK: CN8.5; also elsewhere on the board
/AUDIO_CODEC/SCL: CN7.1; also elsewhere on the board
/AUDIO_CODEC/SDA: CN7.3; also elsewhere on the board
/NODEMCU_ESP12/HCS: CN10.5; also elsewhere on the board
/NODEMCU_ESP12/HMISO: CN10.9; also elsewhere on the board
/NODEMCU_ESP12/HMOSI: CN10.27; also elsewhere on the board
/NODEMCU_ESP12/HSCLK: CN10.25; also elsewhere on the board
/TalkButton/talk: CN9.29; also elsewhere on the board
GND: CN8.12, CN8.14, CN9.11; also elsewhere on the board

Notes on the sheet:
Conectores de la placa NUCLEO-F767ZI
Mouting Holes y Fiduciales
Modulo NODEMCU ESP12 para la conexión WIFI
Modulo POWER MB v2 de alimentacion para NODEMCU
Circuito de botones
Modulo AUDIO CODEC WM8731 para la captura y reproducción de audio
IOREF
NRST
3V3
GND
VIN
PC_8
PC_9
SPI3_SCLK
SPI3_MISO
SPI3_MOSI
PD_2
PG_2
PG_3
PA_3
PC_0
PC_3
PF_3
PF_5
PF_10
PA_7
PF_2
PH_1
PH_0
PD_0
PD_1
PG_0
PD_7
PD_6
PD_5
PD_4
PD_3
PE_2
PE_4
PE_5
PE_6
PE_3
PE_8
PF_7
PF_9
PG_1
PC_6
PB_15
PB_13
PB_12
PA_15
PC_7
PB_5
PB_3
SPI1_SSEL
PB_4
I2C1_SCL
I2C1_SDA
AVDD
PA_5
PA_6
PD_14
PD_15
PF_12
AGND
PB_1
PC_2
PF_4
PB_6
PB_2
PD_13
PD_12
PD_11
PA_0
PB_0
PE_0
PF_13
PE_9
SPI4_SSEL
PF_14
SPI4_MISO
PF_15
PG_14
PG_9
PB_11
PB_10
PE_15
SPI4_MOSI
SPI4_SCLK
PE_7
PE_10

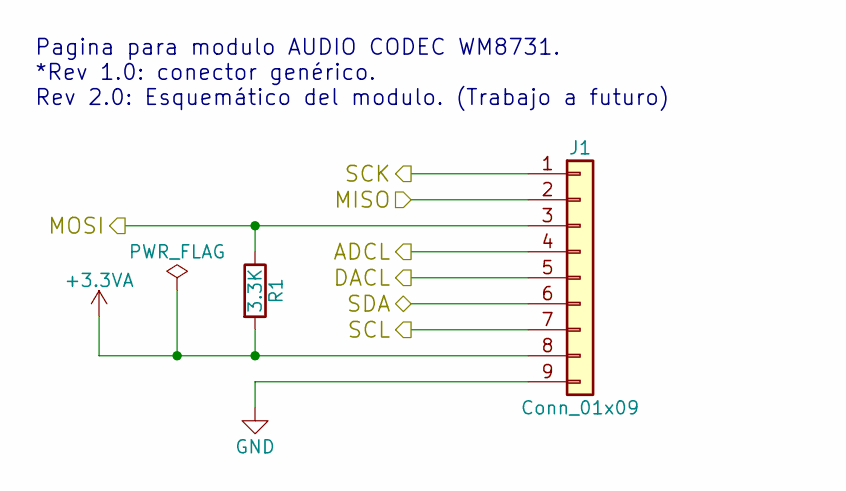
[picture p394: schematic AUDIO_CODEC.sch, Audio Codec WM8731]

Parts:
J1: Conn_01x09; Audio_Codec_WM8731
R1: 3.3K; R_1206_HandSoldering

Connections:
+3.3VA: J1.8, R1.2; also elsewhere on the board
/AUDIO_CODEC/ADCL: J1.4; also elsewhere on the board
/AUDIO_CODEC/DACL: J1.5
/AUDIO_CODEC/MISO: J1.2; also elsewhere on the board
/AUDIO_CODEC/MOSI: J1.3, R1.1; also elsewhere on the board
/AUDIO_CODEC/SCK: J1.1; also elsewhere on the board
/AUDIO_CODEC/SCL: J1.7; also elsewhere on the board
/AUDIO_CODEC/SDA: J1.6; also elsewhere on the board
GND: J1.9; also elsewhere on the board

Notes on the sheet:
Pagina para modulo AUDIO CODEC WM8731. *Rev 1.0: conector genérico. Rev 2.0: Esquemático del modulo. (Trabajo a futuro)

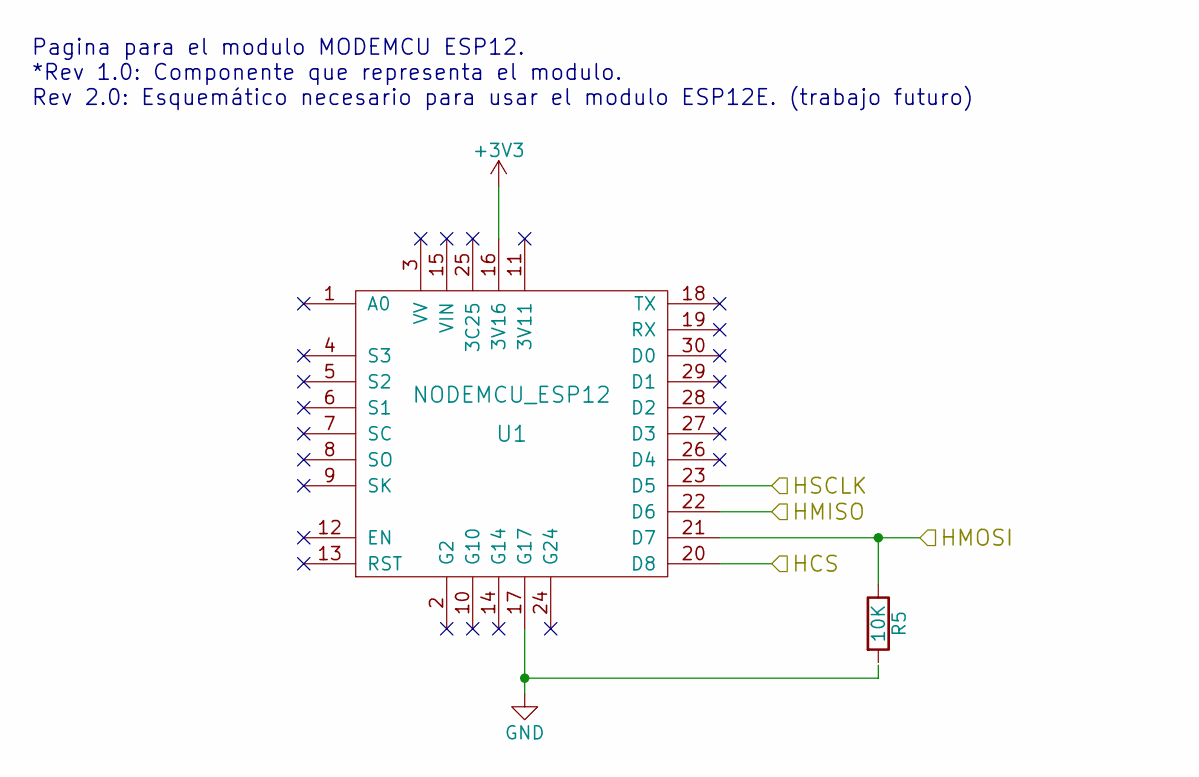
[picture p395: schematic NODEMCU_ESP12.sch, NodeMCU ESP12]

Parts:
R5: 10K; R_1206_HandSoldering
U1: NODEMCU_ESP12

Connections:
+3V3: U1.16 (3V16); also elsewhere on the board
/NODEMCU_ESP12/HCS: U1.20 (D8); also elsewhere on the board
/NODEMCU_ESP12/HMISO: U1.22 (D6); also elsewhere on the board
/NODEMCU_ESP12/HMOSI: R5.1, U1.21 (D7); also elsewhere on the board
/NODEMCU_ESP12/HSCLK: U1.23 (D5); also elsewhere on the board
GND: R5.2, U1.17 (G17); also elsewhere on the board

Notes on the sheet:
Pagina para el modulo MODEMCU ESP12. *Rev 1.0: Componente que representa el modulo. Rev 2.0: Esquemático necesario para usar el modulo ESP12E. (trabajo futuro)

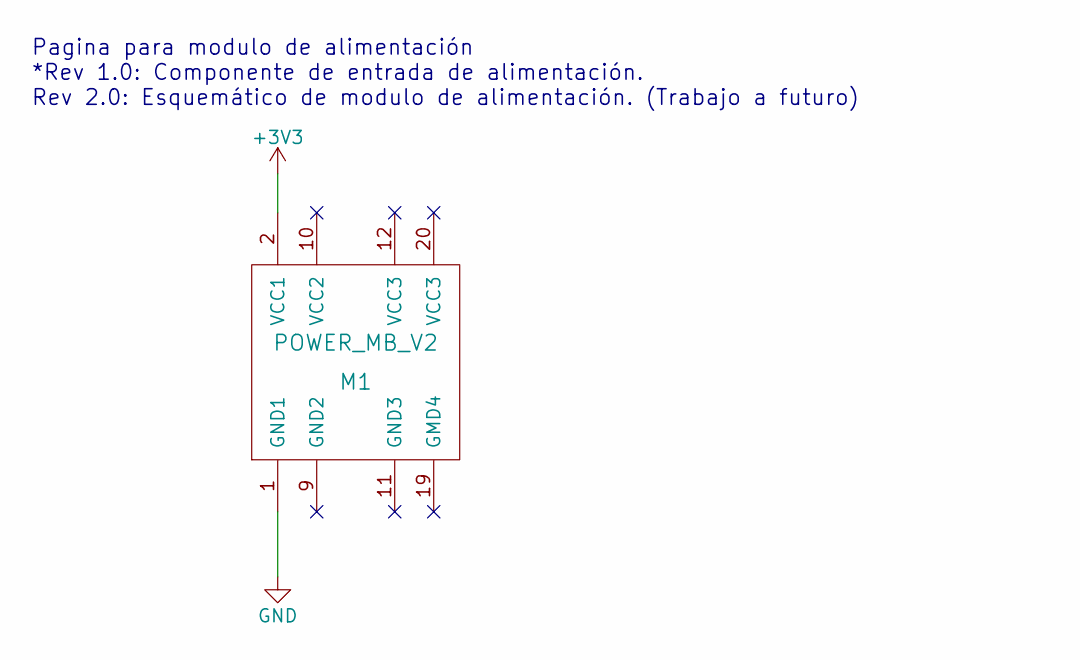
[picture p396: schematic POWER_MB_V2.sch, Power MB v2]

Parts:
M1: POWER_MB_V2

Connections:
+3V3: M1.2 (VCC1); also elsewhere on the board
GND: M1.1 (GND1); also elsewhere on the board

Notes on the sheet:
Pagina para modulo de alimentación *Rev 1.0: Componente de entrada de alimentación. Rev 2.0: Esquemático de modulo de alimentación. (Trabajo a futuro)

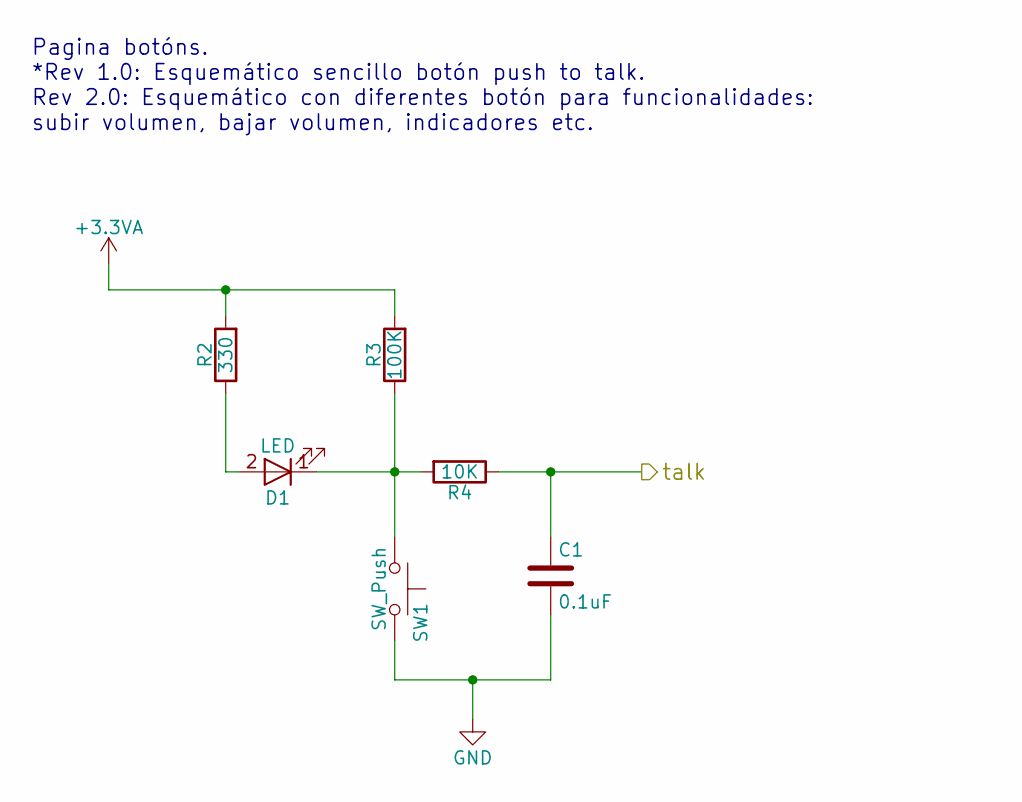
[picture p397: schematic talkbutton.sch, Circuit Push to Talk]

Parts:
C1: 0.1uF; C_0805_HandSoldering
D1: LED; LED_0805_HandSoldering
R2: 330; R_1206_HandSoldering
R3: 100K; R_1206_HandSoldering
R4: 10K; R_1206_HandSoldering
SW1: SW_Push; SW_PUSH_6mm_h8mm

Connections:
+3.3VA: R2.2, R3.2; also elsewhere on the board
/TalkButton/talk: C1.1, R4.1; also elsewhere on the board
GND: C1.2, SW1.2; also elsewhere on the board
unnamed: D1.1 (K), R3.1, R4.2, SW1.1
unnamed: D1.2 (A), R2.1

Notes on the sheet:
Pagina botóns. *Rev 1.0: Esquemático sencillo botón push to talk. Rev 2.0: Esquemático con diferentes botón para funcionalidades: subir volumen, bajar volumen, indicadores etc.

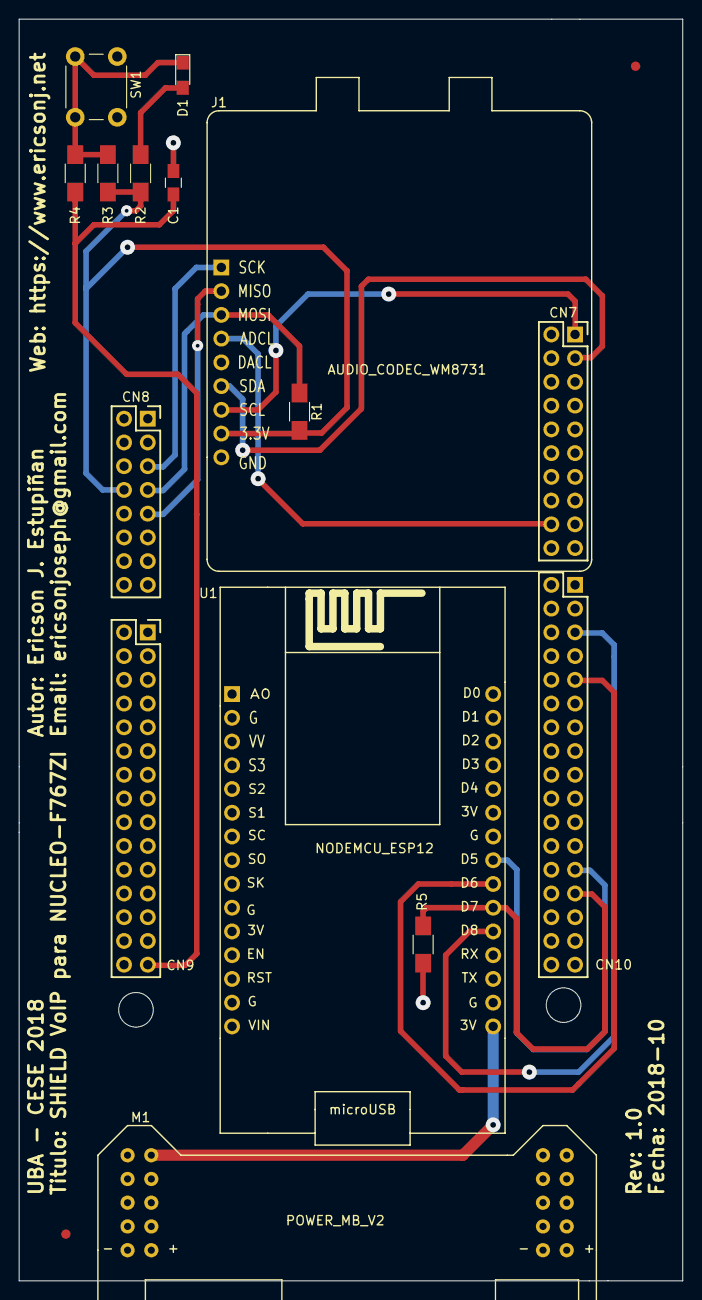
[picture p398: board PCB_TP_Final.kicad_pcb from above]

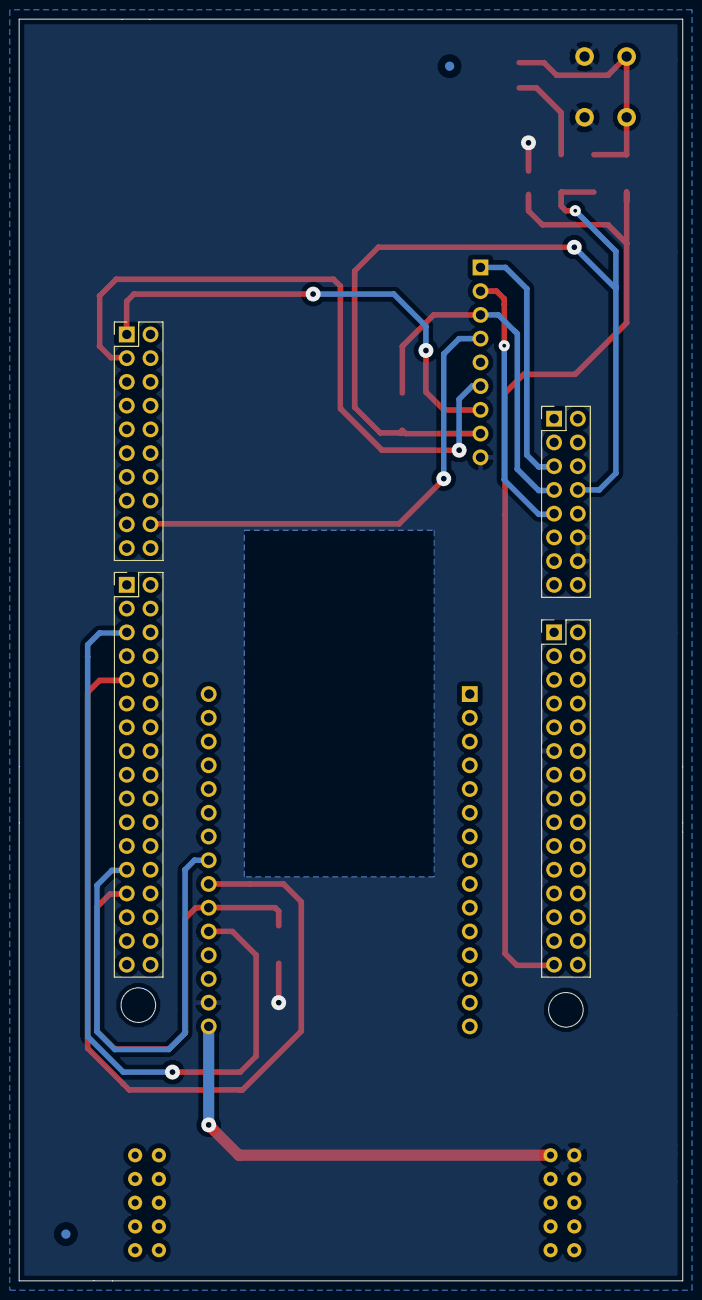
[picture p399: board PCB_TP_Final.kicad_pcb from below]

Board: 2 copper layers, 71.0 x 135.0 mm, 21 parts (4 on the bottom side), 16 nets.
