brengi/CESE-PCB/2018/Lavigna/PRACTICA02/LAVIGNA_GONZALO/LAVIGNA_GONZALO.kicad_pcb

## KiCad design 2018/Lavigna/PRACTICA02/LAVIGNA_GONZALO/LAVIGNA_GONZALO.kicad_pcb (2019-05-17)

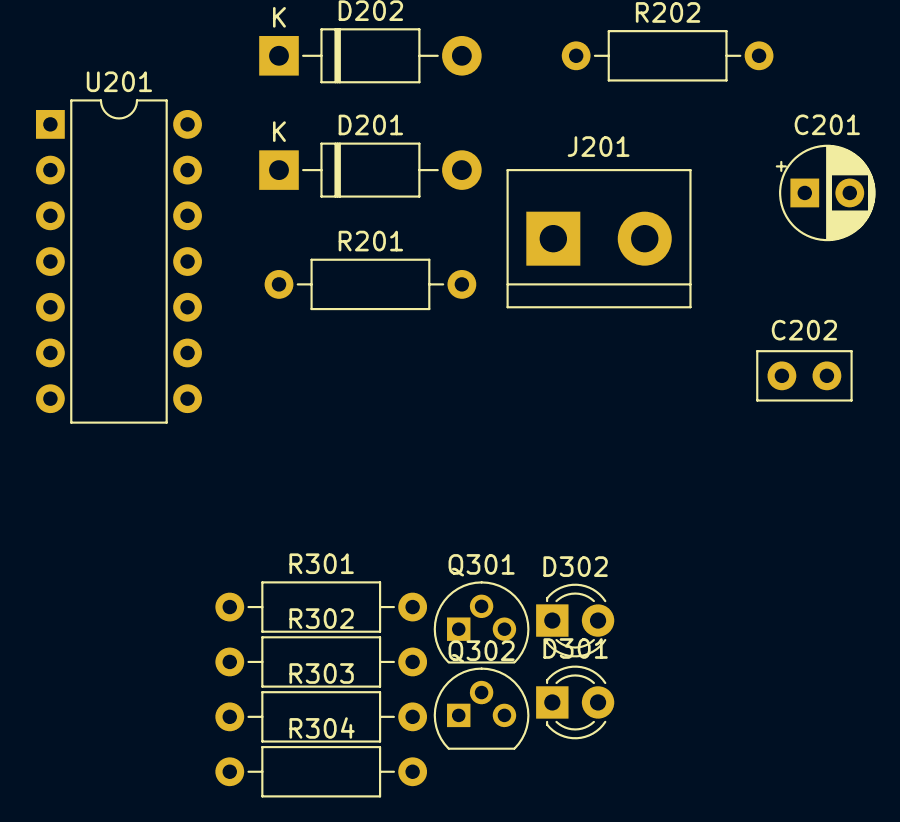
[picture p400: board 2018/Lavigna/PRACTICA02/LAVIGNA_GONZALO/LAVIGNA_GONZALO.kicad_pcb from above]

Board: 2 copper layers, 20 parts (0 on the bottom side), 14 nets, no tracks yet.

Parts:
C201: CP; CP_Radial_D5.0mm_P2.50mm
C202: 0.1u; C_Disc_D5.0mm_W2.5mm_P2.50mm
D201, D202: 1N4148; D_DO-41_SOD81_P10.16mm_Horizontal
D301, D302: LED ROJO; LED_D3.0mm
J201: Conn_01x02; TerminalBlock_bornier-2_P5.08mm
MH101, MH102, MH103, MH104: MountingHole; MountingHole_3.2mm_M3
Q301, Q302: BC546; TO-92
R201, R202: 100K; R_Axial_DIN0207_L6.3mm_D2.5mm_P10.16mm_Horizontal
R301, R303: 2K2; R_Axial_DIN0207_L6.3mm_D2.5mm_P10.16mm_Horizontal
R302, R304: 470R; R_Axial_DIN0207_L6.3mm_D2.5mm_P10.16mm_Horizontal
U201: 40106; DIP-14_W7.62mm

Connections:
+5V: C202.1, J201.2, R302.2, R304.2, U201.14
/Circuito con leds/LED1: R301.2, U201.4, U201.5
/Circuito con leds/LED2: R303.2, U201.6
GND: C201.2, C202.2, J201.1, Q301.3, Q302.3, U201.7
unnamed: C201.1, R201.2, R202.2, U201.1
unnamed: D201.1, R201.1
unnamed: D201.2, D202.1, U201.2, U201.3
unnamed: D202.2, R202.1
unnamed: D301.1, Q301.1
unnamed: D301.2, R302.1
unnamed: D302.1, Q302.1
unnamed: D302.2, R304.1
unnamed: Q301.2, R301.1
unnamed: Q302.2, R303.1
