brengi/CESE-PCB/2018/Lavigna/PRACTICA_FINAL/PROJECTO_KICAD/FINAL/FINAL.kicad_pcb

## KiCad design 2018/Lavigna/PRACTICA_FINAL/PROJECTO_KICAD/FINAL/FINAL.kicad_pcb (2019-05-17)

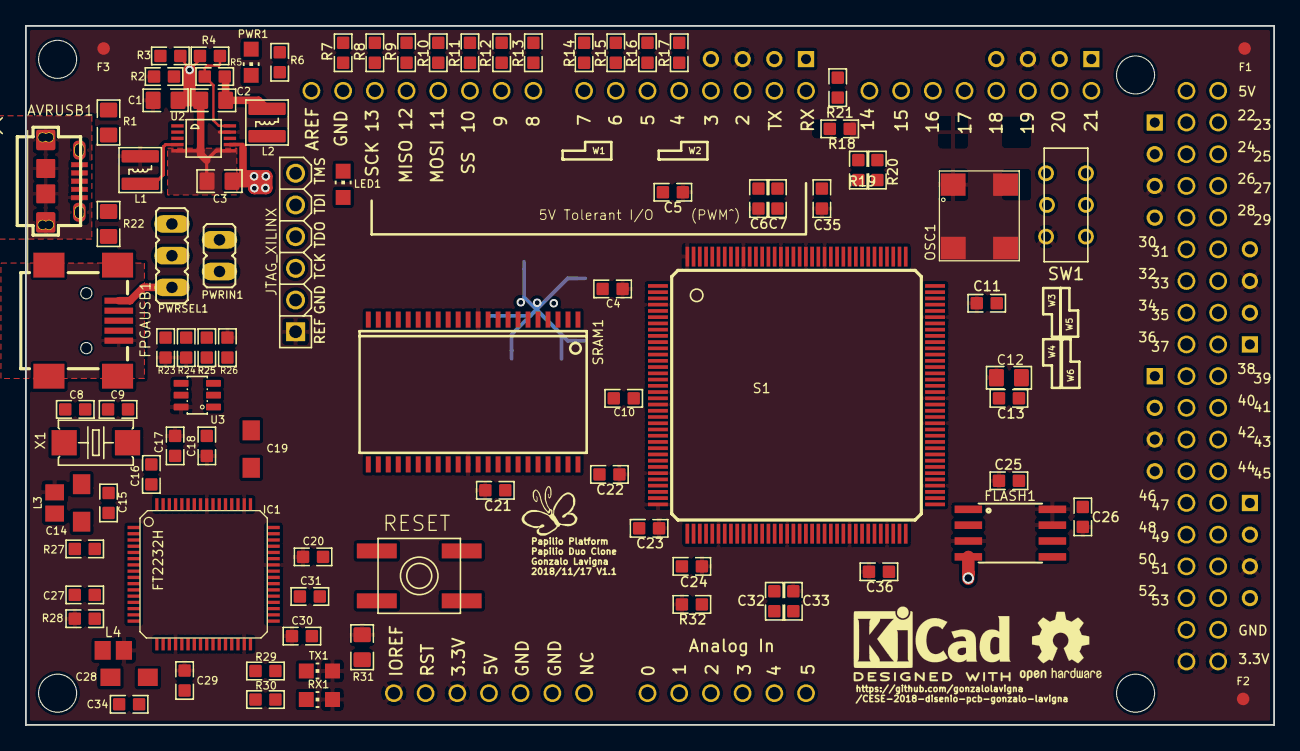
[picture p401: board FINAL.kicad_pcb from above]

Board: 4 copper layers, 100.0 x 56.0 mm, 120 parts (0 on the bottom side), 160 nets.

Parts:
AVRUSB1: MYCON2_USB-MINI-B; CON2_USB_MICRO_B_AT
C1, C2: 22u/6V3; 0805
C3: 10uF/10V; 0805
C4, C5, C6, C7, C10, C11, C13, C15, C16, C17, C18, C20, C21, C22, C23, C24, C25, C26, C27, C29, C30, C31, C32, C33, C34, C35, C36: 0.1uF; 0603
C8, C9: 27pF; 0603
C12: 0.1uF; 0805
C14, C28: 4.7uF; SMC_A
C19: 3.3uF; SMC_A
C101, C102, C105: 100nF; 0603
C103, C104: 1uF; 0603
C106, C107: 22pF; 0603
F1, F2, F3: Fiducial; Fiducial_1mm_Dia_2mm_Outer
FLASH1: FLASH-SPI-25XXSMD1; SO08-EIAJ
FPGAUSB1: CONN_USB; CONN_USB_MINI-B
IC1: FT2232H; LQFP64
L1, L2: 3.3uH; VLS3015
L3, L4: FERRITE_BEAD603; FB603
L100: MH2029-300Y; 0805
LED1: Yellow; CHIP-LED0805
LOGO1: Logo_Open_Hardware_Small; OSHW-Logo2_7.3x6mm_SilkScreen
LOGO2: logo_glavigna; KiCad-Logo2_6mm_SilkScreen
OSC1: 32MHz; OSC1
PWR1: Green; CHIP-LED0805
PWRIN1: JP1E; JP1
PWRSEL1: JP2E; JP2
R1, R22: 22R; 0805
R2: 6K8 1%; 0603
R3, R4, R5: 1K5 1%; 0603
R6: 1K8; 0603
R7, R32: 4.7K; 0603
R8, R9, R10, R11, R12, R13, R14, R15, R16, R17, R18, R19, R20, R21: 390; 0603
R23, R24, R26, R28, R110: 10K; 0603
R25: 2.2K; 0603
R27: 12K 1%; 0603
R29, R30: 1K; 0603
R31: 47K; 0805
R109: 1M; 0603
RESET: EVQQ2; EVQ-Q2
RX1: LEDCHIP-LED0805; CHIP-LED0805
S1: 6SLX9TQG144; TQ144
SRAM1: ISSI_SRAM_8BIT; TSOP44-II
SW1: SWITCH-2CH-6P-3010010P1; 6P-2CH-2.54-9.1X3.5X3.2+2H
TX1: LEDCHIP-LED0805; CHIP-LED0805
U1: ARDUINO_MEGA_SHIELD
U2: LTC3419MS; MSOP10
U3: 93C56B; SOT23-6
U101: ATMEGA32U4-XUMU; QFN44ML7X7
U$1: JTAG_XILINX; JTAG
U$3, U$3#2, U$3#3, U$3#4: STAND-OFF-TIGHT
U$7: GADGETFACTORY_LOGO
WING_POWER1, WING_POWER2, WING_POWER3, WING_POWER4, WING_POWER5, WING_POWER6: FRAME-A4L-LOC; POWER_NO_TEXT
X1: 12MHz; 4X6
Y1: 16Mhz KX-7; CRYSTAL-3.2-2.5

Connections:
+1V2: C2.1, C7.1, C10.1, C13.1, C32.1, L2.2, R5.2, S1.19, S1.28, S1.52, S1.89, S1.128
+1V8: C16.1, C19.+, C27.1, C31.1, IC1.12, IC1.37, IC1.49, IC1.64
+3V3: C1.1, C4.1, C5.1, C6.1, C11.1, C12.1, C17.1, C18.1, C20.1, C21.1, C22.1, C23.1, C24.1, C25.1, C26.1, C29.1, C30.1, C33.1, C35.1, C36.1, C101.2, C105.2, FLASH1.3, FLASH1.7, FLASH1.8, IC1.20, IC1.31, IC1.42, IC1.50, IC1.56, L1.2, L3.2, L4.2, L100.2, OSC1.1@1, OSC1.4@4, R2.2, R23.1, R24.1, R26.1, R28.1, R31.2, R32.1, R110.2, RX1.A, S1.4, S1.18, S1.20, S1.31, S1.36, S1.42, S1.53, S1.63, S1.69, S1.76, S1.86, S1.90, S1.103, S1.122, S1.125, S1.129, S1.135, S1.144, SRAM1.11, SRAM1.33, SW1.CH2A, TX1.A, U1.3.3V, U1.3V3@1, U1.3V3@2, U1.IOREF, U2.9, U3.6, U101.2, U101.14, U101.34, U$1.JTAG_REF, WING_POWER1.P3, WING_POWER2.P3, WING_POWER3.P3, WING_POWER4.P3, WING_POWER5.P3, WING_POWER6.P3
+5V: C3.1, PWRIN1.1, PWRSEL1.2, R6.1, U1.5V@0, U1.5V@1, U1.5V@2, U2.2, U2.3, U2.7, WING_POWER1.P4, WING_POWER2.P4, WING_POWER3.P4, WING_POWER4.P4, WING_POWER5.P4, WING_POWER6.P4
/Arduino/5V_ARDUINO: AVRUSB1.P1, PWRSEL1.3, U101.7
/Arduino/ARD_RESET: R110.1, S1.139, U1.RES, U101.13
/Arduino/AREF: C102.1, U1.AREF, U101.42
/Arduino/ATMEGA_A0: U1.A0, U101.41
/Arduino/ATMEGA_A1: U1.A1, U101.40
/Arduino/ATMEGA_IO13*: R7.2, U101.9
/Arduino/AVCC: C104.1, L100.1, U101.24, U101.44
/Arduino/AVRUSB_N: R1.1, U101.3
/Arduino/AVRUSB_P: R22.1, U101.4
/Arduino/D+: AVRUSB1.P3, R22.2
/Arduino/D-: AVRUSB1.P2, R1.2
/Arduino/MEGA_D14: S1.115, U1.D14, U101.30
/Arduino/MEGA_D15: S1.114, U1.D15, U101.31
/Arduino/MEGA_D16: S1.112, U1.D16, U101.32
/Arduino/MEGA_D28/A5: S1.88, U1.A5, U1.D28, U101.36
/Arduino/MEGA_D30/A4: S1.85, U1.A4, U1.D30, U101.37
/Arduino/MEGA_D32/A3: S1.83, U1.A3, U1.D32, U101.38
/Arduino/MEGA_D34/A2: S1.81, U1.A2, U1.D34, U101.39
/Arduino/UCAP: C103.1, U101.6
/Arduino/XTAL1: C107.2, R109.1, U101.17, Y1.1
/Arduino/XTAL2: C106.2, R109.2, U101.16, Y1.3
/FPGA/AD0-JTAG_TCK: IC1.16, S1.109, U$1.JTAG_TCK
/FPGA/AD1-JTAG_TDI: IC1.17, S1.110, U$1.JTAG_TDI
/FPGA/AD2-JTAG_TDO: IC1.18, S1.106, U$1.JTAG_TDO
/FPGA/AD3-JTAG_TMS: IC1.19, S1.107, U$1.JTAG_TMS
/FPGA/AD4-DTR: IC1.21, S1.45
/FPGA/BD0_TXD/MPSSE_TCK: IC1.38, S1.46
/FPGA/BD1_RXD/MPSSE_TDI: IC1.39, S1.141
/FPGA/BD2_MPSSE_TDO: IC1.40, S1.140
/FPGA/BD3_MPSSE_TMS: IC1.41, S1.138
/FPGA/BD4-DTR: IC1.43, S1.137
/FPGA/FPGA-CORE/FLASH_CS: FLASH1.1, S1.38
/FPGA/FPGA-CORE/FLASH_SCK: FLASH1.6, S1.70
/FPGA/FPGA-CORE/FLASH_SI: FLASH1.5, S1.64
/FPGA/FPGA-CORE/FLASH_SO: FLASH1.2, S1.65
/FPGA/FPGA-CORE/MEGA_D0: R21.2, S1.116
/FPGA/FPGA-CORE/MEGA_D1: R20.2, S1.117
/FPGA/FPGA-CORE/MEGA_D2: R19.2, S1.118
/FPGA/FPGA-CORE/MEGA_D3: R18.2, S1.119
/FPGA/FPGA-CORE/MEGA_D4: R17.2, S1.120
/FPGA/FPGA-CORE/MEGA_D5: R16.2, S1.121
/FPGA/FPGA-CORE/MEGA_D6: R15.2, S1.123
/FPGA/FPGA-CORE/MEGA_D7: R14.2, S1.124
/FPGA/FPGA-CORE/MEGA_D8: R13.2, S1.126
/FPGA/FPGA-CORE/MEGA_D9: R12.2, S1.127
/FPGA/FPGA-CORE/MEGA_D10: R11.2, S1.131
/FPGA/FPGA-CORE/MEGA_D11: R10.2, S1.132
/FPGA/FPGA-CORE/MEGA_D12: R9.2, S1.133
/FPGA/FPGA-CORE/MEGA_D13: R8.2, S1.134
/FPGA/FPGA-CORE/MEGA_D17: S1.111, U1.D17
/FPGA/FPGA-CORE/MEGA_D18: S1.105, U1.D18
/FPGA/FPGA-CORE/MEGA_D19: S1.102, U1.D19
/FPGA/FPGA-CORE/MEGA_D20: S1.101, U1.D20
/FPGA/FPGA-CORE/MEGA_D21: S1.100, U1.D21
/FPGA/FPGA-CORE/MEGA_D22: S1.99, U1.D22
/FPGA/FPGA-CORE/MEGA_D23: S1.98, U1.D23
/FPGA/FPGA-CORE/MEGA_D24: S1.97, U1.D24
/FPGA/FPGA-CORE/MEGA_D25: S1.95, U1.D25
/FPGA/FPGA-CORE/MEGA_D26: S1.93, U1.D26
/FPGA/FPGA-CORE/MEGA_D27: S1.92, U1.D27
/FPGA/FPGA-CORE/MEGA_D29: S1.87, U1.D29
/FPGA/FPGA-CORE/MEGA_D31: S1.84, U1.D31
/FPGA/FPGA-CORE/MEGA_D33: S1.82, U1.D33
/FPGA/FPGA-CORE/MEGA_D35: S1.80, U1.D35
/FPGA/FPGA-CORE/MEGA_D36: S1.79, U1.D36
/FPGA/FPGA-CORE/MEGA_D37: S1.78, U1.D37
/FPGA/FPGA-CORE/MEGA_D38: S1.75, U1.D38
/FPGA/FPGA-CORE/MEGA_D39: S1.74, U1.D39
/FPGA/FPGA-CORE/MEGA_D40: S1.67, U1.D40
/FPGA/FPGA-CORE/MEGA_D41: S1.66, U1.D41
/FPGA/FPGA-CORE/MEGA_D42: S1.62, U1.D42
/FPGA/FPGA-CORE/MEGA_D43: S1.61, U1.D43
/FPGA/FPGA-CORE/MEGA_D44: S1.59, U1.D44
/FPGA/FPGA-CORE/MEGA_D45: S1.58, U1.D45
/FPGA/FPGA-CORE/MEGA_D46: S1.57, U1.D46
/FPGA/FPGA-CORE/MEGA_D47: S1.56, U1.D47
/FPGA/FPGA-CORE/MEGA_D48: S1.55, U1.D48
/FPGA/FPGA-CORE/MEGA_D49: S1.51, U1.D49
/FPGA/FPGA-CORE/MEGA_D50: S1.50, U1.D50
/FPGA/FPGA-CORE/MEGA_D51: S1.48, U1.D51
/FPGA/FPGA-CORE/MEGA_D52: S1.47, U1.D52
/FPGA/FPGA-CORE/MEGA_D53: R32.2, S1.39, U1.D53
/FPGA/FPGA-CORE/OSC_IN: OSC1.3@3, S1.94
/FPGA/FPGA-CORE/SRAM_A0: S1.7, SRAM1.3
/FPGA/FPGA-CORE/SRAM_A1: S1.8, SRAM1.4
/FPGA/FPGA-CORE/SRAM_A2: S1.9, SRAM1.5
/FPGA/FPGA-CORE/SRAM_A3: S1.10, SRAM1.6
/FPGA/FPGA-CORE/SRAM_A4: S1.11, SRAM1.7
/FPGA/FPGA-CORE/SRAM_A5: S1.5, SRAM1.16
/FPGA/FPGA-CORE/SRAM_A6: S1.2, SRAM1.17
/FPGA/FPGA-CORE/SRAM_A7: S1.1, SRAM1.18
/FPGA/FPGA-CORE/SRAM_A8: S1.143, SRAM1.19
/FPGA/FPGA-CORE/SRAM_A9: S1.142, SRAM1.20
/FPGA/FPGA-CORE/SRAM_A10: S1.43, SRAM1.26
/FPGA/FPGA-CORE/SRAM_A11: S1.41, SRAM1.27
/FPGA/FPGA-CORE/SRAM_A12: S1.40, SRAM1.28
/FPGA/FPGA-CORE/SRAM_A13: S1.35, SRAM1.29
/FPGA/FPGA-CORE/SRAM_A14: S1.34, SRAM1.30
/FPGA/FPGA-CORE/SRAM_A15: S1.27, SRAM1.38
/FPGA/FPGA-CORE/SRAM_A16: S1.29, SRAM1.39
/FPGA/FPGA-CORE/SRAM_A17: S1.33, SRAM1.40
/FPGA/FPGA-CORE/SRAM_A18: S1.32, SRAM1.41
/FPGA/FPGA-CORE/SRAM_A19: S1.44, SRAM1.25
/FPGA/FPGA-CORE/SRAM_A20: S1.30, SRAM1.42
/FPGA/FPGA-CORE/SRAM_D0: S1.14, SRAM1.9
/FPGA/FPGA-CORE/SRAM_D1: S1.15, SRAM1.10
/FPGA/FPGA-CORE/SRAM_D2: S1.16, SRAM1.13
/FPGA/FPGA-CORE/SRAM_D3: S1.17, SRAM1.14
/FPGA/FPGA-CORE/SRAM_D4: S1.21, SRAM1.31
/FPGA/FPGA-CORE/SRAM_D5: S1.22, SRAM1.32
/FPGA/FPGA-CORE/SRAM_D6: S1.23, SRAM1.35
/FPGA/FPGA-CORE/SRAM_D7: S1.24, SRAM1.36
/FPGA/FPGA-CORE/SW1: S1.104, SW1.COM2
/FPGA/FPGA-CORE/~SRAM_CS: S1.12, SRAM1.8
/FPGA/FPGA-CORE/~SRAM_OE: S1.26, SRAM1.37
/FPGA/FPGA-CORE/~SRAM_WE: S1.6, SRAM1.15
/FT2232H/5V_FT2232: FPGAUSB1.VUSB, PWRSEL1.1
/FT2232H/BC3: IC1.54, R30.2
/FT2232H/BC4: IC1.55, R29.2
/FT2232H/EECLK: IC1.62, U3.4
/FT2232H/EECS: IC1.63, R23.2, R24.2, U3.5
/FT2232H/EEDATA: IC1.61, R25.1, U3.3
/FT2232H/FTUSB_N: FPGAUSB1.D-, IC1.7
/FT2232H/FTUSB_P: FPGAUSB1.D+, IC1.8
/FT2232H/~RESET: IC1.14, R28.2
GND: AVRUSB1.P5, AVRUSB1.S1, AVRUSB1.S2, AVRUSB1.S3, AVRUSB1.S4, AVRUSB1.S5, AVRUSB1.S6, C1.2, C2.2, C3.2, C4.2, C6.2, C7.2, C8.2, C9.2, C10.2, C11.2, C12.2, C13.2, C14.-, C15.2, C16.2, C17.2, C18.2, C19.-, C20.2, C21.2, C23.2, C24.2, C25.2, C27.2, C28.-, C29.2, C30.2, C31.2, C32.2, C33.2, C34.2, C35.2, C101.1, C102.2, C103.2, C104.2, C105.1, C106.1, C107.1, FLASH1.4, FPGAUSB1.GND, IC1.1, IC1.5, IC1.10, IC1.11, IC1.13, IC1.15, IC1.25, IC1.35, IC1.47, IC1.51, LED1.C, OSC1.2@2, PWR1.C, PWRIN1.2, R3.2, R4.2, R27.2, RESET.B, RESET.B', S1.3, S1.13, S1.25, S1.49, S1.54, S1.60, S1.68, S1.73, S1.77, S1.91, S1.96, S1.108, S1.113, S1.130, S1.136, SRAM1.12, SRAM1.34, SW1.CH2B, U1.GND@0, U1.GND@1, U1.GND@2, U1.GND@3, U1.GND@4, U2.5, U2.6, U3.2, U101.5, U101.15, U101.23, U101.33, U101.35, U101.43, U101.EXP, WING_POWER1.P1, WING_POWER2.P1, WING_POWER3.P1, WING_POWER4.P1, WING_POWER5.P1, WING_POWER6.P1, Y1.2, Y1.4
unnamed: C8.1, IC1.3, X1.2
unnamed: C9.1, IC1.2, X1.1
unnamed: C14.+, C15.1, C28.+, C34.1, IC1.4, L3.1
unnamed: C5.2, C22.2, C26.2, C36.2
unnamed: IC1.6, R27.1
unnamed: IC1.9, L4.1
unnamed: L1.1, U2.4
unnamed: L2.1, U2.8
unnamed: LED1.A, R7.1
unnamed: PWR1.A, R6.2
unnamed: R2.1, R3.1, U2.1
unnamed: R4.1, R5.1, U2.10
unnamed: R8.1, U1.D13
unnamed: R9.1, U1.D12
unnamed: R10.1, U1.D11
unnamed: R11.1, U1.D10
unnamed: R12.1, U1.D9
unnamed: R13.1, U1.D8
unnamed: R14.1, U1.D7
unnamed: R15.1, U1.D6
unnamed: R16.1, U1.D5
unnamed: R17.1, U1.D4
unnamed: R18.1, U1.D3
unnamed: R19.1, U1.D2
unnamed: R20.1, U1.TX
unnamed: R21.1, U1.RX
unnamed: R25.2, R26.2, U3.1
unnamed: R29.1, TX1.C
unnamed: R30.1, RX1.C
unnamed: R31.1, RESET.A, RESET.A', S1.37
