brengi/CESE-PCB/2018/Lavigna/PRACTICA01/LAVIGNA_GONZALO/LAVIGNA_GONZALO.kicad_pcb

## KiCad design 2018/Lavigna/PRACTICA01/LAVIGNA_GONZALO/LAVIGNA_GONZALO.kicad_pcb (2019-05-17)

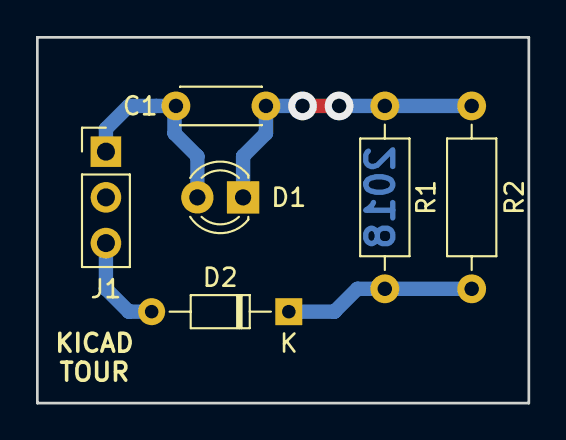
[picture p402: board 2018/Lavigna/PRACTICA01/LAVIGNA_GONZALO/LAVIGNA_GONZALO.kicad_pcb from above]

Board: 2 copper layers, 27.3 x 20.3 mm, 6 parts (0 on the bottom side), 4 nets.

Parts:
C1: 100nF; C_Disc_D4.3mm_W1.9mm_P5.00mm
D1: LED ROJO 3mm; LED_D3.0mm
D2: 1N4148; D_DO-34_SOD68_P7.62mm_Horizontal
J1: Conn_01x03; PinHeader_1x03_P2.54mm_Vertical
R1, R2: 100K; R_Axial_DIN0207_L6.3mm_D2.5mm_P10.16mm_Horizontal

Connections:
unnamed: C1.1, D1.1, R1.1, R2.1
unnamed: C1.2, D1.2, J1.1
unnamed: D2.1, R1.2, R2.2
unnamed: D2.2, J1.3
