brengi/CESE-PCB/2018/Menendez/Contador12/Contador12.kicad_pcb

## KiCad design 2018/Menendez/Contador12/Contador12.kicad_pcb (2019-05-17)

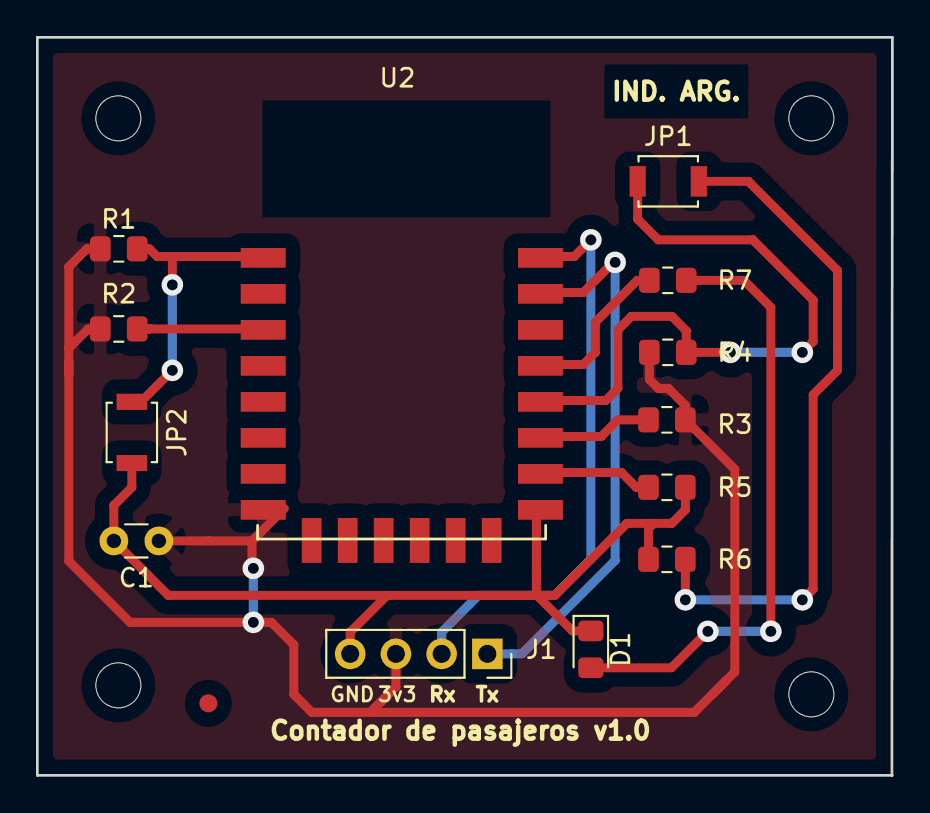
[picture p403: board Contador12.kicad_pcb from above]

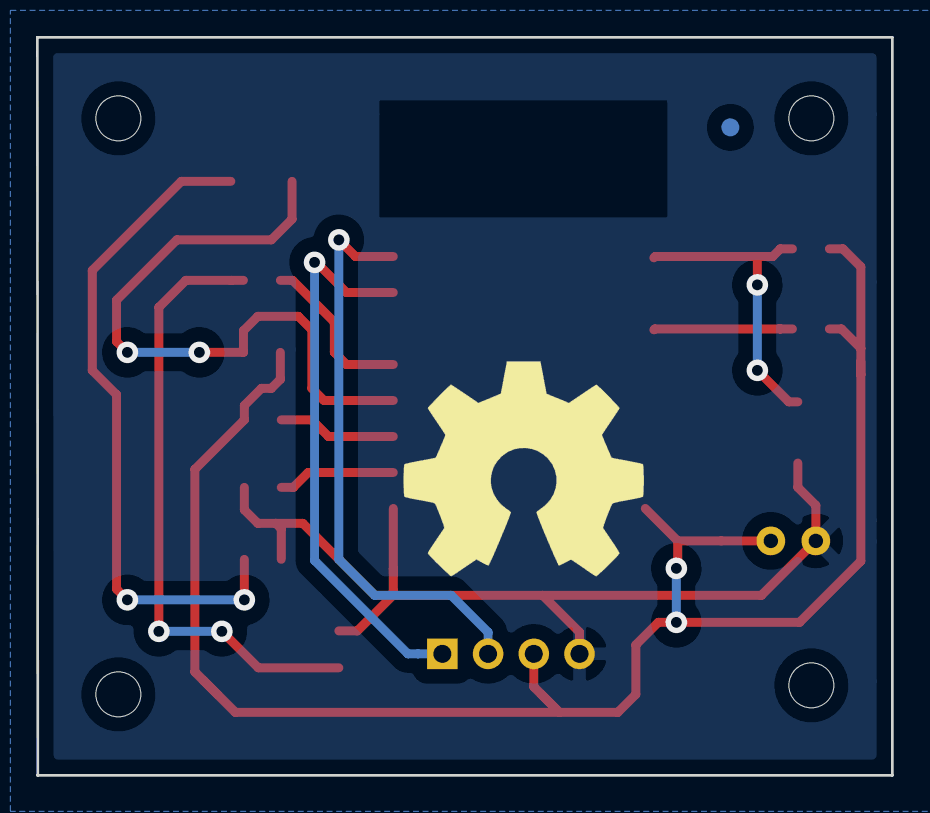
[picture p404: board Contador12.kicad_pcb from below]

Board: 2 copper layers, 47.5 x 41.0 mm, 20 parts (2 on the bottom side), 12 nets.

Parts:
C1: 100n; C_Disc_D3.0mm_W1.6mm_P2.50mm
D1: LED; LED_0805_2012Metric_Pad1.15x1.40mm_HandSolder
F1, F2: MH2; Fiducial_1mm_Dia_2mm_Outer
J1: Conector_ESP; PinSocket_1x04_P2.54mm_Vertical
JP1, JP2: Jumper; SW_SPST_B3U-1000P
Logo1: Logo_Open_Hardware_Small; OSHW-Symbol_13.4x12mm_SilkScreen
MH1: MH1; MountingHole_2.5mm
MH2: MH2; MountingHole_2.5mm
MH3: MH3; MountingHole_2.5mm
MH4: MH4; MountingHole_2.5mm
R1, R2, R3, R4, R5: 10k; R_0805_2012Metric_Pad1.15x1.40mm_HandSolder
R6, R7: 470; R_0805_2012Metric_Pad1.15x1.40mm_HandSolder
U2: ESP-12E; ESP-12E_SMD

Connections:
+3V3: C1.1, J1.3, R1.1, R2.2, R3.2, R4.1, U2.8
/Program: JP1.1, R4.2, U2.12
/Reset: JP2.1, R1.2, U2.1
/Rx: J1.2, U2.16
/Tx: J1.1, U2.15
GND: C1.2, D1.1, J1.4, JP2.2, R5.2, R6.2, U2.9
unnamed: D1.2, R7.2
unnamed: JP1.2, R6.1
unnamed: R2.1, U2.3
unnamed: R3.1, U2.11
unnamed: R5.1, U2.10
unnamed: R7.1, U2.13
