brengi/CESE-PCB/2018/Menendez/ContadorDePasajeros/ContadorDePasajeros.kicad_pcb

## KiCad design 2018/Menendez/ContadorDePasajeros/ContadorDePasajeros.kicad_pcb (2019-05-17)

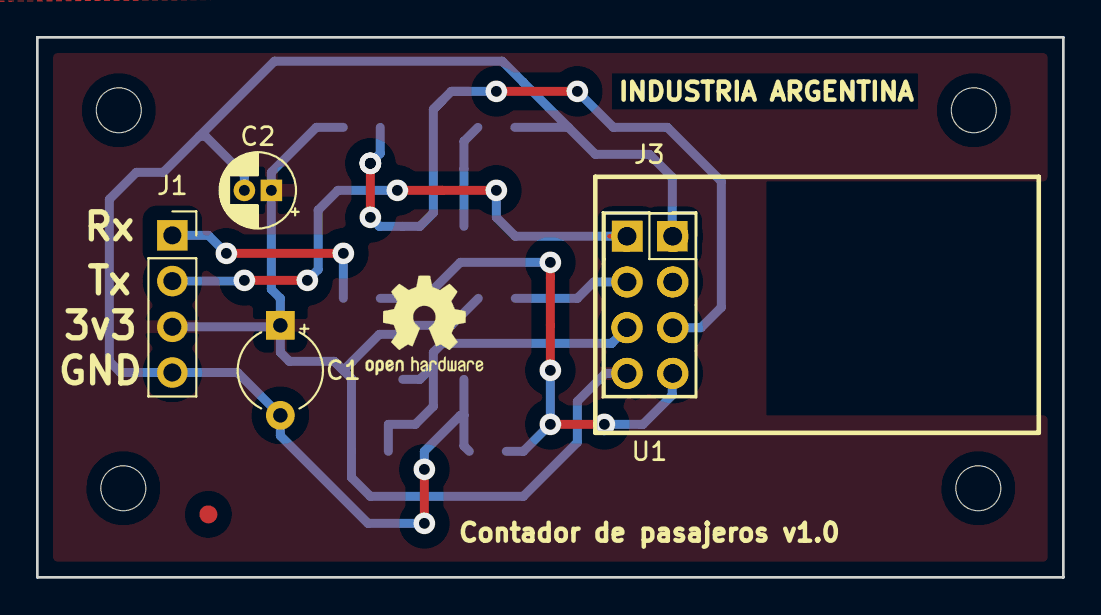
[picture p405: board ContadorDePasajeros.kicad_pcb from above]

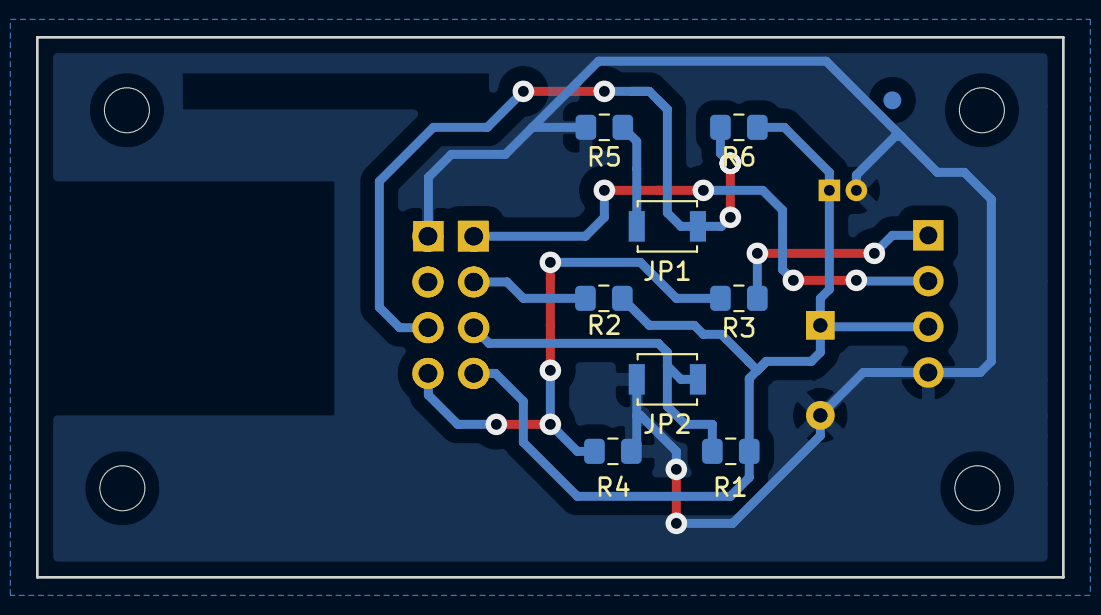
[picture p406: board ContadorDePasajeros.kicad_pcb from below]

Board: 2 copper layers, 57.0 x 30.0 mm, 20 parts (9 on the bottom side), 10 nets.

Parts:
C1: 100n; CP_Radial_Tantal_D4.5mm_P5.00mm
C2: 100u; CP_Radial_D4.0mm_P1.50mm
F1, F2: MH4; Fiducial_1mm_Dia_2mm_Outer
J1: Conector_in; PinSocket_1x04_P2.54mm_Vertical
J3: Conector_esp; PinSocket_2x04_P2.54mm_Vertical
JP1, JP2: Jumper; SW_SPST_B3U-1000P
Logo1: Logo_Open_Hardware_Small; OSHW-Logo2_7.3x6mm_SilkScreen
MH1: MH1; MountingHole_2.5mm
MH2: MH2; MountingHole_2.5mm
MH3: MH3; MountingHole_2.5mm
MH4: MH4; MountingHole_2.5mm
R1, R2, R6: 3k3; R_0805_2012Metric_Pad1.15x1.40mm_HandSolder
R3: 1k; R_0805_2012Metric_Pad1.15x1.40mm_HandSolder
R4: 2k; R_0805_2012Metric_Pad1.15x1.40mm_HandSolder
R5: 470; R_0805_2012Metric_Pad1.15x1.40mm_HandSolder
U1: ESP01; ESP-01

Connections:
+3V3: C1.1, C2.1, J1.3, J3.8, R1.2, R2.2, R6.1, U1.7
/Ch: J3.4, R2.1, U1.3
/Gpio0: J3.5, JP1.1, R6.2, U1.6
/Gpio2: J3.3, U1.4
/Rs: J3.6, JP2.1, R1.1, U1.5
/Rx_i: J3.7, R3.2, R4.1, U1.8
GND: C1.2, C2.2, J1.4, J3.1, JP2.2, R4.2, R5.2, U1.2
unnamed: JP1.2, R5.1
Rx: J1.1, R3.1
Tx: J1.2, J3.2, U1.1
