brengi/CESE-PCB/2018/Roux/vop24_lpcxpresso1769_basehw/vop24_lpcxpresso1769_basehw.kicad_pcb

## KiCad design 2018/Roux/vop24_lpcxpresso1769_basehw/vop24_lpcxpresso1769_basehw.kicad_pcb (2019-05-17)

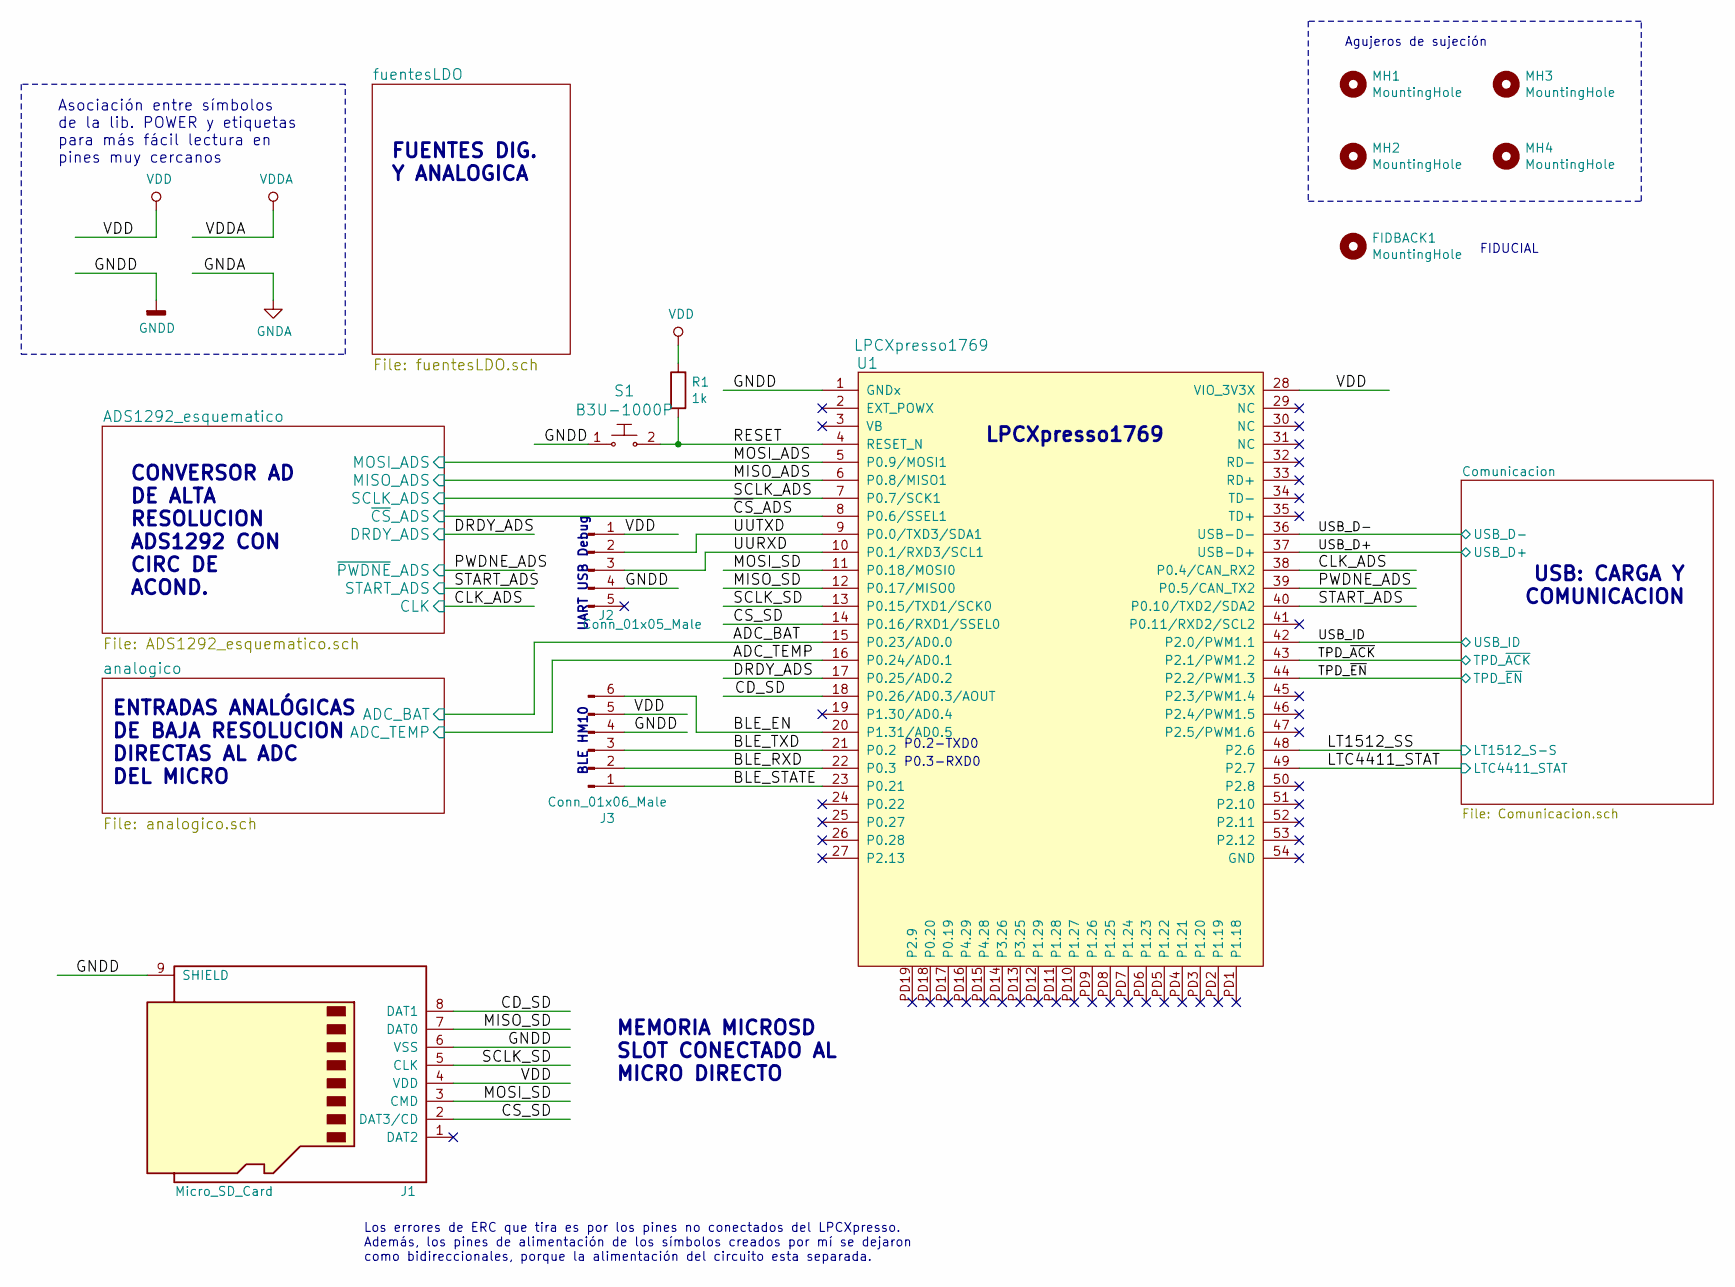
[picture p407: schematic vop24_lpcxpresso1769_basehw.sch, Prototipo 1 Base LPCXpresso - VOP24]

Parts:
FIDBACK1: MountingHole; Fiducial_0.75mm_Dia_1.5mm_Outer
J1: Micro_SD_Card; microSD_3020-901-0001-ACH-ELECTRONICS
J2: Conn_01x05_Male; PinSocket_1x05_P2.54mm_Vertical
J3: Conn_01x06_Male; PinSocket_1x06_P2.54mm_Vertical
MH1, MH2, MH3, MH4: MountingHole; MountingHole_3.5mm
R1: 1k; R_0805_2012Metric_Pad1.15x1.40mm_HandSolder
S1: B3U-1000P; Switch_Tactile_SMD_B3U-1000P; MPN B3U-1000P; Digi-Key_PN SW1020CT-ND
U1: LPCXpresso1769

Connections:
/ADC_BAT: U1.15 (P0.23/AD0.0); also elsewhere on the board
/ADC_TEMP: U1.16 (P0.24/AD0.1); also elsewhere on the board
/BLE_EN: J3.6, U1.20 (P1.31/AD0.5)
/BLE_RXD: J3.2, U1.22 (P0.3)
/BLE_STATE: J3.1, U1.23 (P0.21)
/BLE_TXD: J3.3, U1.21 (P0.2)
/CD_SD: J1.8 (DAT1), U1.18 (P0.26/AD0.3/AOUT)
/CLK_ADS: U1.38 (P0.4/CAN_RX2); also elsewhere on the board
/CS_SD: J1.2 (DAT3/CD), U1.14 (P0.16/RXD1/SSEL0)
/DRDY_ADS: U1.17 (P0.25/AD0.2); also elsewhere on the board
/LT1512_SS: U1.48 (P2.6); also elsewhere on the board
/LTC4411_STAT: U1.49 (P2.7); also elsewhere on the board
/MISO_ADS: U1.6 (P0.8/MISO1); also elsewhere on the board
/MISO_SD: J1.7 (DAT0), U1.12 (P0.17/MISO0)
/MOSI_ADS: U1.5 (P0.9/MOSI1); also elsewhere on the board
/MOSI_SD: J1.3 (CMD), U1.11 (P0.18/MOSI0)
/PWDNE_ADS: U1.39 (P0.5/CAN_TX2); also elsewhere on the board
/RESET: R1.2, S1.2, U1.4 (RESET_N)
/SCLK_ADS: U1.7 (P0.7/SCK1); also elsewhere on the board
/SCLK_SD: J1.5 (CLK), U1.13 (P0.15/TXD1/SCK0)
/START_ADS: U1.40 (P0.10/TXD2/SDA2); also elsewhere on the board
/TPD_~ACK: U1.43 (P2.1/PWM1.2); also elsewhere on the board
/TPD_~EN: U1.44 (P2.2/PWM1.3); also elsewhere on the board
/USB_D+: U1.37 (USB-D+); also elsewhere on the board
/USB_D-: U1.36 (USB-D-); also elsewhere on the board
/USB_ID: U1.42 (P2.0/PWM1.1); also elsewhere on the board
/UURXD: J2.3, U1.10 (P0.1/RXD3/SCL1)
/UUTXD: J2.2, U1.9 (P0.0/TXD3/SDA1)
/~CS~_ADS: U1.8 (P0.6/SSEL1); also elsewhere on the board
GNDD: J1.6 (VSS), J1.9 (SHIELD), J2.4, J3.4, S1.1, U1.1 (GNDx); also elsewhere on the board
VDD: J1.4 (VDD), J2.1, J3.5, R1.1, U1.28 (VIO_3V3X); also elsewhere on the board

Notes on the sheet:
P0.2-TXD0
P0.3-RXD0
FUENTES DIG. Y ANALOGICA
ENTRADAS ANALÓGICAS DE BAJA RESOLUCION DIRECTAS AL ADC DEL MICRO
MEMORIA MICROSD SLOT CONECTADO AL MICRO DIRECTO
USB: CARGA Y COMUNICACION
CONVERSOR AD DE ALTA RESOLUCION ADS1292 CON CIRC DE ACOND.
LPCXpresso1769
Los errores de ERC que tira es por los pines no conectados del LPCXpresso. Además, los pines de alimentación de los símbolos creados por mí se dejaron como bidireccionales, porque la alimentación del circuito esta separada.
BLE HM10
UART USB Debug
Asociación entre símbolos de la lib. POWER y etiquetas para más fácil lectura en pines muy cercanos
Agujeros de sujeción
FIDUCIAL

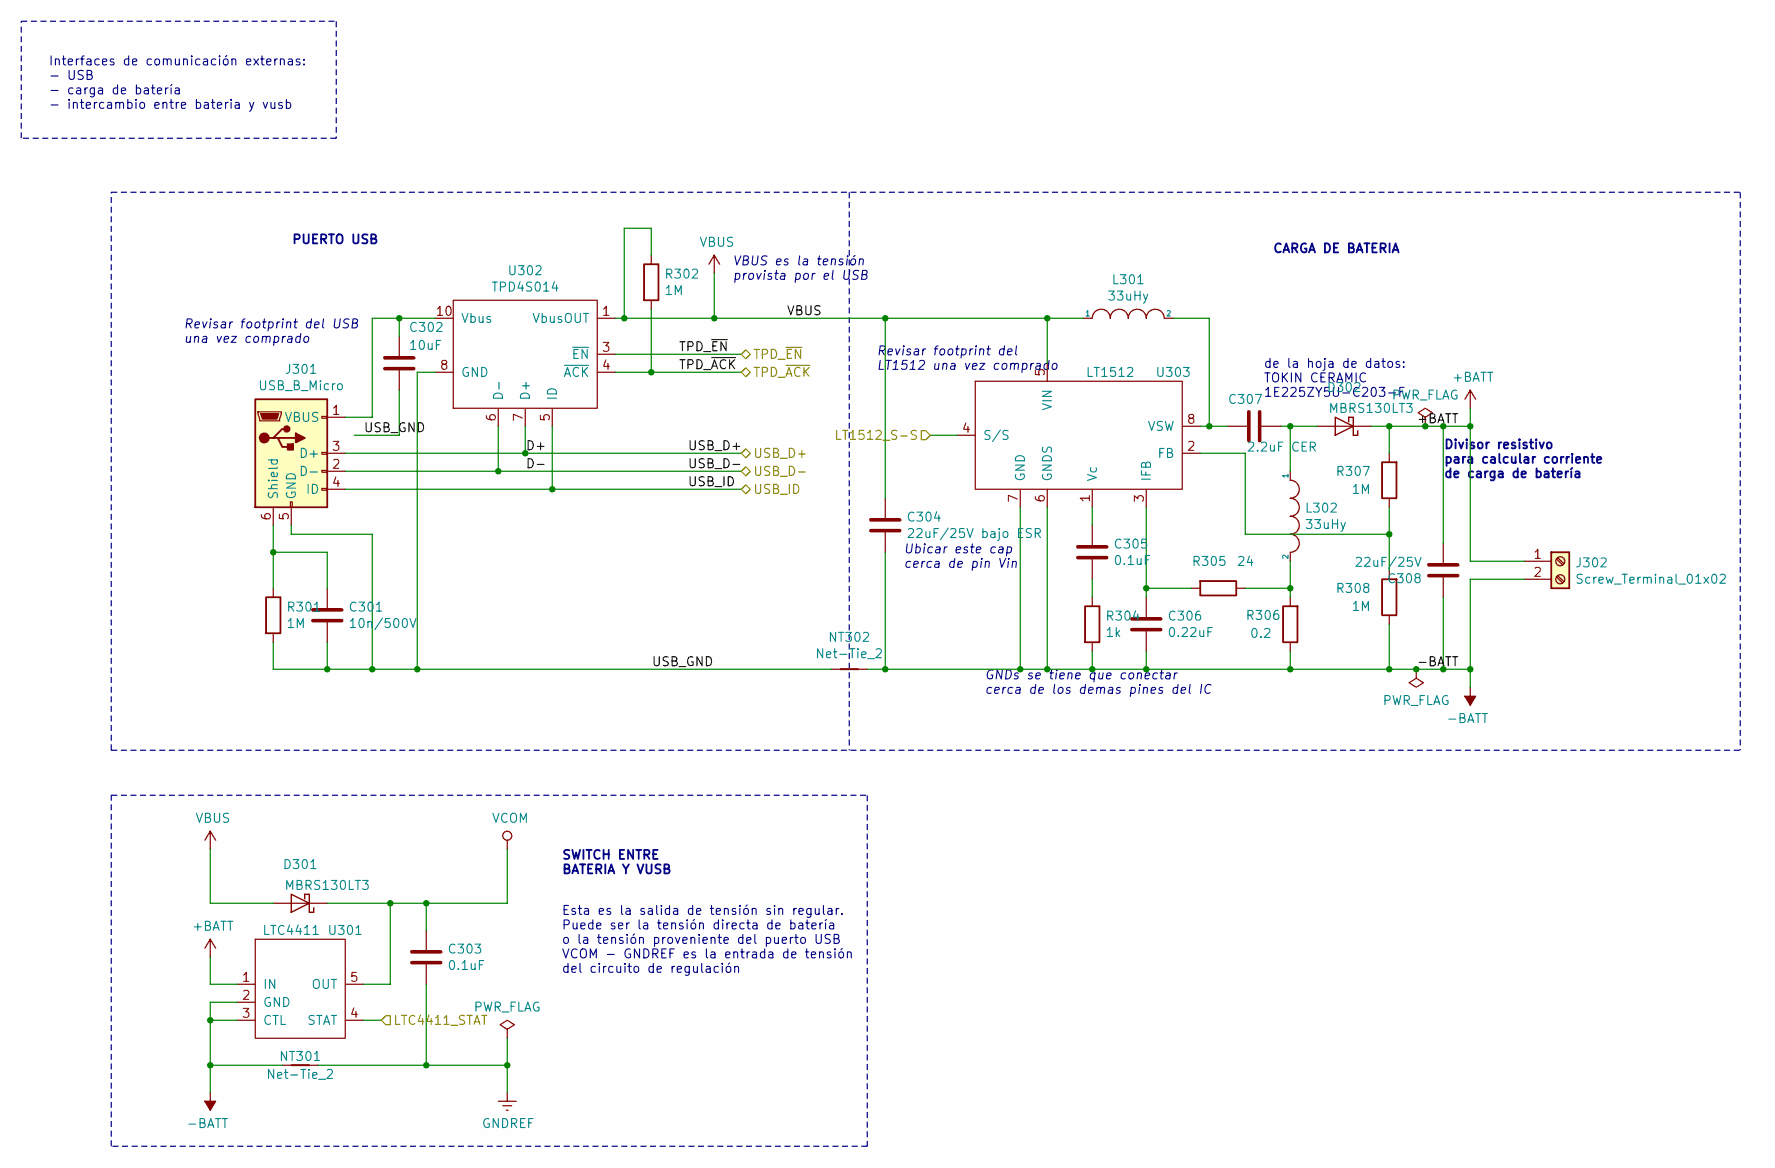
[picture p408: schematic Comunicacion.sch, Prototipo 1 Base LPCXpresso - VOP24]

Parts:
C301: 10n/500V; C_0805_2012Metric_Pad1.15x1.40mm_HandSolder
C302: 10uF; C_0805_2012Metric_Pad1.15x1.40mm_HandSolder
C303, C305: 0.1uF; C_0805_2012Metric_Pad1.15x1.40mm_HandSolder
C304: 22uF/25V bajo ESR; CP_Radial_D5.0mm_P2.50mm
C306: 0.22uF; C_0805_2012Metric_Pad1.15x1.40mm_HandSolder
C307: 2.2uF CER; CP_Radial_D5.0mm_P2.50mm
C308: 22uF/25V; CP_Radial_D5.0mm_P2.50mm
D301, D302: MBRS130LT3; D_SMB-SMC_Universal_Handsoldering
J301: USB_B_Micro; USB_Mini-B_Lumberg_2486_01_Horizontal
J302: Screw_Terminal_01x02; TerminalBlock_bornier-2_P5.08mm
L301, L302: 33uHy; L_Radial_D8.7mm_P5.00mm_Fastron_07HCP
NT301, NT302: Net-Tie_2; NetTie-2_SMD_Pad0.5mm
R301, R302, R307, R308: 1M; R_0805_2012Metric_Pad1.15x1.40mm_HandSolder
R304: 1k; R_0805_2012Metric_Pad1.15x1.40mm_HandSolder
R305: 24; R_0805_2012Metric_Pad1.15x1.40mm_HandSolder
R306: 0.2; R_0805_2012Metric_Pad1.15x1.40mm_HandSolder
U301: LTC4411; SOT-23-5_HandSoldering
U302: TPD4S014; Texas_R-PWSON-N10
U303: LT1512; SO-8_5.3x6.2mm_P1.27mm

Connections:
+BATT: C308.2, D302.1 (K), J302.1, R307.2, U301.1 (IN); also elsewhere on the board
-BATT: C304.2, C306.2, C308.1, J302.2, NT301.1, NT302.2, R304.2, R306.1, R308.1, U301.2 (GND), U301.3 (CTL), U303.6 (GNDS), U303.7 (GND); also elsewhere on the board
/Comunicacion/USB_GND: C301.2, C302.2, J301.5 (GND), NT302.1, R301.2, U302.8 (GND)
/LT1512_SS: U303.4 (S/S); also elsewhere on the board
/LTC4411_STAT: U301.4 (STAT); also elsewhere on the board
/TPD_~ACK: R302.2, U302.4 (~ACK); also elsewhere on the board
/TPD_~EN: U302.3 (~EN); also elsewhere on the board
/USB_D+: J301.3 (D+), U302.7 (D+); also elsewhere on the board
/USB_D-: J301.2 (D-), U302.6 (D-); also elsewhere on the board
/USB_ID: J301.4 (ID), U302.5 (ID); also elsewhere on the board
GNDREF: C303.2, NT301.2; also elsewhere on the board
unnamed: C301.1, J301.6 (Shield), R301.1
unnamed: C302.1, J301.1 (VBUS), U302.10 (Vbus)
unnamed: C305.1, U303.1 (Vc)
unnamed: C305.2, R304.1
unnamed: C306.1, R305.2, U303.3 (IFB)
unnamed: C307.1, D302.2 (A), L302.1
unnamed: C307.2, L301.2, U303.8 (VSW)
unnamed: L302.2, R305.1, R306.2
unnamed: R307.1, R308.2, U303.2 (FB)
VBUS: C304.1, D301.2 (A), L301.1, R302.1, U302.1 (VbusOUT), U303.5 (VIN)
VCOM: C303.1, D301.1 (K), U301.5 (OUT); also elsewhere on the board

Notes on the sheet:
de la hoja de datos: TOKIN CERAMIC 1E225ZY5U-C203-F
Divisor resistivo para calcular corriente de carga de batería
CARGA DE BATERIA
SWITCH ENTRE BATERIA Y VUSB
PUERTO USB
Revisar footprint del USB una vez comprado
Revisar footprint del LT1512 una vez comprado
Ubicar este cap cerca de pin Vin
GNDs se tiene que conectar cerca de los demas pines del IC
Interfaces de comunicación externas: - USB - carga de batería - intercambio entre bateria y vusb
Esta es la salida de tensión sin regular. Puede ser la tensión directa de batería o la tensión proveniente del puerto USB VCOM - GNDREF es la entrada de tensión del circuito de regulación
VBUS es la tensión provista por el USB

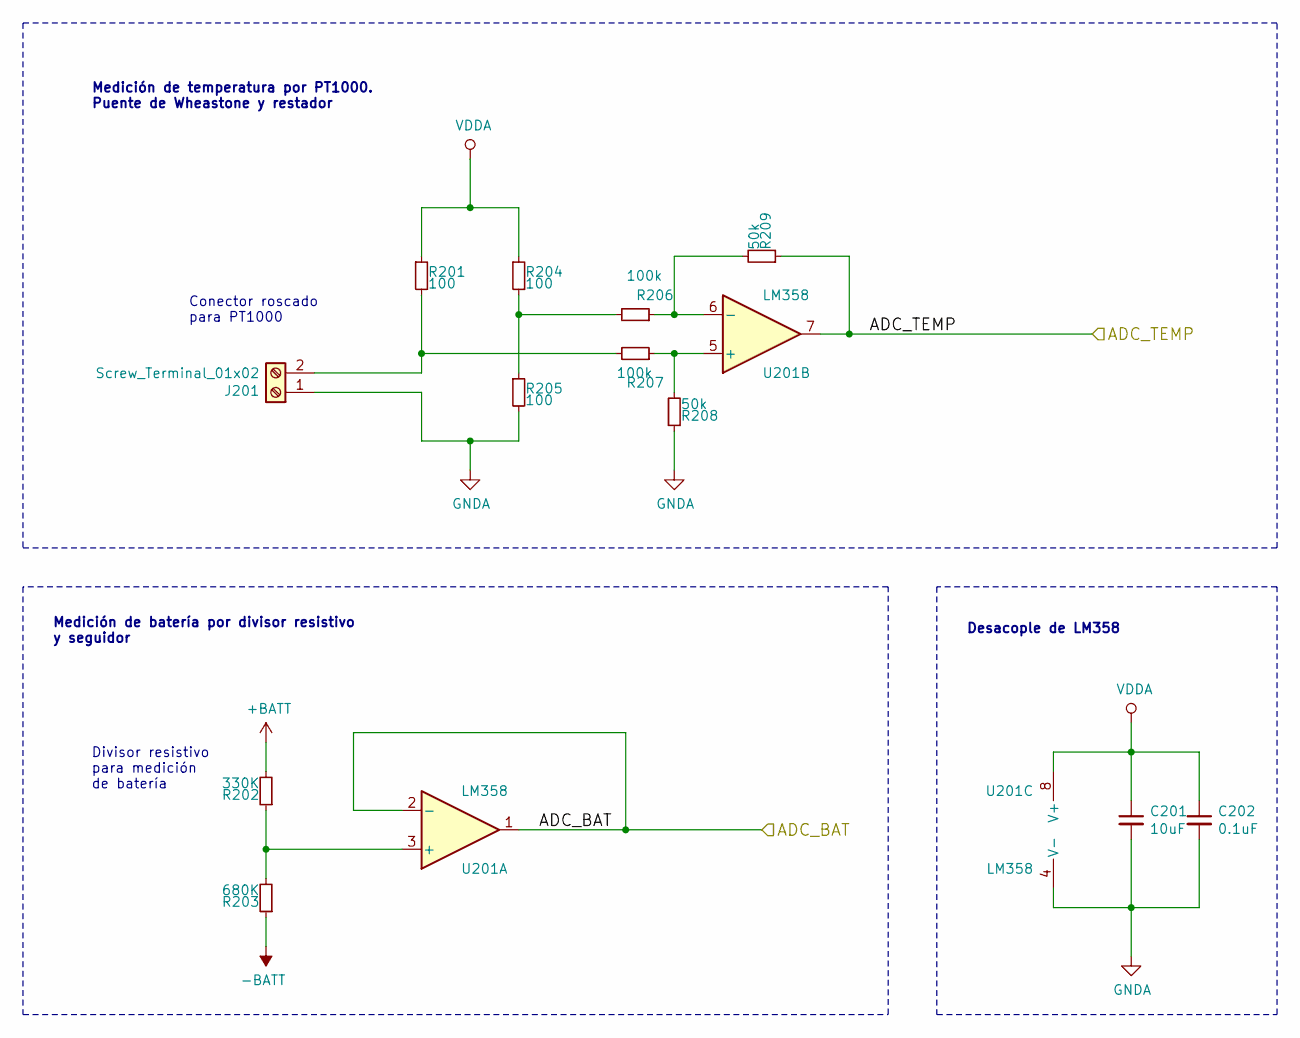
[picture p409: schematic analogico.sch, Prototipo 1 Base LPCXpresso - VOP24]

Parts:
C201: 10uF; C_0805_2012Metric_Pad1.15x1.40mm_HandSolder
C202: 0.1uF; C_0805_2012Metric_Pad1.15x1.40mm_HandSolder
J201: Screw_Terminal_01x02; TerminalBlock_bornier-2_P5.08mm
R201, R204, R205: 100; R_0805_2012Metric_Pad1.15x1.40mm_HandSolder
R202: 330K; R_0805_2012Metric_Pad1.15x1.40mm_HandSolder
R203: 680K; R_0805_2012Metric_Pad1.15x1.40mm_HandSolder
R206, R207: 100k; R_0805_2012Metric_Pad1.15x1.40mm_HandSolder
R208, R209: 50k; R_0805_2012Metric_Pad1.15x1.40mm_HandSolder
U201: LM358; SO-8_5.3x6.2mm_P1.27mm

Connections:
+BATT: R202.2; also elsewhere on the board
-BATT: R203.1; also elsewhere on the board
/ADC_BAT: U201.1, U201.2 (-); also elsewhere on the board
/ADC_TEMP: R209.1, U201.7; also elsewhere on the board
GNDA: C201.2, C202.2, J201.1, R205.2, R208.1, U201.4 (V-); also elsewhere on the board
unnamed: J201.2, R201.2, R207.2
unnamed: R202.1, R203.2, U201.3 (+)
unnamed: R204.2, R205.1, R206.2
unnamed: R206.1, R209.2, U201.6 (-)
unnamed: R207.1, R208.2, U201.5 (+)
VDDA: C201.1, C202.1, R201.1, R204.1, U201.8 (V+); also elsewhere on the board

Notes on the sheet:
Conector roscado para PT1000
Divisor resistivo para medición de batería
Medición de temperatura por PT1000. Puente de Wheastone y restador
Medición de batería por divisor resistivo y seguidor
Desacople de LM358

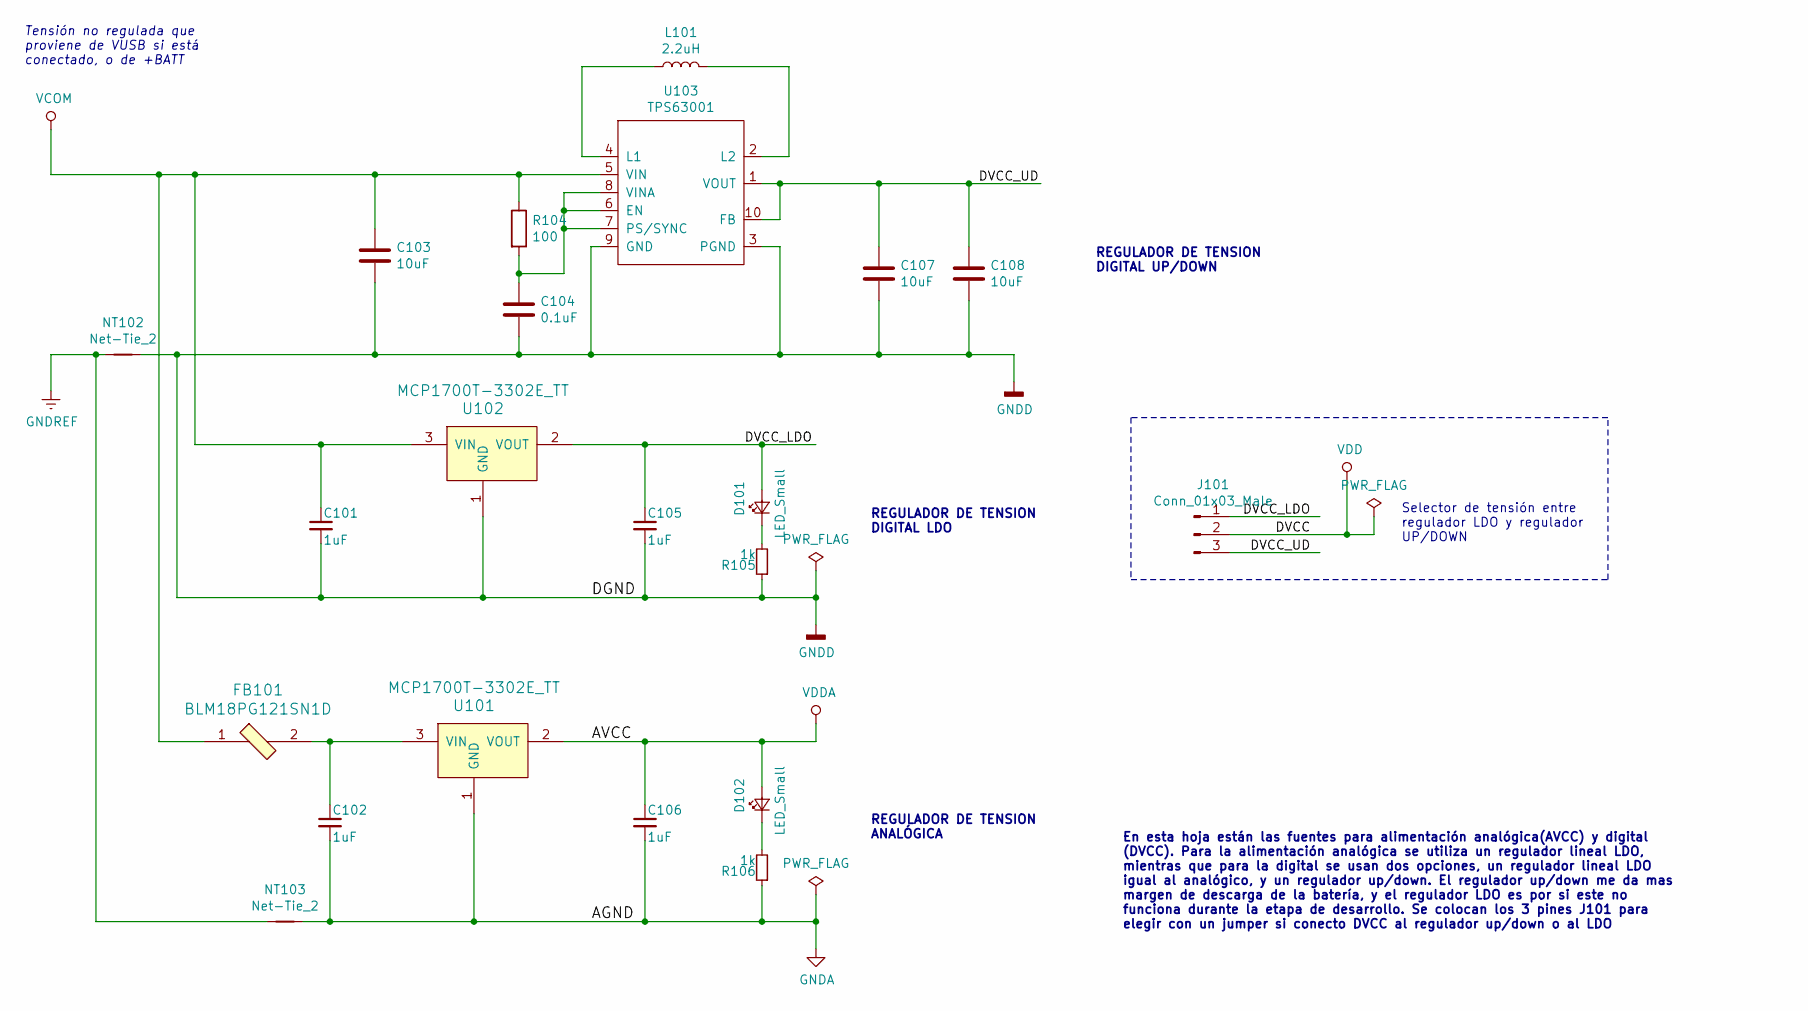
[picture p410: schematic fuentesLDO.sch, Prototipo 1 Base LPCXpresso - VOP24]

Parts:
C101, C102, C105, C106: 1uF; C_0805_2012Metric_Pad1.15x1.40mm_HandSolder
C103, C107, C108: 10uF; C_0805_2012Metric_Pad1.15x1.40mm_HandSolder
C104: 0.1uF; C_0805_2012Metric_Pad1.15x1.40mm_HandSolder
D101, D102: LED_Small; LED_0805_2012Metric_Pad1.15x1.40mm_HandSolder
FB101: BLM18PG121SN1D; 0603; MPN BLM18PG121SN1D; Digi-Key_PN 490-1037-1-ND
J101: Conn_01x03_Male; PinHeader_1x03_P2.54mm_Vertical
L101: 2.2uH; L_0805_2012Metric_Pad1.15x1.40mm_HandSolder
NT102, NT103: Net-Tie_2; NetTie-2_SMD_Pad0.5mm
R104: 100; R_0805_2012Metric_Pad1.15x1.40mm_HandSolder
R105, R106: 1k; R_0805_2012Metric_Pad1.15x1.40mm_HandSolder
U101, U102: MCP1700T-3302E_TT; SOT-23-3; MPN MCP1700T-3302E/TT; Digi-Key_PN MCP1700T3302ETTCT-ND
U103: TPS63001; VSON-10-1EP_3x3mm_P0.5mm_EP1.65x2.4mm_ThermalVias

Connections:
/fuentesLDO/DVCC_LDO: C105.1, D101.2 (A), J101.1, U102.2 (VOUT)
/fuentesLDO/DVCC_UD: C107.1, C108.1, J101.3, U103.1 (VOUT), U103.10 (FB)
GNDA: C102.2, C106.2, NT103.2, R106.1, U101.1 (GND); also elsewhere on the board
GNDD: C101.2, C103.2, C104.2, C105.2, C107.2, C108.2, NT102.2, R105.1, U102.1 (GND), U103.3 (PGND), U103.9 (GND); also elsewhere on the board
GNDREF: NT102.1, NT103.1; also elsewhere on the board
unnamed: C102.1, FB101.2, U101.3 (VIN)
unnamed: C104.1, R104.2, U103.6 (EN), U103.7 (PS/SYNC), U103.8 (VINA)
unnamed: D101.1 (K), R105.2
unnamed: D102.1 (K), R106.2
unnamed: L101.1, U103.4 (L1)
unnamed: L101.2, U103.2 (L2)
VCOM: C101.1, C103.1, FB101.1, R104.1, U102.3 (VIN), U103.5 (VIN); also elsewhere on the board
VDD: J101.2; also elsewhere on the board
VDDA: C106.1, D102.2 (A), U101.2 (VOUT); also elsewhere on the board

Notes on the sheet:
En esta hoja están las fuentes para alimentación analógica(AVCC) y digital (DVCC). Para la alimentación analógica se utiliza un regulador lineal LDO, mientras que para la digital se usan dos opciones, un regulador lineal LDO igual al analógico, y un regulador up/down. El regulador up/down me da mas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
Tensión no regulada que proviene de VUSB si está conectado, o de +BATT
REGULADOR DE TENSION ANALÓGICA
REGULADOR DE TENSION DIGITAL LDO
REGULADOR DE TENSION DIGITAL UP/DOWN
Selector de tensión entre regulador LDO y regulador UP/DOWN

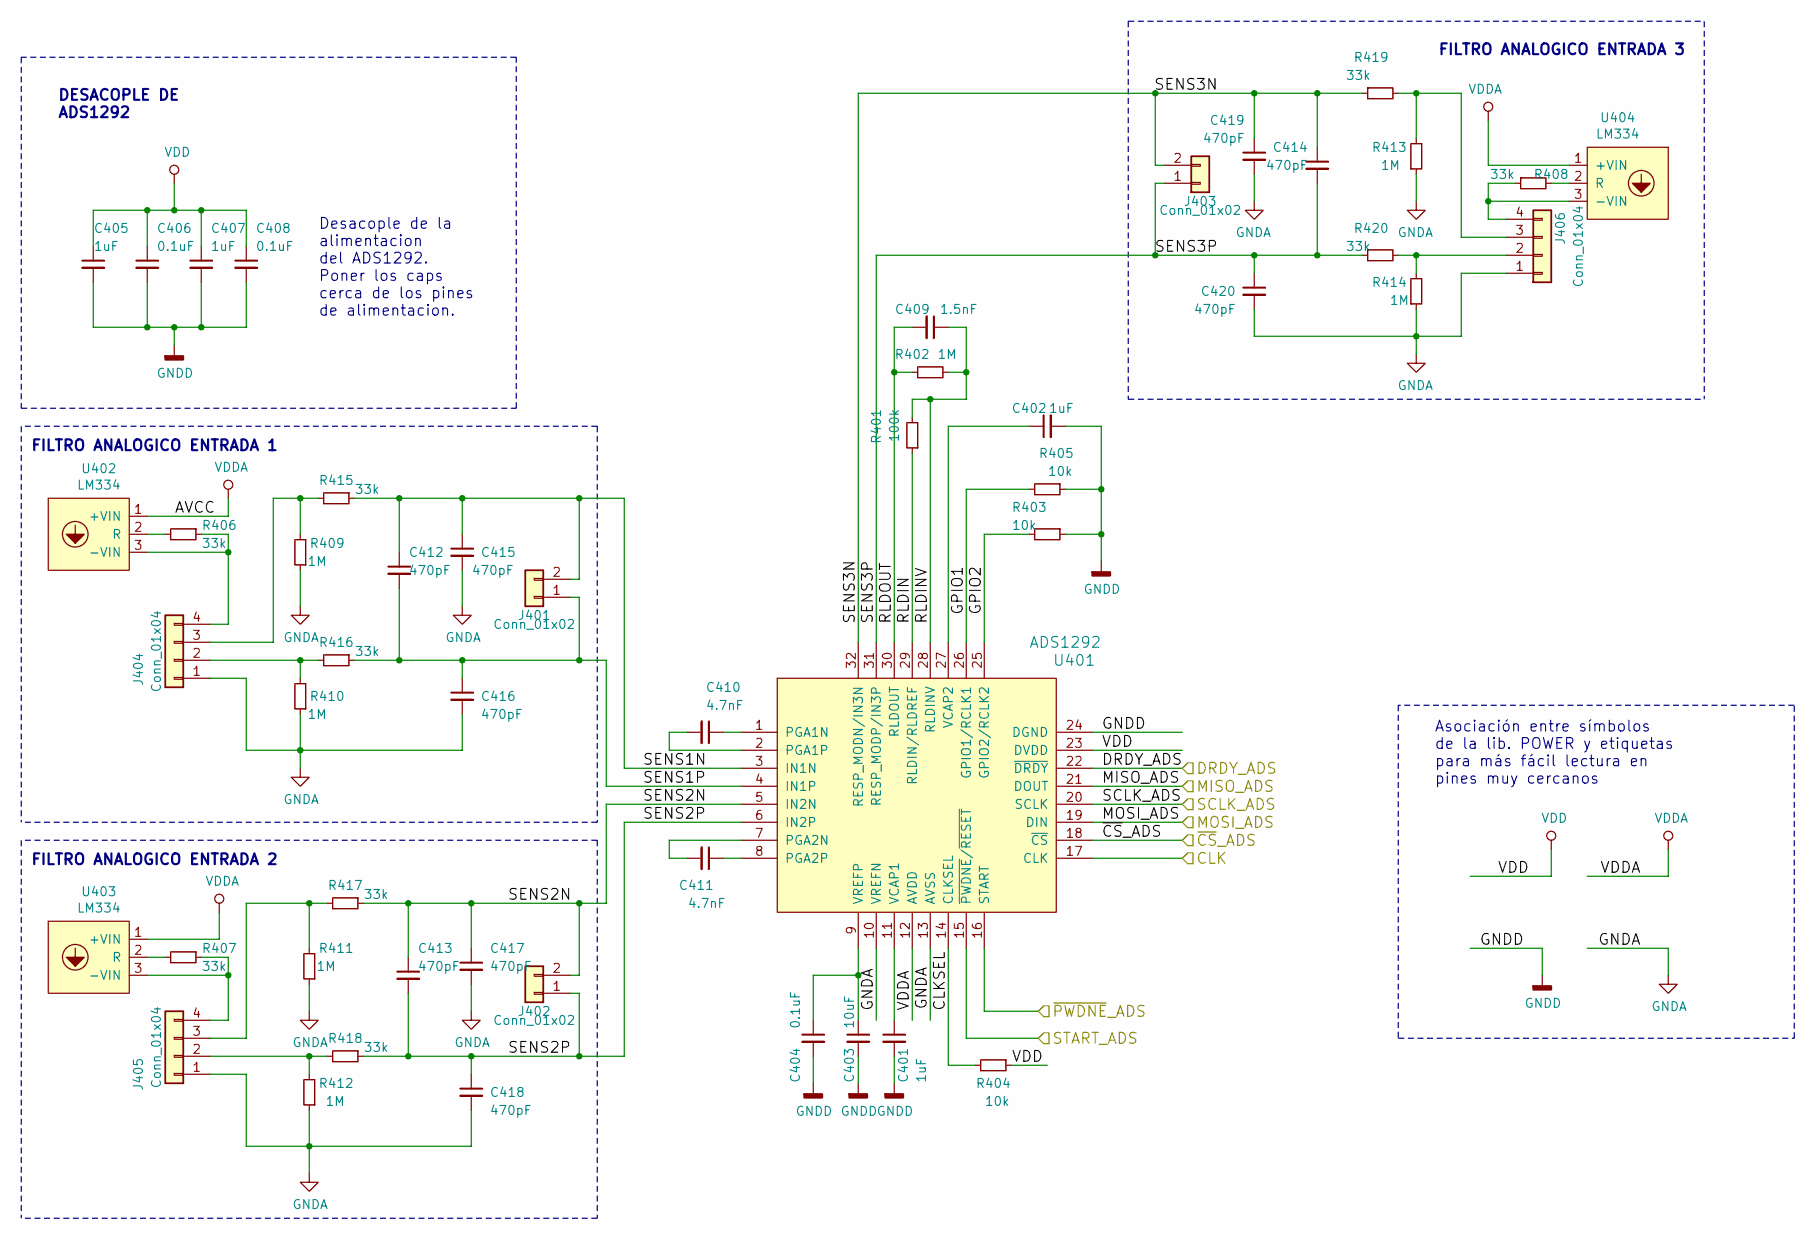
[picture p411: schematic ADS1292_esquematico.sch, Prototipo 1 Base LPCXpresso - VOP24]

Parts:
C401, C402, C405, C407: 1uF; C_0805_2012Metric_Pad1.15x1.40mm_HandSolder
C403: 10uF; C_0805_2012Metric_Pad1.15x1.40mm_HandSolder
C404, C406, C408: 0.1uF; C_0805_2012Metric_Pad1.15x1.40mm_HandSolder
C409: 1.5nF; C_0805_2012Metric_Pad1.15x1.40mm_HandSolder
C410, C411: 4.7nF; C_0805_2012Metric_Pad1.15x1.40mm_HandSolder
C412, C413, C414, C415, C416, C417, C418, C419, C420: 470pF; C_0805_2012Metric_Pad1.15x1.40mm_HandSolder
J401, J402, J403: Conn_01x02; PinHeader_1x02_P1.27mm_Vertical
J404, J405, J406: Conn_01x04; PinSocket_1x04_P2.54mm_Vertical
R401: 100k; R_0805_2012Metric_Pad1.15x1.40mm_HandSolder
R402, R409, R410, R411, R412, R413, R414: 1M; R_0805_2012Metric_Pad1.15x1.40mm_HandSolder
R403, R404, R405: 10k; R_0805_2012Metric_Pad1.15x1.40mm_HandSolder
R406, R407, R408, R415, R416, R417, R418, R419, R420: 33k; R_0805_2012Metric_Pad1.15x1.40mm_HandSolder
U401: ADS1292; PQFP-G32_7x7mm_P0.5mm
U402, U403, U404: LM334; TO-92_Inline_Wide

Connections:
/ADS1292_esquematico/CLKSEL: R404.2, U401.14 (CLKSEL)
/ADS1292_esquematico/GPIO1: R405.2, U401.26 (GPIO1/RCLK1)
/ADS1292_esquematico/GPIO2: R403.2, U401.25 (GPIO2/RCLK2)
/ADS1292_esquematico/RLDIN: R401.1, U401.29 (RLDIN/RLDREF)
/ADS1292_esquematico/RLDINV: C409.1, R401.2, R402.2, U401.28 (RLDINV)
/ADS1292_esquematico/RLDOUT: C409.2, R402.1, U401.30 (RLDOUT)
/ADS1292_esquematico/SENS1N: C412.1, C415.1, J401.2, R415.1, U401.3 (IN1N)
/ADS1292_esquematico/SENS1P: C412.2, C416.1, J401.1, R416.1, U401.4 (IN1P)
/ADS1292_esquematico/SENS2N: C413.1, C417.1, J402.2, R417.1, U401.5 (IN2N)
/ADS1292_esquematico/SENS2P: C413.2, C418.1, J402.1, R418.1, U401.6 (IN2P)
/ADS1292_esquematico/SENS3N: C414.1, C419.1, J403.2, R419.1, U401.32 (RESP_MODN/IN3N)
/ADS1292_esquematico/SENS3P: C414.2, C420.1, J403.1, R420.1, U401.31 (RESP_MODP/IN3P)
/CLK_ADS: U401.17 (CLK); also elsewhere on the board
/DRDY_ADS: U401.22 (~DRDY); also elsewhere on the board
/MISO_ADS: U401.21 (DOUT); also elsewhere on the board
/MOSI_ADS: U401.19 (DIN); also elsewhere on the board
/PWDNE_ADS: U401.16 (START); also elsewhere on the board
/SCLK_ADS: U401.20 (SCLK); also elsewhere on the board
/START_ADS: U401.15 (~PWDNE~/~RESET~); also elsewhere on the board
/~CS~_ADS: U401.18 (~CS); also elsewhere on the board
GNDA: C415.2, C416.2, C417.2, C418.2, C419.2, C420.2, J404.1, J405.1, J406.1, R409.1, R410.1, R411.1, R412.1, R413.1, R414.1, U401.10 (VREFN), U401.13 (AVSS); also elsewhere on the board
GNDD: C401.2, C402.2, C403.2, C404.2, C405.2, C406.2, C407.2, C408.2, R403.1, R405.1, U401.24 (DGND); also elsewhere on the board
unnamed: C401.1, U401.11 (VCAP1)
unnamed: C402.1, U401.27 (VCAP2)
unnamed: C403.1, C404.1, U401.9 (VREFP)
unnamed: C410.1, U401.1 (PGA1N)
unnamed: C410.2, U401.2 (PGA1P)
unnamed: C411.1, U401.8 (PGA2P)
unnamed: C411.2, U401.7 (PGA2N)
unnamed: J404.2, R410.2, R416.2
unnamed: J404.3, R409.2, R415.2
unnamed: J404.4, R406.1, U402.3 (-VIN)
unnamed: J405.2, R412.2, R418.2
unnamed: J405.3, R411.2, R417.2
unnamed: J405.4, R407.1, U403.3 (-VIN)
unnamed: J406.2, R414.2, R420.2
unnamed: J406.3, R413.2, R419.2
unnamed: J406.4, R408.1, U404.3 (-VIN)
unnamed: R406.2, U402.2 (R)
unnamed: R407.2, U403.2 (R)
unnamed: R408.2, U404.2 (R)
VDD: C405.1, C406.1, C407.1, C408.1, R404.1, U401.23 (DVDD); also elsewhere on the board
VDDA: U401.12 (AVDD), U402.1 (+VIN), U403.1 (+VIN), U404.1 (+VIN); also elsewhere on the board

Notes on the sheet:
FILTRO ANALOGICO ENTRADA 1
FILTRO ANALOGICO ENTRADA 2
FILTRO ANALOGICO ENTRADA 3
Desacople de la alimentacion del ADS1292. Poner los caps cerca de los pines de alimentacion.
DESACOPLE DE ADS1292
Asociación entre símbolos de la lib. POWER y etiquetas para más fácil lectura en pines muy cercanos

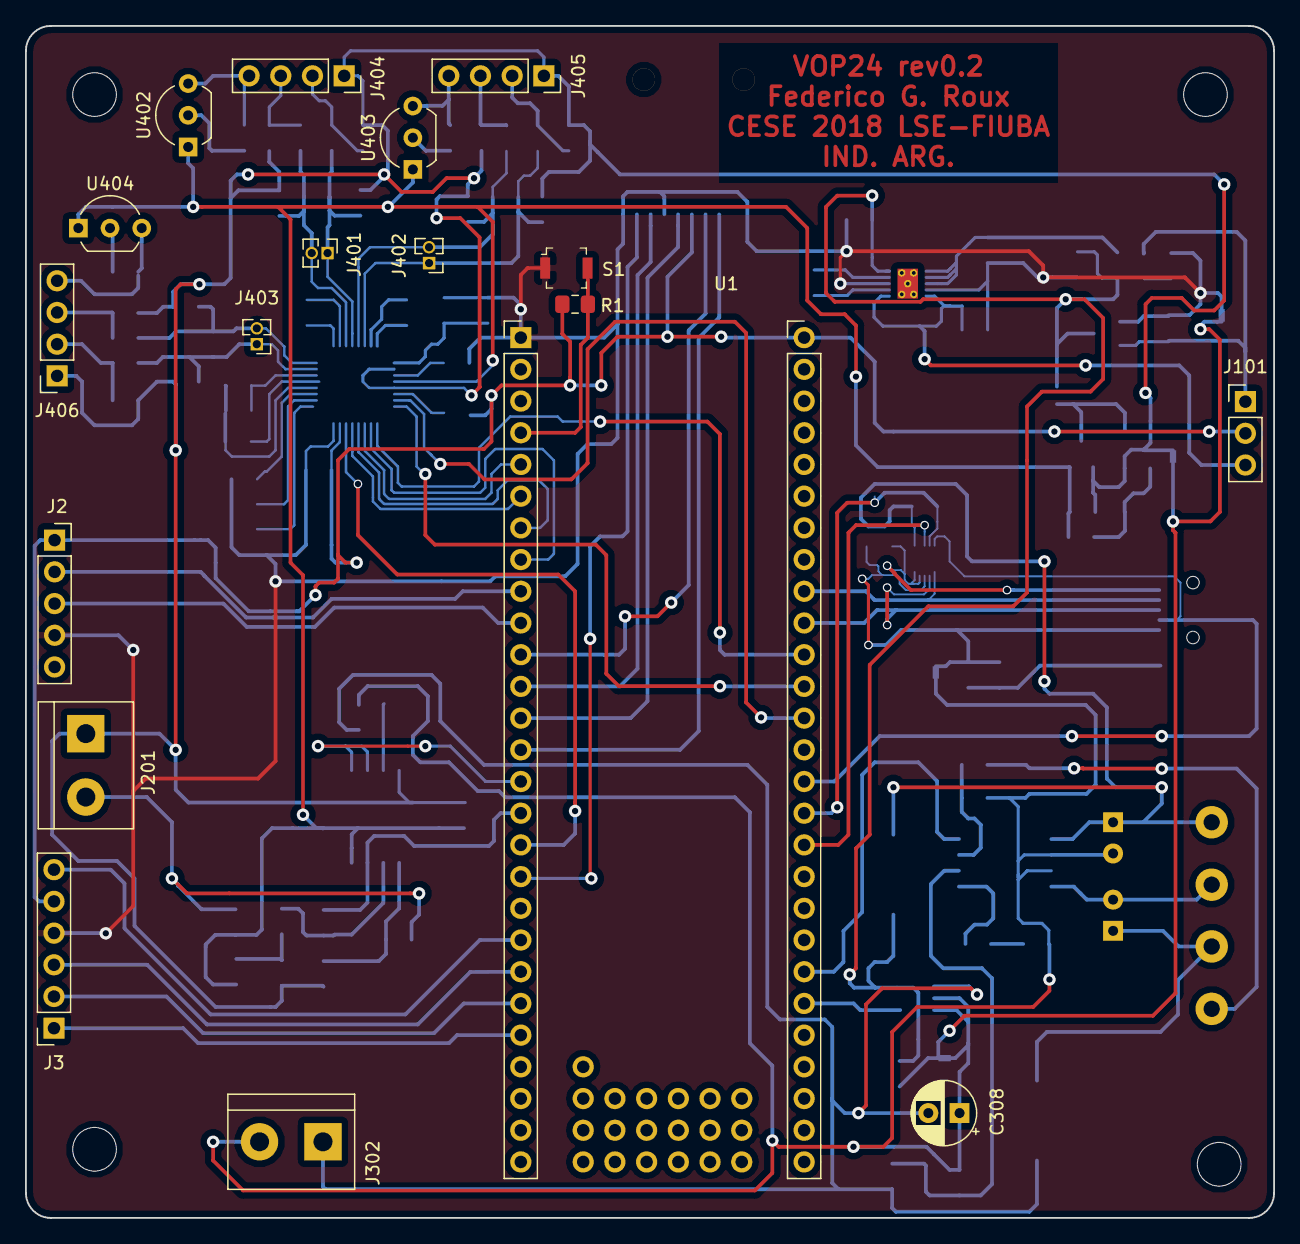
[picture p412: board vop24_lpcxpresso1769_basehw.kicad_pcb from above]

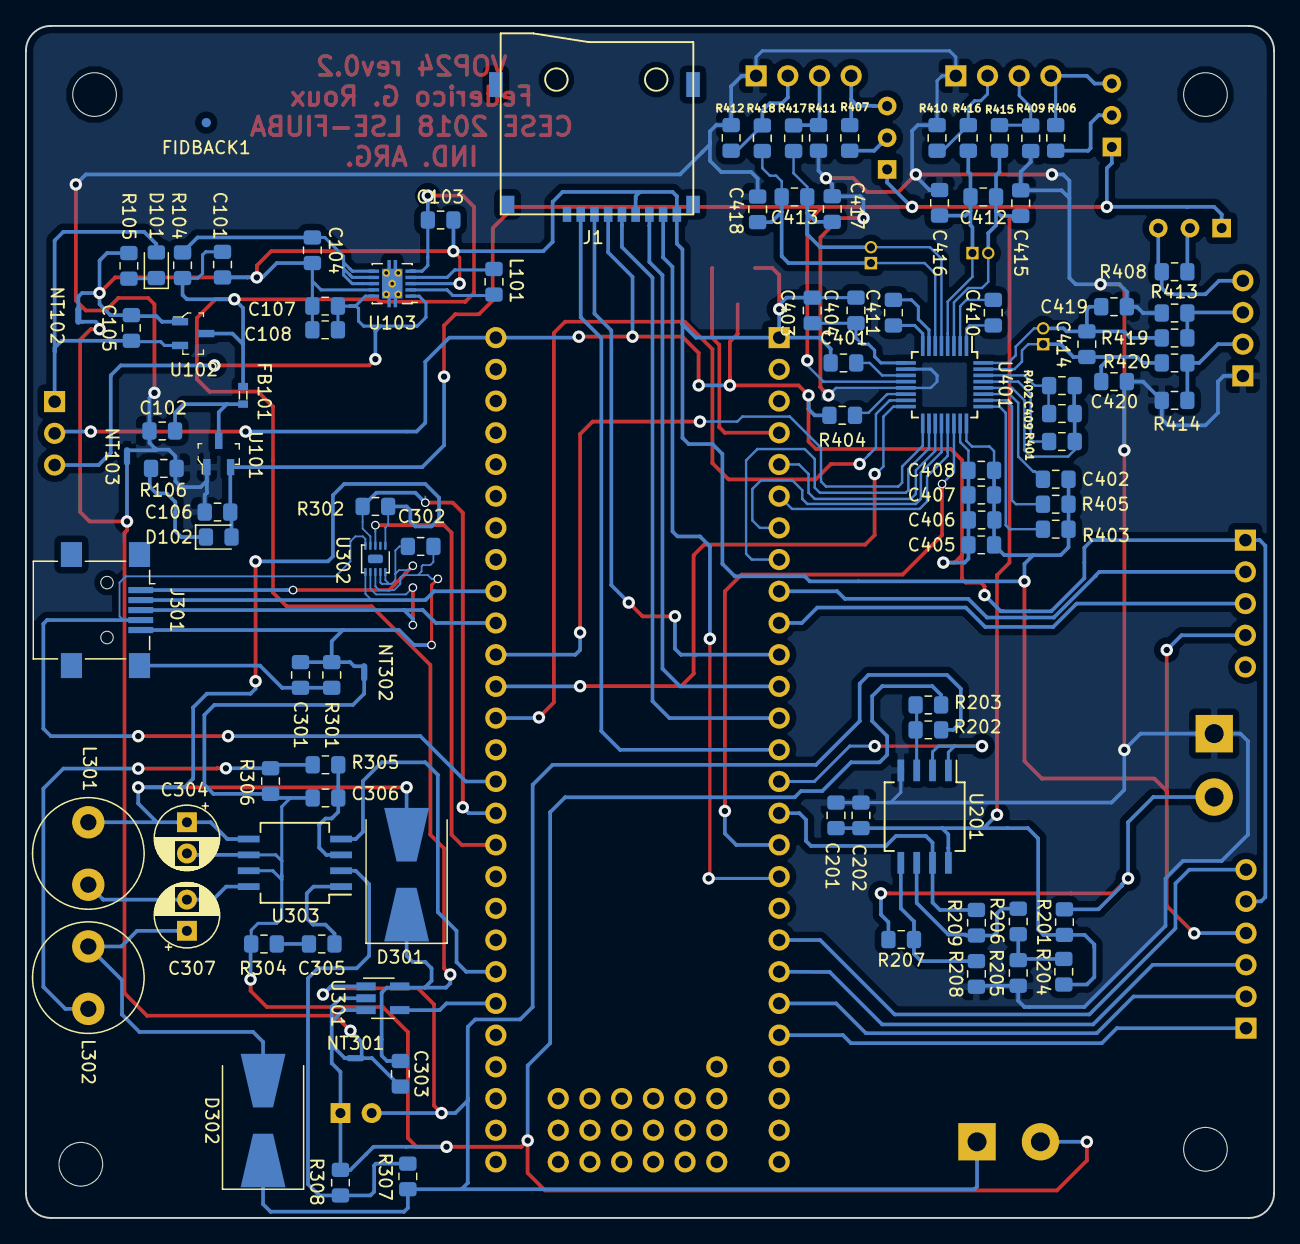
[picture p413: board vop24_lpcxpresso1769_basehw.kicad_pcb from below]

Board: 2 copper layers, 100.0 x 95.5 mm, 121 parts (99 on the bottom side), 92 nets.
