brengi/CESE-PCB/2018/Gavinowich/poncho_can.kicad_pcb

## KiCad design 2018/Gavinowich/poncho_can.kicad_pcb (2019-05-17)

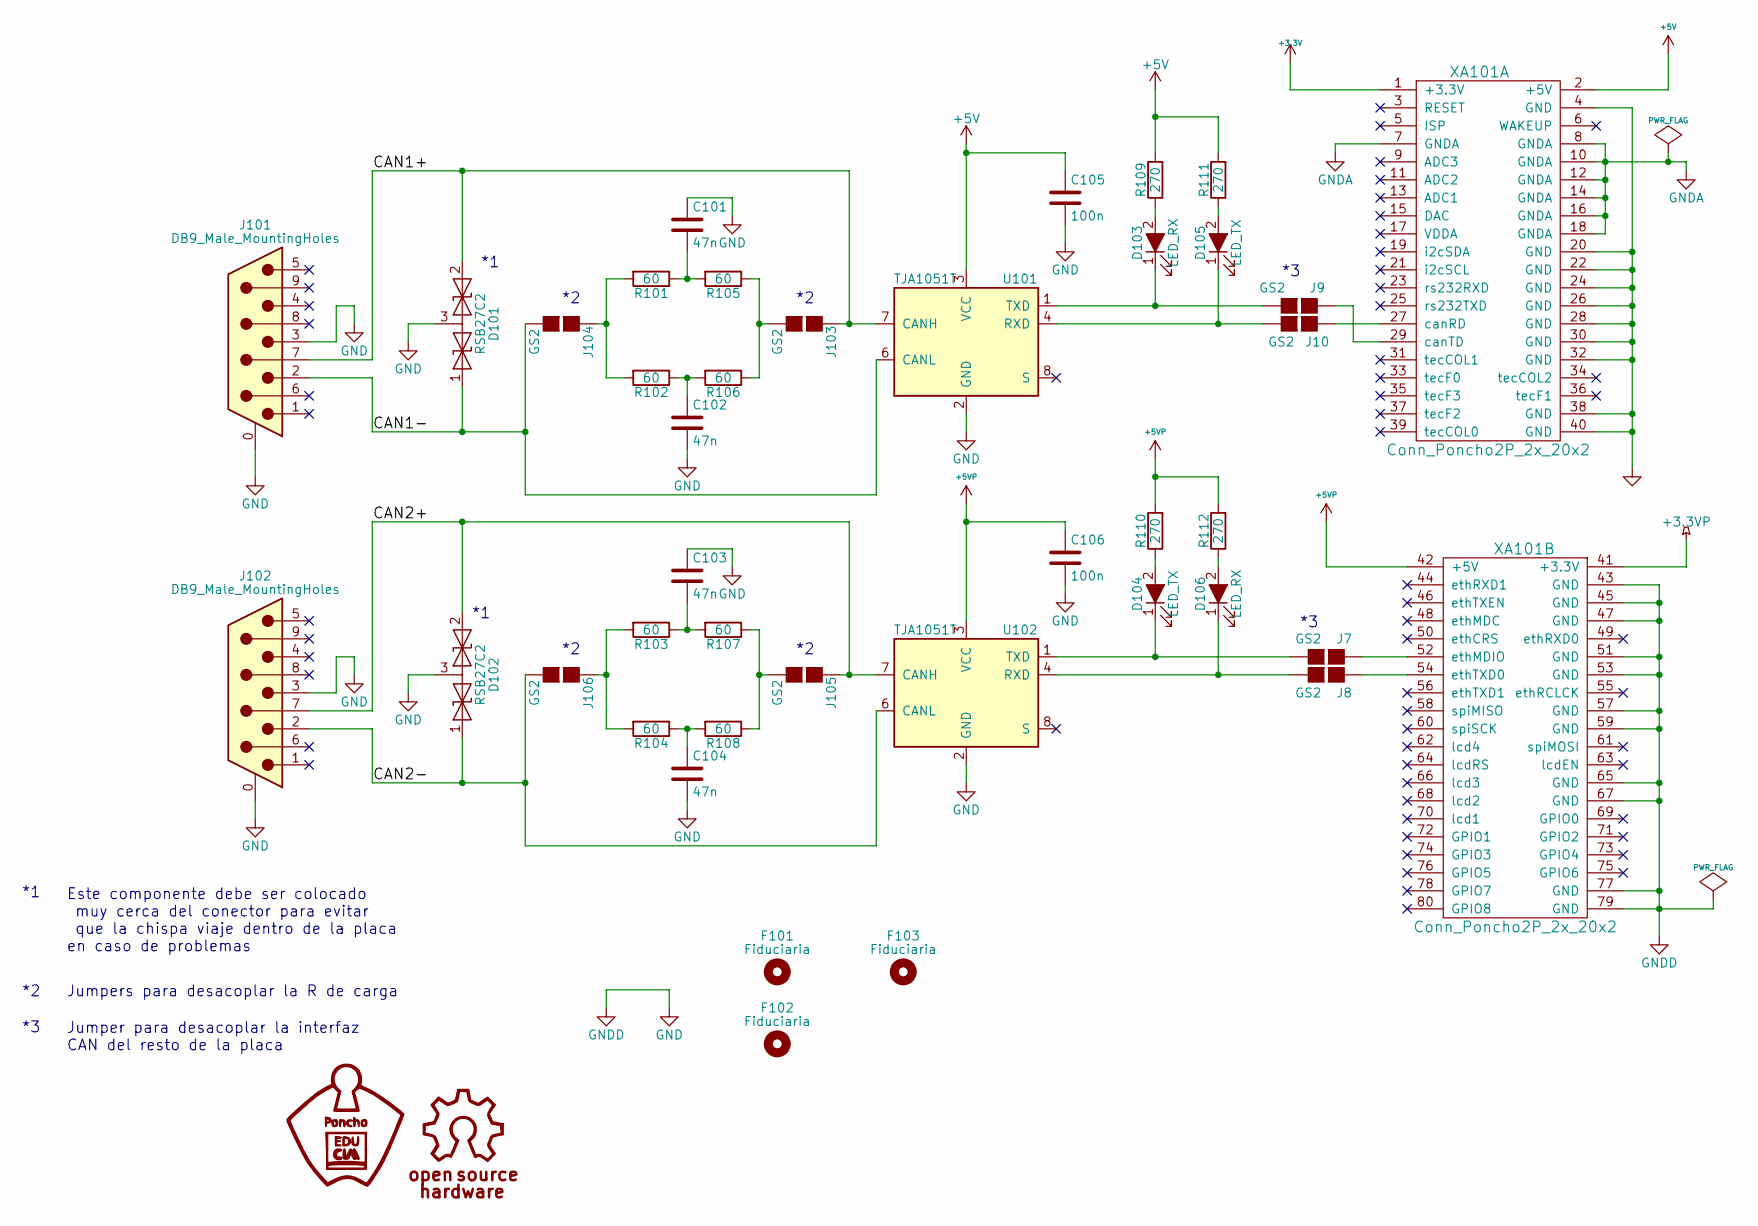
[picture p414: schematic poncho_can.sch, Poncho CAN]

Parts:
C101, C102, C103, C104: 47n; C_0805_HandSoldering; Digikey Part Number 490-7227-1-ND
C105, C106: 100n; C_0805_HandSoldering; Digikey Part Number 311-4354-1-ND
D101, D102: RSB27C2; SOT-23W_Handsoldering; Digikey Part Number ESD7002WTT1GOSCT-ND
D103, D106: LED_RX; LED_0805_HandSoldering; Digikey Part Number 160-1427-1-ND
D104, D105: LED_TX; LED_0805_HandSoldering; Digikey Part Number 160-1423-1-ND
F101, F102, F103: Fiduciaria; Fiducial_1mm_Dia_2.54mm_Outer_CopperBottom
J7, J8, J9, J10, J103, J104, J105, J106: GS2
J101, J102: DB9_Male_MountingHoles; DB9MC; Digikey Part Number 609-5183-ND
R101, R102, R103, R104, R105, R106, R107, R108: 60; R_0805_HandSoldering; Digikey Part Number RMCF0805FT60R4CT-ND
R109, R110, R111, R112: 270; R_0805_HandSoldering; Digikey Part Number RMCF0805JT270RCT-ND
U101, U102: TJA1051T; SOIC-8_3.9x4.9mm_Pitch1.27mm; Digikey Part Number 568-10292-1-ND
XA101: Conn_Poncho2P_2x_20x2; Conn_Poncho_SinBorde; Digikey# 952-1387-ND

Connections:
+3.3VP: XA101.41 (+3.3V)
+3V3: XA101.1 (+3.3V)
+5V: C105.1, R109.2, R111.2, U101.3 (VCC), XA101.2 (+5V)
+5VP: C106.1, R110.2, R112.2, U102.3 (VCC), XA101.42 (+5V)
/CAN1+: D101.2 (A2), J101.7, J103.1 (G1), U101.7 (CANH)
/CAN1-: D101.1 (A1), J101.2, J104.2 (G2), U101.6 (CANL)
/CAN2+: D102.2 (A2), J102.7, J105.1 (G1), U102.7 (CANH)
/CAN2-: D102.1 (A1), J102.2, J106.2 (G2), U102.6 (CANL)
GND: C101.1, C102.2, C103.1, C104.2, C105.2, C106.2, D101.3 (common), D102.3 (common), J101.0 (PAD), J101.3, J102.0 (PAD), J102.3, U101.2 (GND), U102.2 (GND), XA101.4 (GND), XA101.20 (GND), XA101.22 (GND), XA101.24 (GND), XA101.26 (GND), XA101.28 (GND), XA101.30 (GND), XA101.32 (GND), XA101.38 (GND), XA101.40 (GND), XA101.43 (GND), XA101.45 (GND), XA101.47 (GND), XA101.51 (GND), XA101.53 (GND), XA101.57 (GND), XA101.59 (GND), XA101.65 (GND), XA101.67 (GND), XA101.77 (GND), XA101.79 (GND)
GNDA: XA101.7 (GNDA), XA101.8 (GNDA), XA101.10 (GNDA), XA101.12 (GNDA), XA101.14 (GNDA), XA101.16 (GNDA), XA101.18 (GNDA)
unnamed: C101.2, R101.1, R105.2
unnamed: C102.1, R102.1, R106.2
unnamed: C103.2, R103.1, R107.2
unnamed: C104.1, R104.1, R108.2
unnamed: D103.1 (K), J9.2 (G2), U101.1 (TXD)
unnamed: D103.2 (A), R109.1
unnamed: D104.1 (K), J7.2 (G2), U102.1 (TXD)
unnamed: D104.2 (A), R110.1
unnamed: D105.1 (K), J10.2 (G2), U101.4 (RXD)
unnamed: D105.2 (A), R111.1
unnamed: D106.1 (K), J8.2 (G2), U102.4 (RXD)
unnamed: D106.2 (A), R112.1
unnamed: J7.1 (G1), XA101.52 (ethMDIO)
unnamed: J8.1 (G1), XA101.54 (ethTXD0)
unnamed: J9.1 (G1), XA101.29 (canTD)
unnamed: J10.1 (G1), XA101.27 (canRD)
unnamed: J103.2 (G2), R105.1, R106.1
unnamed: J104.1 (G1), R101.2, R102.2
unnamed: J105.2 (G2), R107.1, R108.1
unnamed: J106.1 (G1), R103.2, R104.2

Notes on the sheet:
Jumpers para desacoplar la R de carga
Jumper para desacoplar la interfaz CAN del resto de la placa
Este componente debe ser colocado muy cerca del conector para evitar que la chispa viaje dentro de la placa en caso de problemas

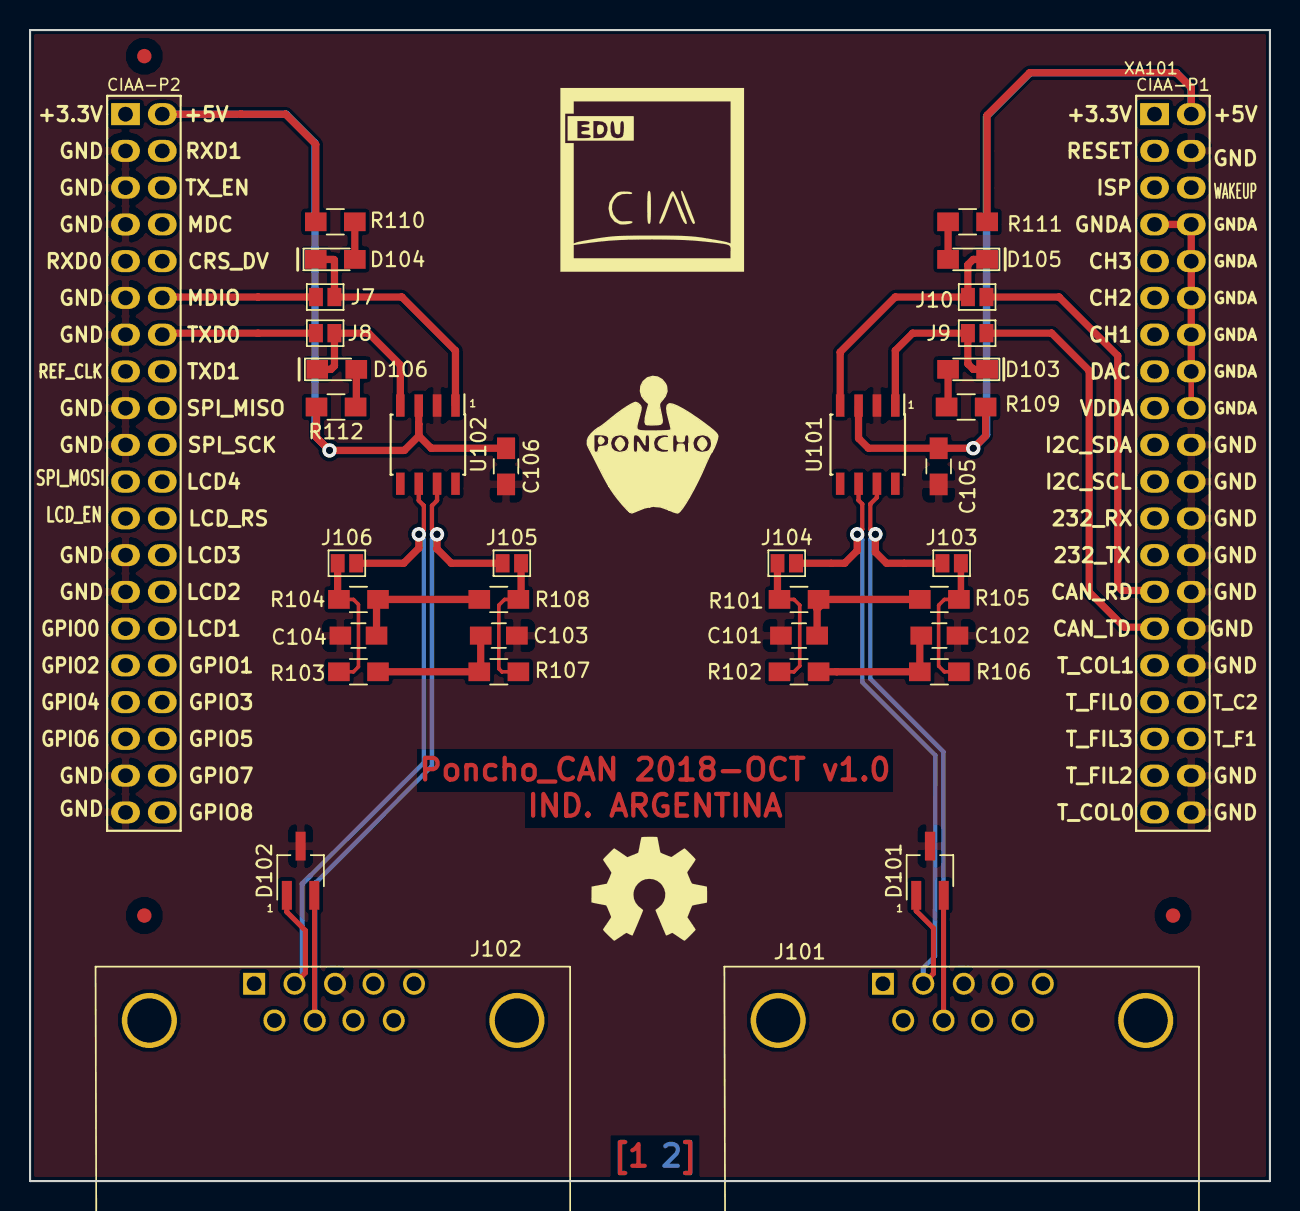
[picture p415: board poncho_can.kicad_pcb from above]

Board: 2 copper layers, 85.7 x 79.6 mm, 41 parts (0 on the bottom side), 28 nets.

Other parts of the board:
G101: Logo_OSHWA
