brengi/CESE-PCB/2018/Chavez/MMA7361/MMA7361.kicad_pcb

## KiCad design 2018/Chavez/MMA7361/MMA7361.kicad_pcb (2019-05-17)

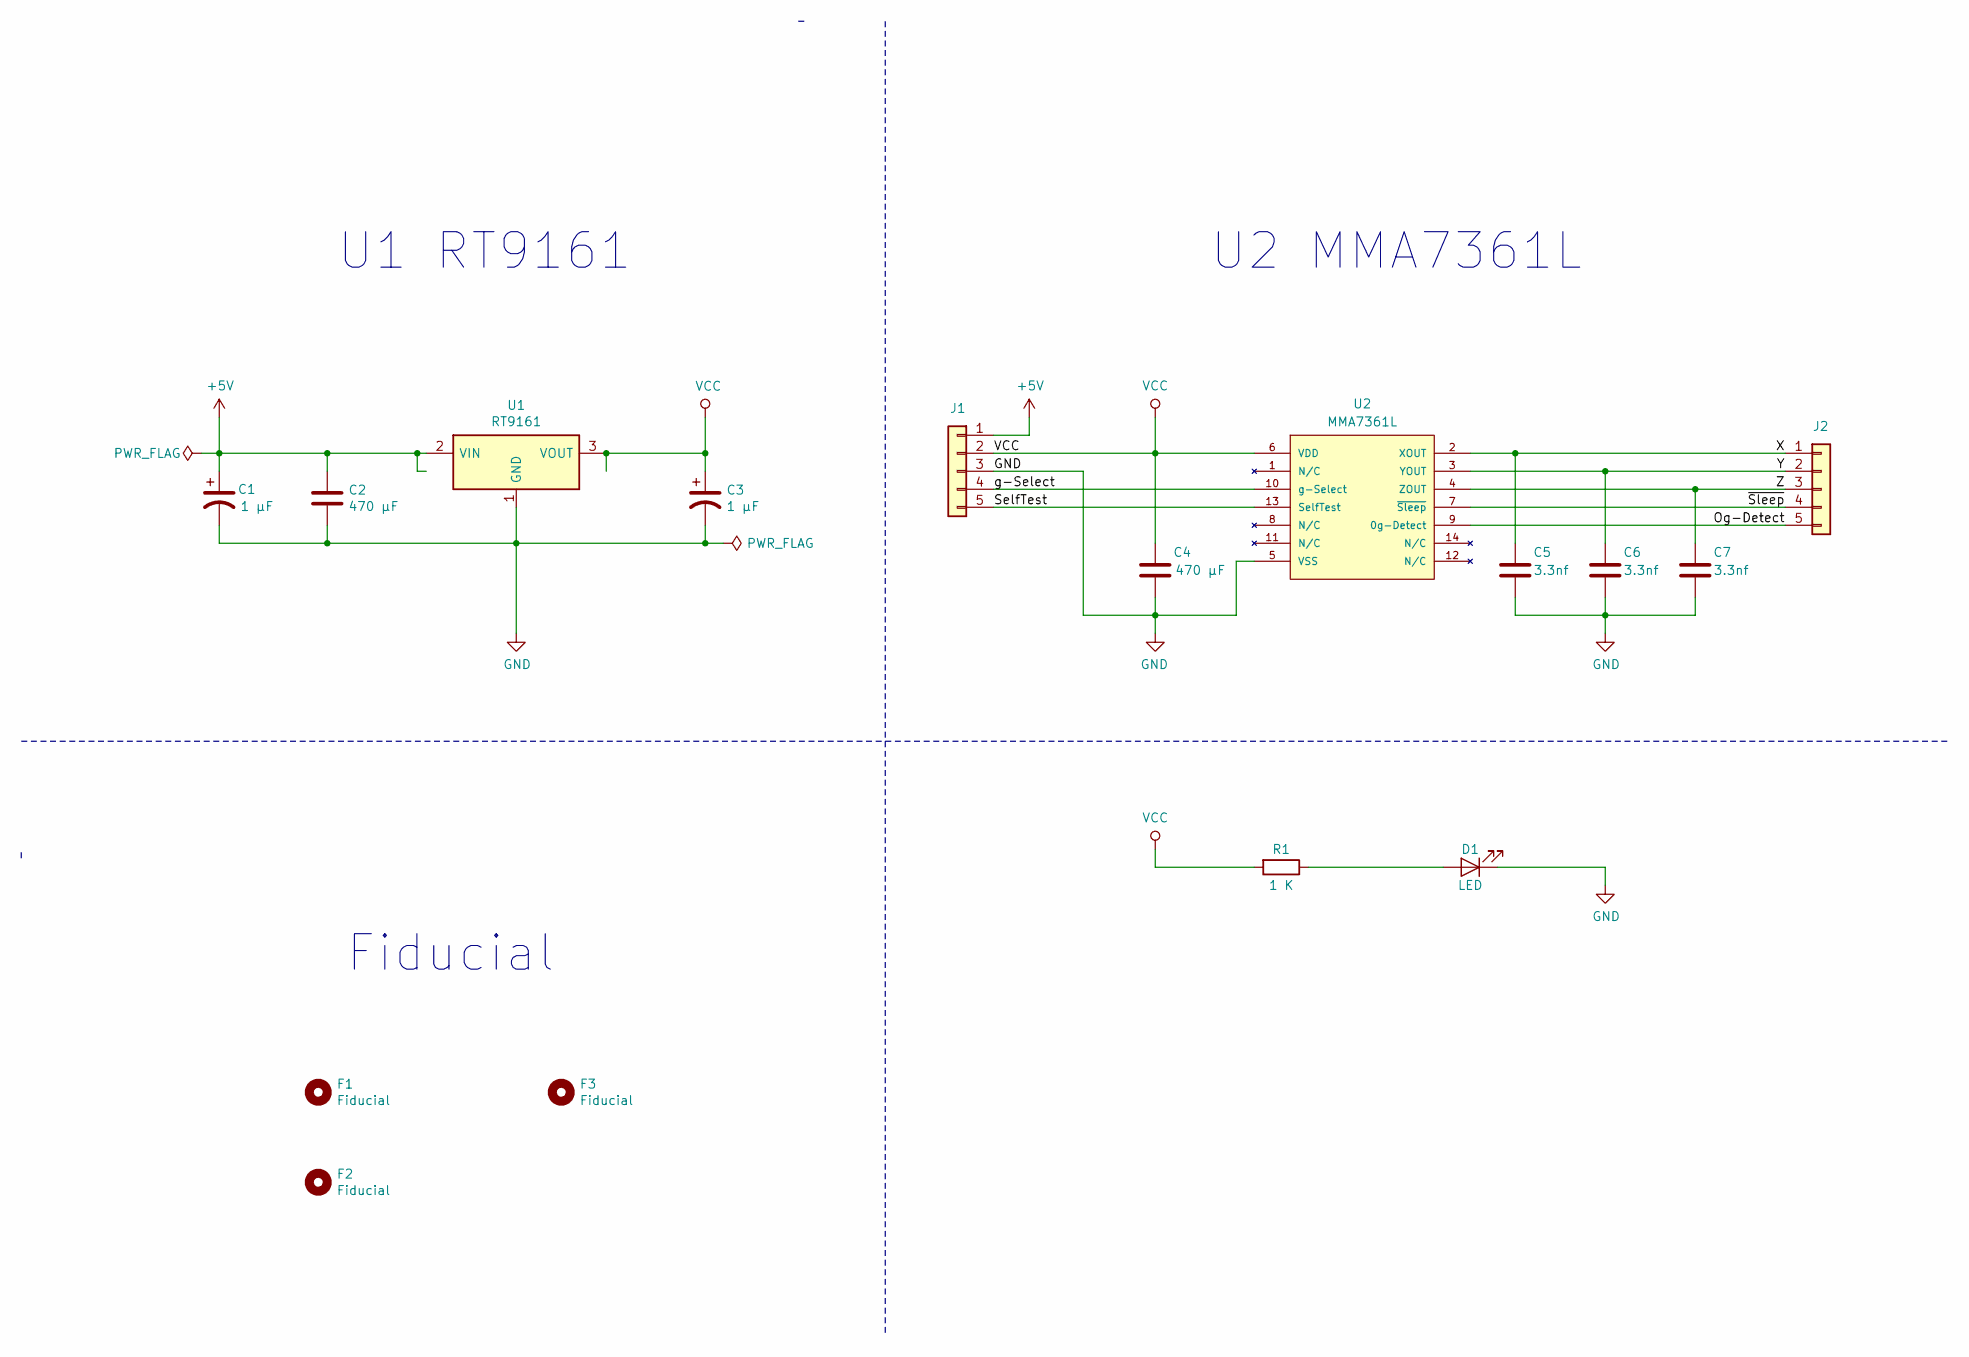
[picture p416: schematic MMA7361.sch, MMA7361 Module]

Parts:
C1, C3: 1 µF; C_0805_2012Metric_Pad1.15x1.40mm_HandSolder
C2, C4: 470 µF; C_0805_2012Metric_Pad1.15x1.40mm_HandSolder
C5, C6, C7: 3.3nf; C_0805_2012Metric_Pad1.15x1.40mm_HandSolder
D1: LED; LED_0805_2012Metric_Pad1.15x1.40mm_HandSolder
F1, F2, F3: Fiducial; Fiducial_1mm_Dia_2mm_Outer
J1, J2: Conn_01x05; PinHeader_1x05_P2.54mm_Vertical
R1: 1 K; R_0805_2012Metric_Pad1.15x1.40mm_HandSolder
U1: RT9161; SOT-89-3_Handsoldering
U2: MMA7361L; LGA-14_3x5mm_P0.8mm_LayoutBorder1x6y

Connections:
+5V: C1.1, C2.1, J1.1, U1.2 (VIN)
/Og-Detect: J2.5, U2.9 (0g-Detect)
/SelfTest: J1.5, U2.13 (SelfTest)
/X: C5.1, J2.1, U2.2 (XOUT)
/Y: C6.1, J2.2, U2.3 (YOUT)
/Z: C7.1, J2.3, U2.4 (ZOUT)
/g-Select: J1.4, U2.10 (g-Select)
/~Sleep: J2.4, U2.7 (~Sleep)
GND: C1.2, C2.2, C3.2, C4.2, C5.2, C6.2, C7.2, D1.1 (K), J1.3, U1.1 (GND), U2.5 (VSS)
unnamed: D1.2 (A), R1.1
VCC: C3.1, C4.1, J1.2, R1.2, U1.3 (VOUT), U2.6 (VDD)

Notes on the sheet:
U1 RT9161
U2 MMA7361L
Fiducial

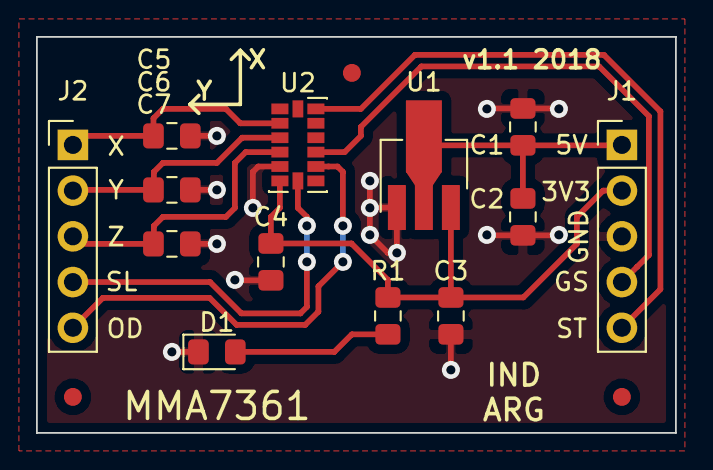
[picture p417: board MMA7361.kicad_pcb from above]

Board: 2 copper layers, 35.5 x 22.0 mm, 16 parts (0 on the bottom side), 11 nets.
