brengi/CESE-PCB/2018/Oliva/R_OlivaTPFinal/WEMB02_j/WEMB02_j/WEMB02_j.kicad_pcb

## KiCad design 2018/Oliva/R_OlivaTPFinal/WEMB02_j/WEMB02_j/WEMB02_j.kicad_pcb (2019-05-17)

Schematic: WEMB02_j.sch, WEMB02_j TPFinal R.Oliva / CESE2018

Parts:
F101, F102, F103: Fiducial; Fiducial_1mm_Dia_2mm_Outer
MH101, MH102, MH103, MH104: MH4mm; MountingHole_4mm

Notes on the sheet:
PLACA MADRE - WIND EMPOWERMENT WEMB02 CONTROL Y ALIMENTACION MÓDULOS DE POTENCIA PARA SOLAR / EOLICA REV. WEMB02J - R.OLIVA 8.12.2018

Schematic: datacomm.sch, WEMB02_j TPFinal R.Oliva / CESE2018

Parts:
C201, C203: 0.1uF 50V; C_0805_2012Metric_Pad1.15x1.40mm_HandSolder
C202: 4.7uF 50V MLCC; C_1210_3225Metric_Pad1.42x2.65mm_HandSolder
D201: CDSOT23-SM712; SOT-323_SC-70_Handsoldering
FR201: 1.5A; C_Disc_D4.3mm_W1.9mm_P5.00mm
J201: Conn_01x05; Molex_KK-254_AE-6410-05A_1x05_P2.54mm_Vertical
J202: RasPI_IO_Header; PinHeader_2x13_P2.54mm_Vertical
J203: RS485; TerminalBlock_bornier-3_P5.08mm
JP201: RX TO RBPI/ARD; PinHeader_1x03_P2.54mm_Vertical
JP202: TX_FROM RBPI/ARD; PinHeader_1x03_P2.54mm_Vertical
JP203: DIR_485 FROM RBPI/ARD; PinHeader_1x03_P2.54mm_Vertical
JP204: +3V3RBPI/+5VARD; PinHeader_1x03_P2.54mm_Vertical
JP205: TER; PinHeader_1x02_P2.54mm_Vertical
Q201: IRFR9024; TO-252-3_TabPin4
R201: 100K; R_0805_2012Metric_Pad1.15x1.40mm_HandSolder
R202: 1K; R_0805_2012Metric_Pad1.15x1.40mm_HandSolder
R203, R204, R205: 10K; R_0805_2012Metric_Pad1.15x1.40mm_HandSolder
R206, R207: 47R; R_0805_2012Metric_Pad1.15x1.40mm_HandSolder
R208: 120R; R_0805_2012Metric_Pad1.15x1.40mm_HandSolder
TP201: +5VLtp; TestPoint_THTPad_D2.0mm_Drill1.0mm
TP202: GNDS; TestPoint_THTPad_D2.0mm_Drill1.0mm
U201: SN75HVD08; SOIC-8_3.9x4.9mm_P1.27mm
XA201: Arduino_Mega2560_Shield; arduino_mega_header

Connections:
+3V3: JP204.3; also elsewhere on the board
+5VL: C201.1, C202.1, J201.5, J202.2, J202.4, Q201.3, TP201.1, XA201.5, XA201.42, XA201.60
+5VP: FR201.1, JP204.1; also elsewhere on the board
/DataComm/B_OUT: D201.2, J203.2, R206.1, R208.2
/DataComm/D485_RBPI: J202.22, JP203.3
/DataComm/DIR_485_ARD: JP203.1, XA201.73
/DataComm/RESET_4D: J201.2, R202.1
/DataComm/RX1_DISP: J201.4, XA201.63
/DataComm/RX2_ARD: JP201.1, XA201.65
/DataComm/RX_TO_RBPI: J202.10, JP201.3
/DataComm/TX1_DISP: J201.3, XA201.64
/DataComm/TX2_ARD: JP202.1, XA201.66
/DataComm/TX_FROM_RBPI(TX0_14): J202.8, JP202.3
GNDS: C201.2, C202.2, C203.2, D201.3, J201.1, J202.9, J202.14, J202.20, J202.25, J203.3, R201.2, R203.2, R205.2, TP202.1, U201.5 (GND), XA201.6, XA201.7, XA201.25, XA201.43, XA201.83; also elsewhere on the board
unnamed: C203.1, JP204.2, R204.1, U201.8 (VCC)
unnamed: D201.1, J203.1, JP205.2, R207.1
unnamed: FR201.2, Q201.2
unnamed: JP201.2, R204.2, U201.1 (RO)
unnamed: JP202.2, R205.1, U201.4 (DI)
unnamed: JP203.2, R203.1, U201.2 (~RE), U201.3 (DE)
unnamed: JP205.1, R208.1
unnamed: Q201.1, R201.1
unnamed: R202.2, XA201.74
unnamed: R206.2, U201.7 (B)
unnamed: R207.2, U201.6 (A)

Notes on the sheet:
REVERSE POL & BACK-SUPP PROT.
TVS DUAL CDSOT23-SM712
GND B A
4D DISPLAY CONNECTOR TX1/RX1/RESET
ARD/RBPI RS485 SELECTORS JP301-303 1:2 ARDUINO 2:3 RBPI
RBPI STD CONN POWER +5V ISO & COMM PORT, DIR 3V3 TTL LEVEL (RBPI UNDER WEMB02)
TI SN75HVD08 RS485 5V/3.3V CONVERTER W/OUTPUT PROT. STD A,B,GND CONN
TERMINATION 120R RESISTOR - JP305 =ON
RS485 SUPPLY JP304 5V (1-2 JUMPER) FOR ARD 3V3 (2-3 JUMPER) FOR RBPI
ARDUINO MEGA2560 MONTAJE DEBAJO DE PLACA WEMB02
+5VL es +5VP luego de Q301, Reverse-Protection
MODULO CONTROL ARDUINO-MEGA
MODULO RS485
CONECTOR A RASPBERRY-PI

Schematic: power.sch, WEMB02_j TPFinal R.Oliva / CESE2018

Parts:
BAT(+)301: SCREW_TERM8191; Banana_Jack_1Pin
BAT(-)301: SCREW_TERM8191; Banana_Jack_1Pin
C301, C305: 0.1uF 50V MLCC; C_0805_2012Metric_Pad1.15x1.40mm_HandSolder
C302: 0.1uF 50V; C_0805_2012Metric_Pad1.15x1.40mm_HandSolder
C303, C306: 10uF 50V MLCC; C_1210_3225Metric_Pad1.42x2.65mm_HandSolder
C304: 10uF 50V; C_1210_3225Metric_Pad1.42x2.65mm_HandSolder
CR301: SMAJ70A
CR302: SMAJ15A; SMAJ70A
CR303: SMAJ05A; SMAJ70A
D301, D302, D303: +5V_F ON; LED_0805_2012Metric_Pad1.15x1.40mm_HandSolder
FR301: 2.7 A; C_Disc_D16.0mm_W5.0mm_P10.00mm
FR302: 1.5A; C_Disc_D4.3mm_W1.9mm_P5.00mm
J301: EXP_PWR; TerminalBlock_RND_205-00232_1x02_P5.08mm_Horizontal
JF301, JF302: Screw_Terminal_01x06; TerminalBlock_bornier-6_P5.08mm
JP301, JP304, JP305: Jumper_2_Open; PinHeader_1x02_P2.54mm_Vertical
JP302, JP303: MAN/-AUTO; PinHeader_1x03_P2.54mm_Vertical
Q301, Q302: BC817-40_215; BC817-40; MPN BC817-40,215; Digi-Key_PN 1727-2919-1-ND
R301, R305, R306: 10K; R_0805_2012Metric_Pad1.15x1.40mm_HandSolder
R302, R303: 5K; R_0805_2012Metric_Pad1.15x1.40mm_HandSolder
R304, R307: 100K; R_0805_2012Metric_Pad1.15x1.40mm_HandSolder
RV301: 10 K MT; PV36W103C01B00
TP_GND301: TP2; TestPoint_THTPad_D2.0mm_Drill1.0mm
U301: SDM30-125S; POWER_SDM1b
U302: FEEDER_BRD; Global_feeder
U303: R-78E3.3-0.5; Converter_DCDC_RECOM_R-78E-0.5_THT
U304: R-78E5.0-1.0; Converter_DCDC_RECOM_R-78E-0.5_THT

Connections:
+3V3: C303.1, U303.3 (OUT); also elsewhere on the board
+5F: C306.1, CR303.1, JF301.2, JF301.5, JF302.2, JF302.5, JP304.1, U304.3 (OUT)
+5VP: C301.1, C302.2, FR302.2, JP305.1, U301.6, U303.1 (IN); also elsewhere on the board
+15V: C304.1, C305.1, CR302.1, JF301.1, JF301.4, JF302.1, JF302.4, JP301.1, R307.2, U301.1, U302.4, U304.1 (IN)
+BATT: BAT(+)301.1, FR301.2; also elsewhere on the board
/LowV_Detect/-FEED_SHDN: R305.1; also elsewhere on the board
/Power/+B_FEED: CR301.1, FR301.1, R304.2, U302.1
/Power/-FSHDN: JP302.2, R304.1, U302.3
/Power/SDM1: R306.1; also elsewhere on the board
/Power/SDM_ON: JP303.2, R307.1, U301.4
Earth: BAT(-)301.1, C304.2, C305.2, C306.2, CR301.2, CR302.2, CR303.2, D301.1, D302.1, JF301.3, JF301.6, JF302.3, JF302.6, JP302.3, JP303.3, Q301.2, Q302.2, TP_GND301.1, U301.2, U302.2, U302.5, U304.2 (GND); also elsewhere on the board
GNDS: C301.2, C302.1, C303.2, D303.1, J301.2, RV301.1, U301.7, U303.2 (GND); also elsewhere on the board
unnamed: D301.2, R301.2
unnamed: D302.2, R302.2
unnamed: D303.2, R303.2
unnamed: FR302.1, J301.1
unnamed: JP301.2, R301.1
unnamed: JP302.1, Q301.3
unnamed: JP303.1, Q302.3
unnamed: JP304.2, R302.1
unnamed: JP305.2, R303.1
unnamed: Q301.1, R305.2
unnamed: Q302.1, R306.2
unnamed: RV301.2, RV301.3, U301.8

Notes on the sheet:
INPUTS FROM BATTERY
-SHDN de LM5576 SI OPEN: PULL UP INTERNO A ON LOW: SHUTDOWN MODE
SDM30-12S5 ISOLATED DC/DC CONV +5V OUT 5A MAX 2"X2" PCB PACKAGE (BOTTOM SIDE)
FEEDER BOARD J.ALINEI 2016
TO POWER MODULES
UP-TRIM +VOUT
70V TVS
15V TVS
5V TVS
JP FEEDER 1-2 LVD_AUTO 2-3 OFF ALL OPEN: ON
JP +5V ISO 1-2 LVD_AUTO 2-3 OFF ALL OPEN: ON
78E05 RECOM SWITCHING DC/DC CONV +5V OUT 1A MAX PTH
78E03.3 RECOM SWITCHING DC/DC CONV +3V3 OUT 0.5A MAX PTH
(+5V) GNDS
ENTRADA DESDE BATERIAS
MODULO FEEDER PRINCIPAL +15V
SALIDAS FEEDER PRINCIPAL Y EXPANSION
SUB MODULO FEEDER SALIDA +5V
MODULO ISO +5V/5A, +3V3 Y LED
LVD INPUT
FEEDER LEDs

Schematic: lvd.sch, WEMB02_j TPFinal R.Oliva / CESE2018

Parts:
C401: 0.1uF 50V; C_0805_2012Metric_Pad1.15x1.40mm_HandSolder
C402: 10uF 50V; EEE-1EA100WR
CR401: SMAJ15A; SMAJ70A
FR401: 0.25 A; C_Disc_D10.0mm_W2.5mm_P5.00mm
JP401: 48V; PinHeader_1x02_P2.54mm_Vertical
JP402: 24V; PinHeader_1x02_P2.54mm_Vertical
JP403: 12V; PinHeader_1x02_P2.54mm_Vertical
Q401: MMBTA42LT1G; SOT-23-3; MPN MMBTA42LT1G; Digi-Key_PN MMBTA42LT1GOSCT-ND
R401, R402, R406, R407: 10K; R_0805_2012Metric_Pad1.15x1.40mm_HandSolder
R403: 150K; R_0805_2012Metric_Pad1.15x1.40mm_HandSolder
R404: 56K; R_0805_2012Metric_Pad1.15x1.40mm_HandSolder
R405: 47K; R_0805_2012Metric_Pad1.15x1.40mm_HandSolder
RV401, RV402: 100 K MT; PV36W103C01B00
RV403, RV404: 10 K MT; PV36W103C01B00
TP401, TP402: TP1; TestPoint_Pad_D2.0mm
TP403, TP404, TP405: TP2; TestPoint_Pad_D2.0mm
U401: ICL7665ACSA+; ICL7665ACSA&plus_

Connections:
+BATT: FR401.2; also elsewhere on the board
/LowV_Detect/+B_LVD: C401.1, C402.1, CR401.1, JP403.2, Q401.2, R406.1, R407.1, RV403.1, RV403.2, RV404.1, RV404.2, TP405.1, U401.8
/LowV_Detect/-FEED_SHDN: R406.2, U401.1; also elsewhere on the board
/Power/SDM1: R407.2, U401.7; also elsewhere on the board
Earth: C401.2, C402.2, CR401.2, R401.2, R402.2, R405.2, U401.4; also elsewhere on the board
unnamed: FR401.1, JP401.1, JP402.1, JP403.1, Q401.3
unnamed: JP401.2, R403.1
unnamed: JP402.2, R404.1
unnamed: Q401.1, R403.2, R404.2, R405.1
unnamed: R401.1, RV401.1, TP401.1, U401.3
unnamed: R402.1, RV402.1, TP402.1, U401.6
unnamed: RV401.2, RV401.3, RV403.3, TP403.1, U401.2
unnamed: RV402.2, RV402.3, RV404.3, TP404.1, U401.5

Notes on the sheet:
LOW VOLTAGE DETECTOR - ICL7665 OUT1, OUT2 PROGRAMMABLE (SEE INSTRUCTIONS)
15V TVS
LOW VOLTAGE DETECTOR (DETECTOR DE BAJA TENSIÓN)
LOW VOLTAGE DETECTOR CIRCUIT - ICL7665
ACTIVE VOLTAGE DIVIDER FOR 12,24 OR 48 V SYSTEMS

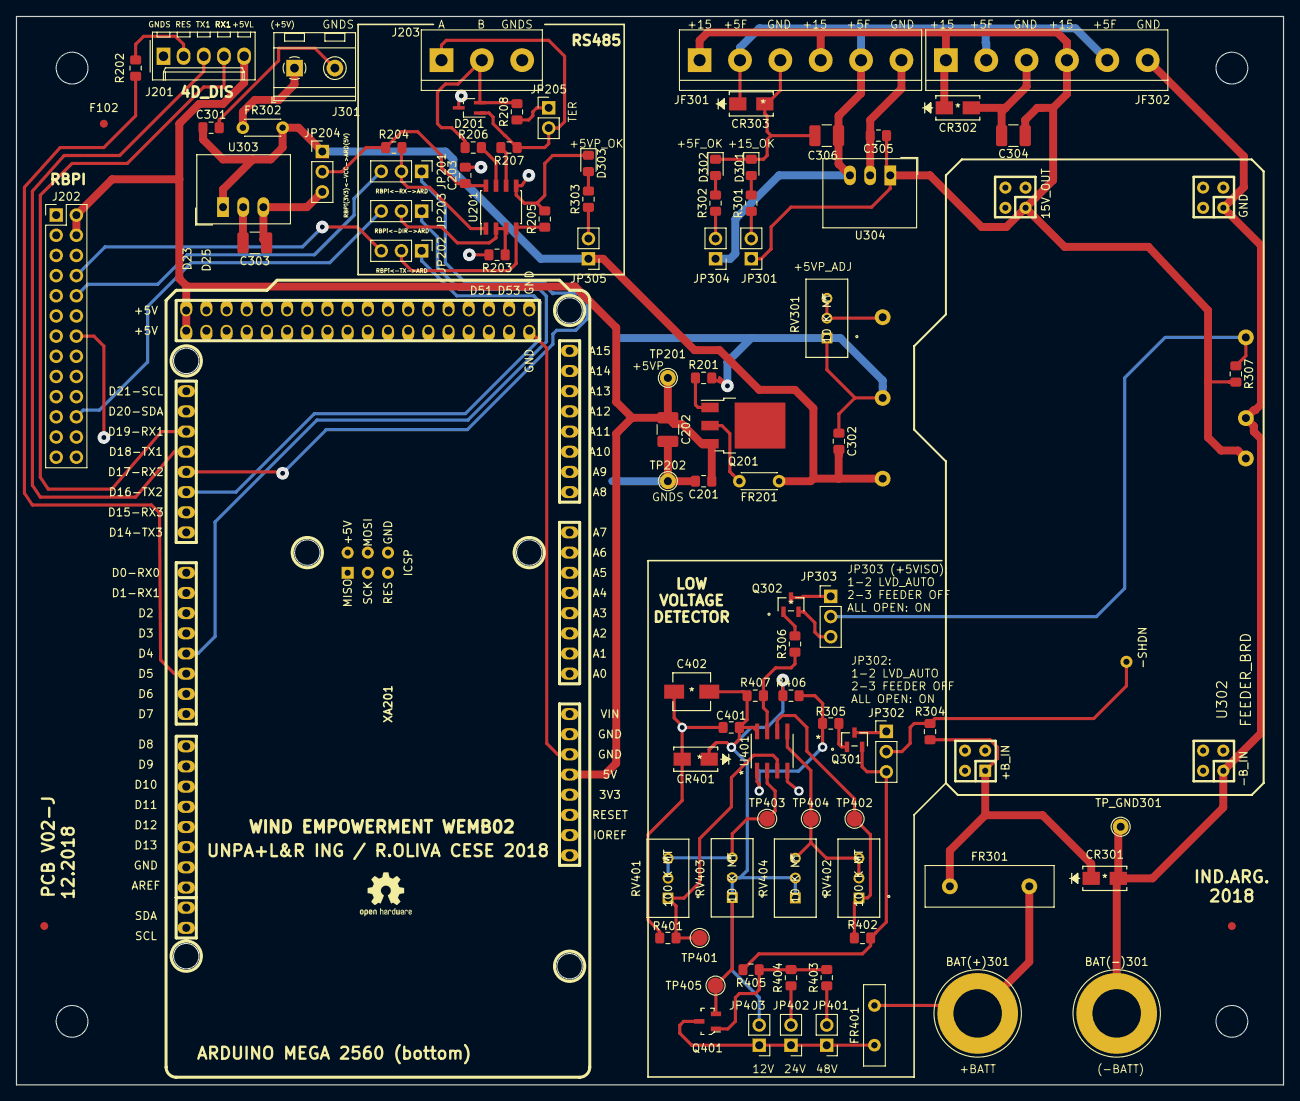
[picture p418: board WEMB02_j.kicad_pcb from above]

Board: 2 copper layers, 159.5 x 134.5 mm, 97 parts (1 on the bottom side), 55 nets.
