brengi/CESE-PCB/2018/Germino/retro-ciaa.kicad_pcb

## KiCad design 2018/Germino/retro-ciaa.kicad_pcb (2019-05-17)

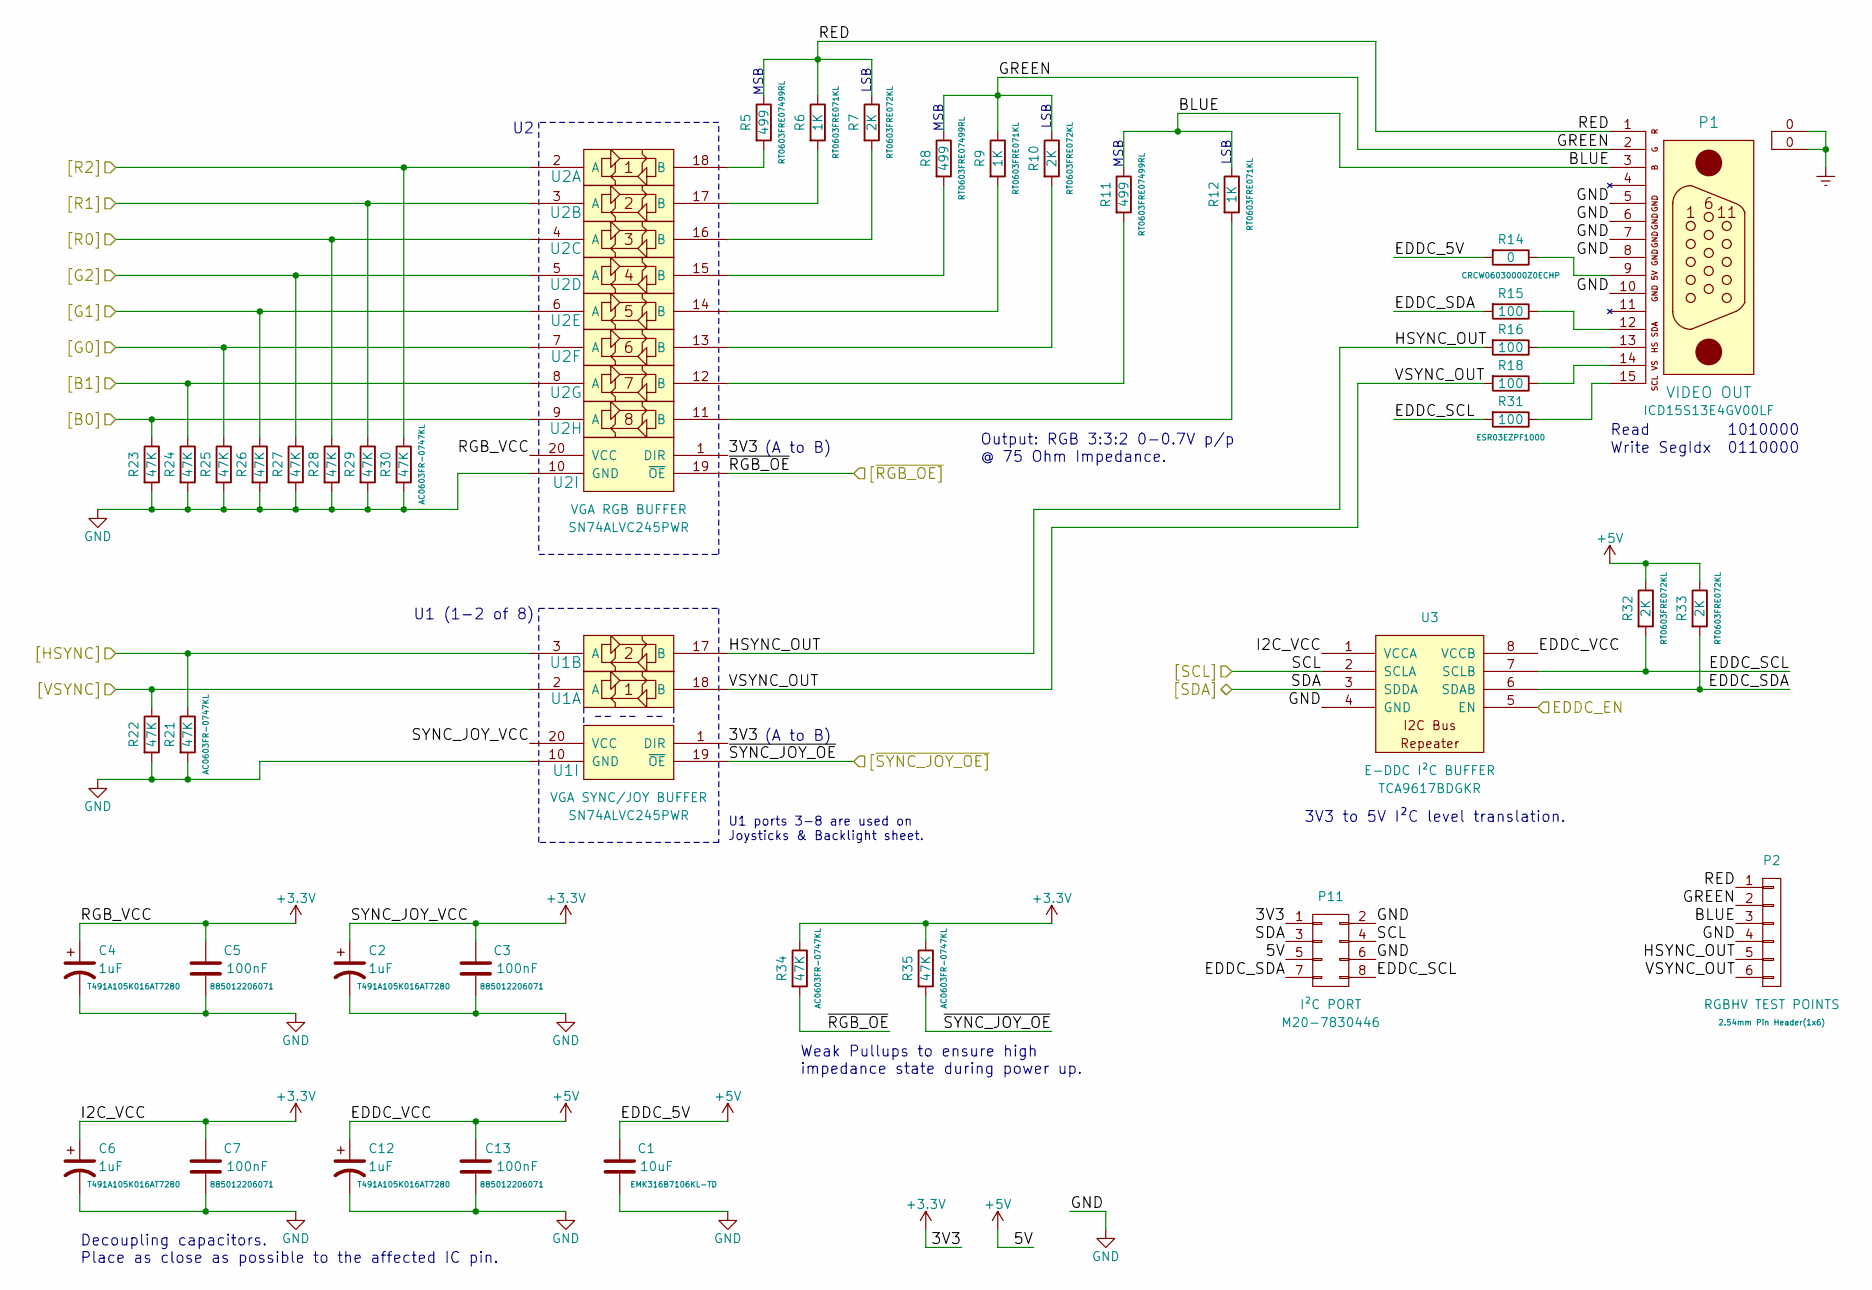
[picture p419: schematic video.sch, VIDEO OUTPUT]

Parts:
C1: 10uF; C_1206
C2, C4, C6, C12: 1uF; CP_Tantalum_Case-A_EIA-3216-18_Reflow
C3, C5, C7, C13: 100nF; C_0603
P1: VIDEO OUT; DSUB-15-HD_Female_Horizontal_Pitch2.29x1.98mm_EdgePinOffset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
P2: RGBHV TEST POINTS; Pin_Header_Straight_1x06_Pitch2.54mm
P11: I²C PORT; Pin_Header_Straight_2x04_Pitch2.54mm
R5, R8, R11: 499; R_0603
R6, R9, R12: 1K; R_0603
R7, R10, R32, R33: 2K; R_0603
R14: 0; R_0603
R15, R16, R18, R31: 100; R_0603
R21, R22, R23, R24, R25, R26, R27, R28, R29, R30, R34, R35: 47K; R_0603
U1: VGA SYNC/JOY BUFFER
U2: VGA RGB BUFFER
U3: E-DDC I²C BUFFER; VSSOP-8_3.0x3.0mm_Pitch0.65mm

Connections:
+3V3: C2.1, C3.2, C4.1, C5.2, C6.1, C7.2, P11.1, R34.1, R35.1, U1.1 (DIR), U1.20 (VCC), U2.1 (DIR), U2.20 (VCC), U3.1 (VCCA); also elsewhere on the board
+5V: C1.2, C12.1, C13.2, P11.5, R14.2, R32.1, R33.1, U3.8 (VCCB); also elsewhere on the board
/B0: R23.1, U2.9 (A); also elsewhere on the board
/B1: R24.1, U2.8 (A); also elsewhere on the board
/BLUE: P1.3, P2.3, R11.1, R12.1
/EDDC_EN: U3.5 (EN); also elsewhere on the board
/EDDC_SCL: P11.8, R31.2, R32.2, U3.7 (SCLB)
/EDDC_SDA: P11.7, R15.2, R33.2, U3.6 (SDAB)
/G0: R25.1, U2.7 (A); also elsewhere on the board
/G1: R26.1, U2.6 (A); also elsewhere on the board
/G2: R27.1, U2.5 (A); also elsewhere on the board
/GREEN: P1.2, P2.2, R8.1, R9.1, R10.1
/HSYNC: R21.1, U1.3 (A); also elsewhere on the board
/HSYNC_OUT: P2.5, R16.2, U1.17 (B)
/R0: R28.1, U2.4 (A); also elsewhere on the board
/R1: R29.1, U2.3 (A); also elsewhere on the board
/R2: R30.1, U2.2 (A); also elsewhere on the board
/RED: P1.1, P2.1, R5.1, R6.1, R7.1
/SCL: P11.4, U3.2 (SCLA); also elsewhere on the board
/SDA: P11.3, U3.3 (SDDA); also elsewhere on the board
/VSYNC: R22.1, U1.2 (A); also elsewhere on the board
/VSYNC_OUT: P2.6, R18.2, U1.18 (B)
/~RGB_OE: R34.2, U2.19 (~OE); also elsewhere on the board
/~SYNC_JOY_OE: R35.2, U1.19 (~OE); also elsewhere on the board
Earth: P1.0; also elsewhere on the board
GND: C1.1, C2.2, C3.1, C4.2, C5.1, C6.2, C7.1, C12.2, C13.1, P1.5, P1.6, P1.7, P1.8, P1.10, P2.4, P11.2, P11.6, R21.2, R22.2, R23.2, R24.2, R25.2, R26.2, R27.2, R28.2, R29.2, R30.2, U1.10 (GND), U2.10 (GND), U3.4 (GND); also elsewhere on the board
unnamed: P1.9, R14.1
unnamed: P1.12, R15.1
unnamed: P1.13, R16.1
unnamed: P1.14, R18.1
unnamed: P1.15, R31.1
unnamed: R5.2, U2.18 (B)
unnamed: R6.2, U2.17 (B)
unnamed: R7.2, U2.16 (B)
unnamed: R8.2, U2.15 (B)
unnamed: R9.2, U2.14 (B)
unnamed: R10.2, U2.13 (B)
unnamed: R11.2, U2.12 (B)
unnamed: R12.2, U2.11 (B)

Notes on the sheet:
1010000
0110000
Write SegIdx
Read
MSB
LSB
Output: RGB 3:3:2 0-0.7V p/p @ 75 Ohm Impedance.
(A to B)
3V3 to 5V I²C level translation.
Weak Pullups to ensure high impedance state during power up.
Decoupling capacitors. Place as close as possible to the affected IC pin.
U1 (1-2 of 8)
U1 ports 3-8 are used on Joysticks & Backlight sheet.

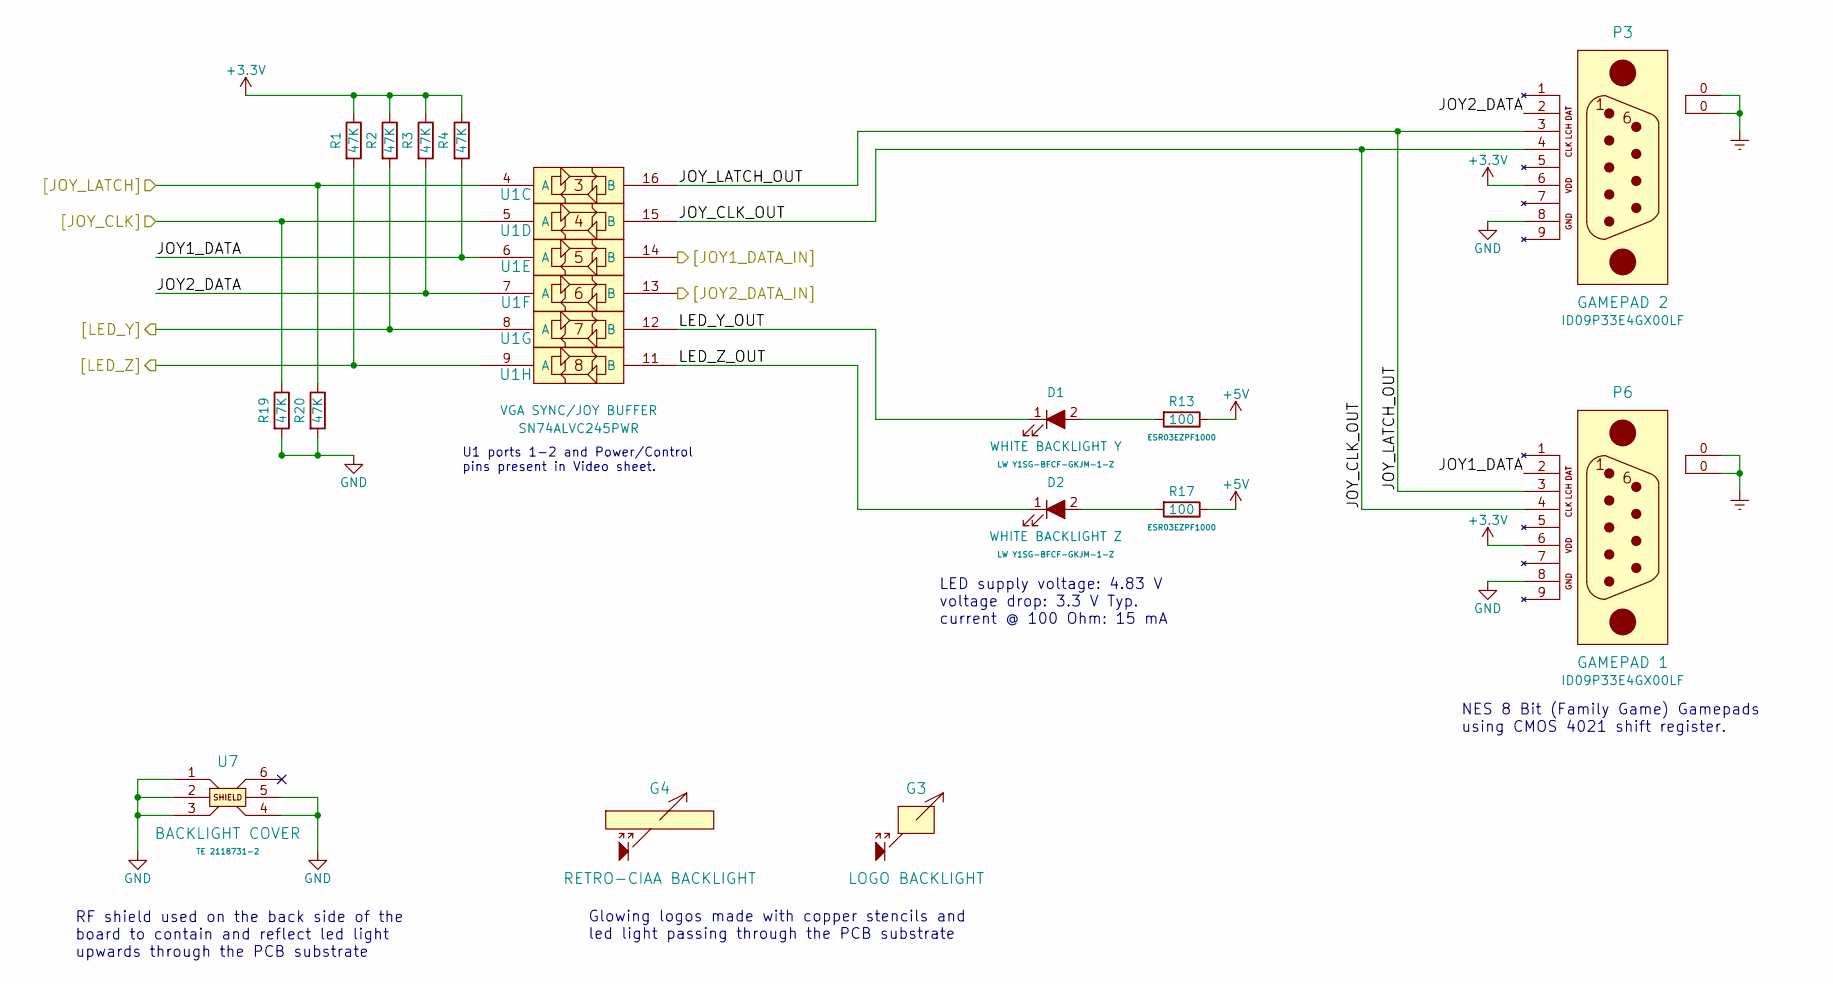
[picture p420: schematic joyled.sch, JOYSTICKS & BACKLIGHT]

Parts:
D1: WHITE BACKLIGHT Y; LED_LW_Y1SG
D2: WHITE BACKLIGHT Z; LED_LW_Y1SG
G3: LOGO BACKLIGHT; TREX_LOGO_BACK
G4: RETRO-CIAA BACKLIGHT; RETROCIAA_LOGO_BACK
P3: GAMEPAD 2; DSUB-9_Male_Horizontal_Pitch2.77x2.84mm_EdgePinOffset7.70mm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
P6: GAMEPAD 1; DSUB-9_Male_Horizontal_Pitch2.77x2.84mm_EdgePinOffset7.70mm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
R1, R2, R3, R4, R19, R20: 47K; R_0603
R13, R17: 100; R_0603
U1: VGA SYNC/JOY BUFFER
U7: BACKLIGHT COVER; TE_SHIELD_2118731-2

Connections:
+3V3: P3.6, P6.6, R1.1, R2.1, R3.1, R4.1; also elsewhere on the board
+5V: R13.1, R17.1; also elsewhere on the board
/JOY1_DATA: P6.2, R4.2, U1.6 (A)
/JOY1_DATA_IN: U1.14 (B); also elsewhere on the board
/JOY2_DATA: P3.2, R3.2, U1.7 (A)
/JOY2_DATA_IN: U1.13 (B); also elsewhere on the board
/JOY_CLK: R19.1, U1.5 (A); also elsewhere on the board
/JOY_CLK_OUT: P3.4, P6.4, U1.15 (B)
/JOY_LATCH: R20.1, U1.4 (A); also elsewhere on the board
/JOY_LATCH_OUT: P3.3, P6.3, U1.16 (B)
/LED_Y: R2.2, U1.8 (A); also elsewhere on the board
/LED_Y_OUT: D1.1 (K), U1.12 (B)
/LED_Z: R1.2, U1.9 (A); also elsewhere on the board
/LED_Z_OUT: D2.1 (K), U1.11 (B)
Earth: P3.0, P6.0; also elsewhere on the board
GND: P3.8, P6.8, R19.2, R20.2, U7.1, U7.2, U7.3, U7.4, U7.5; also elsewhere on the board
unnamed: D1.2 (A), R13.2
unnamed: D2.2 (A), R17.2

Notes on the sheet:
U1 ports 1-2 and Power/Control pins present in Video sheet.
NES 8 Bit (Family Game) Gamepads using CMOS 4021 shift register.
LED supply voltage: 4.83 V voltage drop: 3.3 V Typ. current @ 100 Ohm: 15 mA
RF shield used on the back side of the board to contain and reflect led light upwards through the PCB substrate
Glowing logos made with copper stencils and led light passing through the PCB substrate
