brengi/CESE-PCB/2018/Germino/retro-ciaa.kicad_pcb

## KiCad design 2018/Germino/retro-ciaa.kicad_pcb (continued)

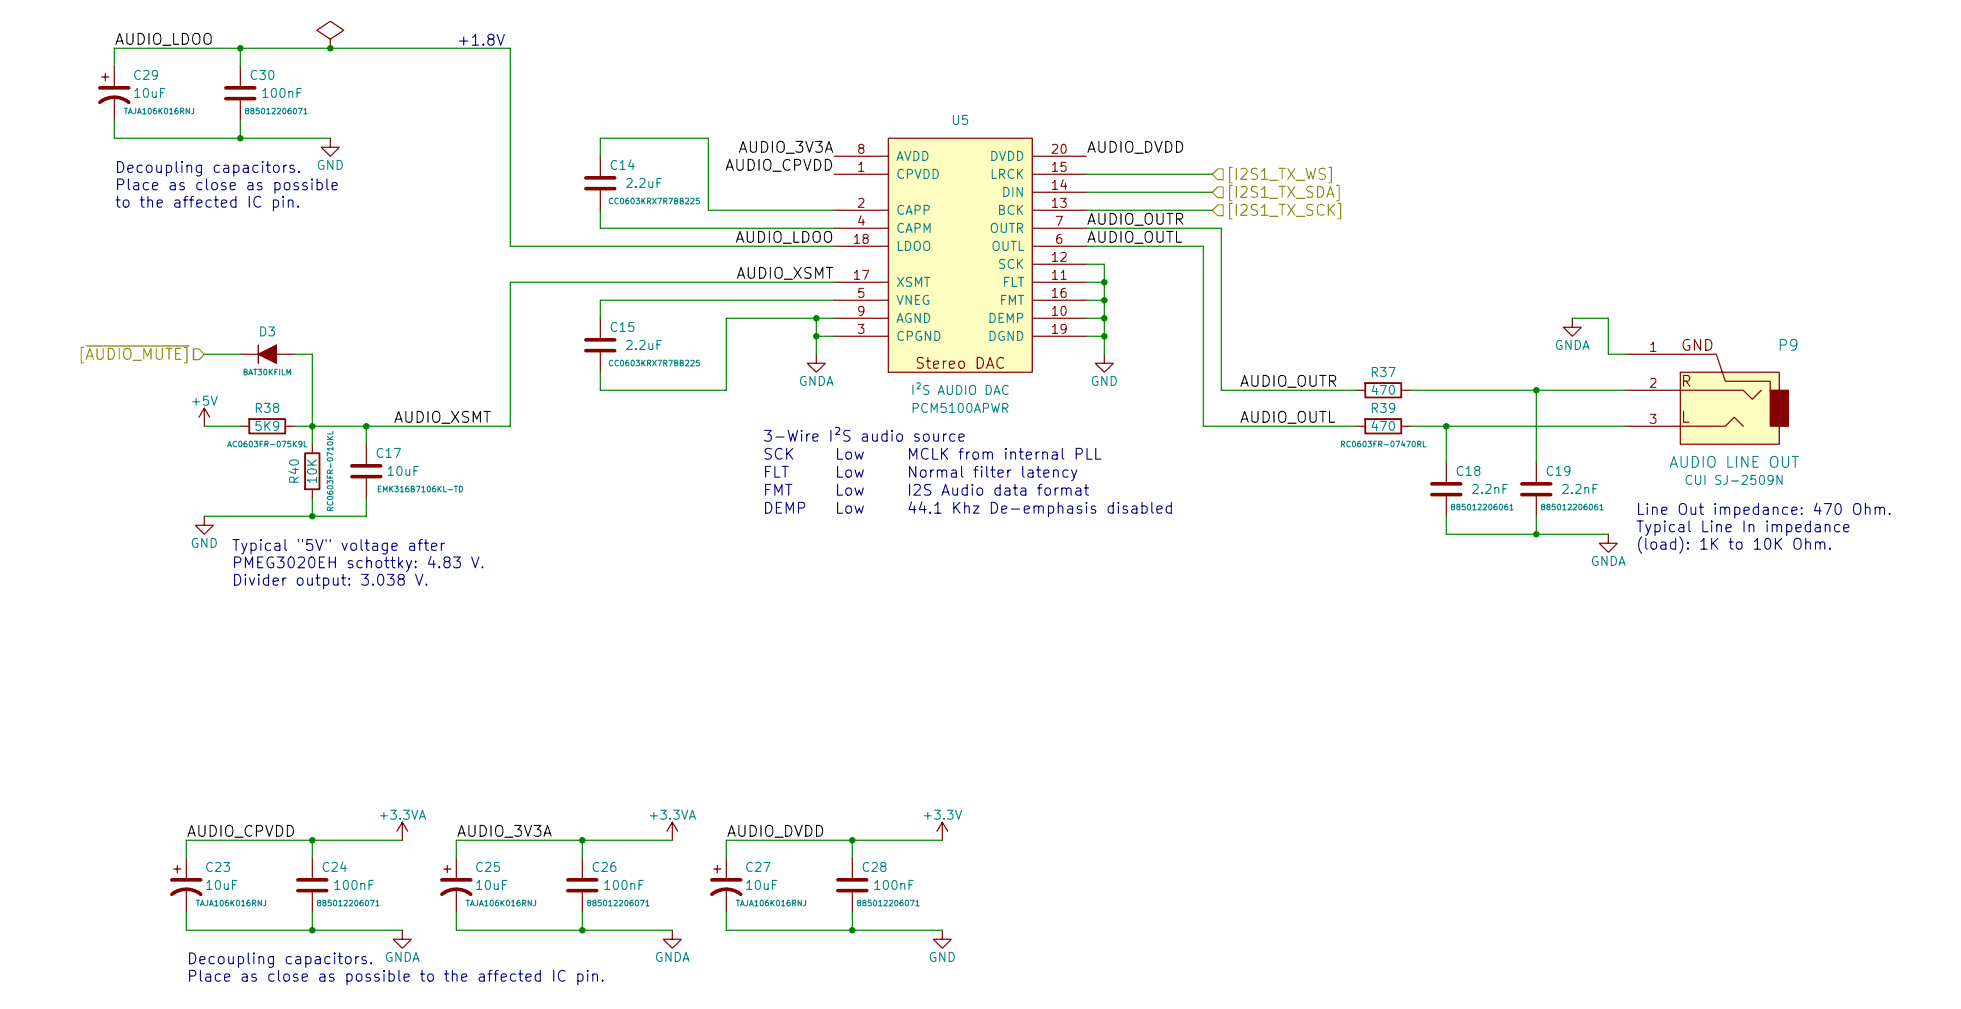
[picture p421: schematic audio.sch, AUDIO OUTPUT]

Parts:
C14, C15: 2.2uF; C_0603
C17: 10uF; C_1206
C18, C19: 2.2nF; C_0603
C23, C25, C27, C29: 10uF; CP_Tantalum_Case-A_EIA-3216-18_Reflow
C24, C26, C28, C30: 100nF; C_0603
D3: BAT30; D_SOD-523
P9: AUDIO LINE OUT; CUI_SJ-2509N
R37, R39: 470; R_0603
R38: 5K9; R_0603
R40: 10K; R_0603
U5: I²S AUDIO DAC; TSSOP-20_4.4x6.5mm_Pitch0.65mm

Connections:
+3.3VA: C23.1, C24.2, C25.1, C26.2, U5.1 (CPVDD), U5.8 (AVDD); also elsewhere on the board
+3V3: C27.1, C28.2, U5.20 (DVDD); also elsewhere on the board
+5V: R38.2; also elsewhere on the board
/AUDIO_LDOO: C29.1, C30.2, U5.18 (LDOO)
/AUDIO_OUTL: R39.2, U5.6 (OUTL)
/AUDIO_OUTR: R37.2, U5.7 (OUTR)
/AUDIO_XSMT: C17.2, D3.2 (A), R38.1, R40.1, U5.17 (XSMT)
/I2S1_TX_SCK: U5.13 (BCK); also elsewhere on the board
/I2S1_TX_SDA: U5.14 (DIN); also elsewhere on the board
/I2S1_TX_WS: U5.15 (LRCK); also elsewhere on the board
/~AUDIO_MUTE: D3.1 (K); also elsewhere on the board
GND: C17.1, C27.2, C28.1, C29.2, C30.1, R40.2, U5.10 (DEMP), U5.11 (FLT), U5.12 (SCK), U5.16 (FMT), U5.19 (DGND); also elsewhere on the board
GNDA: C15.1, C18.1, C19.1, C23.2, C24.1, C25.2, C26.1, P9.1, U5.3 (CPGND), U5.9 (AGND); also elsewhere on the board
unnamed: C14.1, U5.4 (CAPM)
unnamed: C14.2, U5.2 (CAPP)
unnamed: C15.2, U5.5 (VNEG)
unnamed: C18.2, P9.3, R39.1
unnamed: C19.2, P9.2, R37.1

Notes on the sheet:
FLT
Low
Normal filter latency
FMT
I2S Audio data format
3-Wire I²S audio source
SCK
MCLK from internal PLL
DEMP
44.1 Khz De-emphasis disabled
Typical "5V" voltage after PMEG3020EH schottky: 4.83 V. Divider output: 3.038 V.
+1.8V
Line Out impedance: 470 Ohm. Typical Line In impedance (load): 1K to 10K Ohm.
Decoupling capacitors. Place as close as possible to the affected IC pin.
Decoupling capacitors. Place as close as possible to the affected IC pin.

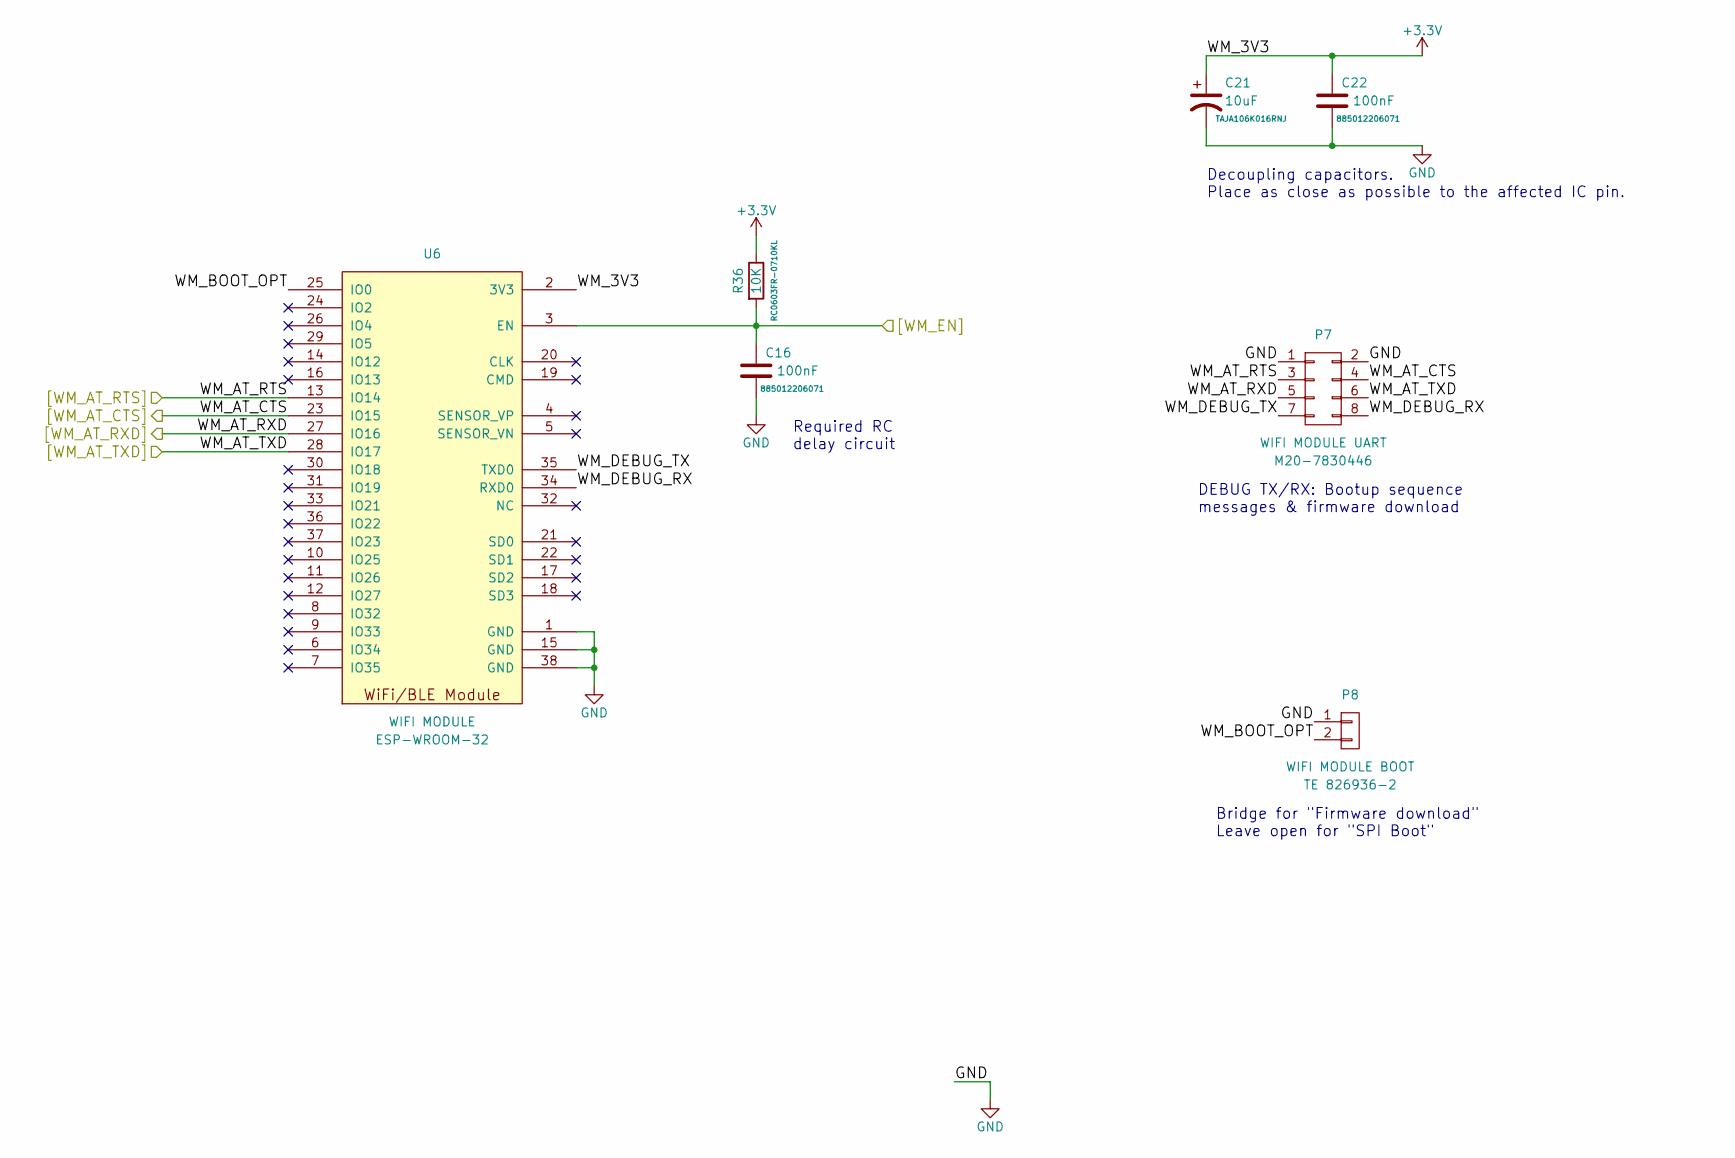
[picture p422: schematic wifi.sch, WI-FI & BLUETOOTH]

Parts:
C16, C22: 100nF; C_0603
C21: 10uF; CP_Tantalum_Case-A_EIA-3216-18_Reflow
P7: WIFI MODULE UART; Pin_Header_Straight_2x04_Pitch2.54mm
P8: WIFI MODULE BOOT; Pin_Header_Straight_1x02_Pitch2.54mm
R36: 10K; R_0603
U6: WIFI MODULE; ESP-WROOM-32

Connections:
+3V3: C21.1, C22.2, R36.1, U6.2 (3V3); also elsewhere on the board
/WM_AT_CTS: P7.4, U6.23 (IO15); also elsewhere on the board
/WM_AT_RTS: P7.3, U6.13 (IO14); also elsewhere on the board
/WM_AT_RXD: P7.5, U6.27 (IO16); also elsewhere on the board
/WM_AT_TXD: P7.6, U6.28 (IO17); also elsewhere on the board
/WM_BOOT_OPT: P8.2, U6.25 (IO0)
/WM_DEBUG_RX: P7.8, U6.34 (RXD0)
/WM_DEBUG_TX: P7.7, U6.35 (TXD0)
/WM_EN: C16.2, R36.2, U6.3 (EN); also elsewhere on the board
GND: C16.1, C21.2, C22.1, P7.1, P7.2, P8.1, U6.1 (GND), U6.15 (GND), U6.38 (GND); also elsewhere on the board

Notes on the sheet:
Bridge for "Firmware download" Leave open for "SPI Boot"
DEBUG TX/RX: Bootup sequence messages & firmware download
Required RC delay circuit
Decoupling capacitors. Place as close as possible to the affected IC pin.

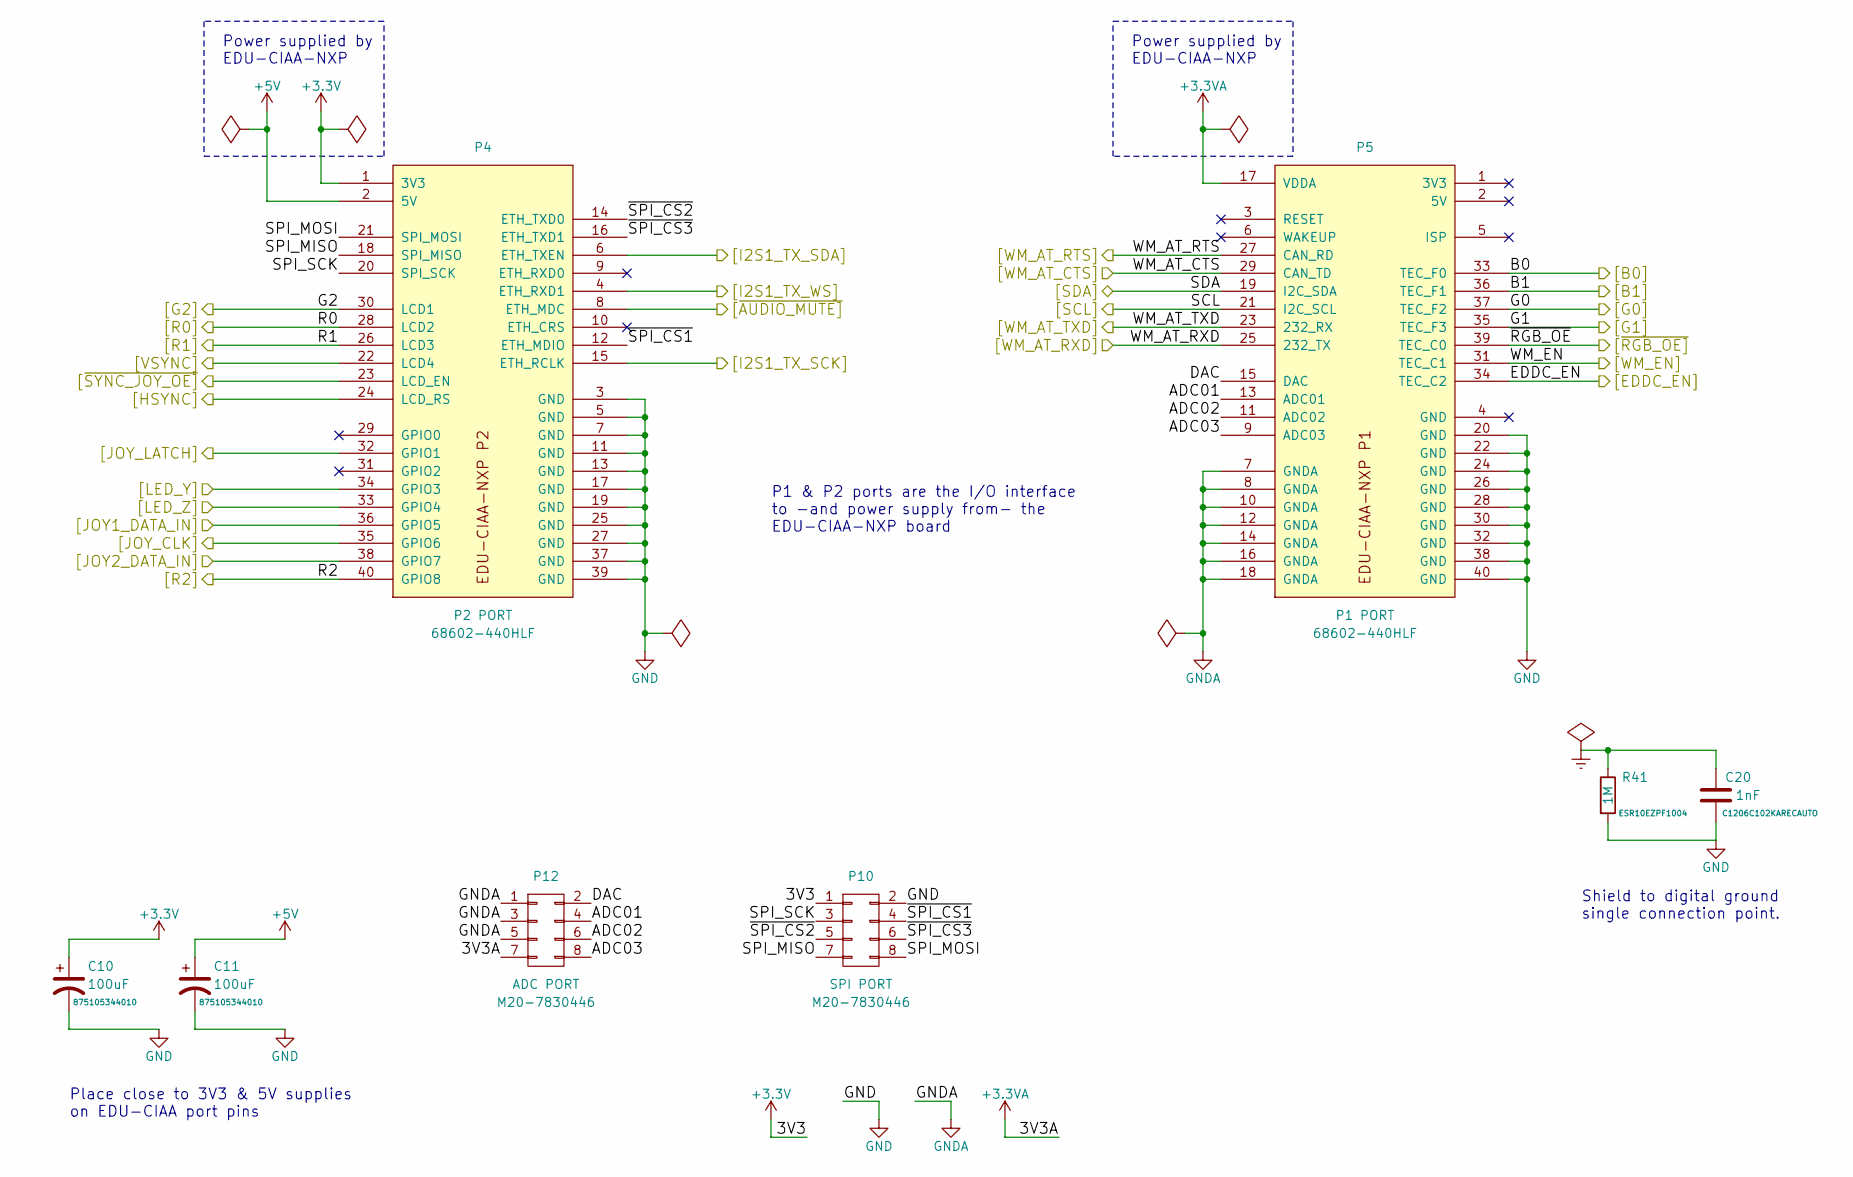
[picture p423: schematic educiaa.sch, EDU-CIAA-NXP INTERFACE]

Parts:
C10, C11: 100uF; CP_Elec_6.3x5.8
C20: 1nF; C_1206
P4: P2 PORT; Pin_Header_Back_2x20_Pitch2.54mm
P5: P1 PORT; Pin_Header_Back_2x20_Pitch2.54mm
P10: SPI PORT; Pin_Header_Straight_2x04_Pitch2.54mm
P12: ADC PORT; Pin_Header_Straight_2x04_Pitch2.54mm
R41: 1M; R_0805

Connections:
+3.3VA: P5.17 (VDDA), P12.7; also elsewhere on the board
+3V3: C10.1, P4.1 (3V3), P10.1; also elsewhere on the board
+5V: C11.1, P4.2 (5V); also elsewhere on the board
/ADC01: P5.13 (ADC01), P12.4
/ADC02: P5.11 (ADC02), P12.6
/ADC03: P5.9 (ADC03), P12.8
/B0: P5.33 (TEC_F0); also elsewhere on the board
/B1: P5.36 (TEC_F1); also elsewhere on the board
/DAC: P5.15 (DAC), P12.2
/EDDC_EN: P5.34 (TEC_C2); also elsewhere on the board
/G0: P5.37 (TEC_F2); also elsewhere on the board
/G1: P5.35 (TEC_F3); also elsewhere on the board
/G2: P4.30 (LCD1); also elsewhere on the board
/HSYNC: P4.24 (LCD_RS); also elsewhere on the board
/I2S1_TX_SCK: P4.15 (ETH_RCLK); also elsewhere on the board
/I2S1_TX_SDA: P4.6 (ETH_TXEN); also elsewhere on the board
/I2S1_TX_WS: P4.4 (ETH_RXD1); also elsewhere on the board
/JOY1_DATA_IN: P4.36 (GPIO5); also elsewhere on the board
/JOY2_DATA_IN: P4.38 (GPIO7); also elsewhere on the board
/JOY_CLK: P4.35 (GPIO6); also elsewhere on the board
/JOY_LATCH: P4.32 (GPIO1); also elsewhere on the board
/LED_Y: P4.33 (GPIO4); also elsewhere on the board
/LED_Z: P4.34 (GPIO3); also elsewhere on the board
/R0: P4.28 (LCD2); also elsewhere on the board
/R1: P4.26 (LCD3); also elsewhere on the board
/R2: P4.40 (GPIO8); also elsewhere on the board
/SCL: P5.21 (I2C_SCL); also elsewhere on the board
/SDA: P5.19 (I2C_SDA); also elsewhere on the board
/SPI_MISO: P4.18 (SPI_MISO), P10.7
/SPI_MOSI: P4.21 (SPI_MOSI), P10.8
/SPI_SCK: P4.20 (SPI_SCK), P10.3
/VSYNC: P4.22 (LCD4); also elsewhere on the board
/WM_AT_CTS: P5.29 (CAN_TD); also elsewhere on the board
/WM_AT_RTS: P5.27 (CAN_RD); also elsewhere on the board
/WM_AT_RXD: P5.25 (232_TX); also elsewhere on the board
/WM_AT_TXD: P5.23 (232_RX); also elsewhere on the board
/WM_EN: P5.31 (TEC_C1); also elsewhere on the board
/~AUDIO_MUTE: P4.8 (ETH_MDC); also elsewhere on the board
/~RGB_OE: P5.39 (TEC_C0); also elsewhere on the board
/~SPI_CS1: P4.12 (ETH_MDIO), P10.4
/~SPI_CS2: P4.14 (ETH_TXD0), P10.5
/~SPI_CS3: P4.16 (ETH_TXD1), P10.6
/~SYNC_JOY_OE: P4.23 (LCD_EN); also elsewhere on the board
Earth: C20.2, R41.1; also elsewhere on the board
GND: C10.2, C11.2, C20.1, P4.3 (GND), P4.5 (GND), P4.7 (GND), P4.11 (GND), P4.13 (GND), P4.17 (GND), P4.19 (GND), P4.25 (GND), P4.27 (GND), P4.37 (GND), P4.39 (GND), P5.20 (GND), P5.22 (GND), P5.24 (GND), P5.26 (GND), P5.28 (GND), P5.30 (GND), P5.32 (GND), P5.38 (GND), P5.40 (GND), P10.2, R41.2; also elsewhere on the board
GNDA: P5.7 (GNDA), P5.8 (GNDA), P5.10 (GNDA), P5.12 (GNDA), P5.14 (GNDA), P5.16 (GNDA), P5.18 (GNDA), P12.1, P12.3, P12.5; also elsewhere on the board

Notes on the sheet:
Place close to 3V3 & 5V supplies on EDU-CIAA port pins
P1 & P2 ports are the I/O interface to -and power supply from- the EDU-CIAA-NXP board
Power supplied by EDU-CIAA-NXP
Shield to digital ground single connection point.

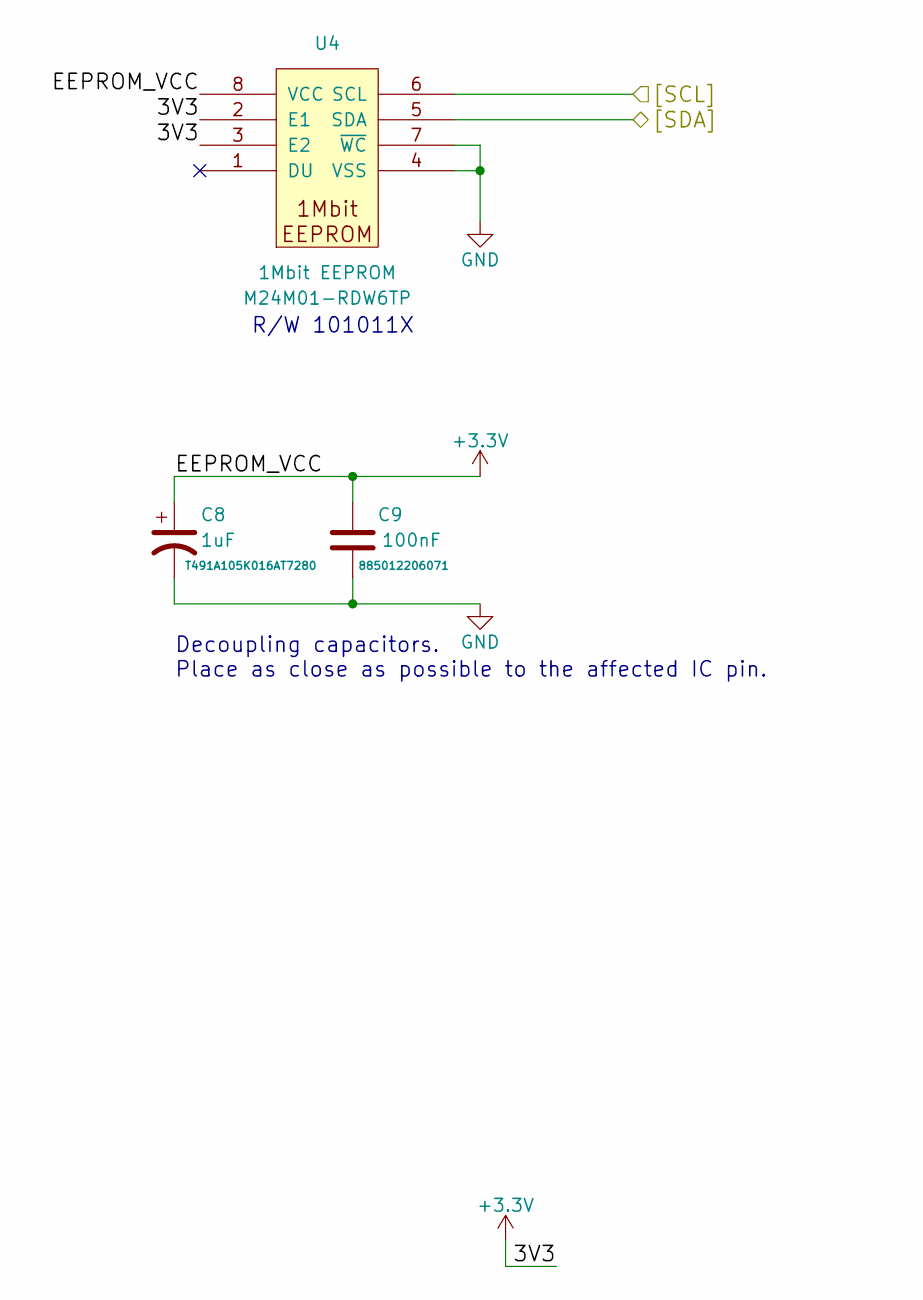
[picture p424: schematic storage.sch]

Parts:
C8: 1uF; CP_Tantalum_Case-A_EIA-3216-18_Reflow
C9: 100nF; C_0603
U4: 1Mbit EEPROM; TSSOP-8_4.4x3mm_Pitch0.65mm

Connections:
+3V3: C8.1, C9.2, U4.2 (E1), U4.3 (E2), U4.8 (VCC); also elsewhere on the board
/SCL: U4.6 (SCL); also elsewhere on the board
/SDA: U4.5 (SDA); also elsewhere on the board
GND: C8.2, C9.1, U4.4 (VSS), U4.7 (~WC); also elsewhere on the board

Notes on the sheet:
R/W 101011X
Decoupling capacitors. Place as close as possible to the affected IC pin.

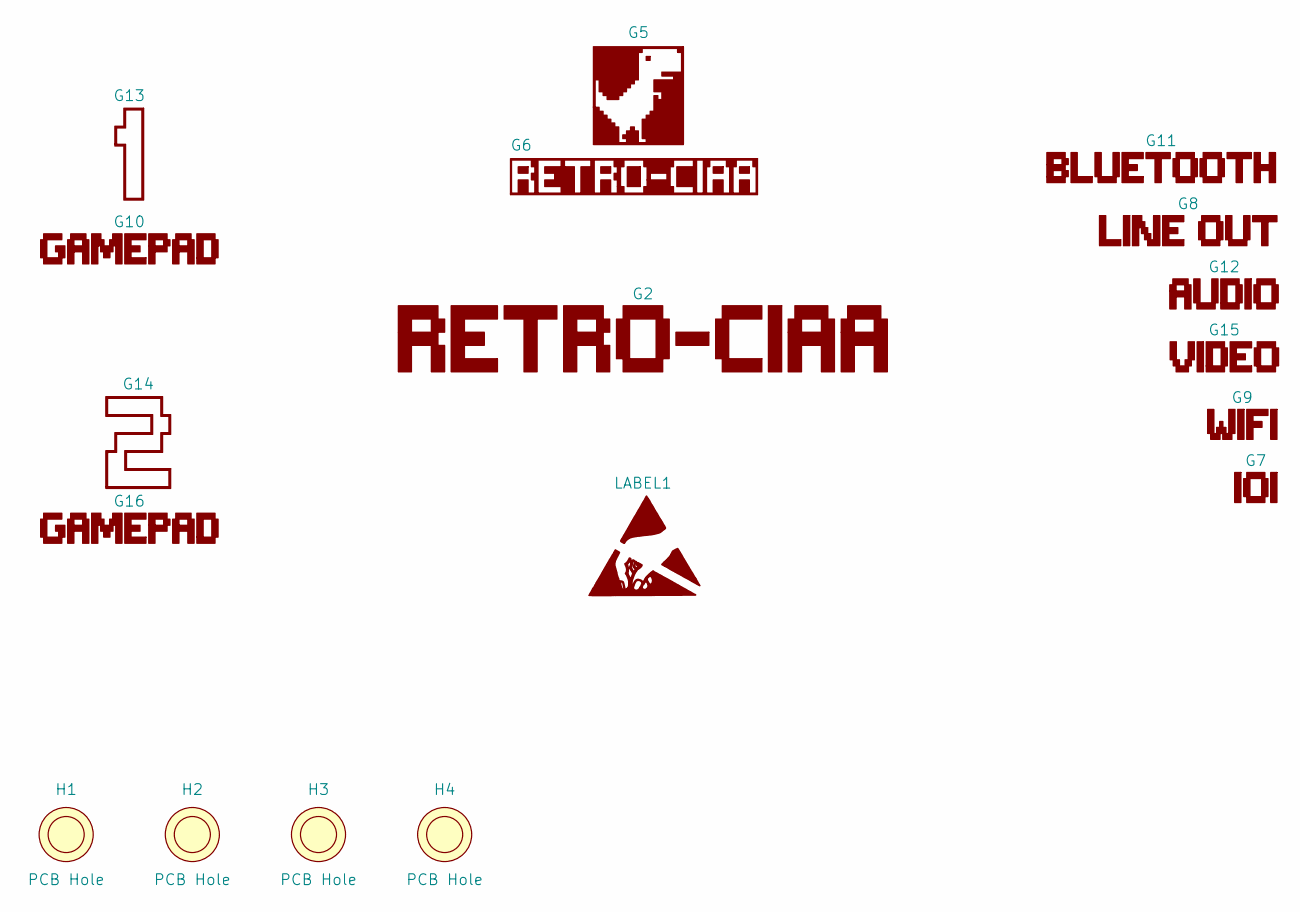
[picture p425: schematic labels.sch, LABELS & MECHANICAL]

Parts:
G2: RETROCIAA_LOGO
G5: LOGO_FRONT; TREX_LOGO_FRONT
G6: RETROCIAA_LOGO_FRONT
G7: RETROCIAA_VIDEO_CONN
G8: RETROCIAA_LINEOUT
G9: RETROCIAA_WIFI
G10, G16: RETROCIAA_GAMEPAD
G11: RETROCIAA_BLUETOOTH
G12: RETROCIAA_AUDIO
G13: RETROCIAA_1
G14: RETROCIAA_2
G15: RETROCIAA_VIDEO
H1, H2, H3, H4: PCB Hole; MountingHole_3.7mm_Pad_Via
LABEL1: ESD_LOGO_15; ESD_Sign_12

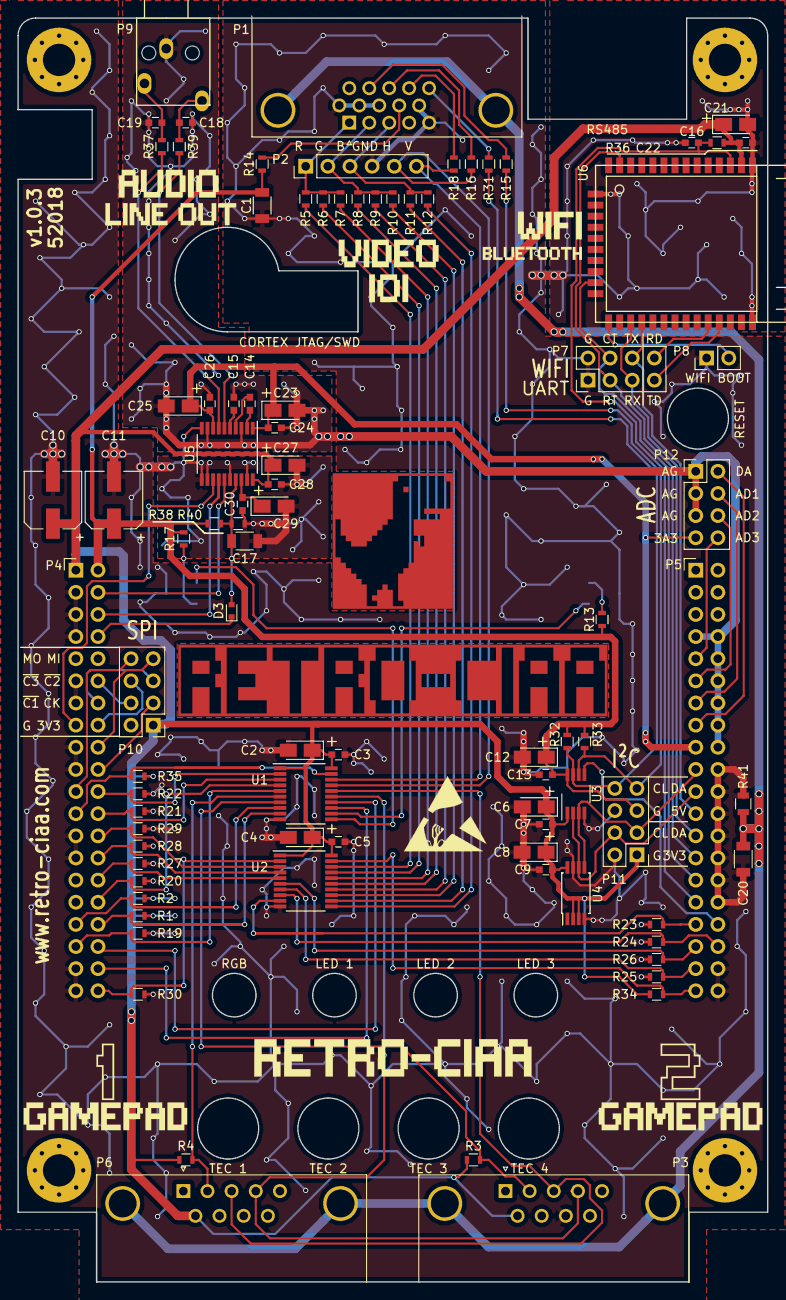
[picture p426: board retro-ciaa.kicad_pcb from above]

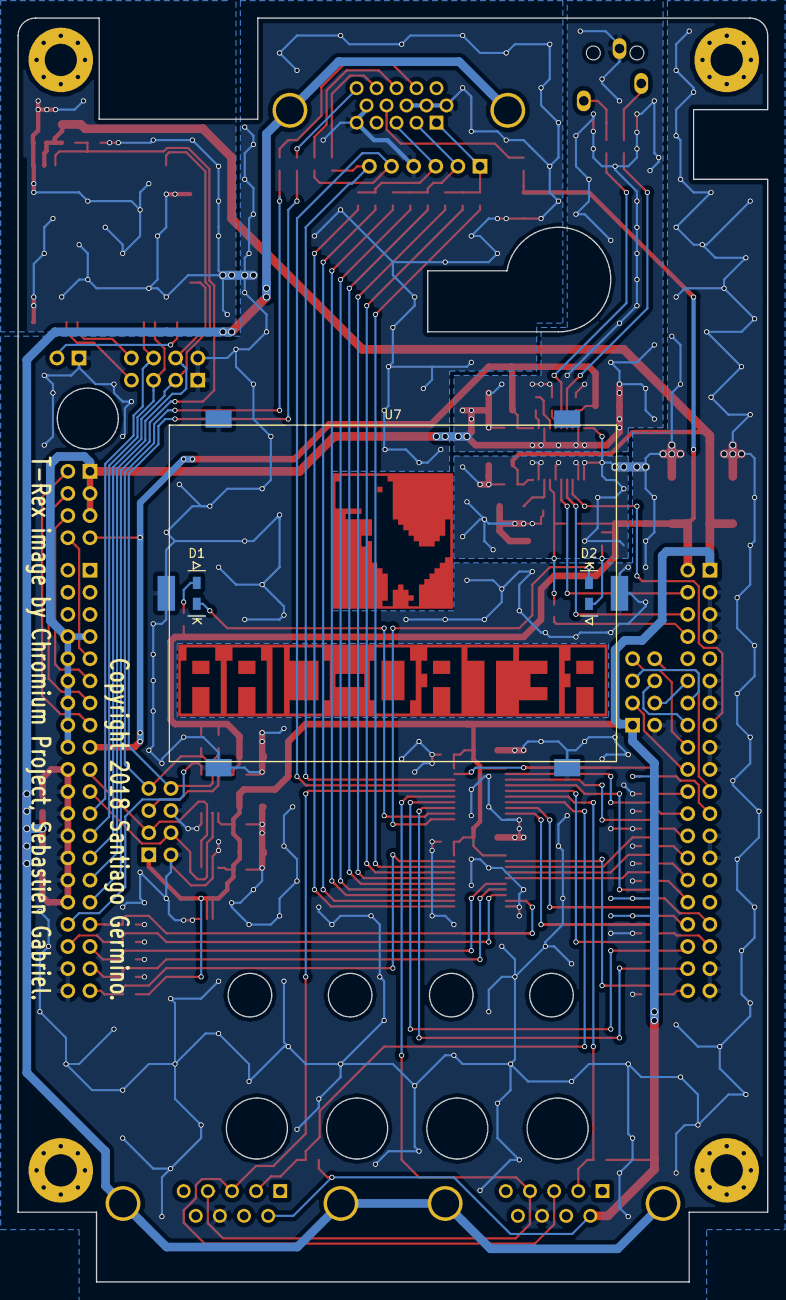
[picture p427: board retro-ciaa.kicad_pcb from below]

Board: 2 copper layers, 86.0 x 145.0 mm, 113 parts (5 on the bottom side), 86 nets.
