brengi/CESE-PCB/2018/Pistarelli/tpFinal.kicad_pcb

## KiCad design 2018/Pistarelli/tpFinal.kicad_pcb (2019-05-17)

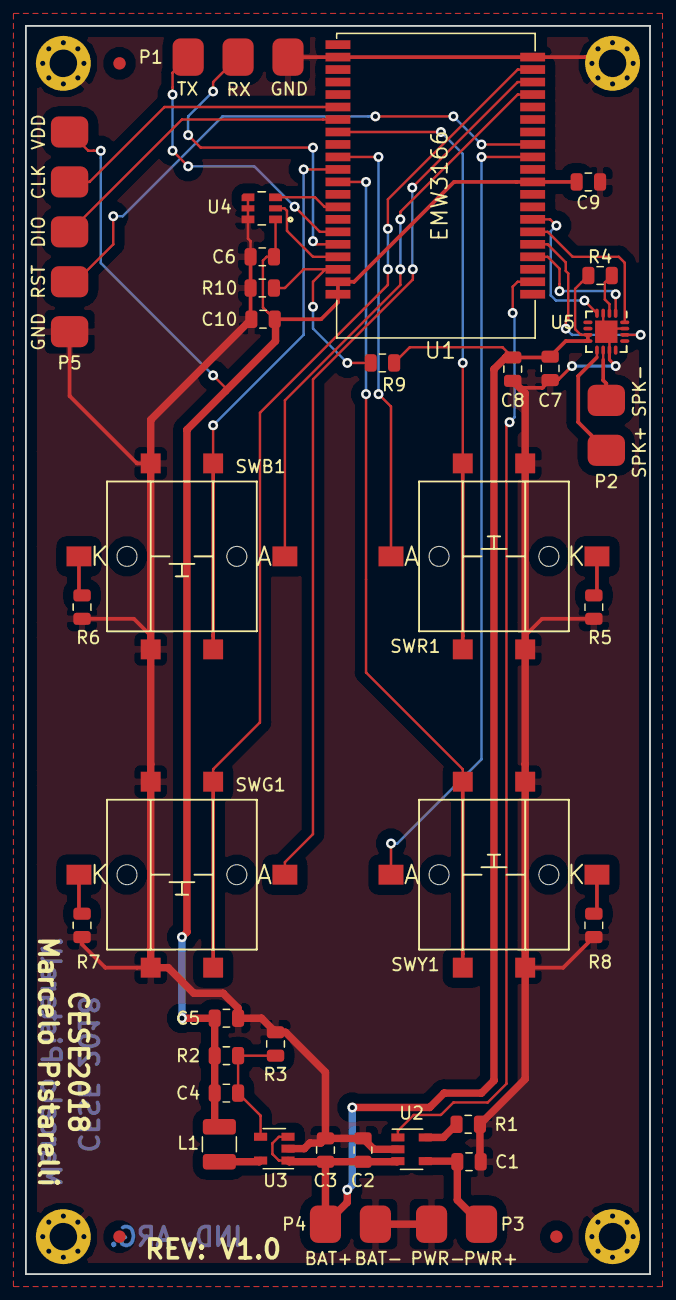
[picture p428: board tpFinal.kicad_pcb from above]

Board: 2 copper layers, 50.0 x 100.0 mm, 42 parts (0 on the bottom side), 35 nets.

Parts:
C1, C2, C3, C5, C7, C10: 10uF; C_0805_2012Metric
C4: 15pF; C_0805_2012Metric
C6, C8, C9: 0.1uF; C_0805_2012Metric
FD1, FD2, FD3: Fiducial; Fiducial_1mm_Dia_2mm_Outer
L1: 2.2uH; L_1210_3225Metric
MH1, MH2, MH3, MH4: MountingHole_Pad; MountingHole_2.2mm_M2_Pad_Via
P1: CONN_UART_TX_RX
P2: CONN_SPK
P3: CONN_PWR
P4: CONN_BAT
P5: CONN_SWD
R1: 2K; R_0805_2012Metric
R2: 453K; R_0805_2012Metric
R3: 100k; R_0805_2012Metric
R4: 100K; R_0805_2012Metric
R5: 470R; R_0805_2012Metric
R6: 220R; R_0805_2012Metric
R7: 330R; R_0805_2012Metric
R8: 270R; R_0805_2012Metric
R9, R10: 10K; R_0805_2012Metric
SWB1: TS12I
SWG1: TS12I
SWR1: TS12I
SWY1: TS12I
U1: EMW3166
U2: MCP73831-2-OT; SOT-23-5
U3: AUR9705AGH; SOT-23-5
U4: SPH0644HM4H-1
U5: MAX98357A; QFN-16-1EP_3x3mm_P0.5mm_EP1.8x1.8mm

Connections:
+3V3: C4.1, C5.1, C6.2, C9.2, C10.1, L1.2, P5.1, R2.1, U1.10, U1.39, U1.40, U4.1
+BATT: C2.1, C3.1, C7.1, C8.1, P4.1, R4.2, R9.2, U2.3, U3.1, U3.3, U5.7, U5.8
+VDC: C1.1, P3.1, U2.4
/AMPLIFICADOR_BCLK: U1.6, U5.16
/AMPLIFICADOR_DIN: U1.4, U5.1
/AMPLIFICADOR_LRCLK: U1.5, U5.14
/AMPLIFICADOR_SD_MODE: U1.7, U5.4
/CARGADOR_STAT: U1.2, U2.1
/LED_B: SWB1.5, U1.17
/LED_G: SWG1.5, U1.18
/LED_R: SWR1.5, U1.29
/LED_Y: SWY1.5, U1.12
/MIC_CLK: U1.37, U4.2
/MIC_DATA: U1.33, U4.3
/NRST: P5.4, U1.13
/SWCLK: P5.2, U1.25
/SWDIO: P5.3, U1.26
/SW_B: SWB1.1, SWB1.2, U1.30
/SW_G: SWG1.1, SWG1.2, U1.19
/SW_R: SWR1.1, SWR1.2, U1.27
/SW_Y: SWY1.1, SWY1.2, U1.31
/UART_Rx: P1.2, U1.36
/UART_Tx: P1.1, U1.35
/amplificadorAudioDigital/GAIN_SLOT: R4.1, U5.2
/amplificadorAudioDigital/OUT+: P2.1, U5.9
/amplificadorAudioDigital/OUT-: P2.2, U5.10
GND: C1.2, C2.2, C3.2, C5.2, C6.1, C7.2, C8.2, C9.1, C10.2, MH1.1, MH2.1, MH3.1, MH4.1, P1.3, P3.2, P4.2, P5.5, R1.2, R3.2, R5.2, R6.2, R7.2, R8.2, R10.2, SWB1.3, SWB1.4, SWG1.3, SWG1.4, SWR1.3, SWR1.4, SWY1.3, SWY1.4, U1.20, U1.21, U2.2, U3.2, U4.4, U4.5, U4.6, U5.3, U5.11, U5.15, U5.17
unnamed: C4.2, R2.2, R3.1, U3.4
unnamed: L1.1, U3.5
unnamed: R1.1, U2.5
unnamed: R5.1, SWR1.6
unnamed: R6.1, SWB1.6
unnamed: R7.1, SWG1.6
unnamed: R8.1, SWY1.6
unnamed: R9.1, R10.1, U1.38
