brengi/CESE-PCB/2018/Vallasciani/Final project - Audio processor/Poncho_Grande/poncho_grande.kicad_pcb

## KiCad design 2018/Vallasciani/Final project - Audio processor/Poncho_Grande/poncho_grande.kicad_pcb (2019-05-17)

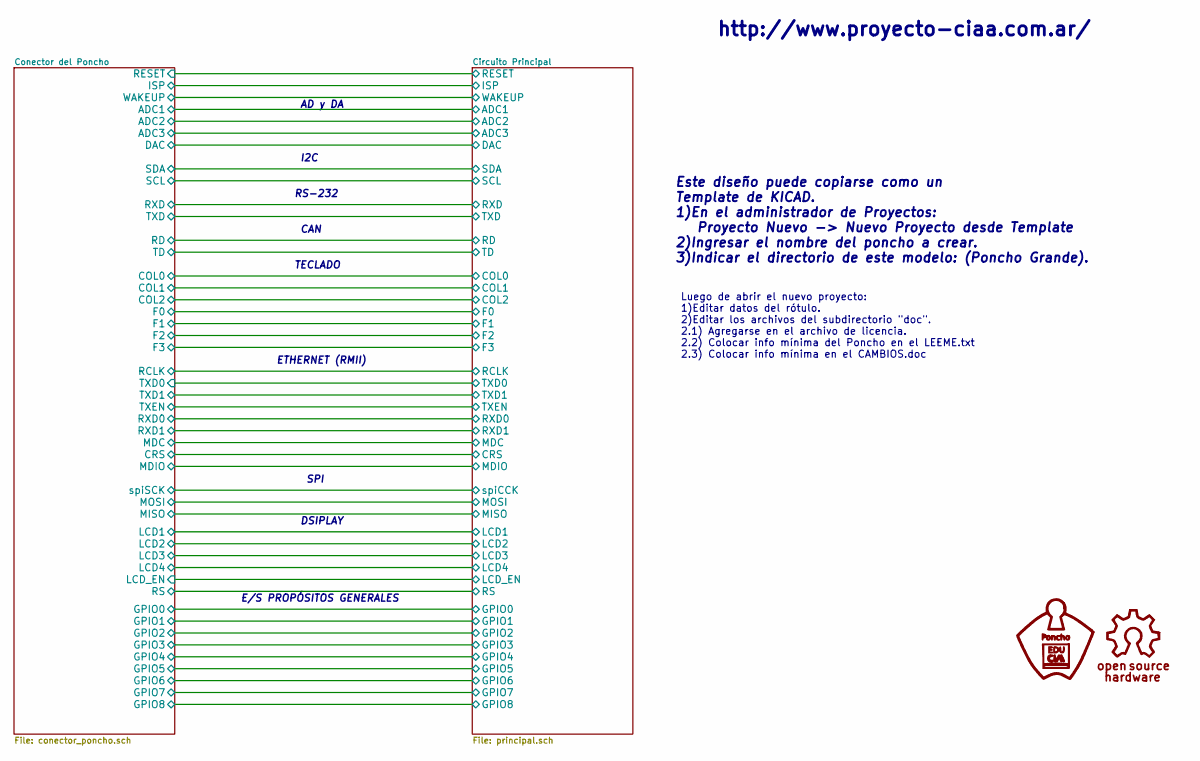
[picture p429: schematic poncho_grande.sch, Poncho Grande - Modelo - Ejemplo - Template]

Notes on the sheet:
AD y DA
I2C
RS-232
CAN
TECLADO
ETHERNET (RMII)
SPI
DSIPLAY
E/S PROPÓSITOS GENERALES
Este diseño puede copiarse como un Template de KICAD. 1)En el administrador de Proyectos: Proyecto Nuevo -> Nuevo Proyecto desde Template 2)Ingresar el nombre del poncho a crear. 3)Indicar el directorio de este modelo: (Poncho Grande).
http://www.proyecto-ciaa.com.ar/
Luego de abrir el nuevo proyecto: 1)Editar datos del rótulo. 2)Editar los archivos del subdirectorio "doc". 2.1) Agregarse en el archivo de licencia. 2.2) Colocar info mínima del Poncho en el LEEME.txt 2.3) Colocar info mínima en el CAMBIOS.doc
