brengi/CESE-PCB/AislacionUSB/USBCableIsolatorCircuit.kicad_pcb

## KiCad design AislacionUSB/USBCableIsolatorCircuit.kicad_pcb (2016-07-26)

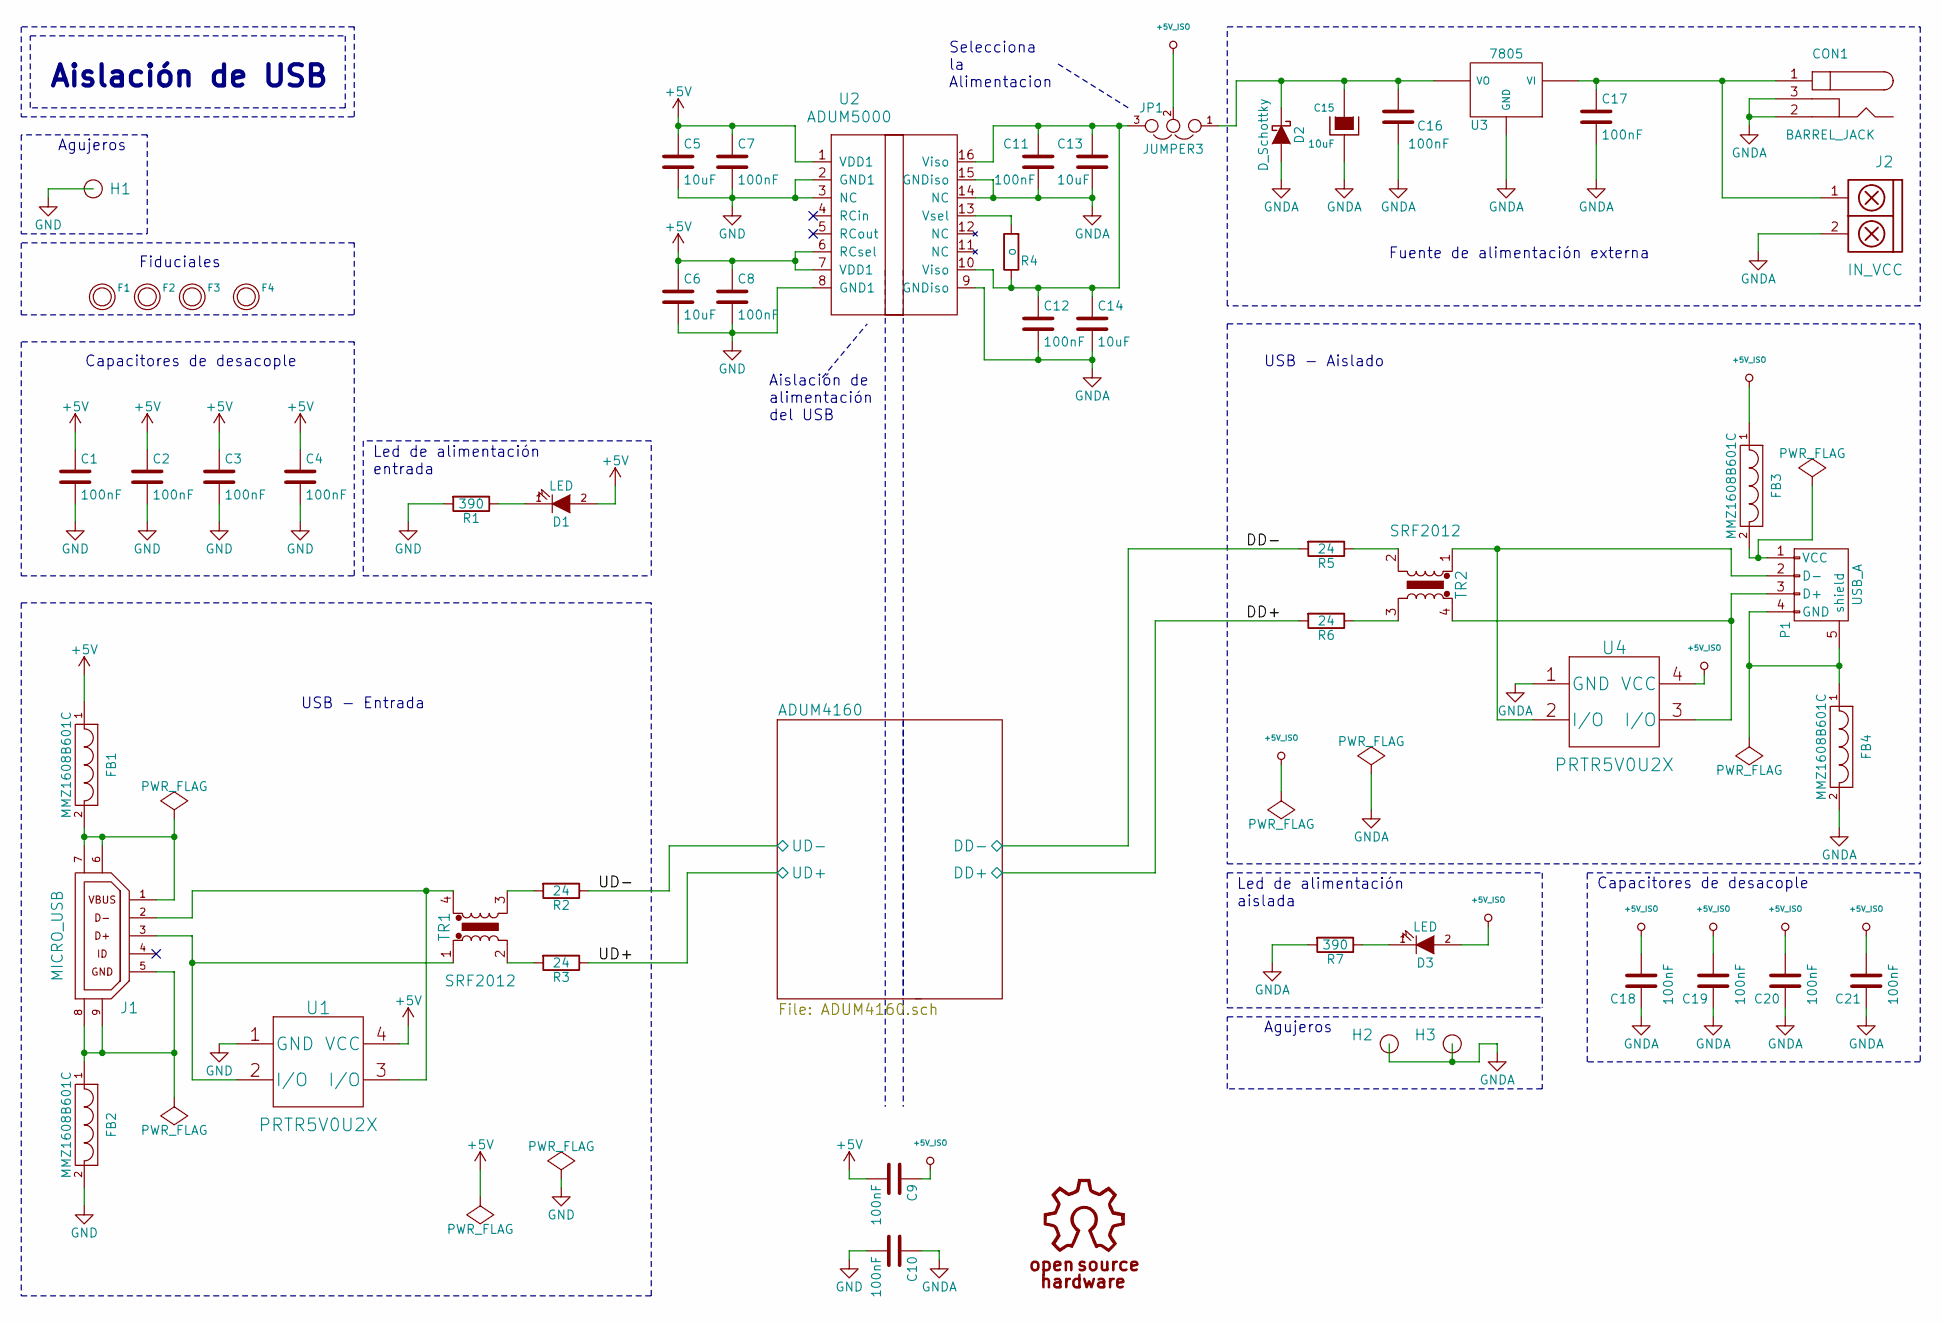
[picture p435: schematic USBCableIsolatorCircuit.sch, Aislador USB para uso industrial.]

Parts:
C1, C2, C3, C4, C7, C8, C11, C12, C16, C17, C18, C19, C20, C21: 100nF; C_0603_HandSoldering; Digikey# 399-1096-1-ND
C5, C6, C13, C14: 10uF; C_1206_HandSoldering; Digikey# 445-1602-1-ND
C9, C10: 100nF; C_1812_HandSoldering; Digikey# 399-3442-2-ND
C15: 10uF; SMD-1206_Pol; Digikey# 399-4788-2-ND
CON1: BARREL_JACK; JACK_ALIM; Digikey# EJ508A-ND
D1, D3: LED; LED_0805; Digikey# 475-1410-2-ND
D2: D_Schottky; DO-214AC_SMA
F1, F2, F3, F4: FIDUCIAL; Fiducial_1mm
FB1, FB2, FB3, FB4: MMZ1608B601C; C_0603_HandSoldering; Digikey# 445-2166-1-ND
H1, H2, H3: PCB_HOLE; MountingHole_2.7mm_M2.5_DIN965_Pad
J1: MICRO_USB; USB_MicroAB; Digikey# H11635TR-ND
J2: IN_VCC; bornier2; Digikey# 571-7969492
JP1: JUMPER3; PIN_ARRAY_3x1; Digikey# Z5375-ND
P1: USB_A; Digikey# UE27AC54100-ND
R1, R7: 390; R_0603_HandSoldering; Digikey# P390BZCT-ND
R2, R3, R5, R6: 24; R_0603_HandSoldering; Digikey# P24GTR-ND
R4: o; R_0603_HandSoldering; Digikey# P0.0GTR-ND
TR1, TR2: SRF2012; SRF2012-HandSoldering; Digikey# SRF2012-900YCT-ND
U1, U4: PRTR5V0U2X; SOT-143-4-HandSoldering; Digikey# CM1213A-02SROSCT-ND
U2: ADUM5000; Digikey# ADUM5000ARWZ-RLCT-ND
U3: 7805; TO-220; Digikey# LM7805CT-ND

Connections:
+5V: C1.1, C2.1, C3.1, C4.1, C5.1, C6.1, C7.1, C8.1, C9.2, D1.2 (A), FB1.1, U1.4 (VCC), U2.1 (VDD1), U2.6 (RCsel), U2.7 (VDD1); also elsewhere on the board
+5V_iso: C9.1, C18.2, C19.2, C20.2, C21.2, D3.2 (A), FB3.1, JP1.2, U4.4 (VCC); also elsewhere on the board
/ADUM4160/DD+: R6.2; also elsewhere on the board
/ADUM4160/DD-: R5.2; also elsewhere on the board
/ADUM4160/UD+: R3.1; also elsewhere on the board
/ADUM4160/UD-: R2.1; also elsewhere on the board
GND: C1.2, C2.2, C3.2, C4.2, C5.2, C6.2, C7.2, C8.2, C10.2, FB2.2, H1.1, R1.2, U1.1 (GND), U2.2 (GND1), U2.3 (NC), U2.8 (GND1); also elsewhere on the board
GNDA: C10.1, C11.2, C12.2, C13.2, C14.2, C15.2, C16.2, C17.2, C18.1, C19.1, C20.1, C21.1, CON1.2, CON1.3, D2.2 (A), FB4.2, H2.1, H3.1, J2.2, R7.2, U2.9 (GNDiso), U2.14 (NC), U2.15 (GNDiso), U3.2 (GND), U4.1 (GND); also elsewhere on the board
unnamed: C11.1, C12.1, C13.1, C14.1, JP1.3, R4.1, U2.10 (Viso), U2.16 (Viso)
unnamed: C15.1, C16.1, D2.1 (K), JP1.1, U3.3 (VO)
unnamed: C17.1, CON1.1, J2.1, U3.1 (VI)
unnamed: D1.1 (K), R1.1
unnamed: D3.1 (K), R7.1
unnamed: FB1.2, J1.1 (VBUS), J1.6 (S2), J1.7 (S1)
unnamed: FB2.1, J1.5 (GND), J1.8 (S3), J1.9 (S4)
unnamed: FB3.2, P1.1 (VCC)
unnamed: FB4.1, P1.4 (GND), P1.5 (shield)
unnamed: J1.2 (USB_DN), TR1.4, U1.3 (I/O)
unnamed: J1.3 (USB_DP), TR1.1, U1.2 (I/O)
unnamed: P1.2 (D-), TR2.1, U4.2 (I/O)
unnamed: P1.3 (D+), TR2.4, U4.3 (I/O)
unnamed: R2.2, TR1.3
unnamed: R3.2, TR1.2
unnamed: R4.2, U2.13 (Vsel)
unnamed: R5.1, TR2.2
unnamed: R6.1, TR2.3

Notes on the sheet:
Fiduciales
Led de alimentación aislada
Capacitores de desacople
USB - Aislado
Fuente de alimentación externa
Led de alimentación entrada
USB - Entrada
Aislación de alimentación del USB
Aislación de USB
Selecciona la Alimentacion
Agujeros
