brengi/CESE-PCB/AislacionUSB/USBCableIsolatorCircuit.kicad_pcb

## KiCad design AislacionUSB/USBCableIsolatorCircuit.kicad_pcb (continued)

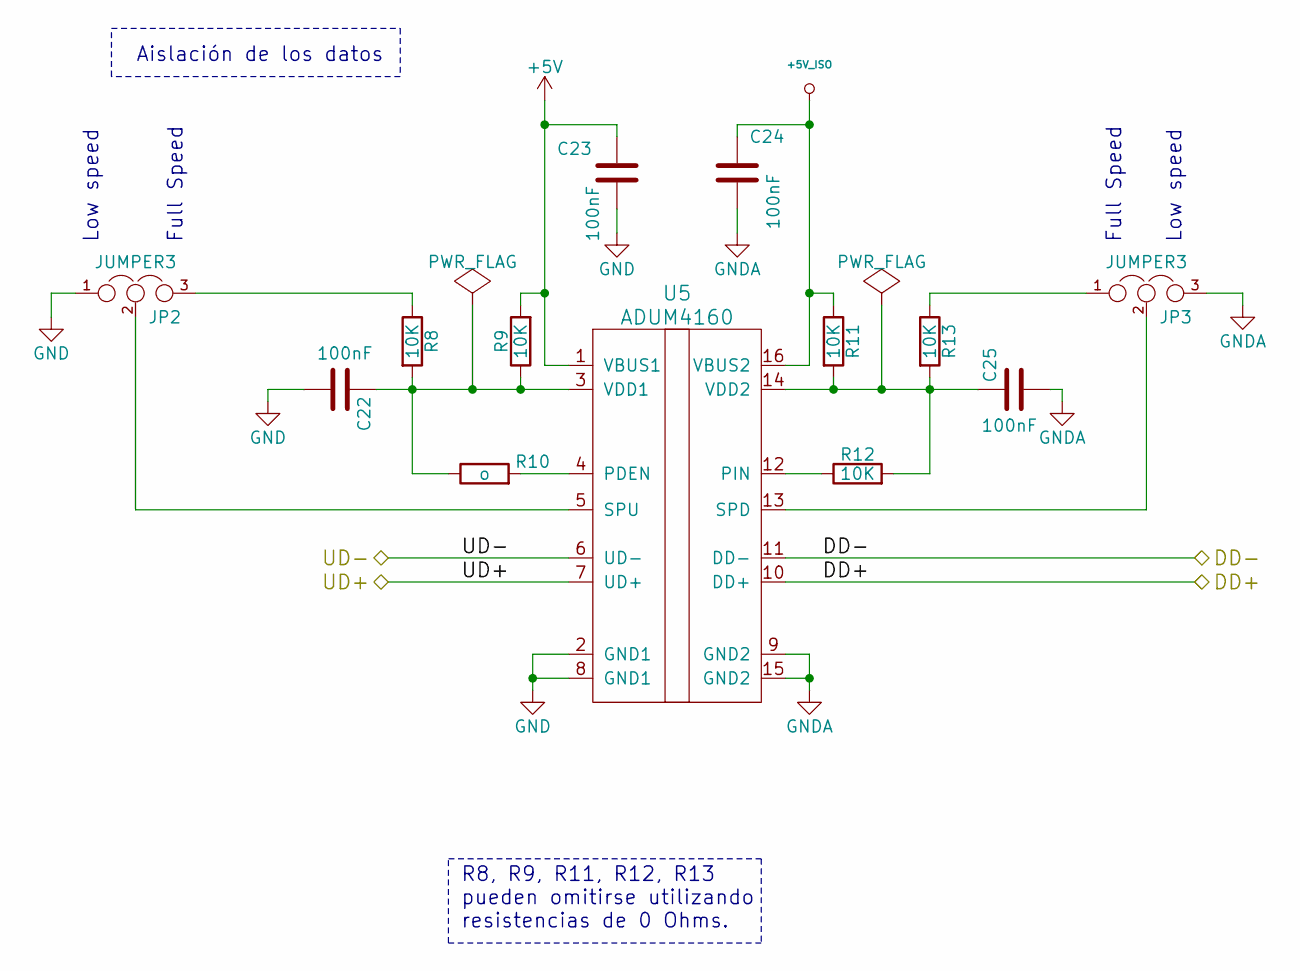
[picture p436: schematic ADUM4160.sch, Aislador USB para uso industrial.]

Parts:
C22, C23, C24, C25: 100nF; C_0603_HandSoldering; Digikey# 399-1096-1-ND
JP2, JP3: JUMPER3; PIN_ARRAY_3x1; Digikey# Z5375-ND
R8, R9, R11, R12, R13: 10K; R_0603_HandSoldering; Digikey# P10KGTR-ND
R10: o; R_0603_HandSoldering; Digikey# P0.0GTR-ND
U5: ADUM4160; Digikey# ADUM4160BRWZ-RLTR-ND

Connections:
+5V: C23.2, R9.2, U5.1 (VBUS1); also elsewhere on the board
+5V_iso: C24.2, R11.1, U5.16 (VBUS2); also elsewhere on the board
/ADUM4160/DD+: U5.10 (DD+); also elsewhere on the board
/ADUM4160/DD-: U5.11 (DD-); also elsewhere on the board
/ADUM4160/UD+: U5.7 (UD+); also elsewhere on the board
/ADUM4160/UD-: U5.6 (UD-); also elsewhere on the board
GND: C22.2, C23.1, JP2.1, U5.2 (GND1), U5.8 (GND1); also elsewhere on the board
GNDA: C24.1, C25.2, JP3.3, U5.9 (GND2), U5.15 (GND2); also elsewhere on the board
unnamed: C22.1, R8.2, R9.1, R10.1, U5.3 (VDD1)
unnamed: C25.1, R11.2, R12.2, R13.2, U5.14 (VDD2~)
unnamed: JP2.2, U5.5 (SPU)
unnamed: JP2.3, R8.1
unnamed: JP3.1, R13.1
unnamed: JP3.2, U5.13 (SPD)
unnamed: R10.2, U5.4 (PDEN)
unnamed: R12.1, U5.12 (PIN)

Notes on the sheet:
Full Speed
Low speed
Aislación de los datos
R8, R9, R11, R12, R13 pueden omitirse utilizando resistencias de 0 Ohms.

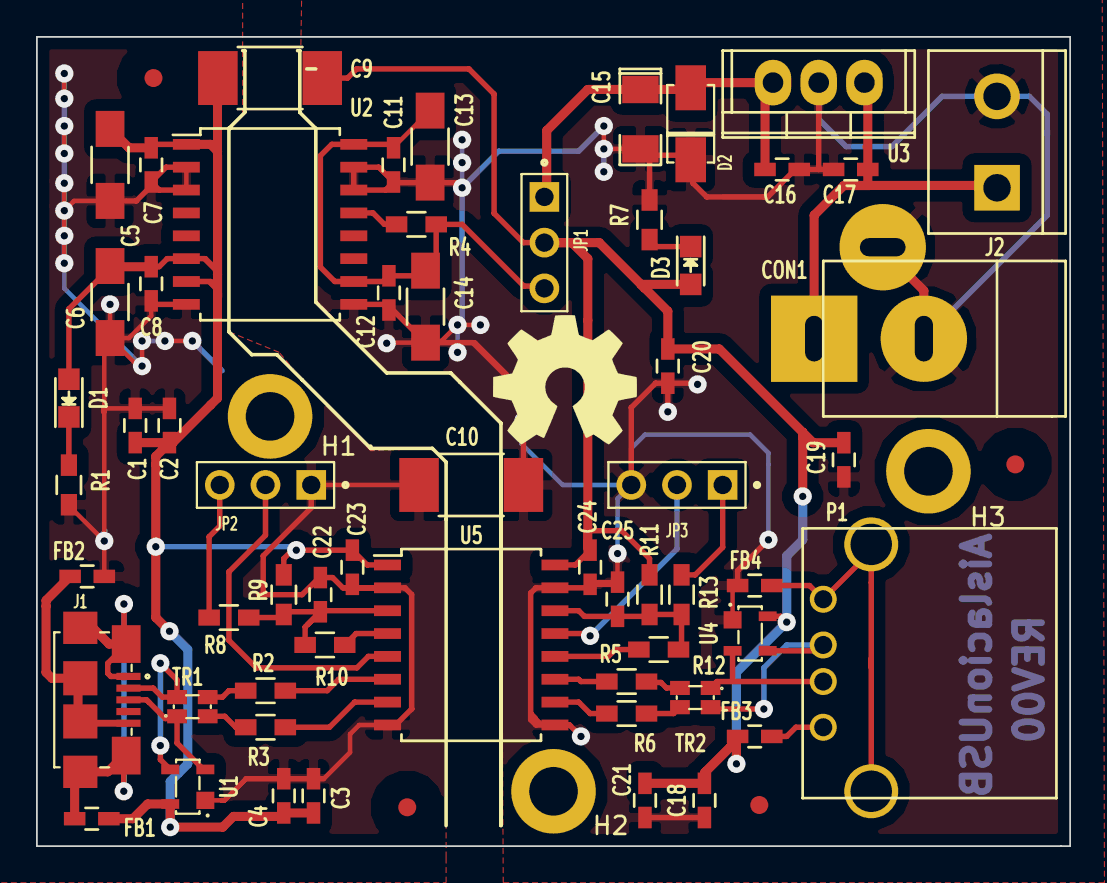
[picture p437: board USBCableIsolatorCircuit.kicad_pcb from above]

Board: 2 copper layers, 57.4 x 45.0 mm, 67 parts (0 on the bottom side), 34 nets.

Other parts of the board:
OPEN HARDWARE: OSHWA
